adzetto/DASK_26__DESIGN_AND_ANALYSIS/afad_reports/DD3.pdf

# Tü rkiye Deprem Tehlike Haritaları Interaktif Web Uygulaması

## Kullanıcı Girdileri

Rapor Başlığı: DASK26DD-3

DD-3 Deprem Yer Hareketi Düzeyi | 50 yılda aşılma olasılığı %50 (tekrarlanma periyodu 72 yıl) olan deprem yer hareketi düzeyi
Yerel Zemin Sınıfı: ZD | Orta sıkı - sıkı kum, çakıl veya çok katı kil tabakaları

Enlem: 41.002136°

Boylam 29.106832°

## Çıktılar

S S

= 0.358 | S1 = 0.099 | PGA=0.152 | PGV=9.459

SS : Kısa periyot harita spektral ivme katsayısı [boyutsuz]

S1 : 1.0 saniye periyot için harita spektral ivme katsayısı [boyutsuz]

PGA : En büyük yer ivmesi [g]

PGV : En büyük yer hızı [cm/sn]

Sismik Tehlike Haritası Detay Raporu | https://tdth.afad.gov.tr/TDTH/detayliRapor.xhtml
1 of 6 | 2/3/2026, 4:59 PM

## Yerel Zemin Sınıfları

Yerel Zemin Sınıfı: | Zemin Cinsi | Üst 30 metrede ortalama
(VS)30 [m/s] | (N60)30 [darbe/30 cm] | (Cu )30 [kPa]
ZA | Sağlam, sert kayalar | > 1500 | - | -
ZB | Az ayrışmış, orta sağlam kayalar Çok sıkı kum, çakıl ve sert kil tabakaları veya ayrışmış, | 760 -1500 | - | - ZC
| çok çatlaklı zayıf kayalar | 360 -760 | > 50 | > 250
ZD | Orta sıkı - sıkı kum, çakıl veya çok katı kil tabakaları | 180 -360 | 15 - 50 | 70 -250
ZE | Gevşek kum, çakıl veya yumuşak - katı kil tabakaları veya PI > 20 ve w > % 40 koşullarını sağlayan toplamda 3 metreden daha kalın yumuşak kil tabakası ( Cu < 25 kPa ) içeren profiller | < 180 | < 15 | < 70
ZF | Sahaya özel araştırma ve değerlendirme gerektiren zeminler : 1) Deprem etkisi altında çökme ve potansiyel göçme riskine sahip zeminler (sıvılaşabilir zeminler, yüksek derecede hassas killer, göçebilir zayıf çimentolu zeminler vb.), 2) Toplam kalınlığı 3 metreden fazla turba ve/veya organik içeriği yüksek killer, 3) Toplam kalınlığı 8 metreden fazla olan yüksek plastisiteli (PI > 50) killer , 4) Çok kalın (> 35 m) yumuşak veya orta katı killer.
2 of 6 | 2/3/2026, 4:59 PM

## Yerel Zemin Etki Katsayıları

Yerel Zemin Sınıfı: | Kısa periyot bölgesi için Yerel Zemin Etki Katsayısı FS
SS ≤ 0.25 | SS = 0.50 | SS = 0.75 | SS = 1.00 | SS = 1.25 | SS ≥ 1.50
ZA | 0.8 | 0.8 | 0.8 | 0.8 | 0.8 | 0.8
ZB | 0.9 | 0.9 | 0.9 | 0.9 | 0.9 | 0.9
ZC | 1.3 | 1.3 | 1.2 | 1.2 | 1.2 | 1.2
ZD | 1.6 | 1.4 | 1.2 | 1.1 | 1.0 | 1.0
ZE | 2.4 | 1.7 | 1.3 | 1.1 | 0.9 | 0.8
ZF | Sahaya özel zemin davranış analizi yapılacaktır.

## Yerel Zemin Sınıfı: ZD ve SS

## =0.358 için FS=1.514

Yerel Zemin Sınıfı: | 1.0 saniye periyot için Yerel Zemin Etki Katsayısı F1 S1
≤ 0.10 | S1 = 0.20 | S1 = 0.30 | S1 = 0.40 | S1 = 0.50 | S1 ≥ 0.60
ZA | 0.8 | 0.8 | 0.8 | 0.8 | 0.8 | 0.8
ZB | 0.8 | 0.8 | 0.8 | 0.8 | 0.8 | 0.8
ZC | 1.5 | 1.5 | 1.5 | 1.5 | 1.5 | 1.4
ZD | 2.4 | 2.2 | 2.0 | 1.9 | 1.8 | 1.7
ZE | 4.2 | 3.3 | 2.8 | 2.4 | 2.2 | 2.0
ZF | Sahaya özel zemin davranış analizi yapılacaktır.

## Yerel Zemin Sınıfı: ZD ve S1

## =0.099 için F1

=2.400

3 of 6 | 2/3/2026, 4:59 PM

## Tasarım Spektral İvme Katsayıları

## SDS = SS FS

= 0.358 x 1.514 = 0.542

## SD1 = S1

F1

= 0.099 x 2.400 = 0.238

SDS : Kısa periyot tasarım spektral ivme katsayısı [boyutsuz]

SD1 : 1.0 saniye periyot için tasarım spektral ivme katsayısı [boyutsuz]

4 of 6 | 2/3/2026, 4:59 PM

## Yatay Elastik Tasarım Spektrumu

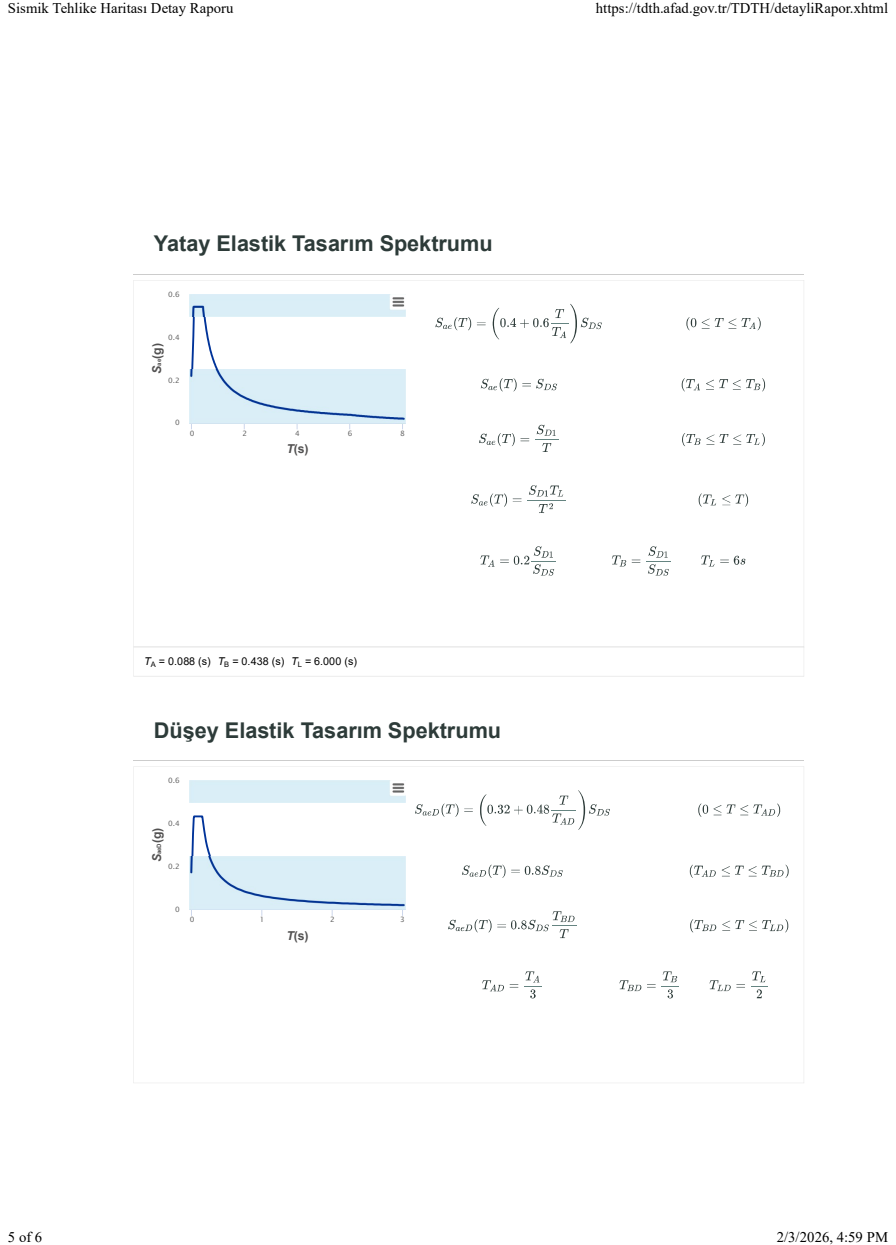
[picture p2: page 5]
Sae(g) 0 2 4 6 8; SaeD(g) 0 1 2 3

Düşey Elastik Tasarım Spektrumu

TAD = 0.029 (s) TBD = 0.146 (s) TLD = 3.000 (s)

6 of 6 | 2/3/2026, 4:59 PM
