adzetto/DASK_26__DESIGN_AND_ANALYSIS/tex/rapor.pdf

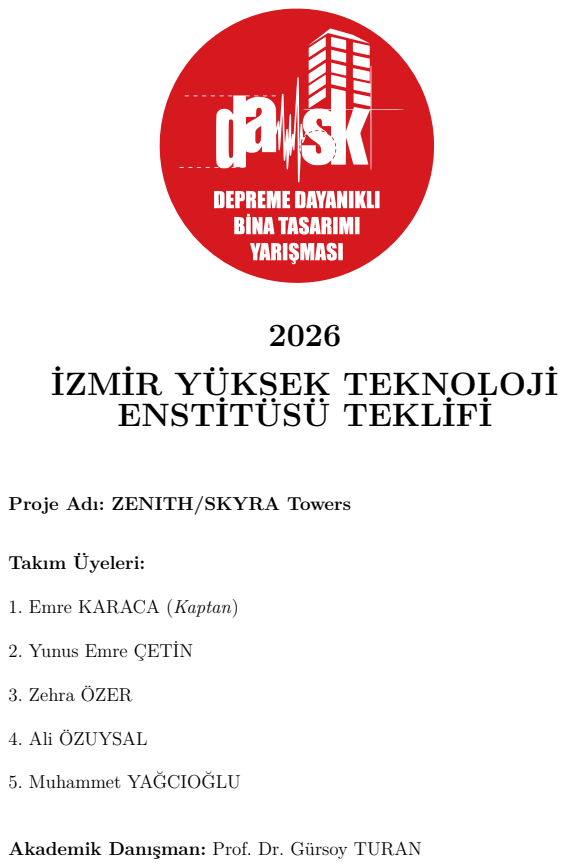
[picture p3: page 1]
Takım Üyeleri:; 3. Zehra ÖZER; 4. Ali ÖZUYSAL; 5. Muhammet YAĞCIOĞLU

İZMİR YÜKSEK TEKNOLOJİ
ENSTİTÜSÜ TEKLİFİ

Proje Adı: ZENITH/SKYRA Towers

1. Emre KARACA (Kaptan)

2. Yunus Emre ÇETİN

Akademik Danışman: Prof. Dr. Gürsoy TURAN

DASK 2026 | İzmir Yüksek Teknoloji Enstitüsü Proje Teklifi

## İçindekiler

1 BİNA TANITIMI | 1
2 MİMARİ TASARIM | 2
3 YAPISAL SİSTEM TANIMI ve TASARIMI | 3
4 ÇİZİMLER | 5
5 SORULAR | 6
DASK Depreme Dayanıklı Bina Tasarımı Yarışması Proje Teklifi | i/14

## 1 BİNA TANITIMI

Konum ve vizyon. İstanbul; Asya ile Avrupa’yı birbirine bağlayan, yüzyıllardır ticaretin, kültürün ve diplomasinin kesişim noktası olan dünyanın sayılı metropollerinden biridir. Türkiye’nin gayrisafi yurtiçi hasılasının yaklaşık üçte birini tek başına üreten bu şehir, ülkenin finans, lojistik ve hizmet sektörlerinin de merkezi konumundadır. Bu potansiyeli küresel ölçekte değerlendirmek amacıyla İstanbul’un Ümraniye ilçesinde inşa edilen İstanbul Finans Merkezi (İFM); Londra, New York, Hong Kong ve Singapur gibi dünya finans merkezleriyle rekabet edecek altyapıya sahip, akıllı ve sürdürülebilir bir kentsel finans ekosistemi yaratmayı hedeflemektedir (Şekil 1). İFM yerleşkesinde konumlanan GÜRSOY Towers projesi, bölgenin artan nitelikli ofis, konaklama ve ticaret alanı ihtiyacına yanıt vererek İstanbul’un küresel finans haritasındaki konumunu güçlendirmeyi amaçlamaktadır.
Mimari konsept ve boyutlar. GÜRSOY Towers, 25 katlı iki simetrik ikiz kuleden oluşan, İFM silüetine prestij katan bir yapı olarak tasarlanmıştır. Her kule 15×8 m plan boyutlarına sahip olup zemin kat yüksekliği 4,5 m, tipik kat yüksekliği 3,0 m, toplam bina yüksekliği 76,5 m, kuleler arası açıklık ise 4,0 m’dir. Kule başına tipik kat brüt alanı yaklaşık 150 m² olup iki kulenin toplam brüt inşaat alanı yaklaşık 7 666 m²
’dir. Kuleler; 6.,
12., 18. ve 25. katlarda yer alan dört adet köprü ile birbirine bağlanmıştır. Köprüler yalnızca taşıyıcı birer eleman değil, aynı zamanda birer sosyal ve ticari odak noktasıdır: sırasıyla gastronomi, iş dünyası, kültür-sanat ve sky lounge temaları etrafında şekillendirilmiştir. Dış cephe, yüksek performanslı cam paneller ve çelik çerçeve kompozisyonuyla tasarlanmış olup kulelerin kesişen çapraz elemanları cephede de okunarak yapıya dinamik ve güçlü bir karakter kazandırmaktadır.
Kat kullanım programı. Zemin kat; çift cepheli ana giriş lobisi, dijital karşılama ekranları, güvenlik kontrol noktası ve sanat sergi galerisi olarak düzenlenmiştir. 2.–3. katlar; butik mağazalar, flagship restoranlar, konferans merkezi ve basın odası gibi ticari ve kamusal işlevlere ayrılmıştır. 4. kat tam donanımlı fitness merkezi, kapalı yüzme havuzu ve spa alanı ile kullanıcılara sosyal yaşam imkânı sunmaktadır. 5–11. katlar; açık plan ofis düzeninde yüksek yoğunluklu çalışma alanları olarak planlanmış olup esnek bölme sistemleri sayesinde farklı kiracı ihtiyaçlarına uyarlanabilmektedir. 13–17. katlar ise hukuk büroları, finans şirketleri ve uluslararası danışmanlık firmalarına yönelik premium süit ofisler olarak tasarlanmıştır. A Kulesi’nde 19. kattan itibaren üst düzey yönetici ofisleri, CEO süitleri ve özel toplantı salonları; B Kulesi’nde ise aynı katlarda 5 yıldızlı butik otel odaları, wellness merkezi ve presidential süit yer almaktadır. Bu ikili kullanım yapısı sayesinde iş seyahati ile konaklama ihtiyacı aynı yerleşkede karşılanmaktadır. 24. katta her iki kulede penthouse katlar bulunurken, 25. katta İstanbul’un eşsiz siluetini sunan 360° panoramik sky lounge, çatı teras restoranı ve gözlem platformu konumlandırılmıştır. GÜRSOY Towers bu programıyla çalışma, konaklama, gastronomi, sosyal yaşam ve kültürel etkinlik işlevlerini bir arada sunarak İFM’nin en çok yönlü yapısı olmayı hedeflemektedir.
DASK Depreme Dayanıklı Bina Tasarımı Yarışması Proje Teklifi | 1/14


Şekil 1: İstanbul Finans Merkezi (İFM) yerleşkesi ve GÜRSOY Towers proje konumu.

## 2 MİMARİ TASARIM

Binanın mimari tasarımında dikkate alınan tasarım kriterlerinin çevresel ve ekonomik koşulları da kapsayacak şekilde ilgili görsellerle desteklenerek açıklandığı bölümdür (şekiller hariç maksimum 1 A4 sayfa).

DASK Depreme Dayanıklı Bina Tasarımı Yarışması Proje Teklifi | 2/14

## 3 YAPISAL SİSTEM TANIMI ve TASARIMI

Saha koşulları ve deprem tehlikesi. Proje sahası, İstanbul Finans Merkezi (41.00◦ K, 29.11◦ D) mevkiinde olup Kuzey Anadolu Fayı’na yakın konumu itibarıyla birinci derece deprem kuşağında yer almaktadır. AFAD [3] DD-2 tehlike düzeyinde tasarım spektral ivmeleri SDS = 1.008 g, SD1 = 0.514 g olarak belirlenmiştir [1]. Saha ZD zemin sınıfında olup kalın yumuşak zemin tabakası uzun periyotlu deprem dalgalarını kuvvetlendirerek üstyapıya aktarmaktadır; bu durum yapısal tasarımda hem yanal rijitliği hem de yeterli şekil değiştirme kapasitesini zorunlu kılmaktadır.
Taşıyıcı sistem tipi ve gerekçeleri. Salt moment çerçevesi sünek olmakla birlikte yanal ötelenmeyi yeterince sınırlayamamakta; çaprazlı sistem ise yüksek rijitlik sağlamakla beraber gevrek kırılmaya açık bulunmaktadır. Bu dengeyi kurmak üzere çerçeve–çapraz hibrit sistem tercih edilmiştir [5]: çapraz elemanlar yatay yükleri doğrudan temele ileterek yanal ötelenmeyi kontrol altına almakta; moment çerçevesi ise enerji yutma ve plastik yeniden dağılım imkânı sunmaktadır. İkiz kule konfigürasyonu benimsenerek ∼H/4, H/2, 3H/4 ve tepe kotlarına yerleştirilen dört köprü ile kuleler kuplajlanmış; global rijitlik artırılmış, diferansiyel ötelenme ve burulma talebi asgariye indirilmiştir [10, 15]. Köprüler aynı zamanda iki kulenin eş fazlı titreşimini sağlayarak antisimetrik modları bastırma işlevi de görmektedir.
İzlenen yaklaşımlar ve kabuller. Yapısal model OpenSees®
[4] ortamında oluşturulmuştur. Kolon–kiriş birleşimleri rijit, çapraz uçları mafsallı kabul edilmiştir. Güçlü kolon–zayıf kiriş ilkesi gözetilerek plastik mafsalların kiriş uçlarında oluşması hedeflenmiş, kat mekanizması ihtimali bertaraf edilmiştir [1]. Her iki doğrultuda tam simetri tesis edilerek kütle merkezi ile rijitlik merkezi çakıştırılmış (ex/Lx = 0, ey/Ly = 0); böylece deprem yüklerinin burulma bileşeni sıfırlanmıştır. A1a burulma düzensizliği kontrolünde zemin katta ηbi = 1,69 < 2,0, üst katlarda ηbi < 1,2 elde edilmiştir [2]. Deprem analizinde Mod Birleştirme Yöntemi (MBY) ile zaman tanım alanında hesap (ZTAH) uygulanmış; modal katkılar CQC kuralı (ξ =0.05) ile birleştirilmiştir [1].
Sistem geometrisi ve çapraz yerleşim stratejisi. Yapı 20×20 m taban alanı üzerinde iki simetrik kuleden oluşmaktadır (Şekil 2). Her kule 15×8 m plan boyutunda, 7×3 düşey kolon ağı üzerine inşa edilmiş olup zemin kat yüksekliği h0 = 4,5 m, sonraki 24 kat h = 3,0 m; toplam yükseklik H = 76,5 m’dir. Kuleler arası açıklık 4,0 m olup köprüler 6., 12., 18. ve
25. katlarda konumlandırılmıştır. X doğrultusunda köşe açıklıkları (1,35 m) kısa tutularak çerçeve rijitliği takviye edilmiş; Y doğrultusunda simetrik iki açıklık (3,85 m) ile rijitlik dağılımı dengelenmiştir. Çapraz elemanlar, deprem kesme kuvvetinin en yoğun olduğu alt katlara konsantre edilmiştir (Şekil 2). XZ düzleminde iç açıklıklarda zemin–13. kat arasında X-çapraz çifti uygulanarak kesme kuvveti basınç ve çekme bileşenlerine ayrıştırılmıştır. Dış açıklıklarda alt dört katta her katta tam çapraz, üst katlarda ise üçer katlık zikzak düzeninde çapraz yerleştirilmiştir; bu gradyan, üst katlardaki kesme kuvveti düşüşüne paralel olarak rijitlik dağılımını optimize etmektedir. Y Z düzleminde ise köprü katlarındaki düğüm noktalarını güçlendirmek amacıyla mega brace (mega çapraz) konfigürasyonu benimsenmiştir. Zemin bloğunda (0–6. kat) çaprazlar zemin kattan başlayarak iki kat yüksekliğinde orta kolonda birleşmekte (2. kat seviyesi) ve oradan köprü altı düğümüne (6. kat altı) açılmaktadır. Üst bloklarda mega çaprazlar bir köprü altı düğümünden bir sonraki köprü altı düğümüne uzanmakta, merkez düğüm noktaları orta kolonda oluşmaktadır. Köprü üstü düğüm noktaları ek çaprazlarla mega brace merkezine bağlanarak köprü seviyelerinde rijit düğüm noktaları tesis edilmiştir. En üst katta (24–25. kat) köprü üzerinden çatıya doğru kapatma çaprazları uygulanmıştır.
DASK Depreme Dayanıklı Bina Tasarımı Yarışması Proje Teklifi | 3/14

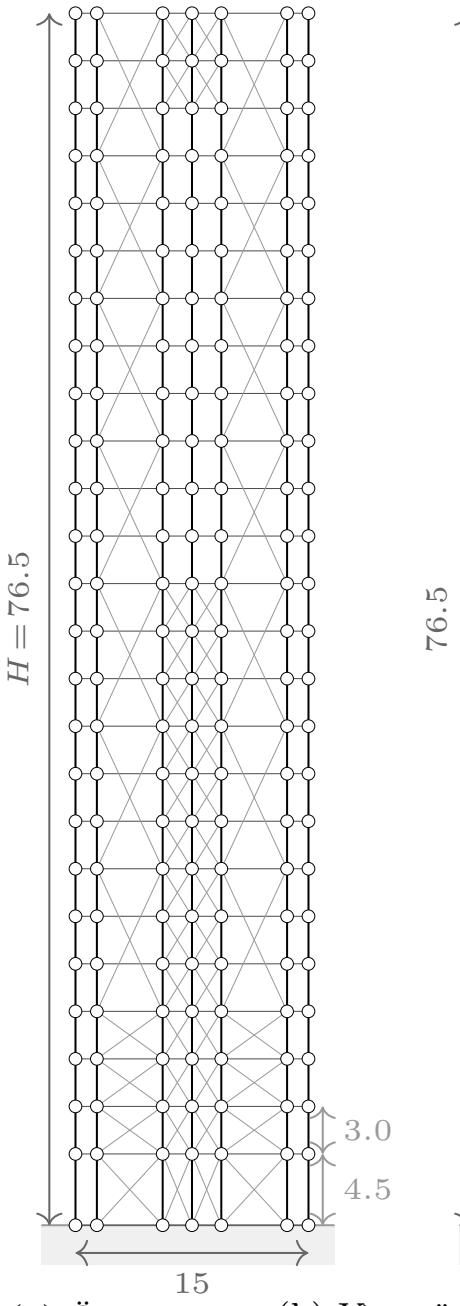
[picture p4: figure]

(a) Ön görünüm (XZ)

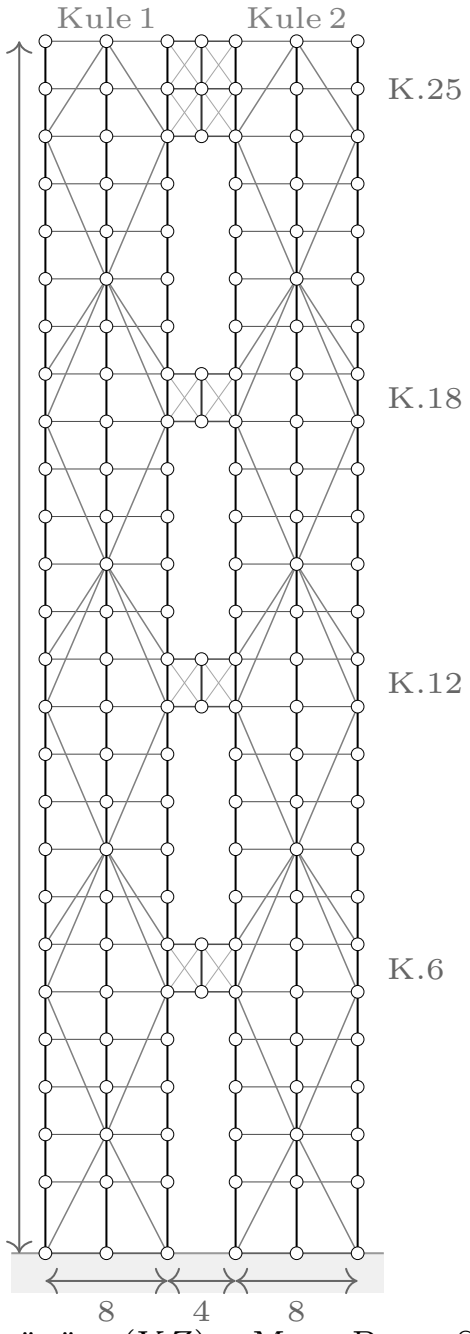
[picture p5: figure]
Kule 1; Kule 2

(b) Yan görünüm (Y Z) – Mega Brace Sistemi

Şekil 2: V10 modelinin yapısal sistemi: (a) ön görünüm (XZ)—iç açıklıklarda X-çapraz (0–12. kat), dış açıklıklarda 3 katlık zikzak; (b) yan görünüm (Y Z)—mega brace çapraz sistemi ve köprü kafes bağlantıları. Siyah: kolon, koyu gri: kiriş/köprü, açık gri: çapraz. Beyaz daireler: düğüm noktaları. Ölçüler metre cinsindendir.

DASK Depreme Dayanıklı Bina Tasarımı Yarışması Proje Teklifi | 4/14

## 4 ÇİZİMLER

Binanın her bir farklı katına ait plan ve iki ana doğrultudaki kesit çizimleri verilecektir.

- Çizimler ayrıca "dwg" formatında ek olarak sunulacaktır.
DASK Depreme Dayanıklı Bina Tasarımı Yarışması Proje Teklifi | 5/14

## 5 SORULAR

### 5.1 Soru I

Soru: Yapı taşıyıcı sistemini belirlerken nelere dikkat ettiğinizi depreme dayanıklı bina tasarım ilkeleri çerçevesinde (taşıyıcı elemanların geometrisi ve yerleşimi, yeterli dayanım, rijitlik ve sünekliğin sağlanması gibi) açıklayınız.
Cevap: Taşıyıcı sistem seçiminde beş temel ilkeye dikkat edilmiştir: (1) simetri ve düzenlilik, (2) yeterli rijitlik, (3) sürekli yük aktarımı, (4) süneklik, (5) hafiflik. TBDY 2018 ve uluslararası tasarım esasları çerçevesinde bu ilkeler aşağıda açıklanmıştır [1, 5].

### 5.1.1 İkiz Kule ve Köprü Sistemi & Simetri ve Düzenlilik

Yüksek katlı yapı konfigürasyonu olarak iki ayrı kule ve bunları birbirine bağlayan köprü elemanlarından oluşan bir sistem tasarlanmıştır. Her kule 26 kattan oluşmakta olup 7×3 kolon gridi üzerine inşa edilmiştir. Literatürdeki çalışmalar, köprü bağlantılarının yapı yüksekliğinin 1/4, 1/2 ve 3/4 seviyelerine yerleştirilmesinin sismik performansı optimize ettiğini göstermektedir [10]. Bu doğrultuda köprüler yaklaşık olarak 6., 12., 18. ve 25. katlara konumlandırılmıştır. Bu konfigürasyon, yatay yükler altında kulelerin birlikte çalışmasını sağlamakta ve tek bir yüksek kuleye kıyasla daha dengeli yük dağılımı sunmaktadır. Yapının planda ve düşeyde düzenli olması, burulma düzensizliğini önlemek açısından temel gerekliliktir. İkiz kule sistemi her iki ana eksende (X, Y ) simetrik olarak tasarlanmış; kütle merkezi ile rijitlik merkezi arasındaki eksantrisite en aza indirilmiştir. A1a burulma düzensizliği katsayısı zemin katta ηbi = 1.69 olup 2,0’nin altındadır; üst katlarda ηbi < 1.2 değerleri elde edilmiştir [2].

### 5.1.2 Yeterli Yanal Rijitlik & Sürekli Yük Aktarımı ve Süneklik

Deprem yüklerinin güvenle temele aktarılması için yapının yatay kuvvetlere karşı yeterli rijitliğe sahip olması gerekmektedir. Çerçeve-çapraz hibrit sistem tercih edilerek, moment taşıyan çerçevelerin sünekliği ile çapraz elemanların rijitliği bir arada kullanılmıştır. Çapraz elemanlar XZ ve Y Z düzlemlerinde stratejik noktalara yerleştirilmiş; köprü bağlantısı ise iki kule arasında yük paylaşımını sağlayarak global sistem rijitliğini artırmıştır. Deprem yüklerinin kesintisiz olarak temele iletilmesi için düşey taşıyıcı elemanlar tüm katlarda aynı konumda devam etmektedir. Kolon-kiriş düğüm noktaları rijit bağlantılı, çapraz elemanlar mafsallı modellenmiştir. Güçlü kolon–zayıf kiriş tasarım prensibi uygulanarak plastik mafsalların kiriş uçlarında oluşması hedeflenmiştir. CQC yöntemiyle hesaplanan göreli kat ötelemesi δ/h = 0.00117 < 0.008’dir [1].

### 5.1.3 Hafiflik ve Malzeme

Deprem kuvvetleri yapı kütlesi ile doğru orantılı olduğundan, taşıyıcı sistemin mümkün olduğunca hafif tutulması esastır. Balsa ahşap malzeme (E = 3.5 GPa) kullanılarak yapısal analizler OpenSees® yazılımı ile gerçekleştirilmiş [4], ağırlık minimizasyonu ve rijitlik maksimizasyonu hedefleriyle iteratif optimizasyon yapılmıştır. Github deposunda (https://github.com/adzetto/DASK_26__DESIGN_AND_ANALYSIS) tüm analiz ve optimizasyon kodları mevcuttur [11].
Sonuç olarak, sahaya özgü deprem tehlikesi parametreleri (SDS = 1.008 g, SD1 = 0.514 g, zemin sınıfı ZD) dikkate alınarak [3], TBDY 2018 gerekliliklerini karşılayan simetrik, yeterli yanal rijitliğe ve sünekliğe sahip, hafif bir çerçeve–çapraz hibrit ikiz kule–köprü taşıyıcı sistemi tasarlanmıştır.
DASK Depreme Dayanıklı Bina Tasarımı Yarışması Proje Teklifi | 6/14

### 5.2 Soru II

Soru: Binanızın doğal titreşim periyodu ile deprem yer hareketi tepki spektrumu arasındaki ilişkiyi açıklayınız.
Cevap: Yapının ilk üç doğal titreşim periyodu (T1 = 0.115 s, T2 = 0.079 s, T3 = 0.054 s) değerlendirildiğinde, T1 TBDY 2018 DD-2 tasarım spektrumunun sabit ivme (plato) bölgesine (TA = 0.102 s < T1 < TB = 0.510 s) düşmekte; T2 ve T3 ise artan bölgede (T < TA) yer almaktadır. Birinci mod tam plato ivmesini (Sae = 1.008 g) alırken, T2 için Sae = 0.872 g, T3 için Sae = 0.723 g elde edilmektedir. Periyotların ZD zemin hakim periyodundan (Tg ≈ 0.4–0.7 s) belirgin şekilde kısa olması rezonans riskini ortadan kaldırmaktadır.
İstanbul Finans Merkezi (41.002136◦

, 29.106832◦
) için AFAD [3] DD-2 verileri: SS = 0.877, S1 = 0.243, zemin sınıfı ZD. Yerel zemin etki katsayıları FS = 1.149, F1 = 2.114 ile tasarım parametreleri:
SDS = 0.877 × 1.149 = 1.008 g, | SD1 = 0.243 × 2.114 = 0.514 g. | (1)

Köşe periyotları TA = 0.2 · SD1/SDS = 0.102 s, TB = SD1/SDS = 0.510 s olarak hesaplanmıştır [1].

OpenSees®
[4] ile 1108 düğüm, 2794 elemanlı V10 modeli elasticBeamColumn elemanları ve toplu kütle (lumped mass) formülasyonu ile oluşturulmuştur. Özdeğer problemi Kϕn = ω

2
nMϕn ARPACK kütüphanesi ile Lanczos iterasyonu (-genBandArpack) kullanılarak çözülmüş; ilk 12 mod için periyotlar Tn = 2π/ωn ile elde edilmiştir. Modal periyotlar: T1 = 0.115 s (Y sallanım, %72.3), T2 = 0.079 s (X sallanım, %68.3), T3 = 0.054 s (burulma). Birinci mod TA < T1 < TB aralığında plato bölgesinde olup Sae = SDS = 1.008 g almaktadır; T2 ve T3 artan bölgede olup Sae(T2) = 0.872 g, Sae(T3) = 0.723 g değerlerini almaktadır. Dördüncü mod (T4 = 0.039 s) daha derin artan bölgede: Sae(T4) = (0.4 + 0.6 · 0.039/0.102) · 1.008 = 0.635 g. Modal katkılar CQC yöntemiyle birleştirilmiş olup korelasyon katsayısı ρij = 8ξ
| 2 (1 + βij )β 3/2 ij /[(1 − β
| 2 ij ) 2 + 4ξ
2βij (1 + βij )
| | 2 ]

(βij = ωi/ωj

, ξ = 0.05) ile hesaplanmıştır. Elastik taban kesme kuvveti Vt = 160 N olup TBDY 2018 gerekliliklerini sağlamaktadır. Yapı periyodunun ZD zemin hakim periyodundan (Tg ≈ 0.4–0.7 s) kısa olması rezonans riskini azaltmaktadır. Spektrum-periyot ilişkisi

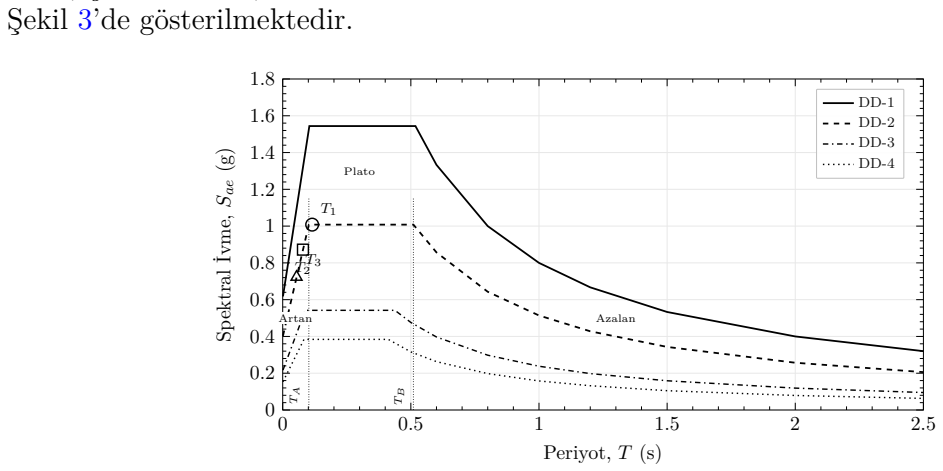
[picture p6: figure]
Şekil 3’de gösterilmektedir.; Artan; Azalan; Plato; Periyot, T (s); Spektral İvme,; Sae (g)

Şekil 3: AFAD DD-1/2/3/4 yatay elastik tasarım spektrumları ve OpenSees modal analiz sonuçları (İFM, ZD). Beyaz işaretçiler V10 modelinin ilk üç modunu göstermektedir (T1 = 0.115 s plato, T2 = 0.079 s artan, T3 = 0.054 s artan).

DASK Depreme Dayanıklı Bina Tasarımı Yarışması Proje Teklifi | 7/14

### 5.3 Soru III

Soru: Yapıdaki düşey taşıyıcıların yerleşiminin belirlenmesinde dikkat edilen hususlar nelerdir?
Cevap: Düşey taşıyıcı yerleşiminde üç temel hedef gözetilmiştir: (i) düşey yüklerin
(Z) sürekli ve kesintisiz temele aktarımı, (ii) yatay kuvvetlere (X, Y ) karşı yeterli yanal rijitliğin temini, (iii) burulma düzensizliğinin kontrolü [1].
Kolon Grid Konfigürasyonu: Her kule için 7 × 3 ortogonal kolon gridi uygulanmıştır. X ekseninde değişken açıklık düzeni benimsenmiş olup köşe açıklıkları (L = 2,7 cm) kısa tutularak moment çerçevesi rijitliği artırılmış, iç açıklıklarda (3,7 cm) perde duvarı benzeri rijitlik konsantrasyonu sağlanmıştır. Y ekseninde eşit iki açıklık (Ly = 7,7 cm) ile simetrik dağılım elde edilmiş; merkez kolonlar köprü bağlantı hattını güçlendirmektedir. Bu konfigürasyon rijitlik merkezi ile kütle merkezi arasındaki mesafeyi sıfıra indirerek burulma talebini azaltmaktadır [5].
Yanal Yük Taşıyıcı Sistem: Moment çerçevesi tek başına hedef yanal rijitliği karşılayamadığından, XZ ve Y Z düzlemlerinde çapraz elemanlarla desteklenmiş hibrit sistem tercih edilmiştir. Çapraz elemanlar köşe ve merkez açıklıklara yerleştirilmiş; tüm katlarda kesintisiz devam ettirilerek yük akışı sürekliliği tesis edilmiştir [1].
Köprü Bağlantı Seviyeleri: Köprüler yapı yüksekliğinin H/4, H/2, 3H/4 ve tepe kotlarına konumlandırılmıştır. Bu dağılım, ikiz kule sistemlerinde mod şekillerini dengeleyerek taban kesme kuvvetini minimize etmektedir [10]. Köprü genişliği merkez kolon hattı (x = 11.3–18.7 cm, genişlik 7,4 cm) ile sınırlandırılmış; böylece kulelerin bağımsız titreşim karakteristiği korunarak kontrollü yük paylaşımı sağlanmıştır. Uygulanan çift simetri sayesinde kütle-rijitlik eksantrisitesi ex/Lx = 0,000, ey/Ly = 0,000 olarak elde edilmiştir [1]. Zemin katta A1a burulma düzensizliği katsayısı ηbi = 1,69 < 2,0 olup bu değer alt katlardaki asimetrik çapraz rijitliğinden kaynaklanmaktadır; 5. kattan itibaren ηbi < 1,2 değerleri elde edilmiştir [2]. Kolon yerleşimi Şekil 4’de sunulmaktadır.

n−1

n

n+1

Kule 1 | Kule 2

Köprü

4.3 m

3 m

(a) YZ Kesiti

(köprü katı n = 6, 12, 18, 25)

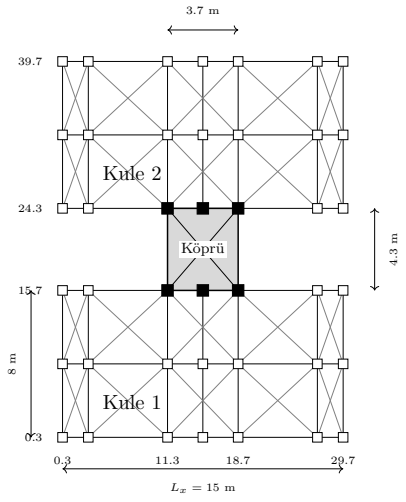
[picture p7: figure]
Köprü; Kule 1; Kule 2

(b) Kat Planı (n. kat)

Kolon

Köprü bağ.

Döşeme
Kiriş
Çapraz

Şekil 4: V10 modeli kolon yerleşimi ve köprü bağlantısı: (a) YZ kesiti (n−1, n, n+1 katları), (b) köprü katı planı. 7 × 3 kolon gridi, köprü açıklığı 8,6 cm. Temsilî çizim için DASK 2026 kodları [11] kullanılmıştır. Uzunluklar elemanların dışından dışına ölçü olarak verilmiştir.

DASK Depreme Dayanıklı Bina Tasarımı Yarışması Proje Teklifi | 8/14

### 5.4 Soru IV

Soru: Önerdiğiniz yapısal sistemin ülkemizde uygulaması yaygın mıdır? Yaygın değilse sebepleri ne olabilir? Bu sebepler arasında uygulama zorluğu ve maliyet olabilir mi? Cevap: Önerilen ikiz kule–gökyüzü köprüsü–moment çerçevesi/çaprazlı çerçeve hibrit sistemi Türkiye’de yaygın değildir. Ülkemiz dünyanın 7. büyük ham çelik üreticisi olmasına karşın yapısal çeliğin inşaat sektöründeki payı %5’in altındadır; gelişmiş ülkelerde bu oran %30–55 bandındadır [13, 14]. İkiz kule konsepti yalnızca İş Kuleleri, Tat Towers ve Skyland İstanbul gibi sınırlı sayıda projede karşımıza çıkmakta; hiçbirinde yüksek kotta kuleleri bağlayan yapısal bir sky bridge bulunmamaktadır. Petronas İkiz Kuleleri (170 m kotunda 58 m çelik köprü) bu konfigürasyonun dünya ölçeğindeki en bilinen temsilcisi olup Türkiye’de eşdeğeri mevcut değildir [10].

### 5.4.1 Uygulama Zorluğu

Hibrit sistemde moment çerçevesi düğüm noktaları tam nüfuziyetli küt kaynak ile rijit bağlantı gerektirmekte; her birleşimin ultrasonik muayene (UT) ile tahribatsız kontrol sürecinden geçmesi zorunludur. Çaprazlı çerçevelerde ise guse plakası tasarımı Whitmore efektif kesit, blok kesme dayanımı ve burkulma kontrolleri gibi çok parametreli bir detaylandırma sürecini içermektedir. Sky bridge elemanları, iki bağımsız kulenin farklı titreşim periyotlarından kaynaklanan diferansiyel yer değiştirmelere maruz kaldığından kayma anahtarı, sismik derz veya sürgülü mesnet gibi özel birleşim detayları ile donatılmalıdır. Türkiye’de çelik yapı sektörü betonarmeye kıyasla oldukça dar kapsamlıdır; sertifikalı kaynak teknisyeni, çelik detay mühendisi ve bu tür karmaşık birleşimleri projelendirebilecek deneyimli yapısal tasarım bürosu sayısı sınırlı kalmaktadır [13].

### 5.4.2 Maliyet

Çelik malzemenin kilogram başına birim fiyatı betonarmeye yakın olmakla birlikte sistemin bütünü değerlendirildiğinde belirgin ek maliyet kalemleri ortaya çıkmaktadır: tam nüfuziyetli kaynak işçiliği, UT ve manyetik parçacık muayenesi (MT) gibi tahribatsız muayene süreçleri, epoksi veya galvaniz bazlı çok katmanlı korozyon koruma sistemi ve sky bridge özel çelik imalatı bunların başlıcalarıdır. Öte yandan çeliğin düşük özgül ağırlığı (γs ≈ 78.5 kN/m³≪ γc ≈ 25 kN/m³
) yapının toplam kütlesini mt ciddi oranda azaltmakta, taban kesme kuvveti VtE = mt SaR(T1) doğrudan düşmekte ve temel boyutları küçülmektedir [1]. Ayrıca fabrikada kontrollü üretim ile sahada bulonlu montaj, kalıpiskele ihtiyacını ortadan kaldırarak inşaat süresini ve işçilik maliyetini belirgin biçimde azaltmaktadır.

### 5.4.3 Sektörel Sebepler

Türkiye’de inşaat sektörü köklü bir betonarme geleneği üzerine inşa edilmiştir. Ülke genelinde çimento fabrikası, hazır beton santrali ve beton prefabrik tesisi altyapısı son derece güçlüdür; mühendislik fakültelerinde yapısal tasarım eğitimi ağırlıklı olarak betonarme üzerine şekillenmektedir. Çelik yapıların tasarım, hesap ve yapım esaslarını düzenleyen ulusal yönetmelik ÇYTHYE 2018 ancak son yıllarda yürürlüğe girmiş olup [12] sektörde çelik yapı kültürünün oluşması için yeterli süre henüz geçmemiştir. Deprem sonrası hızlı yeniden yapılanma ihtiyacı ve çeliğin sismik performans avantajları göz önüne alındığında [14] bu eğilimin değişeceği ve önerdiğimiz gibi hibrit sistemlerin ülkemizde giderek daha fazla tatbik edileceği öngörülmektedir.

DASK Depreme Dayanıklı Bina Tasarımı Yarışması Proje Teklifi | 9/14

### 5.5 Soru V

Soru: Deprem etkileri altında tasarıma esas iç kuvvetleri belirlemek için hangi hesap yöntemini seçtiğinizi nedenleriyle birlikte açıklayınız.
Cevap: Tasarıma esas iç kuvvetlerin tayininde Mod Birleştirme Yöntemi (MBY, TBDY 2018 Md. 4.8.2) tercih edilmiştir [1].

### 5.5.1 EDYY’nin Yetersizliği

Eşdeğer Deprem Yükü Yöntemi (EDYY, Md. 4.7.3) yapı davranışının birinci mod ile temsil edilebileceğini varsayar. Kat deprem kuvvetleri bu tek modun şekil fonksiyonuna istinaden dağıtılır. Ne var ki ikiz kule–köprü sisteminde köprü elemanları iki kulenin müstakil titreşim modlarını çiftleştirmekte; translasyonel ve torsiyonel bileşenleri müteselsilen ihtiva eden karışık modlar hasıl olmaktadır. İlk üç doğal periyot (T1 = 0.115 s, T2 = 0.079 s, T3 = 0.054 s) birbirine yakındır; birinci modun etkin kütle oranı %72 olup kalan katkı üst modlara tevzi olmaktadır. Bu husus EDYY’nin esas varsayımını geçersiz kılmaktadır [1].

### 5.5.2 MBY’nin Tercih Gerekçesi

MBY’de tüm anlamlı titreşim modları ayrı ayrı göz önüne alınır. Her n. mod için azaltılmış spektral ivme SaR(Tn) = Sae(Tn)/Ra(Tn) tasarım spektrumundan okunur; modal kütle ile çarpılarak ilgili moda ait deprem kuvveti elde edilir (R = 4, D = 2.5, I = 1.0). Elde edilen modal kuvvetler elemanlarda N, V , M iç tesirlerine dönüştürülüp istatistiksel bir kaide ile tevhid edilir. İlk üç modun yakın frekansları hasebiyle modlar arası korelasyon ihmal edilemez; bu sebeple SRSS yerine CQC kuralı (ξ = 0.05) benimsenmiştir. Denk. 4.30 muktezasınca her iki doğrultuda etkin kütle oranı toplamı %95’i aşıncaya dek mod sayısı artırılmış; 12 mod ile şart sağlanmıştır [1].
Taban kesme kuvveti Md. 4.8.4 Denk. 4.31 uyarınca βtE ile kontrol edilmiş; A1a düzensizliği sebebiyle γE = 0.90 alınmıştır. Göreli kat ötelemesinde çelik yapılara mahsus κ = 0.5 (Md. 4.9.1.4) gözetilmiş; ikinci mertebe etkileri Ch = 1 ile hesaba katılmıştır (Md. 4.9.2) [1, 12].

### 5.5.3 Doğrulama ve Ölçekli Model

OpenSees®
[4] ile 1108 düğüm, 2794 elemanlı V10 modeli tesis edilmiştir. MBY neticeleri iki müstakil yöntemle teyit edilmiştir: ZTAH (Md. 4.8.3; Düzce BOL090, 1/

√
50 ölçek,
Newmark-β, ∆t = 0.005 s) ve statik itme (Md. 5.6.5; ters üçgen yük, δt = 6.12 cm) [11]. Her iki tahlilde taban kesme kuvveti ve kat ötelemesi MBY ile mutabık bulunmuştur. TBDY 2018 usulleri gerçek ölçekli binalar için tanzim edilmiş olmakla birlikte dayandığı nazari esaslar ölçekten bağımsızdır. Özdeğer problemi, CQC ve modal süperpozisyon sırf riyazi işlemlerdir; yapının balsa (E = 3.5 GPa) yahut çelik (E = 200 GPa) olması yalnızca K ve M’yi değiştirir. Benzeşim kuramı gereğince SF = SES

2
L

, Sm = SρS

3
L

şartı
sağlandıkça bu yöntemler ölçekli modelde de mer’iyyetini muhafaza etmektedir [1].
DASK Depreme Dayanıklı Bina Tasarımı Yarışması Proje Teklifi | 10/14

### 5.6 Soru VI

Soru: Yapı analizinde sönüm oranının ne şekilde dikkate alındığını açıklayınız.
Cevap: Gerçek yapılarda deprem enerjisi malzeme histerezisi, birleşim sürtünmesi ve yapısal olmayan elemanlar vasıtasıyla yutulur. Bu enerji kaybı analitik modelde doğrudan temsil edilemediğinden eşdeğer viskoz sönüm oranı ξ ile idealize edilir. Sönüm, yapı tepkisini doğrudan sınırlandıran parametredir; ihmal edilmesi halinde rezonans civarında teorik olarak sonsuz genlik hasıl olur. Analizlerde ξ iki seviyede dikkate alınmıştır [1]. Spektral düzeltme. MBY’de deprem talebi tasarım spektrumundan okunur; spektrum ise belirli bir referans sönüme göre tanzim edilmiştir. TBDY 2018 ξ = %5 esas alır. Farklı ξ değerlerinde spektral ordinatlar ηb =

q
10/(5 + ξ (%)) ile tashih edilir (Md. 2.3.4): ξ = %2 → ηb = 1.195 (spektrum yükselir, talep artar), ξ = %10 → 0.816 (talep düşer). Sebebi açıktır: düşük sönümlü yapı rezonans bandında daha fazla enerji biriktirir, dolayısıyla aynı yer hareketi altında daha büyük ivme tepkisi verir. Çelik çerçeve modelimiz için ξ = %5 benimsenmiştir; bu, kaynaksız bulonlu birleşim detayı ile uyumlu alt sınır değeridir [12]. Rayleigh sönümü. ZTAH’de hareket denklemi Mu¨ + Cu˙ + Ku = −M1u¨g(t) adım adım entegre edilir; burada C sönüm matrisinin açıkça tanımlanması gerekir. Genel bir C matrisi N² bağımsız terim içereceğinden deneysel tayini imkansızdır. Rayleigh formülasyonu C = a0M + a1K bu sorunu iki parametreye indirger; M ve K’ya orantılı olduğundan modal ayrışma özelliği korunur: ξn = a0/(2ωn) + a1ωn/2. İki kontrol frekansında hedef ξ sağlanacak biçimde a0 ve a1 hesaplanır [4]. V10 modelinde ω1 = 54.64 rad/s ve ω2 = 3.5ω1 = 191.2 rad/s seçilmiş; ξ = 0.05 ile a0 = 4.250, a1 = 4.07×10⁻⁴
s elde edilmiştir. ω1–ω2 arasında sönüm hedefin altında kalır (ξmin = 0.042); yüksek frekanslı modlarda a1K terimi baskınlaşarak aşırı sönüm verir ve fiziksel anlamsız yüksek mod salınımları bastırılır (Şekil 5b).
Parametrik doğrulama. Sönümün yapısal tepkiye etkisini nicel olarak göstermek amacıyla KYH-1 (PGA = 0.335 g) altında 9 farklı ξ (%0,5–%20) ile tam ZTAH (32,2 s, 6446 adım, sıfır yakınsama hatası) icra edilmiştir (Şekil 5a). ξ = %0,5’te umax = 1,127 cm iken ξ = %5’te 0,449 cm’e, ξ = %20’de 0,319 cm’e düşmüştür. Düşük sönümde (ξ < %3) eğri dikleşir zira birinci mod rezonans bandına yaklaşır; yüksek sönümde ise eğri yataylaşır çünkü enerji yutma kapasitesi doyuma ulaşır. Bu durum sönüm seçiminin tasarımda kritik bir durum olduğunu teyit etmektedir [1].
%0.5 | %1 | %2 | %5 | %10 | %20

0.2

0.4

0.6

0.8

1

1.2

ξ =%5

Sönüm oranı ξ

umax (cm)

(a)

10⁻¹.5 | 10⁻¹ | 10⁻⁰.5

0

5 · 10⁻²

0.1

0.15

0.2

Periyot T (s)

Efektif

ξ

ξ0 | =%2
ξ0 | =%5
ξ0 | =%10

(b)
Şekil 5: (a) Çatı ötelemesi–sönüm oranı (KYH-1, ZTAH), (b) Rayleigh sönüm eğrileri.
DASK Depreme Dayanıklı Bina Tasarımı Yarışması Proje Teklifi | 11/14

### 5.7 Soru VII

Soru: Önerdiğiniz yapısal sistemin göreli kat ötelemelerine ve kat ivmelerine etkisi ne olacaktır?
Cevap: Üç yer hareketi kaydı (KYH-1: 0.335 g, KYH-2: 1.243 g, KYH-3: 1.896 g) altında tam ZTAH (∆t=0.005 s, 6446 adım, ξ =0.05 Rayleigh) icra edilmiştir [1, 4]. Önerilen hibrit sistemin etkisi iki esas tepki büyüklüğü üzerinden değerlendirilmiştir (Şekil 6). Göreli kat ötelemesi. Maksimum interstory drift her üç kayıt altında 23. katta teşekkül etmektedir: KYH-1’de λmax =0.435%, KYH-2’de 1.320%, KYH-3’te 2.175%. Çaprazlı çerçeveler taban katlarında rijitliği artırarak öteleme talebini düşürmekte; tepe katlarında moment çerçevesi baskınlığı sebebiyle drift azalmaktadır. Öteleme talebi üst katlarda (14–23. kat) yoğunlaşmakta olup bu husus rijitlik gradyanı ile yüksek modların bu kotlarda birinci moda yakın genlikler hasıl etmesinden kaynaklanmaktadır. PGA oranı 5.66× iken drift oranı 5.00× olarak elde edilmiş; elastik modelin yaklaşık lineer orantılılığı teyit edilmiştir. Kule arası diferansiyel öteleme ∆ux < 0.001 cm olup sky bridge kuleleri eş-fazlı çalıştırmaktadır [10]. Tasarım depremi (KYH-1) altında λmax = 0.435% ≪ 0.8% (κ=0.5 çelik sınırı, Md. 4.9.1.3) olup yapı öteleme güvenliğini geniş marjla sağlamaktadır [1, 12].
Kat ivmeleri. Çatı katı ivme yükseltme faktörü: KYH-1’de Ω = 3.17, KYH-2’de 2.60, KYH-3’te 3.30 (Ω¯ ≈3.0). Kısa periyotlu yapı (T1 = 0.115 s, plato bölgesi) sismik enerjiyi büyük oranda ivme olarak yapıya intikal ettirmektedir: KYH-3’te uroof =2.37 cm (%1.6) iken u¨roof =6.26 g (PGA’nın 3.3×’ı). Yanal rijitliği yüksek yapıların karakteristiği budur: öteleme talebi düşük, ivme talebi yüksektir. Periyodun uzatılması Ω’yı düşürür fakat drift talebini artırır; bu mübadele yapısal sistem seçiminin esas dengeleme parametresidir. Çaprazlı çerçeveler Klateral’i artırarak T1’i düşürmekte (drift ↓, Ω ↑); moment çerçeveleri redundans ve yedek taşıyıcılık; sky bridge ise kuplajlama (∆ux≈0, ηbi =1.915) temin etmektedir [15].
0 | 1 | 2 | 3

0

5

10

15

20

25

λ (%)

Kat

KYH-1
KYH-2
KYH-3
(a) Göreli kat ötelemesi
0 | 1 | 2 | 3

0

5

10

15

20

25

ux (cm)

Kat

KYH-1
KYH-2
KYH-3
(b) Deplasman zarfı
0 | 0.5 | 1 | 1.5 | 2

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
Ω= 1

Ω= 3

KYH-1

KYH-2

KYH-3

Ω¯ ≈ 3.0

PGA (g)

¨uroof (g)

(c) Çatı ivmesi yükseltmesi
Şekil 6: Kule 1 ZTAH: (a) göreli kat ötelemesi profili (λmax: kat 23), (b) kat deplasman zarfı, (c) çatı ivmesi–PGA ilişkisi (Ω¯ ≈3).
DASK Depreme Dayanıklı Bina Tasarımı Yarışması Proje Teklifi | 12/14

### 5.8 Soru VIII

Soru: Önerdiğiniz yapısal sistemin tasarım depremine maruz kalması halinde oluşması muhtemel hasar durumunu yorumlayınız ve yapının deprem öncesi durumuna getirilmesinin teknik ve ekonomik açıdan fizibilitesini değerlendiriniz.
Cevap: Tasarım depremi DD-2 altında yapılan zaman tanım alanında hesap sonuçlarına göre, önerilen kompozit ikiz kule sisteminin tüm kolon, kiriş ve çapraz elemanlarında kalıcı şekil değiştirme oluşmadığı, birleşim bölgelerinde akma eşiğinin çok altında kalındığı ve yapının deprem sonrası derhal kullanılabilir durumda olduğu belirlenmiştir. Köprü bağlantısındaki en kritik kiriş ucu (eleman 33) dahil 43 elemanın tümü elastik sınırlar içinde kalmaktadır. Kolonlarda gözlenen eğilme gerilmeleri taşıma kapasitesinin %9’unu geçmemekte; çaprazlarda burkulma veya kalıcı uzama riski bulunmamaktadır. Yapıştırma birleşim kapasitesine göre talep/kapasite oranı TKOmax = 0.087 olup hasar eşiğinin (TKO = 0.25) çok altındadır. Eleman bazlı gerilme dağılımı Şekil 7a’da sunulmuştur. Balsa kırılma dayanımı fb = 3.5 kN/cm²
; modelde ×240 ölçekleme ile fb,m = 840 kN/cm²
. Birleşim verimi ηj = 0.35 olup belirleyici kapasite Mj = 10.6 kN·cm’dir [6]. KYH-3’te en kritik eleman 33’ün TKO = 0.68 (< 1.0, hâlâ elastik).
Göçme olasılığı Baker (2015) MLE yöntemi ile lognormal kırılganlık fonksiyonu kullanılarak hesaplanmıştır [6, 7]. 43 eleman × 3 yer hareketi verisinden eleman bazlı ki = TKOi/PGA MLE ile saptanmış, sistem kırılganlığı en zayıf halkadan (el. 33) türetilmiştir. Medyan kapasiteler: θDS-1 = 0.86 g, θgöçme = 3.45 g. Belirsizlik: βr = 0.15, βu = 0.55 (model+malzeme+birleşim), βT = 0.57. DD-2’de: P(DS-1) = 4.9%, P(göçme) = 2.2 × 10⁻⁵ (Şekil 7b). Yıllık göçme olasılığı 4.5×10⁻⁸ ≪ 10⁻⁴
(ASCE 7-22) [8]. Eleman bazlı medyan göçme kapasitesi (θgöçme,i) dağılımı Şekil 7c’de sunulmuştur.
1 | 5 | 10 | 15 | 20 | 25 | 30 | 35 | 40 43

0

50

100

150

200

250
El. 33

fb = 840 (ölçek dışı)

Eleman numarası

σb (kN/cm2

)

KYH-3 σb
KYH-2 σb
KYH-1 σb
(a) Eğilme gerilmesi dağılımı
0.1 | 0.2 | 0.5 | 1 | 2 | 5 | 10

0

0.2

0.4

0.6

0.8

1

| El.13

DS-1 (θ = 0.86)

DD-2

DD-1

PGA (g)

P(DS|PGA)

DS-2 (θ = 1.73) DS-3 (θ = 2.59)

Göçme (θ = 3.45) | 90% GA
(b) Sistem kırılganlık eğrileri (MLE)
1 | 5 | 10 | 15 | 20 | 25 | 30 | 35 | 40 | 43

0

20

40

60 | θ˜= 10.9
DD-2 | P5 | = 5.2
El. 4 | El. 13 | El. 33 | El. 36

Eleman numarası

θgöçme (g)

(c) Eleman bazlı θgöçme,i — gri bant: IQR (Q1–Q3)
Şekil 7: Hasar değerlendirmesi: (a) eğilme gerilmesi dağılımı (3 yer hareketi); (b) Baker (2015) MLE kırılganlık eğrileri (βT =0.57, gri alan: göçme %90 GA); (c) eleman bazlı θgöçme,i (gri bant IQR). En zayıf halka el. 33. İstatistik (N = 43, 5 el.>50 g kırpılmış): ˜θ=10.9 g, ¯θ=15.3 g, CoV = 0.78, P5 =5.2 g; θ < 10 g: 13 eleman (%30).

Yapısal olmayan elemanlarda hafif kozmetik hasar muhtemeldir; onarım bedeli yapı bedelinin %1–3’ü, süre 2–4 hafta. Taşıyıcı elemanlar elastik; kalıcı deformasyon sıfır [8]. Yapı Hemen Kullanım (HK) seviyesindedir [1].

DASK Depreme Dayanıklı Bina Tasarımı Yarışması Proje Teklifi | 13/14

## Kaynaklar

[1] T.C. Çevre ve Şehircilik Bakanlığı, Türkiye Bina Deprem Yönetmeliği (TBDY 2018), Resmi Gazete, 2018.
[2] T.C. Çevre, Şehircilik ve İklim Değişikliği Bakanlığı, TBDY 2018 Uygulama Tebliği Taslağı, 27.05.2024.
[3] AFAD, Türkiye Deprem Tehlike Haritaları İnteraktif Web Uygulaması, https://tdth.afad.gov.tr, 2024.
[4] McKenna, F., Scott, M.H., Fenves, G.L., OpenSees: Open System for Earthquake Engineering Simulation, Pacific Earthquake Engineering Research Center, UC Berkeley, https://opensees.berkeley.edu.
[5] FEMA P-751, 2009 NEHRP Recommended Seismic Provisions: Design Examples, Building Seismic Safety Council, National Institute of Building Sciences, Washington, D.C., 2012.
[6] FEMA P-58, Seismic Performance Assessment of Buildings, Federal Emergency Management Agency, Washington, D.C., 2012.
[7] Baker, J.W., “Efficient Analytical Fragility Function Fitting Using Dynamic Structural Analysis,” Earthquake Spectra, 31(1), 579–599, 2015.
[8] ASCE/SEI 41-17, Seismic Evaluation and Retrofit of Existing Buildings, American Society of Civil Engineers, Reston, Virginia, 2017.
[9] FEMA 356, Prestandard and Commentary for the Seismic Rehabilitation of Buildings, Federal Emergency Management Agency, Washington, D.C., 2000.
[10] Patoliya, N., Patel, I., Agrawal, V., Seismic Analysis of Tall Buildings Connected with Sky Bridge, IARJSET, vol. 10, 2023, doi: 10.17148/IARJSET.2023.10446.
[11] Adzetto, DASK 2026 Tasarım ve Analiz Kodları, https://github.com/adzetto/DASK_26__DESIGN_AND_ANALYSIS, (https://github.com/adzetto/DASK_26__DESIGN_AND_ANALYSIS) 2026.
[12] T.C. Çevre ve Şehircilik Bakanlığı, Çelik Yapıların Tasarım, Hesap ve Yapım Esaslarına Dair Yönetmelik (ÇYTHYE 2018), Resmi Gazete, 2018.
[13] Kurtay, C., Badem, M., Avrupa Ülkeleri ve Türkiye’deki Çelik Yapı Uygulama Olanak ve Kısıtlarının İncelenmesi, Gazi Üniversitesi Mühendislik Mimarlık Fakültesi Dergisi, cilt 19, sayı 4, ss. 351–363, 2004.
[14] Of, N., Öztürk, S., Depremlerden Sonraki Yeniden Yapılanma Süreci Üzerine Küresel Bir Araştırma: Çelik Prefabrik Malzeme Kullanımının Gerekliliği, Afet ve Risk Dergisi, cilt 5, sayı 1, ss. 346–360, 2022, doi: 10.35341/afet.1092649.
[15] Tambunan, M.L.S., Sjah, J., Rarasati, A.D., Sulistian, R., Trigunarsyah, B., Optimizing Seismic Design of Multi-Tower Buildings Using Sky Bridge Isolation and BIM: A Case Study, Int. J. Eng. Technol. Innov., vol. 14, no. 4, pp. 355–377, 2024, doi: 10.46604/ijeti.2024.13409.
[16] TS EN 1991-1-4, Eurocode 1: Yapılar Üzerindeki Etkiler – Bölüm 1-4: Genel Etkiler – Rüzgar Etkileri, Türk Standartları Enstitüsü, 2015.
DASK Depreme Dayanıklı Bina Tasarımı Yarışması Proje Teklifi | 14/14
