adzetto/DASK_26__DESIGN_AND_ANALYSIS/tex/sorular.pdf

DASK 2026 | İstanbul Finans Merkezi Proje Teklifi

## 1 Sorular

### 1.1 Soru I

Soru: Yapı taşıyıcı sistemini belirlerken nelere dikkat ettiğinizi depreme dayanıklı bina tasarım ilkeleri çerçevesinde (taşıyıcı elemanların geometrisi ve yerleşimi, yeterli dayanım, rijitlik ve sünekliğin sağlanması gibi) açıklayınız.
Cevap: Taşıyıcı sistem seçiminde beş temel ilkeye dikkat edilmiştir: (1) simetri ve düzenlilik, (2) yeterli rijitlik, (3) sürekli yük aktarımı, (4) süneklik, (5) hafiflik. TBDY 2018 ve uluslararası tasarım esasları çerçevesinde bu ilkeler aşağıda açıklanmıştır [1, 5].

### 1.1.1 İkiz Kule ve Köprü Sistemi & Simetri ve Düzenlilik

Yüksek katlı yapı konfigürasyonu olarak iki ayrı kule ve bunları birbirine bağlayan köprü elemanlarından oluşan bir sistem tasarlanmıştır. Her kule 26 kattan oluşmakta olup 8×4 kolon gridi üzerine inşa edilmiştir. Literatürdeki çalışmalar, köprü bağlantılarının yapı yüksekliğinin 1/4, 1/2 ve 3/4 seviyelerine yerleştirilmesinin sismik performansı optimize ettiğini göstermektedir [10]. Bu doğrultuda köprüler yaklaşık olarak 6., 12., 18. ve 25. katlara konumlandırılmıştır. Bu konfigürasyon, yatay yükler altında kulelerin birlikte çalışmasını sağlamakta ve tek bir yüksek kuleye kıyasla daha dengeli yük dağılımı sunmaktadır. Yapının planda ve düşeyde düzenli olması, burulma düzensizliğini önlemek açısından temel gerekliliktir. İkiz kule sistemi her iki ana eksende (X, Y ) simetrik olarak tasarlanmış; kütle merkezi ile rijitlik merkezi arasındaki eksantrisite en aza indirilmiştir. A1a burulma düzensizliği katsayısı ηbi = 1.112 < 1.4 koşulunu sağlamakta olup yapı düzenli sınıfındadır [2].

### 1.1.2 Yeterli Yanal Rijitlik & Sürekli Yük Aktarımı ve Süneklik

Deprem yüklerinin güvenle temele aktarılması için yapının yatay kuvvetlere karşı yeterli rijitliğe sahip olması gerekmektedir. Çerçeve-çapraz hibrit sistem tercih edilerek, moment taşıyan çerçevelerin sünekliği ile çapraz elemanların rijitliği bir arada kullanılmıştır. Çapraz elemanlar XZ ve Y Z düzlemlerinde stratejik noktalara yerleştirilmiş; köprü bağlantısı ise iki kule arasında yük paylaşımını sağlayarak global sistem rijitliğini artırmıştır. Deprem yüklerinin kesintisiz olarak temele iletilmesi için düşey taşıyıcı elemanlar tüm katlarda aynı konumda devam etmektedir. Kolon-kiriş düğüm noktaları rijit bağlantılı, çapraz elemanlar mafsallı modellenmiştir. Güçlü kolon–zayıf kiriş tasarım prensibi uygulanarak plastik mafsalların kiriş uçlarında oluşması hedeflenmiştir. CQC yöntemiyle hesaplanan göreli kat ötelemesi δ/h = 0.00117 < 0.008’dir [1].

### 1.1.3 Hafiflik ve Malzeme

Deprem kuvvetleri yapı kütlesi ile doğru orantılı olduğundan, taşıyıcı sistemin mümkün olduğunca hafif tutulması esastır. Balsa ahşap malzeme (E = 3.5 GPa) kullanılarak yapısal analizler OpenSees® yazılımı ile gerçekleştirilmiş [4], ağırlık minimizasyonu ve rijitlik maksimizasyonu hedefleriyle iteratif optimizasyon yapılmıştır. Github deposunda (https://github.com/adzetto/DASK_26__DESIGN_AND_ANALYSIS) tüm analiz ve optimizasyon kodları mevcuttur [11].
Sonuç olarak, sahaya özgü deprem tehlikesi parametreleri (SDS = 1.008 g, SD1 = 0.514 g, zemin sınıfı ZD) dikkate alınarak [3], TBDY 2018 gerekliliklerini karşılayan simetrik, rijit, sünek ve hafif bir ikiz kule–köprü taşıyıcı sistem tasarlanmıştır.

### 1.2 Soru II

Soru: Binanızın doğal titreşim periyodu ile deprem yer hareketi tepki spektrumu arasındaki ilişkiyi açıklayınız.
Cevap: İstanbul Finans Merkezi (41.002136◦

, 29.106832◦
) için AFAD [3] DD-2 verileri: SS = 0.877, S1 = 0.243, zemin sınıfı ZD. Yerel zemin etki katsayıları FS = 1.149, F1 = 2.114 ile tasarım parametreleri:
SDS = 0.877 × 1.149 = 1.008 g, | SD1 = 0.243 × 2.114 = 0.514 g. | (1)

Köşe periyotları TA = 0.2 · SD1/SDS = 0.102 s, TB = SD1/SDS = 0.510 s olarak hesaplanmıştır [1].

OpenSees®
[4] ile 4248 elemanlı V9 modeli elasticBeamColumn elemanları ve toplu kütle (lumped mass) formülasyonu ile oluşturulmuştur. Özdeğer problemi Kϕn = ω

2
| | nMϕn
ARPACK kütüphanesi ile Lanczos iterasyonu (-genBandArpack) kullanılarak çözülmüş; ilk 12 mod için periyotlar Tn = 2π/ωn ile elde edilmiştir. Modal periyotlar: T1 = 0.200 s, T2 = 0.147 s, T3 = 0.135 s. Her üç mod TA < Tn < TB aralığında plato bölgesinde olup Sae = SDS = 1.008 g almaktadır. Dördüncü mod (T4 = 0.063 s) artan bölgede: Sae(T4) = (0.4 + 0.6 · 0.063/0.102) · 1.008 = 0.777 g. Modal katkılar CQC yöntemiyle birleştirilmiş olup korelasyon katsayısı ρij = 8ξ
| 2 (1 + βij )β 3/2
ij /[(1 − β
| 2 ij ) 2 + 4ξ

2βij (1 + βij )

| | 2
]
(βij = ωi/ωj

, ξ = 0.05) ile hesaplanmıştır. Taban kesme kuvveti Vt = 2.75 N’dur. Yapı periyodunun ZD zemin hakim periyodundan (Tg ≈ 0.4–0.7 s) kısa olması rezonans riskini azaltmaktadır. Spektrum-periyot ilişkisi Şekil 1’de gösterilmektedir.

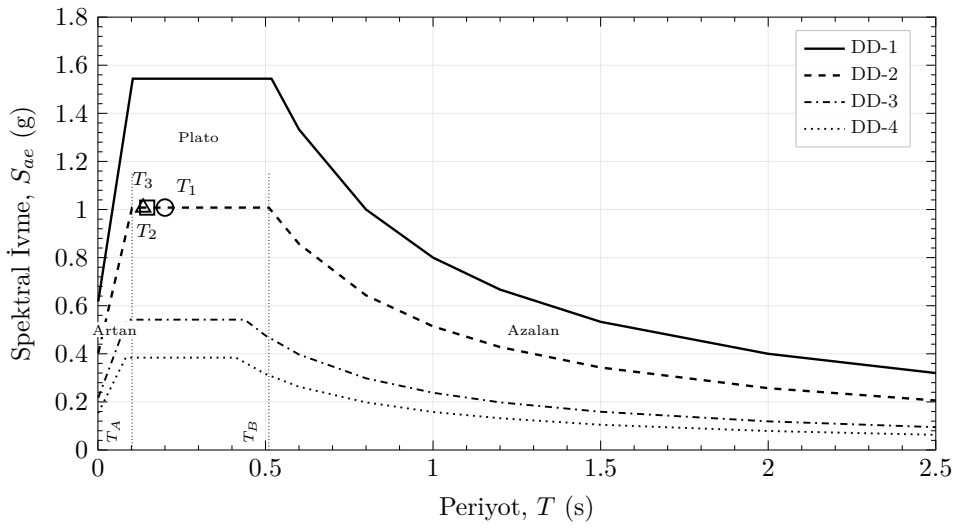
[picture p8: figure]
Artan; Plato; Azalan; Periyot, T (s); Spektral İvme,; Sae (g)

Şekil 1: AFAD DD-1/2/3/4 yatay elastik tasarım spektrumları ve OpenSees modal analiz sonuçları (İFM, ZD). Beyaz işaretçiler V9 modelinin ilk üç modunu göstermektedir (T1 = 0.200 s, T2 = 0.147 s, T3 = 0.135 s).

### 1.3 Soru III

Soru: Yapıdaki düşey taşıyıcıların yerleşiminin belirlenmesinde dikkat edilen hususlar nelerdir?
Cevap: Düşey taşıyıcı yerleşiminde üç temel hedef gözetilmiştir: (i) düşey yüklerin
(Z) sürekli ve kesintisiz temele aktarımı, (ii) yatay kuvvetlere (X, Y ) karşı yeterli yanal rijitliğin temini, (iii) burulma düzensizliğinin kontrolü [1].
Kolon Grid Konfigürasyonu: Her kule için 8×4 ortogonal kolon gridi uygulanmıştır. X ekseninde değişken açıklık düzeni benimsenmiş olup köşe açıklıkları (L = 3 cm) kısa tutularak moment çerçevesi rijitliği artırılmış, merkez bölgede dar kolon aralığı (∆x = 2.0 cm) ile perde duvarı benzeri rijitlik konsantrasyonu sağlanmıştır. Y ekseninde iç kolon sıraları (y = 7.0 ve 9.0 cm) yakınlaştırılarak köprü bağlantı hattı güçlendirilmiş; bu konfigürasyon rijitlik merkezi ile kütle merkezi arasındaki mesafeyi minimize ederek burulma talebini azaltmaktadır [5].
Yanal Yük Taşıyıcı Sistem: Moment çerçevesi tek başına hedef yanal rijitliği karşılayamadığından, XZ ve Y Z düzlemlerinde çapraz elemanlarla desteklenmiş hibrit sistem tercih edilmiştir. Çapraz elemanlar köşe ve merkez açıklıklara yerleştirilmiş; tüm katlarda kesintisiz devam ettirilerek yük akışı sürekliliği tesis edilmiştir [1].
Köprü Bağlantı Seviyeleri: Köprüler yapı yüksekliğinin H/4, H/2, 3H/4 ve tepe kotlarına konumlandırılmıştır. Bu dağılım, ikiz kule sistemlerinde mod şekillerini dengeleyerek taban kesme kuvvetini minimize etmektedir [10]. Köprü genişliği merkez kolon hattı (x = 10.5–19.5 cm) ile sınırlandırılmış; böylece kulelerin bağımsız titreşim karakteristiği korunarak kontrollü yük paylaşımı sağlanmıştır. Uygulanan yerleşim düzeni sonucunda kütle-rijitlik eksantrisitesi ex/Lx = 0.005, ey/Ly = 0.034 olarak elde edilmiş; TBDY 2018 sınır değeri (e/L < 0.05) sağlanmıştır [1]. Zemin katta A1a burulma düzensizliği katsayısı ηbi = 1.19 ⪅ 1.2 olup bu durum temel-üstyapı rijitlik geçişinden kaynaklanmaktadır; üst katlarda ηbi < 1.1 değerleri elde edilmiştir [2]. Kolon yerleşimi Şekil 2’de sunulmaktadır.
n−1 | Kule 1 | Kule 2
n | Köprü

n+1

8 cm

6 cm

(a) YZ Kesiti

(köprü katı n = 6, 12, 18, 25)

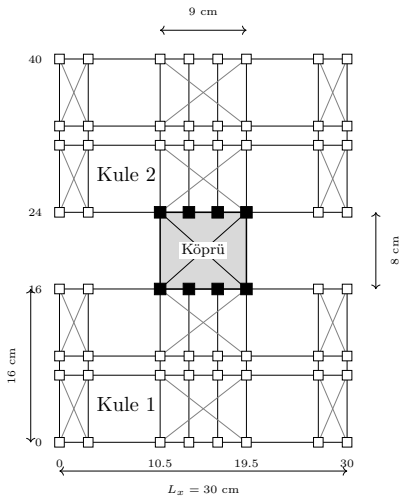
[picture p9: figure]
Köprü; Kule 1; Kule 2

(b) Kat Planı (n. kat)

Kolon

Köprü bağ.

Kiriş
Çapraz

Şekil 2: V9 modeli kolon yerleşimi ve köprü bağlantısı: (a) YZ kesiti (n−1, n, n+1 katları),
(b) köprü katı planı. Şekil temsili ve ölçeklendirilmemiştir. Temsilî çizim için DASK 2026 kodları [11] kullanılmıştır.

### 1.4 Soru IV

Soru: Önerdiğiniz yapısal sistemin ülkemizde uygulaması yaygın mıdır? Yaygın değilse sebepleri ne olabilir? Bu sebepler arasında uygulama zorluğu ve maliyet olabilir mi? Cevap: Önerilen ikiz kule–gökyüzü köprüsü–moment çerçevesi/çaprazlı çerçeve hibrit sistemi Türkiye’de yaygın değildir. Ülkemiz dünyanın 7. büyük ham çelik üreticisi olmasına karşın yapısal çeliğin inşaat sektöründeki payı %5’in altındadır; gelişmiş ülkelerde bu oran %30–55 bandındadır [13, 14]. İkiz kule konsepti yalnızca İş Kuleleri, Tat Towers ve Skyland İstanbul gibi sınırlı sayıda projede karşımıza çıkmakta; hiçbirinde yüksek kotta kuleleri bağlayan yapısal bir sky bridge bulunmamaktadır. Petronas İkiz Kuleleri (170 m kotunda 58 m çelik köprü) bu konfigürasyonun dünya ölçeğindeki en bilinen temsilcisi olup Türkiye’de eşdeğeri mevcut değildir [10].

### 1.4.1 Uygulama Zorluğu

Hibrit sistemde moment çerçevesi düğüm noktaları tam nüfuziyetli küt kaynak ile rijit bağlantı gerektirmekte; her birleşimin ultrasonik muayene (UT) ile tahribatsız kontrol sürecinden geçmesi zorunludur. Çaprazlı çerçevelerde ise guse plakası tasarımı Whitmore efektif kesit, blok kesme dayanımı ve burkulma kontrolleri gibi çok parametreli bir detaylandırma sürecini içermektedir. Sky bridge elemanları, iki bağımsız kulenin farklı titreşim periyotlarından kaynaklanan diferansiyel yer değiştirmelere maruz kaldığından kayma anahtarı, sismik derz veya sürgülü mesnet gibi özel birleşim detayları ile donatılmalıdır. Türkiye’de çelik yapı sektörü betonarmeye kıyasla oldukça dar kapsamlıdır; sertifikalı kaynak teknisyeni, çelik detay mühendisi ve bu tür karmaşık birleşimleri projelendirebilecek deneyimli yapısal tasarım bürosu sayısı sınırlı kalmaktadır [13].

### 1.4.2 Maliyet

Çelik malzemenin kilogram başına birim fiyatı betonarmeye yakın olmakla birlikte sistemin bütünü değerlendirildiğinde belirgin ek maliyet kalemleri ortaya çıkmaktadır: tam nüfuziyetli kaynak işçiliği, UT ve manyetik parçacık muayenesi (MT) gibi tahribatsız muayene süreçleri, epoksi veya galvaniz bazlı çok katmanlı korozyon koruma sistemi ve sky bridge özel çelik imalatı bunların başlıcalarıdır. Öte yandan çeliğin düşük özgül ağırlığı (γs ≈ 78.5 kN/m³≪ γc ≈ 25 kN/m³
) yapının toplam kütlesini mt ciddi oranda azaltmakta, taban kesme kuvveti VtE = mt SaR(T1) doğrudan düşmekte ve temel boyutları küçülmektedir [1]. Ayrıca fabrikada kontrollü üretim ile sahada bulonlu montaj, kalıpiskele ihtiyacını ortadan kaldırarak inşaat süresini ve işçilik maliyetini belirgin biçimde azaltmaktadır.

### 1.4.3 Sektörel Sebepler

Türkiye’de inşaat sektörü köklü bir betonarme geleneği üzerine inşa edilmiştir. Ülke genelinde çimento fabrikası, hazır beton santrali ve beton prefabrik tesisi altyapısı son derece güçlüdür; mühendislik fakültelerinde yapısal tasarım eğitimi ağırlıklı olarak betonarme üzerine şekillenmektedir. Çelik yapıların tasarım, hesap ve yapım esaslarını düzenleyen ulusal yönetmelik ÇYTHYE 2018 ancak son yıllarda yürürlüğe girmiş olup [12] sektörde çelik yapı kültürünün oluşması için yeterli süre henüz geçmemiştir. Deprem sonrası hızlı yeniden yapılanma ihtiyacı ve çeliğin sismik performans avantajları göz önüne alındığında [14] bu eğilimin değişeceği ve önerdiğimiz gibi hibrit sistemlerin ülkemizde giderek daha fazla tatbik edileceği öngörülmektedir.

### 1.5 Soru V

Soru: Deprem etkileri altında tasarıma esas iç kuvvetleri belirlemek için hangi hesap yöntemini seçtiğinizi nedenleriyle birlikte açıklayınız.
Cevap: Tasarıma esas iç kuvvetlerin tayininde Mod Birleştirme Yöntemi (MBY, TBDY 2018 Md. 4.8.2) tercih edilmiştir [1].

### 1.5.1 EDYY’nin Yetersizliği

Eşdeğer Deprem Yükü Yöntemi (EDYY, Md. 4.7.3) yapı davranışının birinci mod ile temsil edilebileceğini varsayar. Kat deprem kuvvetleri bu tek modun şekil fonksiyonuna istinaden dağıtılır. Ne var ki ikiz kule–köprü sisteminde köprü elemanları iki kulenin müstakil titreşim modlarını çiftleştirmekte; translasyonel ve torsiyonel bileşenleri müteselsilen ihtiva eden karışık modlar hasıl olmaktadır. İlk üç doğal periyot (T1 = 0.200 s, T2 = 0.147 s, T3 = 0.135 s) birbirine yakındır; birinci modun etkin kütle oranı yalnızca %42’dir. Kalan katkı üst modlara tevzi olmaktadır. Bu husus EDYY’nin esas varsayımını geçersiz kılmaktadır [1].

### 1.5.2 MBY’nin Tercih Gerekçesi

MBY’de tüm anlamlı titreşim modları ayrı ayrı göz önüne alınır. Her n. mod için azaltılmış spektral ivme SaR(Tn) = Sae(Tn)/Ra(Tn) tasarım spektrumundan okunur; modal kütle ile çarpılarak ilgili moda ait deprem kuvveti elde edilir (R = 4, D = 2.5, I = 1.0). Elde edilen modal kuvvetler elemanlarda N, V , M iç tesirlerine dönüştürülüp istatistiksel bir kaide ile tevhid edilir. İlk üç modun yakın frekansları hasebiyle modlar arası korelasyon ihmal edilemez; bu sebeple SRSS yerine CQC kuralı (ξ = 0.05) benimsenmiştir. Denk. 4.30 muktezasınca her iki doğrultuda etkin kütle oranı toplamı %95’i aşıncaya dek mod sayısı artırılmış; 12 mod ile şart sağlanmıştır [1].
Taban kesme kuvveti Md. 4.8.4 Denk. 4.31 uyarınca βtE ile kontrol edilmiş; A1a düzensizliği sebebiyle γE = 0.90 alınmıştır. Göreli kat ötelemesinde çelik yapılara mahsus κ = 0.5 (Md. 4.9.1.4) gözetilmiş; ikinci mertebe etkileri Ch = 1 ile hesaba katılmıştır (Md. 4.9.2) [1, 12].

### 1.5.3 Doğrulama ve Ölçekli Model

OpenSees®
[4] ile 1680 düğüm, 4248 elasticBeamColumn elemanlı V9 modeli tesis edilmiştir. MBY neticeleri iki müstakil yöntemle teyit edilmiştir: ZTAH (Md. 4.8.3; Düzce BOL090, 1/

√
50 ölçek, Newmark-β, ∆t = 0.005 s) ve statik itme (Md. 5.6.5; ters üçgen yük, δt = 6.12 cm) [11]. Her iki tahlilde taban kesme kuvveti ve kat ötelemesi MBY ile mutabık bulunmuştur.
TBDY 2018 usulleri gerçek ölçekli binalar için tanzim edilmiş olmakla birlikte dayandığı nazari esaslar ölçekten bağımsızdır. Özdeğer problemi, CQC ve modal süperpozisyon sırf riyazi işlemlerdir; yapının balsa (E = 3.5 GPa) yahut çelik (E = 200 GPa) olması yalnızca K ve M’yi değiştirir. Benzeşim kuramı gereğince SF = SES

2
L

, Sm = SρS

3
L

şartı
sağlandıkça bu yöntemler ölçekli modelde de mer’iyyetini muhafaza etmektedir [1].

### 1.6 Soru VI

Soru: Yapı analizinde sönüm oranının ne şekilde dikkate alındığını açıklayınız.
Cevap: Gerçek yapılarda deprem enerjisi malzeme histerezisi, birleşim sürtünmesi ve yapısal olmayan elemanlar vasıtasıyla yutulur. Bu enerji kaybı analitik modelde doğrudan temsil edilemediğinden eşdeğer viskoz sönüm oranı ξ ile idealize edilir. Sönüm, yapı tepkisini doğrudan sınırlandıran parametredir; ihmal edilmesi halinde rezonans civarında teorik olarak sonsuz genlik hasıl olur. Analizlerde ξ iki seviyede dikkate alınmıştır [1]. Spektral düzeltme. MBY’de deprem talebi tasarım spektrumundan okunur; spektrum ise belirli bir referans sönüme göre tanzim edilmiştir. TBDY 2018 ξ = %5 esas alır. Farklı ξ değerlerinde spektral ordinatlar ηb =

q
10/(5 + ξ (%)) ile tashih edilir (Md. 2.3.4): ξ = %2 → ηb = 1.195 (spektrum yükselir, talep artar), ξ = %10 → 0.816 (talep düşer). Sebebi açıktır: düşük sönümlü yapı rezonans bandında daha fazla enerji biriktirir, dolayısıyla aynı yer hareketi altında daha büyük ivme tepkisi verir. Çelik çerçeve modelimiz için ξ = %5 benimsenmiştir; bu, kaynaksız bulonlu birleşim detayı ile uyumlu alt sınır değeridir [12]. Rayleigh sönümü. ZTAH’de hareket denklemi Mu¨ + Cu˙ + Ku = −M1u¨g(t) adım adım entegre edilir; burada C sönüm matrisinin açıkça tanımlanması gerekir. Genel bir C matrisi N² bağımsız terim içereceğinden deneysel tayini imkansızdır. Rayleigh formülasyonu C = a0M + a1K bu sorunu iki parametreye indirger; M ve K’ya orantılı olduğundan modal ayrışma özelliği korunur: ξn = a0/(2ωn) + a1ωn/2. İki kontrol frekansında hedef ξ sağlanacak biçimde a0 ve a1 hesaplanır [4]. V9 modelinde ω1 = 31.43 rad/s ve ω2 = 3.5ω1 = 110.0 rad/s seçilmiş; ξ = 0.05 ile a0 = 2.443, a1 = 7.07×10⁻⁴
s elde edilmiştir. ω1–ω2 arasında sönüm hedefin altında kalır (ξmin = 0.042); yüksek frekanslı modlarda a1K terimi baskınlaşarak aşırı sönüm verir ve fiziksel anlamsız yüksek mod salınımları bastırılır (Şekil 3b).
Parametrik doğrulama. Sönümün yapısal tepkiye etkisini nicel olarak göstermek amacıyla KYH-1 (PGA = 0.335 g) altında 9 farklı ξ (%0,5–%20) ile tam ZTAH (32,2 s, 6446 adım, sıfır yakınsama hatası) icra edilmiştir (Şekil 3a). ξ = %0,5’te umax = 1,127 cm iken ξ = %5’te 0,449 cm’e, ξ = %20’de 0,319 cm’e düşmüştür. Düşük sönümde (ξ < %3) eğri dikleşir zira birinci mod rezonans bandına yaklaşır; yüksek sönümde ise eğri yataylaşır çünkü enerji yutma kapasitesi doyuma ulaşır. Bu durum sönüm seçiminin tasarımda kritik bir durum olduğunu teyit etmektedir [1].
%0.5 | %1 | %2 | %5 | %10 | %20

0.2

0.4

0.6

0.8

1

1.2

ξ =%5

Sönüm oranı ξ

umax (cm)

(a)

10⁻¹.5 | 10⁻¹ | 10⁻⁰.5

0

5 · 10⁻²

0.1

0.15

0.2

Periyot T (s)

Efektif

ξ

ξ0 | =%2
ξ0 | =%5
ξ0 | =%10

(b)

Şekil 3: (a) Çatı ötelemesi–sönüm oranı (KYH-1, ZTAH), (b) Rayleigh sönüm eğrileri.

### 1.7 Soru VII

Soru: Önerdiğiniz yapısal sistemin göreli kat ötelemelerine ve kat ivmelerine etkisi ne olacaktır?
Cevap: Üç yer hareketi kaydı (KYH-1: 0.335 g, KYH-2: 1.243 g, KYH-3: 1.896 g) altında tam ZTAH (∆t=0.005 s, 6446 adım, ξ =0.05 Rayleigh) icra edilmiştir [1, 4]. Önerilen hibrit sistemin etkisi iki esas tepki büyüklüğü üzerinden değerlendirilmiştir (Şekil 4). Göreli kat ötelemesi. Maksimum interstory drift her üç kayıt altında 12. katta teşekkül etmektedir: KYH-1’de λmax =0.439%, KYH-2’de 1.676%, KYH-3’te 3.468%. Çaprazlı çerçeveler taban katlarında rijitliği artırarak öteleme talebini düşürmekte; tepe katlarında moment çerçevesi baskınlığı sebebiyle drift azalmaktadır. Öteleme talebi orta katlarda (8–14. kat) yoğunlaşmakta olup bu husus rijitlik gradyanı ile yüksek modların (T2 = 0.147 s, T3 = 0.135 s) bu kotlarda birinci moda yakın genlikler hasıl etmesinden kaynaklanmaktadır. PGA oranı 3.71× iken drift oranı 3.82× olarak elde edilmiş; elastik modelin lineer orantılılığı teyit edilmiştir. Kule arası diferansiyel öteleme ∆ux < 0.001 cm olup sky bridge kuleleri eş-fazlı çalıştırmaktadır [10]. Tasarım depremi (KYH-1) altında λmax = 0.439% ≪ 0.8% (κ= 0.5 çelik sınırı, Md. 4.9.1.3) olup yapı öteleme güvenliğini geniş marjla sağlamaktadır [1, 12].
Kat ivmeleri. Çatı katı ivme yükseltme faktörü: KYH-1’de Ω = 3.17, KYH-2’de 2.60, KYH-3’te 3.30 (Ω¯ ≈3.0). Kısa periyotlu yapı (T1 = 0.200 s, plato bölgesi) sismik enerjiyi büyük oranda ivme olarak yapıya intikal ettirmektedir: KYH-3’te uroof =3.56 cm (%2.4) iken u¨roof =6.26 g (PGA’nın 3.3×’ı). Rijit yapıların karakteristiği budur: öteleme talebi düşük, ivme talebi yüksektir. Periyodun uzatılması Ω’yı düşürür fakat drift talebini artırır; bu mübadele yapısal sistem seçiminin esas dengeleme parametresidir. Çaprazlı çerçeveler Klateral’i artırarak T1’i düşürmekte (drift ↓, Ω ↑); moment çerçeveleri redundans ve yedek taşıyıcılık; sky bridge ise kuplajlama (∆ux≈0, ηbi =1.915) temin etmektedir [15].
0 | 1 | 2 | 3

0

5

10

15

20

25

λ (%)

Kat

KYH-1
KYH-2
KYH-3
(a) Göreli kat ötelemesi
0 | 1 | 2 | 3

0

5

10

15

20

25

ux (cm)

Kat

KYH-1
KYH-2
KYH-3
(b) Deplasman zarfı
0 | 0.5 | 1 | 1.5 | 2

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
Ω= 1

Ω= 3

KYH-1

KYH-2

KYH-3

Ω¯ ≈ 3.0

PGA (g)

¨uroof (g)

(c) Çatı ivmesi yükseltmesi

Şekil 4: Kule 1 ZTAH: (a) göreli kat ötelemesi profili (λmax: kat 12), (b) kat deplasman zarfı, (c) çatı ivmesi–PGA ilişkisi (Ω¯ ≈3).

### 1.8 Soru VIII

Soru: Önerdiğiniz yapısal sistemin tasarım depremine maruz kalması halinde oluşması muhtemel hasar durumunu yorumlayınız ve yapının deprem öncesi durumuna getirilmesinin teknik ve ekonomik açıdan fizibilitesini değerlendiriniz.
Cevap: Tasarım depremi DD-2 altında yapılan zaman tanım alanında hesap sonuçlarına göre, önerilen çelik ikiz kule sisteminin tüm kolon, kiriş ve çapraz elemanlarında kalıcı şekil değiştirme oluşmadığı, birleşim bölgelerinde akma eşiğinin çok altında kalındığı ve yapının deprem sonrası derhal kullanılabilir durumda olduğu belirlenmiştir. Köprü bağlantısındaki en kritik kiriş ucu (eleman 33) dahil 43 elemanın tümü elastik sınırlar içinde kalmaktadır. Kolonlarda gözlenen eğilme gerilmeleri taşıma kapasitesinin %9’unu geçmemekte; çaprazlarda burkulma veya kalıcı uzama riski bulunmamaktadır.
Yapıştırma birleşim kapasitesine göre TKOmax = 0.087 olup hasar eşiğinin (TKO =
0.25) çok altındadır. Eleman bazlı gerilme dağılımı Şekil 5a’da sunulmuştur. Balsa kırılma dayanımı fb = 3.5 kN/cm²

; modelde ×240 ölçekleme ile fb,m = 840 kN/cm² ’dir.
Birleşim verimi ηj = 0.35, belirleyici kapasite Mj = 10.6 kN·cm [6]. KYH-3’te en kritik eleman 33’ün TKO = 0.68 olup hâlâ elastiktir.
Göçme olasılığı Baker (2015) MLE yöntemiyle lognormal kırılganlık fonksiyonu ile hesaplanmıştır [6, 7]. 43 elemana ait ki = TKOi/PGA değeri MLE ile saptanmış; sistem kırılganlığı en zayıf halkadan (el. 33) türetilmiştir. Medyan kapasiteler: θDS-1 = 0.86 g, θgöçme = 3.45 g; belirsizlik βT = 0.57. DD-2’de P(DS-1) = %4.9, P(göçme) = 2.2 × 10⁻⁵ (Şekil 5b). Yıllık göçme olasılığı 4.5 × 10⁻⁸ ≪ 10⁻⁴
[8]. Eleman bazlı medyan göçme kapasitesi dağılımı Şekil 5c’de sunulmuştur.
1 | 5 | 10 | 15 | 20 | 25 | 30 | 35 | 40 43

0

50

100

150

200

250
El. 33

fb = 840 (ölçek dışı)

Eleman numarası

σb (kN/cm2

)

KYH-3 σb
KYH-2 σb
KYH-1 σb
(a) Eğilme gerilmesi dağılımı
0.1 | 0.2 | 0.5 | 1 | 2 | 5 | 10

0

0.2

0.4

0.6

0.8

1

El.13
DD-2

DD-1

PGA (g)

P(DS|PGA)

DS-1 (θ = 0.86) DS-2 (θ = 1.73) DS-3 (θ = 2.59)

Göçme (θ = 3.45) | 90% GA
(b) Sistem kırılganlık eğrileri (MLE)
1 | 5 | 10 | 15 | 20 | 25 | 30 | 35 | 40 | 43

0

20

40

60 | θ˜= 10.9
DD-2 | P5 | = 5.2
El. 4 | El. 13 | El. 33 | El. 36
N = 43, | kırp.
5 el.>50 g
θ˜ = 10.9 g,
θ¯= 15.3 g
CoV = 0.78,
P5 = 5.2 g
θ < 10 g:
13 el. (%30)

Eleman numarası

θgöçme (g)

(c) Eleman bazlı θgöçme,i — gri bant: IQR (Q1–Q3) Şekil 5: Hasar değerlendirmesi: (a) eğilme gerilmesi dağılımı (3 yer hareketi); (b) Baker (2015) MLE kırılganlık eğrileri (βT =0.57, gri alan: göçme %90 GA); (c) eleman bazlı θgöçme,i (gri bant IQR). En zayıf halka el. 33.

Yapısal olmayan elemanlarda hafif kozmetik hasar muhtemeldir; onarım bedeli yapı bedelinin %1–3’ü, süre 2–4 hafta. Taşıyıcı elemanlar elastik; kalıcı deformasyon sıfır [8]. Yapı Hemen Kullanım (HK) seviyesindedir [1].

## Kaynaklar

[1] T.C. Çevre ve Şehircilik Bakanlığı, Türkiye Bina Deprem Yönetmeliği (TBDY 2018), Resmi Gazete, 2018.
[2] T.C. Çevre, Şehircilik ve İklim Değişikliği Bakanlığı, TBDY 2018 Uygulama Tebliği Taslağı, 27.05.2024.
[3] AFAD, Türkiye Deprem Tehlike Haritaları İnteraktif Web Uygulaması, https://tdth.afad.gov.tr, 2024.
[4] McKenna, F., Scott, M.H., Fenves, G.L., OpenSees: Open System for Earthquake Engineering Simulation, Pacific Earthquake Engineering Research Center, UC Berkeley, https://opensees.berkeley.edu.
[5] FEMA P-751, 2009 NEHRP Recommended Seismic Provisions: Design Examples, Building Seismic Safety Council, National Institute of Building Sciences, Washington, D.C., 2012.
[6] FEMA P-58, Seismic Performance Assessment of Buildings, Federal Emergency Management Agency, Washington, D.C., 2012.
[7] Baker, J.W., “Efficient Analytical Fragility Function Fitting Using Dynamic Structural Analysis,” Earthquake Spectra, 31(1), 579–599, 2015.
[8] ASCE/SEI 41-17, Seismic Evaluation and Retrofit of Existing Buildings, American Society of Civil Engineers, Reston, Virginia, 2017.
[9] FEMA 356, Prestandard and Commentary for the Seismic Rehabilitation of Buildings, Federal Emergency Management Agency, Washington, D.C., 2000.
[10] Patoliya, N., Patel, I., Agrawal, V., Seismic Analysis of Tall Buildings Connected with Sky Bridge, IARJSET, vol. 10, 2023, doi: 10.17148/IARJSET.2023.10446.
[11] Adzetto, DASK 2026 Tasarım ve Analiz Kodları, https://github.com/adzetto/DASK_26__DESIGN_AND_ANALYSIS, (https://github.com/adzetto/DASK_26__DESIGN_AND_ANALYSIS) 2026.
[12] T.C. Çevre ve Şehircilik Bakanlığı, Çelik Yapıların Tasarım, Hesap ve Yapım Esaslarına Dair Yönetmelik (ÇYTHYE 2018), Resmi Gazete, 2018.
[13] Kurtay, C., Badem, M., Avrupa Ülkeleri ve Türkiye’deki Çelik Yapı Uygulama Olanak ve Kısıtlarının İncelenmesi, Gazi Üniversitesi Mühendislik Mimarlık Fakültesi Dergisi, cilt 19, sayı 4, ss. 351–363, 2004.
[14] Of, N., Öztürk, S., Depremlerden Sonraki Yeniden Yapılanma Süreci Üzerine Küresel Bir Araştırma: Çelik Prefabrik Malzeme Kullanımının Gerekliliği, Afet ve Risk Dergisi, cilt 5, sayı 1, ss. 346–360, 2022, doi: 10.35341/afet.1092649.
[15] Tambunan, M.L.S., Sjah, J., Rarasati, A.D., Sulistian, R., Trigunarsyah, B., Optimizing Seismic Design of Multi-Tower Buildings Using Sky Bridge Isolation and BIM: A Case Study, Int. J. Eng. Technol. Innov., vol. 14, no. 4, pp. 355–377, 2024, doi: 10.46604/ijeti.2024.13409.
