adzetto/DASK_26__DESIGN_AND_ANALYSIS/results/DASK_Design_Report_V8.md

# DASK 2026 Twin Towers - Design Report (V8)

**Date:** Feb 2, 2026  
**Model Version:** V8 (Weight Optimized)  
**Status:** ✅ Ready for Construction

## 1. Model Specifications
*   **Type:** Twin Towers with Bridges (No Podium)
*   **Dimensions:** 30 cm (W) x 16 cm (D) x 153 cm (H)
*   **Total Weight:** **1.382 kg** (Limit: 1.400 kg) ✅
    *   *Frame:* 1.323 kg
    *   *Panels:* 0.059 kg
    *   *Margin:* 18 g

## 2. Structural Configuration
*   **Core Gap (1.2cm):** **EMPTY** (Reserved for steel weights).
*   **Shear Walls:**
    *   **Floors 0-6:** 3mm Balsa Panels in the 3.4cm bays adjacent to the core.
    *   **Floors 7-25:** Checkerboard X-Bracing in 3.4cm bays.
*   **Bridges:**
    *   4 Bridges (Floors 5-6, 11-12, 17-18, 23-25).
    *   **Stiffened:** Horizontal X-bracing on Top and Bottom faces.
*   **Y-Bracing:** Minimal (Floors 0, 8, 16, 24).

## 3. Modal Analysis (Stiffness)
The structure is extremely stiff, ensuring it stays in the "Ascending" region of the design spectrum.

*   **Fundamental Period (T₁):** **0.041 s** (24.5 Hz)
*   **Target:** T < 0.061 s
*   **Region:** ✅ **Ascending (Stiff)**
*   **Mode Shapes:**
    *   *Mode 1 (Y-Dir):* Anti-Symmetric Torsion (Towers twisting against each other).
    *   *Mode 2 (X-Dir):* Anti-Symmetric Pinching.
    *   *Note:* Global sway is suppressed by high stiffness and bridge coupling.

## 4. Dynamic Earthquake Analysis (Time History)
Performed using **BOL090.AT2** Ground Motion (Bolu, Duzce 1999).

*   **Max Roof Drift:** **0.034 %**
    *   *Limit:* < 1.0% (Damage), < 0.5% (Elastic)
    *   *Status:* ✅ **SAFE (Elastic Range)**
*   **Max Base Shear:** **0.013 kN**
*   **Stress State:** Balsa elements remain well within elastic limits due to low drift.

## 5. Construction Files
*   **AutoCAD (Laser Cut):** `exports/twin_towers_v8_weights.dxf`
*   **3D Visualization:** `results/visualizations/twin_towers_3d_interactive.html`
*   **Blender Render Script:** `scripts/blender_render_script.py`

## 6. Recommendations
1.  **Glue Joints:** Ensure bridge connections are rigid. The anti-symmetric modes stress these connections.
2.  **Base Fixity:** The high stiffness relies on a solid base connection. Use ample glue at Floor 0.
3.  **Weight Placement:** Ensure the steel weights in the 1.2cm gap do not touch the columns to avoid rattling/impact during vibration.

---
*Generated by Gemini CLI Agent*
