adzetto/DASK_26__DESIGN_AND_ANALYSIS/results/visualizations/period_vs_sae_spectrum.png

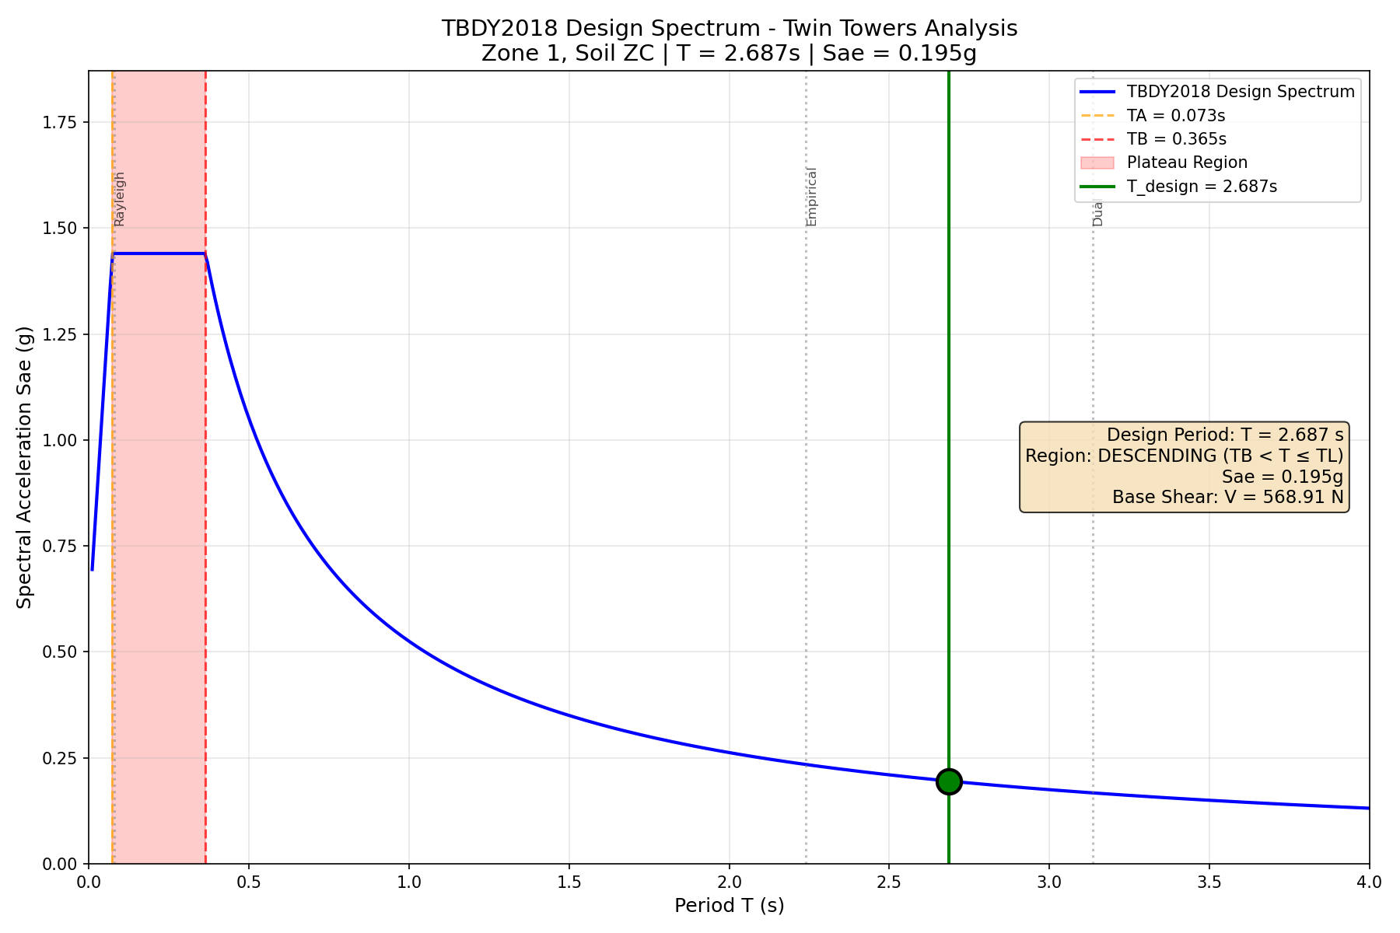
results/visualizations/period_vs_sae_spectrum.png
