adzetto/DASK_26__DESIGN_AND_ANALYSIS/results/visualizations/tbdy2018_spectrum.png

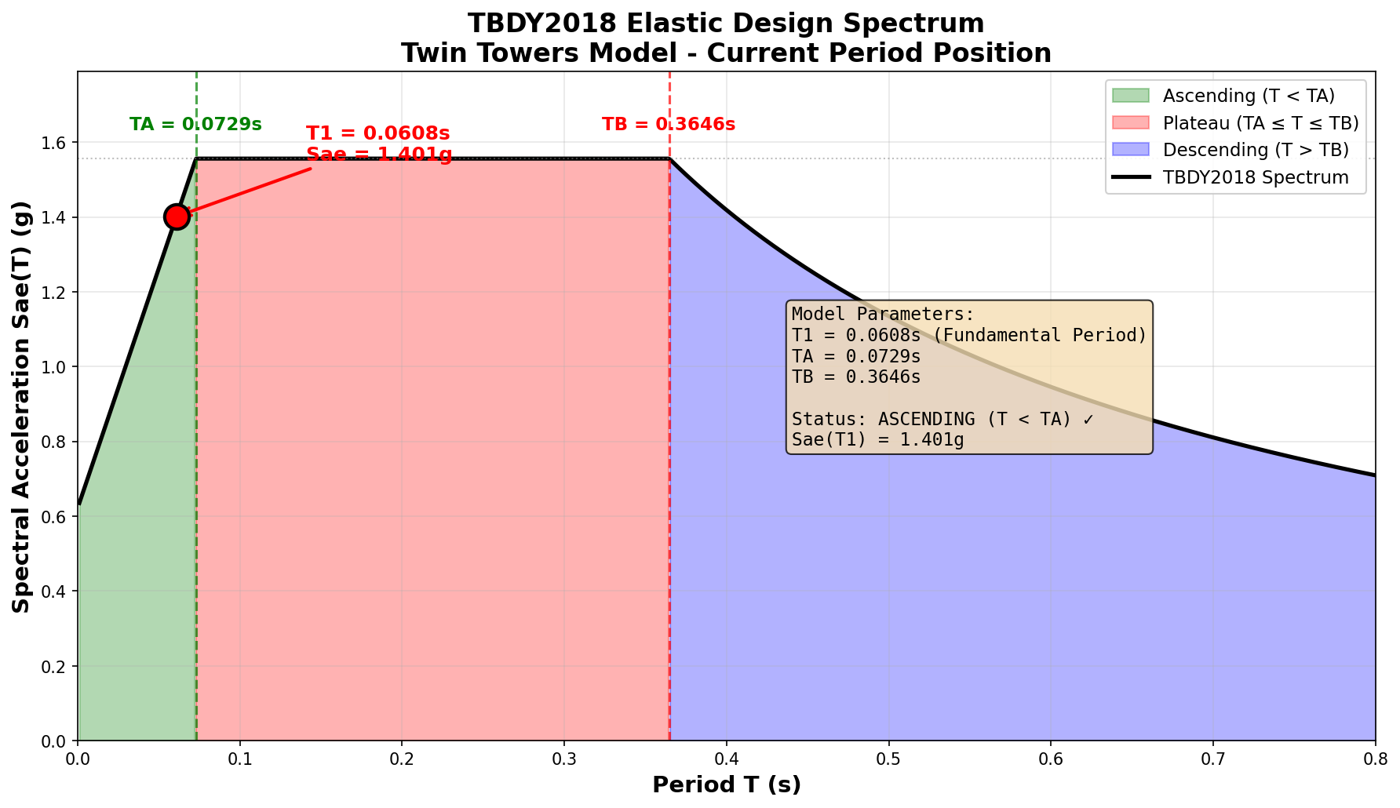
results/visualizations/tbdy2018_spectrum.png
