adzetto/DASK_26__DESIGN_AND_ANALYSIS/results/visualizations/tbdy_spectrum_check.png

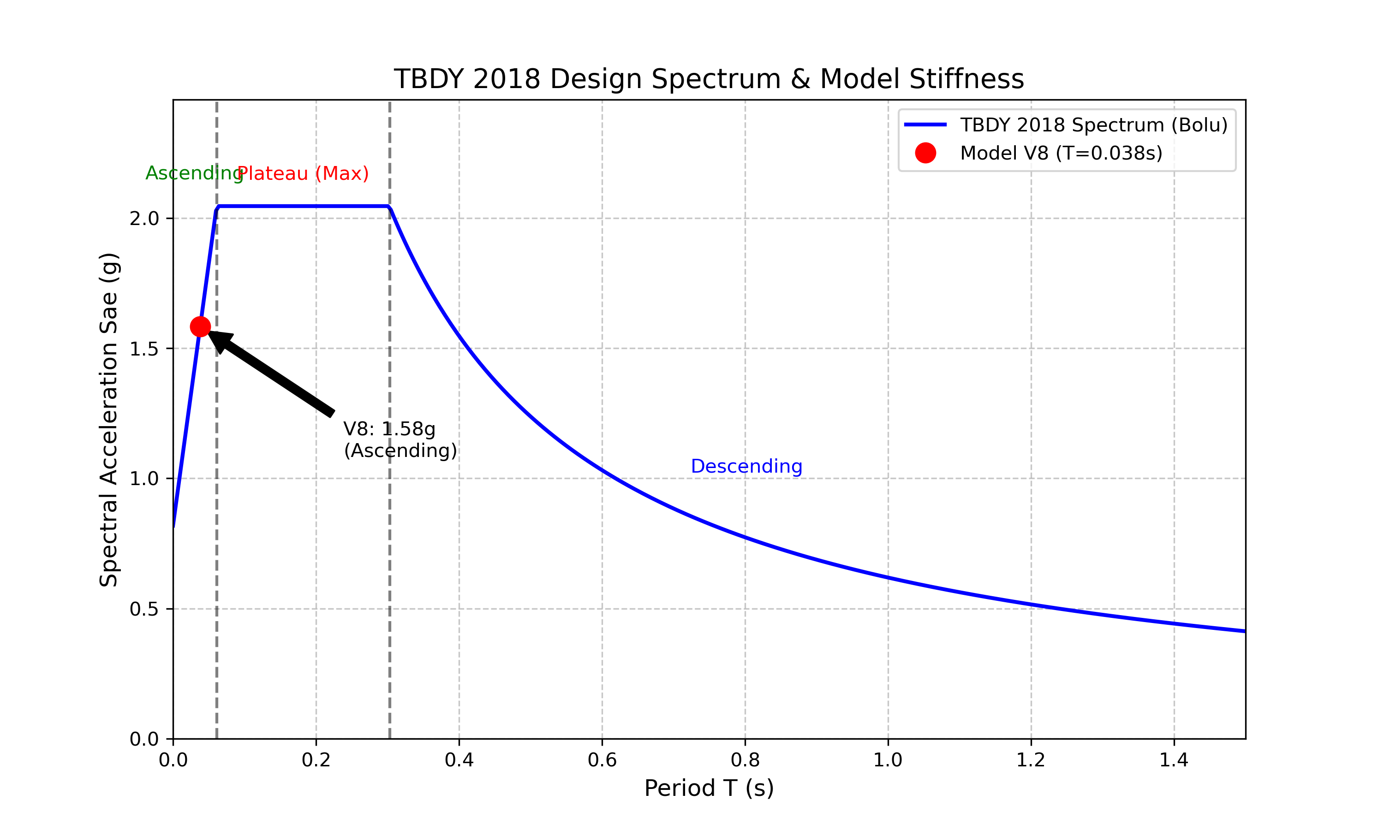
results/visualizations/tbdy_spectrum_check.png
