adzetto/DASK_26__DESIGN_AND_ANALYSIS/exports/twin_towers_v9_plan.dxf

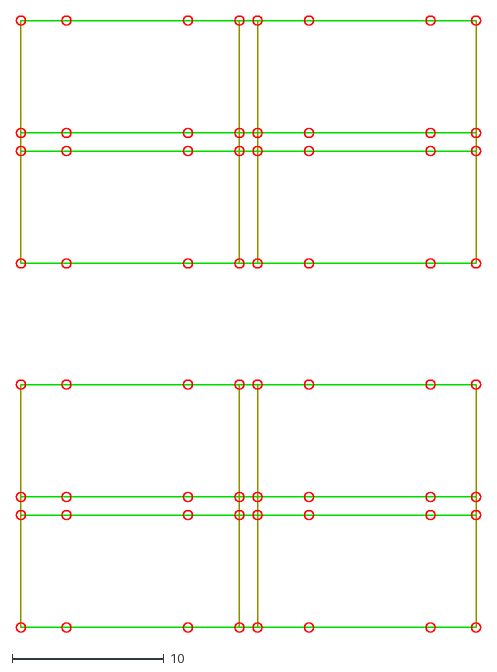
[picture p27: CAD file, 2026-02-07, an earlier design]
exports/twin_towers_v9_plan.dxf
30.6 x 40.6
