adzetto/DASK_26__DESIGN_AND_ANALYSIS/opensees_doc/OpenSeesCommandLanguageManual.txt

Open System for Earthquake Engineering Simulation (OpenSees)

OpenSees Command
Language Manual
Silvia Mazzoni, Frank McKenna, Michael H. Scott, Gregory L. Fenves,
et al.

Printed on 1 July, 2007

iii

Contents
Introduction

11

Notation ........................................................................................................................................11
Copyright ......................................................................................................................................13
Introduction to the Tcl command language ..................................................................................14
Tcl Commands Format.................................................................................................................15
Example Tcl Commands ..............................................................................................................16
Additional Tcl Resources .............................................................................................................17
OpenSees Interpreter...................................................................................................................18

OpenSees

19

OpenSees Features .....................................................................................................................21
WHY OPENSEES? ......................................................................................................................21
+ The library of materials, elements and analysis commands makes OpenSees a powerful tool
for numerical simulation of nonlinear structural and geotechnical systems ......................21
+ The OpenSees library of components is ever-growing and at the leading edge of
numerical-simulation models .............................................................................................21
+ The OpenSees interface is based on a command-driven scripting language which enables
the user to create more-versatile input files.......................................................................21
+ OpenSees is not a black box, making it a useful educational tool for numerical modeling21
+ You can create your own material, element or analysis tools and incorporate them into
OpenSees ..........................................................................................................................21
+ NEES is supporting integration of OpenSees as the simulation component of laboratory
testing.................................................................................................................................21
MODELS: .....................................................................................................................................22
+ linear & nonlinear structural and geotechnical models ...................................................22
SIMULATIONS: ............................................................................................................................23
+ static push-over analyses ...............................................................................................23
+ static reversed-cyclic analyses .......................................................................................23
+ dynamic time-series analyses.........................................................................................23
+ uniform-support excitation...............................................................................................23
+ multi-support excitation ...................................................................................................23
MODELING FEATURES: .............................................................................................................23
MODEL-BUILDING FEATURES: .................................................................................................24
ANALYSIS FEATURES:...............................................................................................................26
ModelBuilder Object .....................................................................................................................29
Domain Object..............................................................................................................................30
Recorder Object ...........................................................................................................................31
Analysis Object.............................................................................................................................31

Model-Building Objects

33

model Command

34

Basic Model Builder......................................................................................................................34
build Command ............................................................................................................................35

node Command

36

mass Command

37

Contents

constraints objects

iv

38

Single-Point Constraints...............................................................................................................38
fix Command ................................................................................................................................38
fixX Command..............................................................................................................................39
fixY Command..............................................................................................................................39
fixZ Command ..............................................................................................................................40
Multi-Point Constraints .................................................................................................................41
equalDOF Command ...................................................................................................................41
rigidDiaphragm Command ...........................................................................................................41
rigidLink Command ......................................................................................................................42

uniaxialMaterial Command

43

-- Contributed Uniaxial Materials

44

BARSLIP Material ........................................................................................................................44
Concrete04 Material -- Popovics Concrete Material ....................................................................57

Concrete04 -- Material Behavior

61

FatigueMaterialExample.tcl

63

Limit State Material

73

Shear Limit Curve.........................................................................................................................74
Axial Limit Curve ..........................................................................................................................75
Shear Limit Curve.........................................................................................................................76
Example Files for Limit State Material..........................................................................................78
PINCHING4 Material ....................................................................................................................84
PINCHING4 Uniaxial Material Model Discussion.........................................................................90
PyTzQz Uniaxial Materials .........................................................................................................104
PySimple1 Material ....................................................................................................................104
TzSimple1 Material.....................................................................................................................105
QzSimple1 Material ....................................................................................................................106
PyLiq1 Material...........................................................................................................................107
TzLiq1 Material...........................................................................................................................108
PySimple1Gen Command..........................................................................................................110
TzSimple1Gen Command..........................................................................................................111

ReinforcingSteel -- Material Behavior

125

Elastic Material ...........................................................................................................................125
Elastic-Perfectly Plastic Material ................................................................................................126
Elastic-Perfectly Plastic Gap Material ........................................................................................128
Elastic-No Tension Material .......................................................................................................129
Parallel Material..........................................................................................................................130
Series Material ...........................................................................................................................131
Hardening Material .....................................................................................................................133
Concrete01 Material -- Zero Tensile Strength............................................................................134

Concrete01 -- Material Behavior

137

Concrete02 Material -- Linear Tension Softening ......................................................................137

Concrete02 -- Material Behavior

143

Concrete03 Material -- Nonlinear Tension Softening................................................................143

Concrete03 -- Material Behavior

147

Contents

v

Steel01 Material .........................................................................................................................147

Steel01 -- Material Behavior

152

Steel02 Material -- Giuffré-Menegotto-Pinto Model with Isotropic Strain Hardening .................153

Steel02 -- Material Behavior

158

Hysteretic Material......................................................................................................................158

Hysteretic -- Material Behavior

161

Viscous Material .........................................................................................................................161

nDMaterial Command

162

Elastic Isotropic Material ............................................................................................................162
J2 Plasticity Material...................................................................................................................163
Plane Stress Material .................................................................................................................163
Plate Fiber Material ....................................................................................................................164
UC Davis Soil Models.................................................................................................................164
Template Elasto-Plastic Material................................................................................................164
UCSD Soil Models......................................................................................................................169

section Command

191

Elastic Section............................................................................................................................192
Uniaxial Section..........................................................................................................................193
Fiber Section ..............................................................................................................................194
Fiber Command..........................................................................................................................196
Quadrilateral Patch Command...................................................................................................197
Circular Patch Command ...........................................................................................................199
Straight Layer Command ...........................................................................................................201
Circular Layer Command ...........................................................................................................202
Section Aggregator.....................................................................................................................203
Elastic Membrane Plate Section ................................................................................................205
Plate Fiber Section .....................................................................................................................205
Bidirectional Section...................................................................................................................206
Isolator2spring Section: Model to include buckling behavior of an elastomeric bearing ..........207

element Command

215

Contents

vi

Truss Element ............................................................................................................................215
Corotational Truss Element........................................................................................................216
Elastic Beam Column Element...................................................................................................217
NonLinear Beam-Column Elements...........................................................................................218
Nonlinear Beam Column Element..............................................................................................218
Beam With Hinges Element .......................................................................................................219
Displacement-Based Beam-Column Element............................................................................223
Zero-Length Elements................................................................................................................223
Zero-Length Element..................................................................................................................224
Zero-Length ND Element ...........................................................................................................225
Zero-Length Section Element ....................................................................................................226
Quadrilateral Elements...............................................................................................................227
Quad Element ............................................................................................................................227
Shell Element .............................................................................................................................228
Bbar Plane Strain Quadrilateral Element ...................................................................................228
Enhanced Strain Quadrilateral Element.....................................................................................229
Brick Elements ...........................................................................................................................230
Standard Brick Element..............................................................................................................230
Bbar Brick Element.....................................................................................................................231
BeamColumnJoint Element........................................................................................................232
Beam-Column Joint Element Discussion ...................................................................................236

Beam-Column Joint Element Discussion

236

UC Davis Soil Elements .............................................................................................................256
FourNodeQuadUP Element .......................................................................................................256
u-p-U element.............................................................................................................................258
Eight Node Brick Element ..........................................................................................................259
Twenty Node Brick Element.......................................................................................................261

UC San Diego Soil Elements

263

block Command

273

block2D Command.....................................................................................................................274
block3D Command.....................................................................................................................276

region Command

278

Geometric Transformation Command

280

Linear Transformation ................................................................................................................280
P-Delta Transformation ..............................................................................................................286
Corotational Transformation.......................................................................................................287

Time Series

288

Constant Time Series.................................................................................................................289
Linear Time Series .....................................................................................................................289
Rectangular Time Series............................................................................................................290
Sine Time Series ........................................................................................................................291
Path Time Series........................................................................................................................292

pattern Command

294

Contents

vii

plain Pattern ...............................................................................................................................294
load Command ...........................................................................................................................295
sp Command ..............................................................................................................................296
eleLoad Command .....................................................................................................................297
UniformExcitation Pattern ..........................................................................................................298
MultipleSupport Pattern..............................................................................................................299
groundMotion Command............................................................................................................299
Plain GroundMotion....................................................................................................................300
Interpolated GroundMotion ........................................................................................................301
imposedMotion Command .........................................................................................................301

Recorder Objects

303

Node Recorder ...........................................................................................................................303
EnvelopeNode Recorder ............................................................................................................305
Drift Recorder .............................................................................................................................306
Element Recorder ......................................................................................................................307
EnvelopeElement Recorder .......................................................................................................309
Display Recorder........................................................................................................................310
Plot Recorder .............................................................................................................................311
playback Command....................................................................................................................311

Analysis Objects

313

constraints Command

316

Plain Constraints ........................................................................................................................318
Penalty Method ..........................................................................................................................318
Lagrange Multipliers ...................................................................................................................319
Transformation Method ..............................................................................................................320

numberer Command

321

Plain Numberer ..........................................................................................................................321
RCM Numberer ..........................................................................................................................322

system Command

323

BandGeneral SOE......................................................................................................................324
BandSPD SOE ...........................................................................................................................324
ProfileSPD SOE .........................................................................................................................324
SparseGeneral SOE...................................................................................................................324
UmfPack SOE ............................................................................................................................325
SparseSPD SOE ........................................................................................................................325

test Command

326

Norm Unbalance Test ................................................................................................................326
Norm Displacement Increment Test...........................................................................................327
Energy Increment Test...............................................................................................................328

algorithm Command

329

Linear Algorithm .........................................................................................................................329
Newton Algorithm .......................................................................................................................329
Newton with Line Search Algorithm ...........................................................................................330
Modified Newton Algorithm ........................................................................................................331
Krylov-Newton Algorithm............................................................................................................331
BFGS Algorithm .........................................................................................................................331
Broyden Algorithm......................................................................................................................332

integrator Command

333

Contents

viii

Load Control...............................................................................................................................334
Displacement Control .................................................................................................................335
Minimum Unbalanced Displacement Norm................................................................................336
Arc-Length Control .....................................................................................................................336
Newmark Method .......................................................................................................................337
Hilbert-Hughes-Taylor Method ...................................................................................................338

analysis Command

339

Static Analysis ............................................................................................................................339
Transient Analysis ......................................................................................................................340
VariableTransient Analysis.........................................................................................................341

rayleigh command

342

eigen Command

343

analyze Command

344

dataBase Commands

345

FileDatastore Command ............................................................................................................345
save Command ..........................................................................................................................346
restore Command.......................................................................................................................346

Miscellaneous Commands

347

print Command...........................................................................................................................347
reset Command..........................................................................................................................348
wipe Command ..........................................................................................................................348
wipeAnalysis Command .............................................................................................................348
loadConst Command..................................................................................................................349
getTime Command.....................................................................................................................349
nodeDisp Command...................................................................................................................349
video Command .........................................................................................................................350
play Command ...........................................................................................................................351
nodeBounds ...............................................................................................................................351
display Command.......................................................................................................................352

How To....

353

Run OpenSees...........................................................................................................................354
...Define Units & Constants ........................................................................................................356
...Generate Matlab Commands ..................................................................................................357
...Define Tcl Procedure...............................................................................................................357
...Read External files ..................................................................................................................359
Building The Model.....................................................................................................................360
...Define Variables and Parameters .................................................................................360
...Build Model and Define Nodes .....................................................................................363
...Build Model and Define Nodes using Variables............................................................364
...Define Materials ............................................................................................................364
...Define Elements............................................................................................................365
Defining Output ..........................................................................................................................366
...Define Analysis-Output Generation ..............................................................................366
...Define Data-Plot During Analysis..................................................................................368
Gravity Loads .............................................................................................................................369
...Define Gravity Loads ....................................................................................................369
...Run Gravity Analysis.....................................................................................................370
Static Analysis ............................................................................................................................370
...Define Static Pushover Analysis ...................................................................................370

Contents

ix

...Run Static Pushover Analysis.......................................................................................371
Dynamic Analysis .......................................................................................................................372
...Define Dynamic Ground-Motion Analysis .....................................................................372
...Run Dynamic Ground-Motion Analysis ...................................................................................373
...Combine Input-File Components ............................................................................................373
...Run Parameter Study..............................................................................................................374
...Run Moment-Curvature Analysis on Section ..........................................................................376
...Determine Natural Period & Frequency ..................................................................................377

Getting Started with OpenSees

379

Introduction.................................................................................................................................381
Download OpenSees .................................................................................................................382
Run OpenSees...........................................................................................................................384
Problem Definition ......................................................................................................................386
Model Builder .............................................................................................................................387
Nodes .........................................................................................................................................388
Elements ....................................................................................................................................390
Recorders ...................................................................................................................................391
Summary of Model-Building Input File .......................................................................................391
Loads and Analysis ....................................................................................................................394
1. Load definition ........................................................................................................................394
2. Analysis definition and features .............................................................................................395
3. Analysis execution..................................................................................................................396
Gravity Loads .............................................................................................................................396
Summary of Gravity Loads.........................................................................................................399
Lateral Loads -- Static Pushover................................................................................................400
Lateral Loads -- Cyclic Lateral Load ..........................................................................................401
Lateral Loads -- Dynamic ground motion ...................................................................................402

Getting Going with OpenSees (under development)

406

Problem Definition ......................................................................................................................407
Model Building............................................................................................................................408
Variables and Units ....................................................................................................................408
Model Builder .............................................................................................................................410
Nodal Coordinates & Masses, Boundary Conditions .................................................................410
Materials .....................................................................................................................................411
Element Cross Section...............................................................................................................412
Elements and Element Connectivity ..........................................................................................413
Gravity and other Constant Loads .............................................................................................414
Summary of Defining Structural Model ......................................................................................414
Error-Checking Tip for Model Building .......................................................................................419
Recorders for Output..................................................................................................................425

Analysis Components

426

Script Utilities Library

427

Contents

x

matTest.tcl..................................................................................................................................427
RCcircSection.tcl ........................................................................................................................429
RCcircSectionFEDEAS.tcl .........................................................................................................430
RCFrameDisplay.tcl ...................................................................................................................432
MomentCurvature.tcl ..................................................................................................................433
ReadSMDFile.tcl ........................................................................................................................434
RotSpring2D...............................................................................................................................436
StFramePZLdisplay.tcl ...............................................................................................................437
Wsection.tcl ................................................................................................................................437
RigidFrame3Ddisplay.tcl ............................................................................................................438
Units&Constants.tcl ....................................................................................................................439
MatlabOutput.tcl .........................................................................................................................440
genPlaneFrame.tcl .....................................................................................................................440

References

443

Index

447

11

CHAPTER 1

Introduction
This document is intended to outline the basic commands currently available with the OpenSees
interpreter. This interpreter is an extension of the Tcl/Tk language for use with OpenSees.
OpenSees is an object-oriented framework for finite element analysis. OpenSees' intended users
are in the research community. A key feature of OpenSees is the interchangeability of
components and the ability to integrate existing libraries and new components into the framework
(not just new element classes) without the need to change the existing code. Core components,
that is the abstract base classes, define the minimal interface (minimal to make adding new
component classes easier but large enough to ensure all that is required can be accommodated).

In This Chapter
Notation.................................................................... 11
Copyright.................................................................. 13
Introduction to the Tcl command language ............... 14
OpenSees Interpreter............................................... 18

Notation
The notation presented in this chapter is used throughout this document.
Input values are a string, unless the first character is a $, in which case an integer, floating point
number or variable is to be provided. In the Tcl language, variable references start with the $
character. Tcl expressions can also be used as input to the commands where the input value is
specified by the first character being a $.
Optional values are identified in enclosing <> braces.
When specifying a variable quantity of values, the command line contains (x $values). The
number of values required, x, and the types of values, $values, are specified in the description of
the command.
An arbitrary number of input values is indicated with the dot-dot-dot notation, i.e. $value1 $value2
...

Chapter 1

Introduction

12

The OpenSees interpreter constructs objects in the order they are specified by the user. New
objects are often based on previously-defined objects. When specified as an object parameter, a
previously-defined object must have already been added to the Domain. This requirement is
specified in the description of the command arguments.
Also, and very important:
Do not use greek fonts ANYWHERE in your documentation, not only do they not come out in Html,
they are not allowed in tcl, which is where this is important. I recommend spelling out the letters:
alpha, beta, gamma, eps (short for epsilon), etc.
I recommend to not use them in your figures either, as you would be unable to refer to them. If you
must use them you have to do it very carefully, as it may be okey for internal variables.

Example command:

node $nodeTag (ndm $coords) <-mass (ndf $MassValues)>
This line executes the node command (page 36) assigns coordinates and masses to a specified
node. The $nodeTag argument is an integer tag identifying the node.The coordinate arguments
are specified with the parentheses () because the number of arguments is dependent on the
definition of the model (ndm (page 34)): two arguments in 2D and three in 3D.
The mass specification at the node definition is optional. Therefore, it is enclosed in <> braces.
The number of mass arguments is also dependent on the model definition, depending on the
number of degrees of freedom assigned to a node (ndf (page 34)).

Chapter 1

Introduction

13

Copyright
Copyright © 1999,2000 The Regents of the University of California. All Rights Reserved.
Permission to use, copy, modify, and distribute this software and its documentation for
educational, research and non-profit purposes, without fee, and without a written agreement is
hereby granted, provided that the above copyright notice, this paragraph and the following three
paragraphs appear in all copies.
Permission to incorporate this software into commercial products may be obtained by contacting
the University of California. [Bill Hoskins Office of Technology Licensing, 2150 Shattuck Avenue
#150 Berkeley, CA 94720-1620, (510) 643-7201]
This software program and documentation are copyrighted by The Regents of the University of
California. The software program and documentation are supplied "as is", without any
accompanying services from The Regents. The Regents does not warrant that the operation of
the program will be uninterrupted or error-free. The end-user understands that the program was
developed for research purposes and is advised not to rely exclusively on the program for any
reason.
IN NO EVENT SHALL THE UNIVERSITY OF CALIFORNIA BE LIABLE TO ANY PARTY FOR
DIRECT, INDIRECT, SPECIAL, INCIDENTAL, OR CONSEQUENTIAL DAMAGES, INCLUDING
LOST PROFITS, ARISING OUT OF THE USE OF THIS SOFTWARE AND ITS
DOCUMENTATION, EVEN IF THE UNIVERSITY OF CALIFORNIA HAS BEEN ADVISED OF
THE POSSIBILITY OF SUCH DAMAGE. THE UNIVERSITY OF CALIFORNIA SPECIFICALLY
DISCLAIMS ANY WARRANTIES, INCLUDING, BUT NOT LIMITED TO, THE IMPLIED
WARRANTIES OF MERCHANTABILITY AND FITNESS FOR A PARTICULAR PURPOSE. THE
SOFTWARE PROVIDED HEREUNDER IS ON AN "AS IS" BASIS, AND THE UNIVERSITY OF
CALIFORNIA HAS NO OBLIGATIONS TO PROVIDE MAINTENANCE, SUPPORT, UPDATES,
ENHANCEMENTS, OR MODIFICATIONS.

Chapter 1

Introduction

14

Introduction to the Tcl command language
The Tcl scripting language was chosen to support the OpenSees commands, which are used to
define the problem geometry, loading, formulation and solution. These commands are one-line
commands which have specific tasks, as described in this manual. The Tcl language provides
useful programming tools, such as variables manipulation, mathematical-expression evaluation
and control structures.
Tcl is a string-based scripting language which allows the following:

Variables and variable substitution
Mathematical-expression evaluation

Basic control structures (if , while, for, foreach)

Procedures

File manipulation

More information on Tcl commands can be found at its web site: Tcl/Tk Primer
(http://dev.scriptics.com/scripting/primer.html) (http://dev.scriptics.com/scripting/primer.html)

Handy Tcl commands:

incr - Increment the value of a variable:
set a 1
incr a

a book reference:
Brent Welch <welch@acm.org>, Ken Jones, and Jeff Hobbs: Practical Programming in Tcl and
Tk, (http://www.beedub.com/book/) 4th Edition ISBN: 0-13-038560-3, June, 2003
(http://www.beedub.com/book/)

Chapter 1

Introduction

15

Tcl Commands Format
Tcl scripts are made up of commands separated by new lines or semicolon (;).
The basic syntax for a Tcl command is:

command $arg1 $arg2 ...
command

name of the Tcl command or user-defined procedure

$arg1 $arg2 ...

arguments for the command

Tcl allows any argument to be nested command:

command [nested-command1] [nested-command2]
where the [] are used to delimit the nested commands. The Tcl interpreter will first evaluate the
nested commands and will then evaluate the outer command with the results to the nested
commands.
The most basic command in Tcl is the set command:

set variable $value
for example:
set a 5

The Tcl interpreter regards a command starting with the pond sign (#) to be a comment statement,
so it does not execute anything following the #. For example:
# this command assigns the value 5 to the variable a
set a 5

The pound sign and the semicolon can be used together to put comments on the same line as the
command. For example:
set a 5; # this command assigns the value 5 to the variable a

Chapter 1

Introduction

Example Tcl Commands
arithmetic

procedure

for & foreach functions

>set a 1

>proc sum {a b} {

for {set i 1} {$i < 10} {incr i 1} {

1

return [expr $a + $b]

puts “i equals $i”

>set b a

}

}

a

>sum 2 3

>set b $a

5

1

>set c [sum 2 3]

set sum 0

>expr 2 + 3

5

foreach value {1 2 3 4} {

5

>

set sum [expr $sum +
$value]

>expr 2 + $a

}

3

puts $sum

>set b [expr 2 + $a]

10

3

>

>
file manipulation

procedure & if statement

>set fileId [open tmp w]

>proc guess {value} {

anumber

global sum

>puts $fileId “hello”

if {$value < $sum} {
puts “too low”

>close $fileID
>type tmp

} else {
if {$value > $sum} {

hello
>

puts “too high”
} else { puts “you got it!”}
}

>source Example1.tcl

}
> guess 9
too low
>

16

Chapter 1

Introduction

Additional Tcl Resources
Here are additional resources for Tcl:

http://www.freeprogrammingresources.com/tcl.html
(http://www.freeprogrammingresources.com/tcl.html)
(a large list of helpful resources)

http://www.tcl.tk/man/ (http://www.tcl.tk/man/)
(Tcl/Tk manual pages)

http://www.mit.edu/afs/sipb/user/golem/doc/tcltk-iap2000/TclTk1.html
(http://www.mit.edu/afs/sipb/user/golem/doc/tcltk-iap2000/TclTk1.html)
(a tutorial describing many commands by describing their implementation in a short
program)

http://www.beedub.com/book/ (http://www.beedub.com/book/)
(some sample chapters from Practical Programming in Tcl and Tk, by Welch and
Jones)

http://philip.greenspun.com/tcl/ (http://philip.greenspun.com/tcl/)
(not the most readable tutorial IMHO, but it does have Tickle-me-Elmo ;) It can be
accessed from the link below as well.)
http://www.tcl.tk/scripting/ (http://www.tcl.tk/scripting/)

17

Chapter 1

Introduction

18

http://hegel.ittc.ukans.edu/topics/tcltk/tutorial-noplugin/index.html
(http://hegel.ittc.ukans.edu/topics/tcltk/tutorial-noplugin/index.html)
(a short tutorial on the essential Tcl commands, also includes a manual of Tcl/Tk
commands at the website below)
http://hegel.ittc.ukans.edu/topics/linux/man-pages/index/index-mann.html
(http://hegel.ittc.ukans.edu/topics/linux/man-pages/index/index-mann.html)

http://pages.cpsc.ucalgary.ca/~saul/personal/archives/Tcl-Tk_stuff/tcl_examples/
(http://pages.cpsc.ucalgary.ca/~saul/personal/archives/Tcl-Tk_stuff/tcl_examples/)
(Tk widgets with screenshots)

OpenSees Interpreter
The main abstractions of OpenSees will be explained using the OpenSees interpreter. The
interpreter is an extension of the Tcl (page 15) scripting language. The OpenSees interpreter adds
commands to Tcl for finite element analysis. Each of these commands is associated (bound) with
a C++ procedure that is provided. It is this procedure that is called upon by the interpreter to parse
the command. In this document we outline only those commands which have been added to Tcl by
OpenSees.
For OpenSees we have added commands to Tcl for finite element analysis:

Modeling – create nodes, elements, loads and constraints

Analysis – specify the analysis procedure.

Output specification – specify what it is you want to monitor during the analysis.

 HELP
OpenSees Documentation Web Page (http://opensees.berkeley.edu/OpenSees/primer.html)
http://opensees.berkeley.edu/cgi-bin/OpenSeesCommands.pl
(http://opensees.berkeley.edu/cgi-bin/OpenSeesCommands.pl)

19

CHAPTER 2

OpenSees
 What is OpenSees?

•ᾉAn object-oriented software framework for simulation applications in earthquake engineering using
finite element methods. OpenSees is not a code.

•ᾉA communication mechanism within PEER for exchanging and building upon research
accomplishments.

•ᾉAs open-source software, it has the potential for a community code for earthquake engineering.

Chapter 2

In This Chapter
OpenSees Features ................................................. 21
ModelBuilder Object ................................................. 29
Domain Object ......................................................... 30
Recorder Object ....................................................... 31
Analysis Object ........................................................ 31

OpenSees

20

Chapter 2

21

OpenSees Features
+ The library of materials, elements and analysis c
powerful tool for numerical simulation of nonlinea
systems
+ The OpenSees library of components is ever-gro
numerical-simulation models
+ The OpenSees interface is based on a command
enables the user to create more-versatile input files.
+ OpenSees is not a black box, making it a useful
modeling
+ You can create your own material, element or an
into OpenSees
+ NEES is supporting integration of OpenSees as
laboratory testing

WHY OPENSEES?

Chapter 2

MODELS:
+ linear & nonlinear structural and
geotechnical models

22

Chapter 2

SIMULATIONS:
+ static push-over analyses
+ static reversed-cyclic analyses
+ dynamic time-series analyses
+ uniform-support excitation
+ multi-support excitation

MODELING FEATURES:
 MODEL-BUILDING CAPABILITIES:

model command (page 34)

node command (page 36)

mass command (page 37)
constraints objects

uniaxialMaterial command (page 43)

nDMaterial command (page 162)

section command (page 191)
element command (page 215)

block command (page 273)

region command
Geometric Transformation command (page 280)

23

Chapter 2

Time Series command (page 288)

pattern command (page 294)

 ANALYSIS CAPABILITIES

constraints command (page 316)

numberer command (page 321)

system command (page 323)
test command (page 326)

algorithm command (page 329)

integrator command (page 333)

analysis command (page 339)
rayleigh command (page 342)

eigen command (page 343)

dataBase command

 RECORDER/OUTPUT CAPABILITIES

Node Recorder (page 303)

EnvelopeNode Recorder
Drift Recorder

Element Recorder (page 307)

EnvelopeElement Recorder

Display Recorder (page 310)
Plot Recorder

playback Command

MODEL-BUILDING FEATURES:
 UNIAXIAL MATERIALS (page 43):

24

Chapter 2

25

Elastic Material (page 125)

Elastic-Perfectly Plastic Material

Elastic-Perfectly Plastic Gap Material
Elastic-No Tension Material

Parallel Material

Series Material

Hardening Material
Concrete01 Material -- Zero Tensile Strength (page 134)

Concrete02 Material -- Linear Tension Softening (page 137)

Concrete03 Material -- Nonlinear Tension Softening (page 143)

Steel01 Material (page 147)
Steel02 Material -- Giuffré-Menegotto-Pinto Model with Isotropic Strain Hardening (page 153)

Hysteretic Material (page 158)

Viscous Material

BARSLIP Material
Bond_SP01 - - Strain Penetration Model for Fully Anchored Steel Reinforcing Bars

Concrete04 Material -- Popovics Concrete Material (page 57)

Fatigue Material

Limit State Material
PINCHING4 Material (page 84)

PyTzQz Uniaxial Materials

Reinforcing Steel Material

 MULTIDIMENSIONAL/nD MATERIALS:

Elastic Isotropic Material (page 162)

J2 Plasticity Material
Plane Stress Material

Plate Fiber Material (page 164)

Template Elasto-Plastic Material

FluidSolidPorousMaterial Material
PressureIndependMultiYield Material

PressureDependMultiYield Material

 ELEMENTS:

Truss Element

Corotational Truss Element

Chapter 2

Elastic Beam Column Element (page 217)

Nonlinear Beam Column Element (page 218)

Beam With Hinges Element (page 219)
Displacement-Based Beam-Column Element (page 223)

Zero-Length Element

Zero-Length ND Element

Zero-Length Section Element (page 226)
Quad Element

Shell Element

Bbar Plane Strain Quadrilateral Element (page 228)

Enhanced Strain Quadrilateral Element
Standard Brick Element

Bbar Brick Element

Eight Node Brick Element (page 259)

Twenty Node Brick Element
u-p-U element

FourNodeQuadUP Element (page 256)

BeamColumnJoint Element

26

 SECTIONS:

Elastic Section (page 192)

Uniaxial Section (page 193)
Fiber Section (page 194)

Section Aggregator

Elastic Membrane Plate Section

Plate Fiber Section (page 205)
Bidirectional Section

Isolator2spring Section: Model to include buckling behavior of an elastomeric bearing

ANALYSIS FEATURES:
 Linear Equation Solvers (page 323) -- provide the solution of the linear system
of equations Ku = P. Each solver is tailored to a specific matrix topology.

Chapter 2

27

Profile SPD (page 324) -- Direct profile solver for symmetric positive definite matrices

Band General -- Direct solver for banded unsymmetric matrices

Band SPD -- Direct solver for banded symmetric positive definite matrices
Sparse General -- Direct solver for unsymmetric sparse matrices

Sparse Symmetric -- Direct solver for symmetric sparse matrices

UmfPack General -- Direct UmfPack solver for unsymmetric matrices

Full General -- Direct solver for unsymmetric dense matrices
Conjugate Gradient -- Iterative solver using the preconditioned conjugate gradient method

 Eigenvalue Solvers -- provide the solution of the generalized eigenvalue
problem Kv = MvL

Symmetric Arpack -- Arpack solver for symmetric matrices
Band Arpack -- Arpack solver for banded matrices

 DOF Numberers (page 321) -- number the degrees of freedom in the domain

Plain (page 321) -- Uses the numbering provided by the user

RCM (page 322) -- Renumbers the DOF to minimize the matrix band-width using the Reverse
Cuthill-McKee algorithm

 Static Integrators (page 333) -- determine the next time step for an analysis

Load Control (page 334) -- Specifies the incremental load factor to be applied to the loads in
the domain

Displacement Control (page 335) -- Specifies the incremental displacement at a specified DOF
in the domain

Minimum Unbalanced Displacement Norm (page 336) -- Specifies the incremental load factor
such that the residual displacement norm in minimized

Arc Length (page 336) -- Specifies the incremental arc-length of the load-displacement path

 Transient Integrators (page 333) -- determine the next time step for an analysis
including inertial effects

Newmark (page 337) -- The two parameter time-stepping method developed by Newmark

Hilbert-Hughes-Taylor (page 338) -- The three parameter Hilbert-Hughes-Taylor time-stepping
method

Central Difference -- Approximates velocity and acceleration by centered finite differences of
displacement

Chapter 2

28

 Solution Algorithms (page 329) -- Iterate from the last time step to the current

Linear Algorithm -- Uses the solution at the first iteration and continues

Newton Algorithm (page 329) -- Uses the tangent at the current iteration to iterate to
convergence

Modified Newton Algorithm -- Uses the tangent at the first iteration to iterate to convergence
Newton with Line Search Algorithm

Krylov-Newton Algorithm

BFGS Algorithm
Broyden Algorithm

 Convergence Tests (page 326) -- Accept the current state of the domain as
being on the converged solution path

Norm Unbalance -- Specifies a tolerance on the norm of the unbalanced load at the current
iteration

Norm Displacement Increment -- Specifies a tolerance on the norm of the displacement
increments at the current iteration

Energy Increment -- Specifies a tolerance on the inner product of the unbalanced load and
displacement increments at the current iteration
Relative Unbalance

Relative Displacement Increment

Relative Energy Increment

 Constraint Handlers (page 316) -- Handle the constraints defined on the domain

Plain Constraints (page 318) -- Removes constrained degrees of freedom from the system of
equations

Lagrange Multipliers (page 319) -- Uses the method of Lagrange multipliers to enforce
constraints

Penalty Method (page 318) -- Uses penalty numbers to enforce constraints

Transformation Method (page 320) -- Performs a condensation of constrained degrees of
freedom

 analysis Command (page 339) -- defines what type of analysis is to be
performed

Chapter 2

29

Static Analysis (page 339) -- solves the KU=R problem, without the mass or damping matrices.

Transient Analysis (page 340) -- solves the time-dependent analysis. The time step in this type
of analysis is constant. The time step in the output is also constant.

Variable Transient Analysis (page 341) -- performs the same analysis type as the Transient
Analysis object. The time step, however, is variable. This method is used when there are
convergence problems with the Transient Analysis object at a peak or when the time step is
too small. The time step in the output is also variable.

ModelBuilder Object
The model builder constructs As in any finite element analysis, the analyst's first step is to
subdivide the body being studied into elements and nodes, to define loads acting on the elements
and nodes, and to define constraints acting on the nodes.
The ModelBuilder is the object in the program responsible for building the following objects in the
model and adding them to the domain:

Node (page 36)

Mass (page 37)
Material (page 162, page 43)

Section (page 191)

Element (page 215)

LoadPattern (page 294)

TimeSeries (page 288)

Transformation (page 280)

Block (page 273)

Constraint (page 316)

Chapter 2

30

Domain Object
The Domain object is responsible for storing the objects created by the ModelBuilder (page 29)
object and for providing the Analysis (page 313) and Recorder (page 31) objects access to these
objects.

Figure 1: Domain Object

Chapter 2

31

Recorder Object
The recorder object monitors user-defined parameters in the model during the analysis. This, for
example, could be the displacement history at a node in a transient analysis, or the entire state of
the model at each step of the solution procedure. Several Recorder (page 303) objects are
created by the analyst to monitor the analysis.

 What does a recorder do?

Monitors the state of a domain component (node, element, etc.) during an analysis

Writes this state to a file or to a database at selected intervals during the analysis

There are also recorders for plotting and monitoring residuals

Once in a file, the information can be easily post-processed.

Analysis Object
The Analysis objects are responsible for performing the analysis. The analysis moves the model
along from state at time t to state at time t + dt. This may vary from a simple static (page 339) linear
analysis to a transient (page 340, page 341) non-linear analysis. In OpenSees each Analysis
object is composed of several component objects, which define the type of analysis how the
analysis is performed.

Chapter 2

Figure 2: Analysis Object

32

33

CHAPTER 3

Model-Building Objects
These objects are used to create the physical model.

In This Chapter
model Command ...................................................... 34
node Command........................................................ 36
mass Command ....................................................... 37
constraints objects.................................................... 38
uniaxialMaterial Command ....................................... 43
nDMaterial Command .............................................. 162
section Command .................................................... 191
element Command ................................................... 215
block Command ....................................................... 273
region Command...................................................... 278
Geometric Transformation Command....................... 280
Time Series .............................................................. 288
pattern Command..................................................... 294

34

CHAPTER 4

model Command
This command is used to construct a ModelBuilder object.
Currently there is only one type of ModelBuilder accepted.

For an example of this command, refer to the Model Building Example (page 363)

In This Chapter
Basic Model Builder.................................................. 34
build Command ........................................................ 35

Basic Model Builder
This command is used to construct the BasicBuilder object.

model BasicBuilder -ndm $ndm <-ndf $ndf>
$ndm

dimension of problem (1,2 or 3)

$ndf

number of degrees of freedom at node (optional)
(default value depends on value of ndm:
ndm=1 -> ndf=1
ndm=2 -> ndf=3
ndm=3 -> ndf=6)

These additional commands allow for the construction of Nodes (page 36), Masses (page 37),
Materials (page 162, page 43), Sections (page 191), Elements (page 215), LoadPatterns (page
294), TimeSeries (page 288), Transformations (page 280), Blocks (page 273) and Constraints
(page 316). These additional commands are described in the subsequent chapters.
EXAMPLE:

Chapter 4

model Command

model basic -ndm 3 -ndf 6; # 3 spacial dimensions, 6 DOF's per node
For an example of this command, refer to the Model Building Example (page 363)

build Command
This command is used to invoke build() (????) on the ModelBuilder (page 29) object.

build
This command has no effect a BasicBuilder (page 34) object, but will on other types of
ModelBuilder (page 29) objects.

35

36

CHAPTER 5

node Command
This command is used to construct a Node object. It assigns coordinates and masses to the Node
object.

node $nodeTag (ndm $coords) <-mass (ndf $MassValues)>
$nodeTag

integer tag identifying node

$coords

nodal coordinates (ndm (page 34) arguments)

$MassValues

nodal mass corresponding to each DOF (ndf (page 34)
arguments) (optional)

The optional -mass string allows analyst the option of associating nodal mass with the node
EXAMPLE:
node 1

0.0

0.0

0.0; # x,y,z coordinates (0,0,0) of node 1

node 2

0.0

120.

0.0; # x,y,z coordinates (0,120,0) of node 2

For an example of this command, refer to the Model Building Example (page 363)

37

CHAPTER 6

mass Command
This command is used to set the mass at a node.

mass $nodeTag (ndf $MassValues)
$nodeTag

integer tag identifying the node associated with the mass

$MassValues

mass values corresponding to each nodal degrees of freedom
(ndf (page 34) values)

EXAMPLE:
mass 2 2.5 0.0 2.5 0.0 0.0 0.0;

# define mass in x and z coordinates

For an example of this command, refer to the Model Building Example (page 363)

38

CHAPTER 7

constraints objects
From Cook: " A constraint either prescribes the value of a DOF (as in imposing a support
condition) or prescribes a relationship among DOF. In common terminology, a single-point
constraint sets a single DOF to a known value (often zero) and a multi-point constraint imposes a
relationship between two or more DOF.... For example, support conditions on a three-bar truss
invoke single-point constraints, while rigid links and rigid elements each invoke a multi-point
constraint."

In This Chapter
Single-Point Constraints ........................................... 38
Multi-Point Constraints ............................................. 41

Single-Point Constraints
The following commands construct homogeneous single-point boundary constraints.

fix Command
This command is used to construct homogeneous single-point boundary constraints.

fix $nodeTag (ndf $ConstrValues)
$nodeTag

integer tag identifying the node to be constrained

$ConstrValues

constraint type (0 or 1). ndf (page 29) values are specified,
corresponding to the ndf degrees-of-freedom.
The two constraint types are:
0

unconstrained

1

constrained

EXAMPLE:
fix 1 1 1 1 1 1 1;

# node 1: fully fixed

Chapter 7

fix 2 0 1 0 0 1 0 -mass 2.5 0.0 2.5 0.0 0.0 0.0;
torsion, translational masses in x-z plane only

constraints objects

39

# node 2: restrain axial elongation and

For an example of this command, refer to the Model Building Example (page 363)

fixX Command
This command is used to construct multiple homogeneous single-point boundary constraints for
all nodes whose x-coordinate lies within a specified distance from a specified coordinate.

fixX $xCoordinate (ndf $ConstrValues) <-tol $tol>
For example, this command is used when specifying boundary conditions for a series of nodes
lying in a plane parallel to the y-z plane in global coordinates.
$xCoordinate

x-coordinate of nodes to be constrained

$ConstrValues

constraint type (0 or 1). ndf (page 29) values are specified,
corresponding to the ndf degrees-of-freedom.
The two constraint types are:

$tol

0

unconstrained

1

constrained

user-defined tolerance (optional, default = 1e-10)

EXAMPLE:
fixX 0.0 1 1 1 1 1 1 -tol 0.1; # fully restrain all nodes in y-z plane at origin (x=0.0)

fixY Command
This command is used to construct multiple homogeneous single-point boundary constraints for
all nodes whose y-coordinate lies within a specified distance from a specified coordinate.

fixY $yCoordinate (ndf $ConstrValues) <-tol $tol>
For example, this command is used when specifying boundary conditions for a series of nodes
lying in a plane parallel to the x-z plane in global coordinates.

Chapter 7

constraints objects

$yCoordinate

y-coordinate of nodes to be constrained

$ConstrValues

constraint type (0 or 1). ndf values are specified, corresponding to
the ndf (page 34) degrees-of-freedom.

40

The two constraint types are:

$tol

0

unconstrained

1

constrained

user-defined tolerance (optional, default = 1e-10)

EXAMPLE:
fixY 0.0 1 1 1 1 1 1 -tol 0.1; # fully restrain all nodes in x-z plane at origin (y=0.0)

fixZ Command
This command is used to construct multiple homogeneous single-point boundary constraints for
all nodes whose z-coordinate lies within a specified distance from a specified coordinate.

fixZ $zCoordinate (ndf $ConstrValues) <-tol $tol>
For example, this command is used when specifying boundary conditions for a series of nodes
lying in a plane parallel to the x-y plane in global coordinates.
$zCoordinate

z-coordinate of nodes to be constrained

$ConstrValues

constraint type (0 or 1). ndf values are specified, corresponding to
the ndf (page 34) degrees-of-freedom.
The two constraint types are:

$tol

0

unconstrained

1

constrained

user-defined tolerance (optional, default = 1e-10)

EXAMPLE:
fixZ 0.0 1 1 1 1 1 1 -tol 0.1; # fully restrain all nodes in x-y plane at origin (z=0.0)

Chapter 7

constraints objects

41

Multi-Point Constraints
The following commands construct multi-point boundary constraints.

equalDOF Command
This command is used to construct a multi-point constraint between nodes.

equalDOF $rNodeTag $cNodeTag $dof1 $dof2 ...
$rNodeTag

integer tag identifying the retained, or master node (rNode)

$cNodeTag

integer tag identifying the constrained, or slave node (cNode)

$dof1 $dof2 ...

nodal degrees-of-freedom that are constrained at the cNode to
be the same as those at the rNode
Valid range is from 1 through ndf (page 34), the number of nodal
degrees-of-freedom.

EXAMPLE:
equalDOF 2 3 1 3 5;

# impose the traslational displacements in x and z directions, and
rotation about the y-axis of node 3 to be the same as those of
node 2.

rigidDiaphragm Command
This command is used to construct a number of Multi-Point Constraint (MP_Constraint) objects.
These objects will constraint certain degrees-of-freedom at the listed slave nodes to move as if in
a rigid plane with the master node.

rigidDiaphragm $perpDirn $masterNodeTag $slaveNodeTag1 $slaveNodeTag2
...

Chapter 7

$perpDirn

constraints objects

42

direction perpendicular to the rigid plane (i.e. direction 3
corresponds to the 1-2 plane)
The rigid plane can be the 1-2, 1-3 or 2-3 plane

$masterNodeTag

integer tag identifying the master node

$slaveNodeTag1
$slaveNodeTag2 ...

nodes that are to be constrained to the master node

NOTE: The constraint object is constructed assuming small rotations.
NOTE: The rigidDiaphragm command works only for problems in three dimensions with
six-degrees-of-freedom at the nodes (ndf (page 34) = 6).
EXAMPLE:
rigidDiaphragm 2 2 4 5 6;

constrain nodes 4,5,6 to move as if in the same x-z plane as node 2.

rigidLink Command
This command is used to construct a single MP_Constraint object.

rigidLink $type $masterNodeTag $slaveNodeTag
$type

string-based argument for rigid-link type:
rod

only the translational degree-of-freedom will be
constrained to be exactly the same as those at
the master node

beam

both the translational and rotational degrees of
freedom are constrained.

$masterNodeTag

integer tag identifying the master node

$slaveNodeTag

integer tag identifying the slave node to be constrained to master
node

NOTE: The constraint object constructed for the beam option assumes small rotations
EXAMPLE:
rigidLink beam 2 3; # connect node 3 to node 2 via a rigid link-beam.

43

CHAPTER 8

uniaxialMaterial Command
This command is used to construct a UniaxialMaterial object which represents uniaxial
stress-strain (or force-deformation) relationships.
The valid queries to any uniaxial material when creating an ElementRecorder (page 307) are
'strain,' 'stress,' and 'tangent.'

In This Chapter
-- Contributed Uniaxial Materials .............................. 44
Elastic Material ......................................................... 125
Elastic-Perfectly Plastic Material............................... 126
Elastic-Perfectly Plastic Gap Material ....................... 128
Elastic-No Tension Material...................................... 129
Parallel Material........................................................ 130
Series Material ......................................................... 131
Hardening Material ................................................... 133
Concrete01 Material -- Zero Tensile Strength........... 134
Concrete02 Material -- Linear Tension Softening...... 137
Concrete03 Material -- Nonlinear Tension Softening143
Steel01 Material ....................................................... 147
Steel02 Material -- Giuffré-Menegotto-Pinto Model with Isotropic
Strain Hardening ...................................................... 153
Hysteretic Material.................................................... 158
Viscous Material ....................................................... 161

44

CHAPTER 9

-- Contributed Uniaxial Materials
These additional materials are contributions to OpenSees and should be available in the latest
executable.
If you have questions about these objects, please do contact the individual authors directly.

In This Chapter
BARSLIP Material .................................................... 44
Bond_SP01 - - Strain Penetration Model for Fully Anchored Steel
Reinforcing Bars....................................................... 46
Concrete04 Material -- Popovics Concrete Material.. 57
Fatigue Material........................................................ 61
Limit State Material................................................... 73
PINCHING4 Material ................................................ 84
PyTzQz Uniaxial Materials ....................................... 104
Reinforcing Steel Material ........................................ 112

BARSLIP Material
Contact Author:

This command is used to construct a uniaxial material that simulates the bar force versus slip
response of a reinforcing bar anchored in a beam-column joint. The model exhibits degradation
under cyclic loading. Cyclic degradation of strength and stiffness occurs in three ways: unloading
stiffness degradation, reloading stiffness degradation, strength degradation.

uniaxialMaterial BarSlip $matTag $fc $fy $Es $fu $Eh $db $ld $nb $depth
$height <$ancLratio> $bsFlag $type <$damage $unit>

$matTag

unique material object integer tag

$fc

positive floating point value defining the compressive strength of
the concrete in which the reinforcing bar is anchored

Chapter 9

-- Contributed Uniaxial Materials

$fy

positive floating point value defining the yield strength of the
reinforcing steel

$Es

floating point value defining the modulus of elasticity of the
reinforcing steel

$fu

positive floating point value defining the ultimate strength of the
reinforcing steel

$Eh

floating point value defining the hardening modulus of the
reinforcing steel

$ld

floating point value defining the development length of the
reinforcing steel

$db

point value defining the diameter of reinforcing steel

$nb

an integer defining the number of anchored bars

$depth

floating point value defining the dimension of the member (beam
or column) perpendicular to the dimension of the plane of the
paper

$height

floating point value defining the height of the flexural member,
perpendicular to direction in which the reinforcing steel is placed,
but in the plane of the paper

$ancLratio

floating point value defining the ratio of anchorage length used for
the reinforcing bar to the dimension of the joint in the direction of
the reinforcing bar (optional, default: 1.0)

$bsFlag

string indicating relative bond strength for the anchored
reinforcing bar (options: "Strong" or "Weak")

$type

string indicating where the reinforcing bar is placed. (options:
"beamtop", “beambot” or "column")

$damage

string indicating whether there is full damage in the material or no
damage (optional, options: “Damage”, “NoDamage” ; default:
Damage)

$unit

string indicating the type of unit system used (optional, options:
“psi”, “MPa”, “Pa”, “psf”, “ksi”, “ksf”) (default: “psi” / “MPa”)*

NOTE:
Model Characteristics:

45

Chapter 9

-- Contributed Uniaxial Materials

46

The uniaxial material model uses the Pinching4 material (page 84) model (Ref. Pinching4 material
model). The response envelope for the bar-slip springs does not represent strength deterioration,
but once the slip demand exceeds 3mm (0.12 in), strength deterioration due to cyclic loading
initiates. As a result the bond-slip springs always exhibit positive stiffness, but strength
deterioration upon reloading to a previously observed slip demand. Reloading and Unloading
Stiffness deterioration are also simulated.

The damage index for unloading and reloading stiffness degradation is evaluated the same say as
the Pinching4 material (ref. Pinching4 material doc.) but the index for strength degradation
specified as

(

(~ )

δf i is

)

δf i = gF1 ⋅ d max + gF 3 ≤ gFLim

With degradation model parameters gF*. It should be noted in here that the deterioration
parameters for unloading, reloading stiffness and strength degradation cannot be modified by the
user and are defined to represent observed behavior.

*NOTE: The model includes predefined bond strengths, so there is the necessity to include in
Units in this material model. For default one can specify units in psi (i.e. pounds/inch2) or in MPa
(i.e. N/mm2). The code detects units in psi if the compressive strength of concrete is greater than
1000 otherwise it takes it as MPa system. The optional variable $unit will help the user to specify
other different types of unit systems according to one’s choice, but currently it is limited to the unit
systems as specified above. The user should also take care to specify the units of length in the
corresponding matching units. (note: Pa = N/m2; ksf = kilo-pound/ft2)

Bond_SP01 - - Strain Penetration Model for Fully Anchored Steel
Reinforcing Bars
URL:

http://www.uwm.edu/~jzhao/Bond_SP01_pages/Bond_index.html
http://www.uwm.edu/~jzhao/Bond_SP01_pages/Bond_index.html

Contact Authors:

Jian Zhao, University of Wisconsin, Milwakee [jzhao@uwm.edu]
Sri Sritharan, Iowa State University [sri@iastate.edu]

Chapter 9

-- Contributed Uniaxial Materials

47

This command is used to construct a uniaxial material object for capturing strain penetration
effects at the column-to-footing, column-to-bridge bent caps, and wall-to-footing intersections. In
these cases, the bond slip associated with strain penetration typically occurs along a portion of the
anchorage length. This model can also be applied to the beam end regions, where the strain
penetration may include slippage of the bar along the entire anchorage length, but the model
parameters should be chosen appropriately.

uniaxialMaterial Bond_SP01 $matTag $Fy $Sy $Fu $Su $b $R

This model is for fully anchored steel reinforcement bars that experience bond slip along a portion
of the anchorage length due to strain penetration effects, which are usually the case for column
and wall longitudinal bars anchored into footings or bridge joints

$matTag

Unique material object integer tag

$Fy

Yield strength of the reinforcement steel

$Sy

Rebar slip at member interface under yield stress and may be
obtained from
1

 d (in ) $ Fy ( psi )
 alpha
$ Sy (in ) = 0.1 b
(
2 * alpha + 1)
+ 0.013(in )
 4000 f ' ( psi )

c


or
1

db(mm) $Fy(MPa
 alpha
)

(2*alpha+1) +0.34(mm)
$Sy(mm) =2.54
 8437 f '(MPa
)
c


db: rebar diameter
$Fy: yield strength of the reinforcement steel
fc': concrete compressive strength of the adjoining connection
member
alpha: parameter used in the local bond-slip relation and can be
taken as 0.4 in accordance with CEB-FIP Model Code 90
$Fu

Ultimate strength of the reinforcement steel

$Su

Rebar slip at the loaded end at the bar fracture strength

$Su = (30~ 40)*$Sy

Chapter 9

-- Contributed Uniaxial Materials

$b

Initial hardening ratio in the monotonic slip vs. bar stress
response (0.3~0.5)

$R

Pinching factor for the cyclic slip vs. bar response (0.5~1.0)

stress

NOTE:

$Fu
$bK
$Fy

K

$Sy

$Su slip

48

Chapter 9

-- Contributed Uniaxial Materials

49

stress

Figure 1: Monotonic bar stress vs. slip response as modelled in Bond_SP01

K

K

slip
K

Figure 2: Cyclic bar stress vs. slip response as modelled in Bond_SP01

80

$R = 1.0
$R = 0.6

Bar stress (ksi)

40

0

-40

-80
-0.6

-0.4

-0.2

0
Loaded-end slip (in)

0.2

0.4

0.6

Chapter 9

-- Contributed Uniaxial Materials

50

Figure 3: Pinching effect represented by $R in Bond_SP01

Model background:
Capturing the structural response and associated damage require accurate modeling of localized
inelastic deformations occurring at the member end regions as identified by shaded areas in
Figure 4. These member end deformations consist of two components: 1) the flexural deformation
that causes inelastic strains in the longitudinal bars and concrete, and 2) the member end rotation,
as indicated by arrows in Figure 4, due to reinforcement slip. The slip considered here is the result
of strain penetration along a portion of the fully anchored bars into the adjoining concrete
members (e.g., footings and joints) during the elastic and inelastic response of a structure.
Ignoring the strain penetration component may appear to produce satisfactory force-displacement
response of the structural system by compromising strain penetration effects with greater
contribution of the flexural action at a given lateral load. However, this approach will appreciably
overestimate the strains and section curvatures in the critical inelastic regions of the member, and
thereby overestimate the structural damage.

Building frame

Bridge bent

Structural wall

Figure 4: Expected inelastic regions at the column and wall ends

Chapter 9

-- Contributed Uniaxial Materials

51

The zero-length section element available in OpenSees may be used to accurately model the
strain penetration effects (or the fixed end rotations shown in Figure 4). Zero-length section
elements have been generally used for section analyses to calculate the moment corresponding
to a given curvature. To model the fixed-end rotation, the zero-length section element should be
placed at the intersection between the flexural member and an adjoining member representing a
footing or joint as shown in Figure 5. A duplicate node is also required between a fiber-based
beam-column element and the adjoining concrete element as shown in Figure 5. The translational
degree-of-freedom of this new node (i.e., node j in Figure 5) should be constrained to the other
node (i.e., node i in Figure 5) to prevent sliding of the beam-column element under lateral loads
because the shear resistance is not included in the zero-length section element.
N
M

Node k
Sec. n
beamcolumn
element

.
.
.
Sec. 2

zero-length
section
element

Sec. 1
Node j
Node i

0

Figure 5: Adding a zero-length section element to a beam-column element

The zero-length section element in OpenSees is assumed to have a unit length such that the
element deformations (i.e., elongation and rotation) are equal to the section deformations (i.e.,
axial strain and curvature). The material model for the steel fibers in the zero-length section
element represents the bar slip instead of strain for a given bar stress. The uniaxial material model
Bond_SP01 is developed for steel fibers in the zero-length section elements.
Note on Material Model for Concrete Fibers

Chapter 9

-- Contributed Uniaxial Materials

52

Similar to the model proposed for the steel fibers, a material model describing the monotonic
response and hysteretic rules is also required for the concrete fibers. The combination of using the
zero-length section element and enforcing the plane section assumption at the end of a flexural
member impose high deformations to the extreme concrete fibers in the zero-length element.
These deformations would likely correspond to concrete compressive strains significantly greater
than the strain capacity stipulated by typical confined concrete models. Such high compressive
strains at the end of flexural members are possible because of additional confinement effects
expected from the adjoining members and because of complex localized deformation at the
member end. Without further proof, it is suggested that the concrete fibers in the zero-length
section element follow a concrete model in OpenSees (e.g., Concrete02). To accommodate the
large deformations expected to the extreme concrete fibers in the zero-length element, this
concrete model may be assumed to follow a perfectly plastic behavior once the concrete strength
reduces to 80% of the confined compressive strength. A parametric study has indicated that the
simulation results would not be very sensitive to the compressive strain chosen to trigger the
perfectly plastic behavior for the concrete fibers in the zero-length section element.
Reference:
Zhao, J., and S. Sritharan. Modeling of strain penetration effects in fiber-based analysis of
reinforced concrete structures. ACI Structural Journal. (Accepted for publication in 2006).

example ss_ic1.tcl
# bridge T-joint
# ----------------# Units: kips, in.
# Pushover analysis multiple dispBeamColumn with strain penetration
# modeling the circular RC column in a bridge T-joint tested by
# Sri Sritharan
# "Seismic response of column/cap beam tee connections
# with cap beam prestressing" Ph.D. thesis, UCSD
# Create ModelBuilder (with two dimensions and 2 DOF/node)
model basic -ndm 2 -ndf 3
# Create nodes
# tag X
node
1 0.0
node
2 0.0
node
3 0.0
node
4 0.0
node
5 0.0
node
6 0.0
node
7 0.0
node
8 12.0
node
9 19.0
node
10 40.0
node
11 61.5
node
12 84.0
node
13 12.0
# Fix supports at base of column

Y
-48.0
-30.0
-12.0
0.0
12.0
30.0
48.0
0.0
0.0
0.0
0.0
0.0
0.0

Chapter 9

-- Contributed Uniaxial Materials

53

# Tag DX DY
RZ
fix 1 1 1
0
fix 7 1 0
0
#equalDOF $rNodeTag $cNodeTag $dof1 $dof2
equalDOF 8 13 2
# Define materials for nonlinear columns
##column Core CONCRETE
uniaxialMaterial Concrete01
uniaxialMaterial Concrete01
##column Cover CONCRETE
uniaxialMaterial Concrete01
##column stub CONCRETE
uniaxialMaterial Elastic
##beam CONCRETE
ecu
uniaxialMaterial Concrete01
## STEEL rebar
##STEEL02
$cR1
$cR2
uniaxialMaterial Steel02
0.04 1.0 0.04
uniaxialMaterial Steel02
0.00 1.0 0.00
uniaxialMaterial Elastic
#uniaxialMaterial StrPen01
$Cd $db $fc
uniaxialMaterial StrPen01
0.0 1.0 4.35

tag
1
200
tag
2
tag
3

f'c
-6.38
-6.38
f'c
-4.56
E
2280

ec0
-0.004
-0.004
ec0
-0.002

tag

$a1

f'cu
-5.11
-5.11
f'cu
0.0

f'c

4

-5.76

$a2
5

$a3
65.0

tag
$a4
29000

6

62.8

29000

7

29000

$Tag

$sy

$fy

$su

400

0.02

65

0.7

ecu
-0.014
-0.014
ecu
-0.006

ec0

f'cu

-0.002

0.0

-0.006

$Fy

$E

$b

$R0

0.02

18.5

0.925

0.15

0.02

18.5

0.925

0.15

$fu

$Kz

$R

97.5

0.50

0.7

1.0
1.0

$la
25.0

# Define cross-section for nonlinear column
set colDia 24;
# bending in this direction (local and global y)
set cover 1.38;
set bcent 1.81;
# [expr $cover+0.197+0.5]
set As 0.60;
# Area of no. 7 bar
set R [expr $colDia/2.0]
set Rc [expr $colDia/2.0-$cover]
set Rb [expr $colDia/2.0-$bcent]
section Fiber 1 {
# core concrete fibers
patch circ
# concrete cover fibers
patch circ
# reinforcing fibers
layer circ
}
section Fiber 2 {
# core concrete fibers
patch circ
# concrete cover fibers
patch circ
# reinforcing fibers
layer circ
}
section Fiber 5 {

1

70

22

0.0

0.0

0.0

$Rc

0.0

360.0

2

70

2

0.0

0.0

$Rc

$R

0.0

360.0

5

14

$As

0.0

0.0

$Rb

-90.0

244.3

3

70

22

0.0

0.0

0.0

$Rc

0.0

360.0

3

70

2

0.0

0.0

$Rc

$R

0.0

360.0

5

14

$As

0.0

0.0

$Rb

-90.0

244.3

Chapter 9

# core concrete fibers
patch circ
# concrete cover fibers
patch circ
# reinforcing fibers
layer circ

-- Contributed Uniaxial Materials

200

70

22

0.0

0.0

0.0

$Rc

0.0

360.0

2

70

2

0.0

0.0

$Rc

$R

0.0

360.0

400

14

$As

0.0

0.0

$Rb

-90.0

244.3

$aw

-$bw

$aw

secID
1
1
1
1
1
1
1
1
1
1
1

transfTag

}
# Define cross-section for nonlinear cap beam
set bmw 27;
# bending in this direction (local and global y)
set bmh 24;
# bending in this direction (local and global y)
set cover 1.38;
set bcent 1.81;
# [expr $cover+0.197+0.5]
set aw [expr $bmw/2.0]
set ac [expr $bmw/2.0-$cover]
set ab [expr $bmw/2.0-$bcent]
set bw [expr $bmh/2.0]
set bc [expr $bmh/2.0-$cover]
set bb [expr $bmh/2.0-$bcent]
section Fiber 3 {
# concrete fibers
patch quad 4 48 1
# reinforcing fibers
layer straight 6 7 $As
layer straight 6 7 $As
}

54

-$bw

-$aw

$bw

-$aw

-$bb
$bb

$ab
$ab

-$bb
$bb

-$ab
-$ab

$bw

# Define column elements
## Geometry of coloumn elements
geomTransf Linear 1
# Number of integration points along length of element
set np 5
# Create the columns using displacement controlled beam-column elements
#
tag
ndI
ndJ
nsecs
element dispBeamColumn
1
1
2
$np
3
element dispBeamColumn
2
2
3
$np
3
element dispBeamColumn
3
3
4
$np
3
element dispBeamColumn
4
4
5
$np
3
element dispBeamColumn
5
5
6
$np
3
element dispBeamColumn
6
6
7
$np
3
element dispBeamColumn
7
4
8
$np
2
element dispBeamColumn
8
13
9
$np
1
element dispBeamColumn
9
9
10
$np
1
element dispBeamColumn
10
10
11
$np
1
element dispBeamColumn
11
11
12
$np
1
# zeroLengthSection
tag
ndI
ndJ
secID
element zeroLengthSection
12
8
13
5
# Set up and perform analysis
## Create recorders
recorder Node -file topdispac.out -time -node 12 -dof 2 disp
recorder Node -file rot4ac.out -time -node 4 -dof 3 disp
recorder Node -file rot8ac.out -time -node 8 -dof 3 disp
recorder Drift drift84ac.out 4 8 2 1
recorder Drift curvatureac.out 8 9 3 1
recorder Drift curvatureac1.out 13 9 3 1

Chapter 9

-- Contributed Uniaxial Materials

recorder Element -file secstrspac.out -time -ele 8 section 5 fiber -$Rb 0 5 stressStrain
recorder Element -file secstrsnac.out -time -ele 8 section 5 fiber $Rb 0 5 stressStrain
recorder Element -file secstrcac.out -time -ele 8 section 5 fiber $Rc 0 1 stressStrain
recorder plot topdispac.out Node12_Ydisp 10 10 300 300 -columns 2 1
set P -90.0
pattern Plain 1 "Constant" {
load 12 $P 0.0 0.0
}
# Define analysis parameters
integrator LoadControl 0
system SparseGeneral -piv
test NormDispIncr 1.0e-4 2000
numberer Plain
constraints Plain
algorithm KrylovNewton
analysis Static
# Do one analysis for constant axial load
analyze 1
# Define reference force
pattern Plain 2 "Linear" {
load 12 0.0 1.0 0.0
}
set dU1 -0.02
set dU2 0.02
# Perform the analysis
integrator DisplacementControl 12 2 $dU1
analyze 33
integrator DisplacementControl 12 2 $dU2
analyze 65
integrator DisplacementControl 12 2 $dU1
analyze 32
integrator DisplacementControl 12 2 $dU1
analyze 67
integrator DisplacementControl 12 2 $dU2
analyze 134
integrator DisplacementControl 12 2 $dU1
analyze 67
integrator DisplacementControl 12 2 $dU1
analyze 101
integrator DisplacementControl 12 2 $dU2
analyze 202
integrator DisplacementControl 12 2 $dU1
analyze 101
integrator DisplacementControl 12 2 $dU1
analyze 135
integrator DisplacementControl 12 2 $dU2
analyze 270
integrator DisplacementControl 12 2 $dU1
analyze 135
integrator DisplacementControl 12 2 $dU1

55

Chapter 9

-- Contributed Uniaxial Materials

56

analyze 202
integrator DisplacementControl 12 2 $dU2
analyze 404
integrator DisplacementControl 12 2 $dU1
analyze 202

materialmodels.tcl
# load pattern test
# ----------------# Jian Zhao, Iowa State University
# June 20, 2004
# ----------------#----------Create Model (2-D 3dof problem-plane truss)
model basic -ndm 2 -ndf 3
# Create nodes
# tag X Y
node
1 0.0
node
2 1.0
node
3 1.0

0.0
0.0
1.0

# Fix supports at node 1
# Tag DX DY
fix 1 1 1
fix 2 0 1
fix 3 0 0

RZ
1
1
1

# Define faked material
# unconfined
uniaxialMaterial Concrete01
# confined CONCRETE
uniaxialMaterial Concrete01
# unconfined
ratio ft et0
uniaxialMaterial Concrete03
0.1 2.5 0.0025
#
STEEL02
$a1 $a2 $a3
uniaxialMaterial Steel02
0.04 1.0 0.04
#uniaxialMaterial StrPen01
$Cd $db $fc
uniaxialMaterial StrPen01
0.0 1.0 4.35
set mat 5
# Define truss element
#
tag
element truss
element truss
element truss
#----------DONE Create Model

CONCRETE
1
tag
f'c
2
CONCRETE
ft0
3

tag
-4.5
ec0
-6.0
tag
beta
-6.0

f'c
-0.002
-0.004
f'c
etu
-0.004

tag

$Fy

4

68.1

tag

$sy

5

0.022

jnode
1
1
2

A
2
3
3

ec0
0.0
f'cu
-5.0
ec0

-0.006
ecu
-0.014

f'cu

ecu

f'cu

ecu

-5.0

-0.014

0.5

0.45

0.0015

$E

$b

$R0

$cR1

$cR2

29000

0.010

22

0.925

0.15

$fy

$su

$fu

$Kz

$R

60

0.77

90

0.5

0.65

-node

2

-dof

1

$a4
1.0
$la
25.0

inode
1
2
3

#----------Create Analysis
# Create displacement command recorders
recorder Node
-file
disp

Mattag
1
$mat
1
$mat
1
$mat

commanddisp.out -time

Chapter 9

-- Contributed Uniaxial Materials

# Create reaction force recorders (for checking material models)
recorder Element -file
reaction.out
-time
-ele

1

57

axialForce

pattern Plain 1 "Series -dt 0.01 -filePath cycload.txt" {
sp 2 1 1
}
integrator LoadControl .01
system SparseGeneral -piv
test NormUnbalance 1.0e-6 100
numberer Plain
constraints Transformation
algorithm Newton
analysis Static
set numIncr 310
analyze $numIncr
wipe

Concrete04 Material -- Popovics Concrete
Material
Contact Authors:

Laura Lowes: http://www.ce.washington.edu/~lowes/
Michael Berry: mpberry@u.washington.edu

This command is used to construct a uniaxial Popovics concrete material object with degraded
linear unloading/reloading stiffness according to the work of Karsan-Jirsa and tensile strength with
exponential decay.

uniaxialMaterial Concrete04 $matTag $fc $ec $ecu $Ec <$ft $et> <$beta>
$matTag

unique material object integer tag

$fc

floating point values defining concrete compressive strength at
28 days (compression is negative)*

$ec

floating point values defining concrete strain at maximum
strength*

$ecu

floating point values defining concrete strain at crushing strength*

$Ec

floating point values defining initial stiffness**

$fct

floating point value defining the maximum tensile strength of
concrete

$et

floating point value defining ultimate tensile strain of concrete

Chapter 9

$beta

-- Contributed Uniaxial Materials

58

floating point value defining the exponential curve parameter to
define the residual stress (as a factor of $ft) at $etu

*NOTE: Compressive concrete parameters should be input as negative values.
**NOTE: The envelope of the compressive stress-strain response is defined using the model
57000 fc
proposed by Popovics (1973). If the user defines Ec =
(in psi) then the envelope curve
is identical to proposed by Mander et al. (1988).
Model Characteristic:
For loading in compression, the envelope to the stress-strain curve follows the model
proposed by Popovics (1973) until the concrete crushing strength is achieved and also for strains
beyond that corresponding to the crushing strength.

ε 
f ci = f c′  ci 
 εc 

Esec =

f ci

ε ci

n=

n
ε 
n − 1 +  ci 
 εc 

n

Ec
Ec − Esec

where subscript i refer to the stress/strain at any load step. For unloading and reloading in
compression, the Karsan-Jirsa model (1969) is used to determine the slope of the curve. For
tensile loading, an exponential curve is used to define the envelope to the stress-strain curve:
f
Ec
 β f  ε − ft
σ i = ft  t  t Ec

εi − t

 ft 

where β multiplier refers to the stress at ultimate tensile strain, generally the value considered is
0.1.
For unloading and reloading in tensile, the secant stiffness is used to define the path.

Chapter 9

-- Contributed Uniaxial Materials

59

The following figures show example stress-strain histories generated using the model.
-4

Tensile response

stress

0.4

1.5

cyclic tension

x 10

1
0.2
0.5
0

0

0.5

1

1.5

strain

0

0

500

Compressive response

stress

1500

2000

x 10

cyclic compression

3

0.01

2
0.005
1
0

0

2

4
strain

6

8

0

0

200

400

600

800

1000

-3

x 10

-3

Tensile-Compressive response
3

10

2
stress

1000

-4

x 10

cyclic tension-compression

5

1
0

0
-1
-2

0

2

4
strain

6

8
-3

x 10

-5

0

200

400

600

800

1000

1200

Chapter 9

-- Contributed Uniaxial Materials

60

cyclic tension compression response envelope
3

2.5

stress (ksi)

2

1.5

1

0.5

0

-0.5
-1

0

1

2

3
strain

4

5

6

7
-3

x 10

Reference:
Mander, J. B., Priestley, M. J. N., and Park, R. (1988). "Theoretical stress-strain model for
confined concrete." Journal of Structural Engineering ASCE, 114(8), 1804-1825.
Popovics, S. (1973). " A numerical approach to the complete stress strain curve for concrete."
Cement and concrete research, 3(5), 583-599.
Karsan, I. D., and Jirsa, J. O. (1969). "Behavior of concrete under compressive loading." Journal
of Structural Division ASCE, 95(ST12).

61

CHAPTER 10

Concrete04 -- Material Behavior
Each material was subjected to a series of ten uniaxial tension and compression strain histories.
The following is the response of this material to such strain excursions. The data shown are the
normalized stresses versus strain. In the normalization, the steel stress was divided by the yield
stress Fy and the concrete stress was divided by the absolute value of compressive strength fc -to maintain positive tension and negative compression. The first figure shows all 10 load patterns
together, which are subsequently shown individually.

Fatigue Material
Author:

Patxi Uriz

Contact Information:

Exponent - Failure Analysis Associates
149 Commonwealth Drive Menlo Park, CA 94025
patxi@exponent.com

The fatigue material uses a modified rainflow cycle counting algorithm to accumulate damage in a
material using Miner’s Rule. Element stress/strain relationships become zero when fatigue life is
exhausted.

uniaxialMaterial Fatigue $matTag $tag <-E0 $E0> <-m $m>
<-min $min> <-max $max>
This material model accounts for the effects of low cycle fatigue. A modified rainflow cycle counter
has been implemented to track strain amplitudes. This cycle counter is used in concert with a
linear strain accumulation model (i.e. Miner’s Rule), based on Coffin-Manson log-log relationships
describing low cycle fatigue failure. This material “wraps” around another material and does not
influence the stress-strain (or force-deformation) relationship of the parent material.
Once the Fatigue material model reaches a damage level of 1.0, the force (or stress) of the parent
material becomes zero (1.0x10-8 times the call to the material). If failure is triggered in
compression, the material stress is dropped at the next zero-force crossing (i.e. compression force
never “drops” to zero).
The Fatigue material assumes that each point is the last point of the history, and tracks damage
with this assumption. If failure is not triggered, this pseudo-peak is discarded.
The material also has the ability to trigger failure based on a maximum or minimum strain (i.e. not
related to fatigue). The default for these values is set to very large numbers.

Chapter 10

Concrete04 -- Material Behavior

62

The default values are calibrated parameters from low cycle fatigue tests of European steel
sections Ballio and Castiglioni (1995), for more information about how material was calibrated, the
user is directed to Uriz (2005).
$matTag

unique material object integer tag

$tag

Unique material object integer tag for the material that is being
“wrapped”

$E0

Value of strain at which one cycle will cause failure (default
0.191)

$m

Slope of Coffin-Manson curve in log-log space (default -0.458)

$min

Global minimum value for strain or deformation (default -1e16)

$max

Global maximum value for strain or deformation (default 1e16)

Example Command:
Example command: uniaxialMaterial Fatigue 2 1 -E0 0.191 -m -0.458
where 2 is the Fatigue material tag, and 1 is the material that is being wrapped, the -E0 and -m
values I have listed here are the default values.

Valid recorder objects for the material are ‘stress’,’tangent’, ‘strain’, ‘stressStrain’, and ‘damage’.
The stress, strain, and tangent recorder options must be available in the material that you are
wrapping.

Chapter 10

FatigueMaterialExample.tcl

FatigueMaterialExample.tcl

63

Chapter 10

FatigueMaterialExample.tcl

# Run an example script to test the fatigue material model
## Define model and loads
model

BasicBuilder -ndm 2

-ndf 2

node 1 0.0 0.0
node 2 0.0 0.0
fix 1 1 1
fix 2 0 1
uniaxialMaterial Steel01 1 60.0 29800.0 0.003
uniaxialMaterial Fatigue 2 1
element zeroLength 1 1 2 -mat 2 -dir 1
pattern Plain 1 "Linear" {
#

nd

load 2

FX
1.0 0.0 0.0

}
## Recorders
recorder Element -file "Damage.out" -time -ele 1 material 1 damage
recorder Element -file "StressStrain.out" \
-time -ele 1 material 1 stressANDstrain
## Set analysis parameters
test EnergyIncr 1.0e-8 200

0

algorithm Newton
system UmfPack
numberer RCM
constraints Plain
analysis Static
## Source the displacement history, and initialize analysis parameters
#source RandomStrainHstory1.tcl
source RandomStrainHstory2.tcl
set LoopLength [array size disp]
set h 1
set controlNode 2
set currentDisp [nodeDisp $controlNode 1 ]
puts [format " \n STARTING DISPLACEMENT = %5.3f \n" $currentDisp]

64

Chapter 10

Figure 1. DamageExample1.jpg

FatigueMaterialExample.tcl

65

Chapter 10

Figure 2. DamageExample2.jpg

FatigueMaterialExample.tcl

66

Chapter 10

RandomStrainHistory1.tcl

FatigueMaterialExample.tcl

67

Chapter 10

set disp(1) -0.0110
set disp(2) -0.0106
set disp(3) -0.0129
set disp(4) -0.0089
set disp(5) -0.0113
set disp(6) -0.0069
set disp(7) -0.0079
set disp(8) 0.0020
set disp(9) -0.0118
set disp(10) -0.0057
set disp(11) -0.0180
set disp(12) -0.0097
set disp(13) -0.0195
set disp(14) -0.0152
set disp(15) -0.0321
set disp(16) -0.0281
set disp(17) -0.0323
set disp(18) -0.0145
set disp(19) -0.0179
set disp(20) -0.0098
set disp(21) -0.0297
set disp(22) -0.0219
set disp(23) -0.0304
set disp(24) -0.0172
set disp(25) -0.0199
set disp(26) -0.0175
set disp(27) -0.0261
set disp(28) -0.0201
set disp(29) -0.0243
set disp(30) -0.0089
set disp(31) -0.0092
set disp(32) 0.0047
set disp(33) -0.0104
set disp(34) 0.0087
set disp(35) 0.0048
set disp(36) 0.0059
set disp(37) 0.0022

FatigueMaterialExample.tcl

68

Chapter 10

FatigueMaterialExample.tcl

69

Chapter 10

RandomStrainHistory2.tcl

FatigueMaterialExample.tcl

70

Chapter 10

set disp(1) -0.0058
set disp(2) 0.0028
set disp(3) -0.0043
set disp(4) -0.0040
set disp(5) -0.0088
set disp(6) -0.0048
set disp(7) -0.0057
set disp(8) 0.0120
set disp(9) 0.0077
set disp(10) 0.0138
set disp(11) 0.0056
set disp(12) 0.0125
set disp(13) 0.0019
set disp(14) 0.0036
set disp(15) -0.0053
set disp(16) 0.0028
set disp(17) -0.0011
set disp(18) 0.0084
set disp(19) 0.0024
set disp(20) 0.0154
set disp(21) 0.0078
set disp(22) 0.0123
set disp(23) -0.0006
set disp(24) 0.0022
set disp(25) -0.0022
set disp(26) 0.0027
set disp(27) 0.0012
set disp(28) 0.0033
set disp(29) -0.0059
set disp(30) 0.0058
set disp(31) -0.0081
set disp(32) 0.0005
set disp(33) -0.0092
set disp(34) -0.0024
set disp(35) -0.0066
set disp(36) -0.0042
set disp(37) -0.0094

FatigueMaterialExample.tcl

71

Chapter 10

FatigueMaterialExample.tcl

72

References
Uriz, Patxi (2005) “Towards Earthquake Resistant Design of Concentrically Braced Steel
Structures,” Doctoral Dissertation, Structural Engineering, Mechanics, and Materials, Department
of Civil and Environmental Engineering, University of California, Berkeley, December 2005
Ballio, G., and Castiglioni, C. A. (1995). "A Unified Approach for the Design of Steel Structures
under Low and/or High Cycle Fatigue." Journal of Constructional Steel Research, 34, 75-101.

73

CHAPTER 11

Limit State Material
Contact Author:

Ken Elwood:
http://www.civil.ubc.ca/faculty/KElwood/KElwood.html

This command is used to construct a uniaxial hysteretic material object with pinching of force and
deformation, damage due to ductility and energy, and degraded unloading stiffness based on
ductility. Failure of the material is defined by the associated limit curve.

uniaxialMaterial LimitState $matTag $s1p $e1p $s2p $e2p $s3p $e3p $s1n $e1n
$s2n $e2n $s3n $e3n $pinchX $pinchY
$damage1 $damage2 $beta $curveTag $curveType.
$matTag

unique material object integer tag

$s1p

$e1p

stress and strain (or force & deformation) at first point of the
envelope in the positive direction

$s2p

$e2p

stress and strain (or force & deformation) at second point of
the envelope in the positive direction

$s3p

$e3p

stress and strain (or force & deformation) at third point of
the envelope in the positive direction (optional)

$s1n

$e1n

stress and strain (or force & deformation) at first point of the
envelope in the negative direction*

$s2n

$e2n

stress and strain (or force & deformation) at second point of
the envelope in the negative direction*

$s3n

$e3n

stress and strain (or force & deformation) at third point of
the envelope in the negative direction (optional)*

$pinchX

pinching factor for strain (or deformation) during reloading

$pinchY

pinching factor for stress (or force) during reloading

$damage1

damage due to ductility: D1(µ-1)

$damage2

damage due to energy: D2(Ei/Eult)

$beta

power used to determine the degraded unloading stiffness
based on ductility, µ-β (optional, default=0.0)

$curveTag

an integer tag for the LimitCurve defining the limit surface

$curveType

an integer defining the type of LimitCurve (0 = no curve,
1 = axial curve, all other curves can be any other integer)

Chapter 11

Limit State Material

74

*NOTE: negative backbone points should be entered as negative numeric values

In This Chapter
Shear Limit Curve..................................................... 74
Axial Limit Curve ...................................................... 75
Shear Limit Curve..................................................... 76
Example Files for Limit State Material ...................... 78

Shear Limit Curve
This command is used to construct a shear limit curve object that is used to define the point of
shear failure for a LimitStateMaterial object. Point of shear failure based on empirical drift capacity
model from Chapter 2.

limitCurve Shear $curveTag $eleTag $rho $fc $b $h $d $Fsw $Kdeg $Fres
$defType $forType <$ndI $ndJ $dof $perpDirn $delta>.
$curveTag

unique limit curve object integer tag

$eleTag

integer element tag for the associated beam-column
element

$rho

transverse reinforcement ratio (Ast/bh)

$fc

concrete compressive strength (psi)

$b

column width (in.)

$h

full column depth (in.)

$d

effective column depth (in.)

$Fsw

floating point value describing the amount of transverse
reinforcement (Fsw = Astfytdc/s)

$Kdeg

If positive: unloading stiffness of beam-column element
(Kunload from Figure 4-8)
if negative: slope of third branch of post-failure backbone
(see Figure 4-6)

$Fres

floating point value for the residual force capacity of the
post-failure backbone (see Figure 4-6)

Chapter 11

Limit State Material

$defType

integer flag for type of deformation defining the abscissa of
the limit curve
1 = maximum beam-column chord rotations
2 = drift based on displacment of nodes ndI and ndJ

$forType

integer flag for type of force defining the ordinate of the limit
curve*
0 = force in associated limit state material
1 = shear in beam-column element

$ndI

integer node tag for the first associated node
(normally node I of $eleTag beam-column element)

$ndJ

integer node tag for the second associated node
(normally node J of $eleTag beam-column element)

$dof

nodal degree of freedom to monitor for drift**

$perpDirn

perpendicular global direction from which length is
determined to compute drift**

$delta

drift (floating point value) used to shift shear limit curve

75

NOTE: * Option 1 assumes no member loads.
** 1 = X, 2 = Y, 3 = Z

Axial Limit Curve
This command is used to construct an axial limit curve object that is used to define the point of
axial failure for a LimitStateMaterial object. Point of axial failure based on model from Chapter 3.
After axial failure response of LimitStateMaterial is forced to follow axial limit curve.

limitCurve Axial $curveTag $eleTag $Fsw $Kdeg $Fres $defType $forType <$ndI
$ndJ $dof $perpDirn $delta>.
$curveTag

unique limit curve object integer tag

$eleTag

integer element tag for the associated beam-column
element

$Fsw

floating point value describing the amount of transverse
reinforcement (Fsw = Astfytdc/s)

$Kdeg

floating point value for the slope of the third branch in the
post-failure backbone, assumed to be negative (see Figure
4-6)

$Fres

floating point value for the residual force capacity of the
post-failure backbone (see Figure 4-6)

Chapter 11

Limit State Material

$defType

integer flag for type of deformation defining the abscissa of
the limit curve
1 = maximum beam-column chord rotations
2 = drift based on displacment of nodes ndI and ndJ

$forType

integer flag for type of force defining the ordinate of the limit
curve*
0 = force in associated limit state material
1 = shear in beam-column element
2 = axial load in beam-column element

$ndI

integer node tag for the first associated node
(normally node I of $eleTag beam-column element)

$ndJ

integer node tag for the second associated node
(normally node J of $eleTag beam-column element)

$dof

nodal degree of freedom to monitor for drift**

$perpDirn

perpendicular global direction from which length is
determined to compute drift**

$delta

drift (floating point value) used to shift axial limit curve

76

NOTE: * Options 1 and 2 assume no member loads.
** 1 = X, 2 = Y, 3 = Z

Shear Limit Curve
This command is used to construct a shear limit curve object that is used to define the point of
shear failure for a LimitStateMaterial object. Point of shear failure based on empirical drift capacity
model from Chapter 2.

limitCurve Shear $curveTag $eleTag $rho $fc $b $h $d $Fsw $Kdeg $Fres
$defType $forType <$ndI $ndJ $dof $perpDirn $delta>.
$curveTag

unique limit curve object integer tag

$eleTag

integer element tag for the associated beam-column
element

$rho

transverse reinforcement ratio (Ast/bh)

$fc

concrete compressive strength (psi)

$b

column width (in.)

$h

full column depth (in.)

$d

effective column depth (in.)

Chapter 11

Limit State Material

$Fsw

floating point value describing the amount of transverse
reinforcement (Fsw = Astfytdc/s)

$Kdeg

If positive: unloading stiffness of beam-column element
(Kunload from Figure 4-8)
if negative: slope of third branch of post-failure backbone
(see Figure 4-6)

$Fres

floating point value for the residual force capacity of the
post-failure backbone (see Figure 4-6)

$defType

integer flag for type of deformation defining the abscissa of
the limit curve
1 = maximum beam-column chord rotations
2 = drift based on displacment of nodes ndI and ndJ

$forType

integer flag for type of force defining the ordinate of the limit
curve*
0 = force in associated limit state material
1 = shear in beam-column element

$ndI

integer node tag for the first associated node
(normally node I of $eleTag beam-column element)

$ndJ

integer node tag for the second associated node
(normally node J of $eleTag beam-column element)

$dof

nodal degree of freedom to monitor for drift**

$perpDirn

perpendicular global direction from which length is
determined to compute drift**

$delta

drift (floating point value) used to shift shear limit curve

NOTE: * Option 1 assumes no member loads.
** 1 = X, 2 = Y, 3 = Z

77

Chapter 11

Limit State Material

Example Files for Limit State Material
CenterCol_basicModel.tcl

78

Chapter 11

Limit State Material

# Example analysis file for LimitStateMaterial
#
# Units: kip, in
# KJE, Feb 2003
source tags.tcl
# Number of analysis steps and step size
#set nSteps 35000
set nSteps 6000
set dlamda 0.1
# Loading option
set loading push
#set loading cyclic
# Analysis control option
set control load
#set control displ
###########################
# Build model
###########################
model BasicBuilder -ndm 2 -ndf 3
################################
# Define nodal mesh and B.C.s
################################
set L 58.0
# tag X Y
node 1 0.0 0.0
node 2 0.0 0.0
node 3 0.0 $L
node 4 0.0 $L
node 5 0.0 $L
# tag DX DY RZ
fix 1 1 1 1
fix 4 0 0 1
fix 5 1 1 1
##############################
# Create column section
##############################
source CenterColSecFiber.tcl
#################################
# Define the beam-column element
#################################
geomTransf PDelta 1
set nint 5
element nonlinearBeamColumn $bcTag 2 3 $nint $flexSec 1 -iter 5 1e-15
####################################
# Define the zero-length end springs
####################################
#rigid material
uniaxialMaterial Elastic $rigidMatTag 9.9e9
#bottom of column slip spring

79

Chapter 11

Limit State Material

80

CenterColShearSpring.tcl
# Defines Shear Spring
# Units: kip, in
# KJE, Feb 2003
# slopes of shear spring backbone
set rigidSlope 1700; #Values when using zero-length spring (G*Av/L)
set negSlope -8;
# residual shear capacity
set Vr 3.0;
# strengths for initial response
set Vi1 25.0;
set Vi2 30.0;
set Vi3 45.0;
# stiffness of unloading slope for flexural component
set kf 24.7 ;# measured off hysteresis plot from analysis
# define limit surface using shear drift model
#
tag
eleTag
# rho f'c b h d Fsw
# Kdeg Fres defType forType nodeI nodeJ dof perpDirn
limitCurve Shear $shearCurveTag $bcTag\
0.0018 3517.0 9.0 9.0 7.75 11.87\
$kf $Vr 2
0
1 4 1 2 0.0
# define HystereticMaterial
uniaxialMaterial LimitState $shearTag\
$Vi1 [expr $Vi1/$rigidSlope] $Vi2 [expr $Vi2/$rigidSlope] $Vi3 [expr $Vi3/$rigidSlope]\
[expr -$Vi1] [expr -$Vi1/$rigidSlope] [expr -$Vi2] [expr -$Vi2/$rigidSlope] [expr -$Vi3] [expr -$Vi3/$rigidSlope]\
$pinchX $pinchY $damage1 $damage2 $beta $shearCurveTag 2 0

CenterColSecFiber.tcl
# Defines Center Column Section
# Units: kip, in
# KJE, Feb 2003
set h 9.0
set b $h
set beta1 100.0
set beta2 100.0
set spall nospalling
set alphaS 0.015
# Set parameters for fiber section
set nfCore 28
set nfCover 4
set c 1.0
set z [expr $h/2.0-$c]
set y [expr $b/2.0-$c]
set nz [expr -$z]

Chapter 11

Limit State Material

81

set ny [expr -$y]
set zc [expr $z+$c]
set yc [expr $y+$c]
set nzc [expr -$zc]
set nyc [expr -$yc]
set fc -3.517
set fc [expr -3.517*$beta2/100.0]
set fcu [expr $fc*$beta1/100.0]
set fy 69.5
set Es 29000.0
set esy [expr $fy/$Es]
set esu 0.15
set fu [expr $fy+$alphaS*$Es*($esu-$esy)]
# Define parameters for elastic section
set Ec 3400
set A [expr $h*$b]
set Ig [expr $h*$h*$h*$b/12]
set Mcr
set Kcr

228.0
1.2e-4

set My
set Ky

554.0 ;# for trilinear model (Mmax from UCFyber)
6.3e-4 ;# based on UCFyber results

set Ry
[expr $Ky*$L/6.0] ; # yield rotation
set EI
[expr $My/$Ky]
set alpha 0.05
set Ku
set Mu
set Ru

0.05
[expr $My+$alpha*$EI*($Ku-$Ky)]
0.5 ;# this assumes alpha is very small so diff between M-curv alpha and M-rot alpha is negligible

set pinchX 0.5
set pinchY 0.4
set damage1 0.0
set damage2 0.0
set beta

0.4; #only to be used with version 1.3

set Ic

[expr $EI/$Ec]

set slipStiff 91000 ;# see CenterColumnMomCurv.xls
set Rslipy [expr $My/$slipStiff]
set alphaSlip [expr $alpha/(1.0+(1.0-$alpha)*($slipStiff*$L/6/$EI))]
set Rslipu [expr $Rslipy+($Mu-$My)/($alphaSlip*$slipStiff)]
# Create axial failure spring
source CenterColAxialSpring.tcl
# Create shear failure spring
source CenterColShearSpring.tcl
section Aggregator $shearAxialOnlySec $shearTag Vy $axialFailTag P
# Create fiber section

Chapter 11

# Define uniaxialMaterials
#
tag
f'c epsc f'cu epscu
uniaxialMaterial Concrete01 $coreTag $fc -0.002 $fcu -0.0052
if {$spall == "spalling"} {
uniaxialMaterial Concrete01 $coverTag $fc

-0.002 0.0

} elseif {$spall == "nospalling"} {
uniaxialMaterial Concrete01 $coverTag $fc

-0.002 $fcu -0.0052

-0.0060

} else {
puts stderr "Invalid spalling option: $spall"
}
#
tag
fy E
hardening ratio
#uniaxialMaterial Steel02 $steelTag 69.5 29000 $alphaS
uniaxialMaterial Hysteretic $steelTag $fy $esy $fu $esu\
-$fy -$esy -$fu -$esu 1.0 1.0 0 0
# Define the fiber section
section Fiber $flexSec {
# Define the concrete patch with fibers for unidirectional bending
patch quadr $coreTag 1 $nfCore $ny $z $ny $nz $y $nz $y $z
# Define the four cover patches
patch quadr $coverTag 1 $nfCover $nyc $zc $nyc $nzc $ny $nz $ny $z
patch quadr $coverTag 1 $nfCover $y $z $y $nz $yc $nzc $yc $zc
patch quadr $coverTag 1 $nfCore $ny $nz $nyc $nzc $yc $nzc $y $nz
patch quadr $coverTag 1 $nfCore $nyc $zc $ny $z $y $z $yc $zc
# Define the reinforcement explicitly using fiber command
# yloc zloc area matTag
fiber -3.250 3.250 0.2 $steelTag 0
fiber -3.250 -3.250 0.2 $steelTag 0
fiber 3.250 -3.250 0.2 $steelTag 0
fiber 3.250 3.250 0.2 $steelTag 0
fiber -3.187 0.0 0.31 $steelTag 0
fiber 3.187 0.0 0.31 $steelTag 0
fiber 0.0 -3.187 0.31 $steelTag 0
fiber 0.0 3.187 0.31 $steelTag 0 }
# moment-rotation end springs for slip (assume elastic)
uniaxialMaterial Elastic $centerSlipTag $slipStiff
set Acenter $A
set Eccenter $Ec
set Iccenter $Ic

CenterColAxialSpring.tcl
# Defines Axial Spring
# Units: kip, in
# KJE, Feb 2003
set Fsw [expr 11.87/1.0]
# Axial elastic stiffness (only one axial spring used)

Limit State Material

82

Chapter 11

Limit State Material

83

set axialElasticSlope [expr 99.0*$Ec*$A/$L]; #99 times more rigid than column
set axialNegSlope -90.0; #slope = axial load/axial displ}
# residual capacity
set Pr 5.0;
# axial loads used for setting initial elastic slope
set P1 65.0;
set P2 75.0;
set P3 85.0;
# define limit surface
#
tag
eleTag Fsw Kdeg
Fres defType forType nodeI nodeJ dof perpDir delta eleRemove
limitCurve Axial $axialCurveTag $bcTag $Fsw $axialNegSlope $Pr 2
2
1 4 1 2
0.0 0
# define LimitStateMaterial
uniaxialMaterial LimitState $axialFailTag\
$P1 [expr $P1/$axialElasticSlope] $P2 [expr $P2/$axialElasticSlope] $P3 [expr $P3/$axialElasticSlope]\
[expr -$P1] [expr -$P1/$axialElasticSlope] [expr -$P2] [expr -$P2/$axialElasticSlope] [expr -$P3] [expr
-$P3/$axialElasticSlope]\
0.5 0.5 0.0 0.0 0.0 $axialCurveTag 1

Tags.tcl
# UniaxialMaterial tags
set coreTag 1
set coverTag 2
set steelTag 3

;# core concrete
;# cover concrete
;# steel

set shearTag 4
;# shear limit state material
set momTag 5
;# mom-curv hysteretic model
set axialTag 6
;# elastic axial force-strain model
set momDegTag 7
;# degrading moment-curv hysteretic model
set axialFailTag 8
;# axial limit state material
set centerSlipTag 9 ;# elastic slip spring
set rigidMatTag 10
set softMatTag 11
# Section tags
set flexSec 1
set shearSec 2
set flexTopSec 3
set flexBotSec 4
set axialSec 5
set shearAxialSec 6
set axialOnlySec 7
set flexShearSec 8
set shearAxialOnlySec 9
# Limit Curve tags
set shearCurveTag 1
set axialCurveTag 2
# Element tags
set bcTag
99

Chapter 11

Limit State Material

84

cyclic.txt
1.2557524028480316e-003
1.2557524028480316e-003
3.0608252487525078e-003
1.5641001656305775e-003
1.1015791633965932e-003
-1.8313432524451514e+000

PINCHING4 Material
Contact Author:

This command is used to construct a uniaxial material that represents a ‘pinched’
load-deformation response and exhibits degradation under cyclic loading. Cyclic degradation of
strength and stiffness occurs in three ways: unloading stiffness degradation, reloading stiffness
degradation, strength degradation.

uniaxialMaterial Pinching4 $matTag $ePf1 $ePd1 $ePf2 $ePd2 $ePf3 $ePd3
$ePf4 $ePd4 <$eNf1 $eNd1 $eNf2 $eNd2 $eNf3 $eNd3 $eNf4 $eNd4>
$rDispP $rForceP $uForceP <$rDispN $rForceN $uForceN > $gK1
$gK2 $gK3 $gK4 $gKLim $gD1 $gD2 $gD3 $gD4 $gDLim $gF1 $gF2
$gF3 $gF4 $gFLim $gE $dmgType

$matTag

unique material object integer tag

$ePf1 $ePf2 $ePf3
$ePf4

floating point values defining force points on the positive
response envelope

$ePd1 $ePd2
$ePd3 $ePd4

floating point values defining deformation points on the positive
response envelope

$eNf1 $eNf2 $eNf3
$eNf4

floating point values defining force points on the negative
response envelope (optional, default: negative of positive
envelope values)

$eNd1 $eNd2
$eNd3 $eNd4

floating point values defining deformations points on the negative
response envelope (optional, default: negative of positive
envelope values)

Chapter 11

Limit State Material

$rDispP

floating point value defining the ratio of the deformation at which
reloading occurs to the maximum historic deformation demand

$rForceP

floating point value defining the ratio of the force at which
reloading begins to force corresponding to the maximum historic
deformation demand

$uForceP

floating point value defining the ratio of strength developed upon
unloading from negative load to the maximum strength
developed under monotonic loading

$rDispN

floating point value defining the ratio of the deformation at which
reloading occurs to the minimum historic deformation demand
(optional, default: $rDispP)

$rForceN

floating point value defining the ratio of the force at which
reloading begins to the force corresponding to the minimum
historic deformation demand (optional, default: $rForceP)

$uForceN

floating point value defining the ratio of the strength developed
upon unloading from a positive load to the minimum strength
developed under monotonic loading (optional, default: $rForceP)

$gK1 $gK2 $gK3
$gK4 $gKLim

floating point values controlling cyclic degradation model for
unloading stiffness degradation

$gD1 $gD2 $gD3
$gD4 $gDLim

floating point values controlling cyclic degradation model for
reloading stiffness degradation

$gF1 $gF2 $gF3
$gF4 $gFLim

floating point values controlling cyclic degradation model for
strength degradation

$gE

floating point value used to define maximum energy dissipation
under cyclic loading. Total energy dissipation capacity is defined
as this factor multiplied by the energy dissipated under
monotonic loading.

$dmgType

string to indicate type of damage (option: “cycle”, “energy”)

85

Chapter 11

Limit State Material

86

NOTE:

Figure 1: Definition of Pinching4 Uniaxial Material Model

Damage Models:
Stiffness and strength are assumed to deteriorate due to the imposed “load” history. The same
basic equations are used to describe deterioration in strength, unloading stiffness and reloading
stiffness:

k i = k 0 ⋅ (1 − δk i )

Chapter 11

Limit State Material

87

where ki is the unloading stiffness at time ti, ko is the initial unloading stiffness (for the case of no
damage), and

δk i (defined below) is the value of the stiffness damage index at time t .
i

d max i = d max 0 ⋅ (1 + δd i )
where d max i is the deformation demand that defines the end of the reload cycle for increasing
d

deformation demand, max 0 is the maximum historic deformation demand (which would be the
deformation demand defining the end of the reload cycle if degradation of reloading stiffness is
ignored), and

δd i (defined below) is the value of reloading stiffness damage index at time t .

(fmax )i = (fmax )0 ⋅ (1 − δf i )

i

Chapter 11

where

Limit State Material

88

(fmax )i is the current envelope maximum strength at time t , (fmax )0 is the initial envelope
i

δf
maximum strength for the case of no damage, and i (defined below) is the value of strength
value index at time ti.

δk δd

δf

i and
i , may be defined to be a function of displacement history
The damage indices, i ,
only ($dmgType = “cycle”) or displacement history and energy accumulation ($dmgType =
“energy”). For either case, all of the damage indices are computed using the same basic equation.

If the damage indices are assumed to be a function of displacement history and energy
accumulation, the unloading stiffness damage index,


(~ )

δk i =  gK1 ⋅ d max


gK 3



Ei

+ gK 2 ⋅ 

E
 monotonic 

where
d min i 
 d max i
~
d max = max 
,

def min 
 def max
Ei =

∫ dE
load history





E monotonic = gE ⋅ 
dE
 monotonic load history 



∫

gK 4 

 ≤ gKLim



δk i is computed as follows:

Chapter 11

Limit State Material

89

with Emonotic equal to the energy required to achieve under monotonic loading the deformation that
defines failure, defmax and defmin the positive and negative deformations that define failure. The

δd

δf

i and
i , are computed using the same equations with degradation
other damage indices,
model parameters gK* replaced by gF* and gD*, as is appropriate.

The above expressions were meant for “Energy” type damage. The user specification of “Energy”
type damage implements damage due to displacement as well as energy. Other type of damage
can be activated: “Cycle” which implements damage due to displacement as well as damage
accrued due to load cycle counting. The expressions for the “Cycle” damage are given below.

If the damage indices are assumed to be a function only of the displacement history, the unloading
stiffness damage index,

(~ )

δk i =  gK1 ⋅ d max


gK 3

δk i is computed as follows:

+ gK 2 ⋅ (Cycle )

gK 4

 ≤ gKLim


where
d min i 
 d max i
~
d max = max 
,

def min 
 def max

with Cycle equal to the number of cycles accrued in the loading history, defmax and defmin the positive

δd

δf

i and
i , are
and negative deformations that define failure. The other damage indices,
computed using the same equations with degradation model parameters gK* replaced by gF* and
gD*, as is appropriate.

 EXAMPLE:
main input file:

RCyclicPinch.tcl (page 96)

supporting files:

procUniaxialPinching.tcl (page 101)

procRCycDAns.tcl (page 102)

Chapter 11

Limit State Material

90

PINCHING4 Uniaxial Material Model
Discussion
PINCHING4 Uniaxial Material Model Discussion

The example files (RCyclicPinch.tcl (page 96), procUniaxialPinching.tcl (page 101),
procRCycDAns.tc (page 102)l) create a one-dimensional structural model consisting of a single
truss element of length 1.0 and area 1.0 (Figure 1). The Pinching4 uniaxial material model is used
to simulate the stress-strain response of the truss material. The truss is subjected to a
pseudo-static cyclic loading. Several files are provided that include different input parameters for
the Pinching4 material model and result in different load-displacement histories for the truss
structure. Refer to the documentation about the Pinching4 uniaxial material model for additional
information.

Input for the Pinching4 Uniaxial Material Model
Refer to the documentation of the Pinching4 uniaxial material model for an explanation of the
following notation.

Response Envelopes:
In these examples the pinching material model is demonstrated with two different
load-deformation response envelopes. Envelope 1 (Figure 2) defines a hardening-type response
while Envelope 2 (Figure 2) defines a softening-type response.

Envelope 1 (Figure 2):

 ePd1 ePf 1   0.0001 2   − eNd1 − eNf 1 
ePd 2 ePf 2 0.0055 6  − eNd 2 − eNf 2

=
=

 ePd 3 ePf 3 0.0188 7   − eNd 3 − eNf 3

 
 

ePd 4 ePf 4 0.0189 7.2 − eNd 4 − eNf 4

Chapter 11

Limit State Material

91

Envelope 2 (Figure 2):

 ePd1 ePf 1   0.0001 2   − eNd1 − eNf 1 
ePd 2 ePf 2 0.0055 6  − eNd 2 − eNf 2

=
=

 ePd 3 ePf 3 0.0188 7   − eNd 3 − eNf 3

 
 

ePd 4 ePf 4 0.0189 0.2 − eNd 4 − eNf 4

Load-Unload Response Parameters:
The form of the load-unload response, and the extent of pinching in the response history, is
defined by the following six parameters. In each of the examples, the following values are used.

[rDispP

rForceP uForceP] = [rDispN

rForceN

uForceN ] = [0.5 0.25 0.05]

Chapter 11

Limit State Material

92

Strength and Stiffness Degradation Parameters:
The Pinching4 uniaxial material model simulates degradation of stiffness and strength under cyclic
loading. The example files demonstrate, individually and in combination, each of the two stiffness
degradation options and the one strength degradation option. The following parameters are used
to define strength and stiffness degradation, as needed, in the example files.

 gK1 gK 2 gK 3 gK 4 gKLim   1.0 0.2 0.3 0.2 0.9
 gD1 gD 2 gD3 gD 4 gDLim  0.5 0.5 2.0 2.0 0.5

=

 gF1 gF 2 gF 3 gF 4 gFLim   1.0 0.0 1.0 1.0 0.9

 

 gE
 10.0


Tcl Scripts:
The following tcl script files are used to run the examples:
RCyclicPinch.tcl (page 96)
procUniaxialPinching.tcl (page 101)
procRCycDAns.tcl (page 102)
Lines should be commented out as necessary within RCyclicPinch.tcl to exercise different
degradation models of the Pinching4 uniaxial material model and different load histories.

If the structure is subjected to a monotonic load history, the load-displacement history is shown in
Figure 2 results with the actual response history depending on the envelope chosen for the
material model. If the structure is subjected to a cyclic load history (Figure 3), one of the
load-displacement histories shown in Figure 4 results, with the exact response depending on the
strength and stiffness degradation model employed. In this case the damage type activated was
“Energy”. The case in which the damage type activated was “Cycle” is shown in Figure 5.

Figures:

Chapter 11

Figure 3: Structural Model
Figure 1: Structural Model

Limit State Material

93

Chapter 11

Figure 4: Response Envelopes
Figure 2: Response Envelopes

Figure 5: Cyclic Displacement History
Figure 3: Cyclic Displacement History

Limit State Material

94

Chapter 11

Limit State Material

95

Chapter 11

Limit State Material

96

Figure 6: Load-Deformation Response Histories ("Energy type damage")
Figure 4: Load-Deformation Response Histories (“Energy type damage”)

Figure 7: Plot showing Both Stiffness and Strength Degradation for Damage Type "Energy" and
"Cycle"
Figure 5. Plot showing Both Stiffness and Strength Degradation for Damage Type
"Energy" and "Cycle"

RCyclicPinch.tcl
#############################################################################################
#####################

# Test example for PINCHING MATERIAL #

# Written: N.Mitra #

# Description: uniaxial material with user defined envelope (softening type used here) and damage parameters #

Chapter 11

Limit State Material

97

# Date: May 04 2002 #

## Model subjected to reverse Cyclic Loading #

## File Name: RCyclicPinch.tcl #

# refer to Pinching-Type Material Model.doc for full explanation of the parameters #

#############################################################################################
#####################

wipe
#create the ModelBuilder object

model BasicBuilder -ndm 2 -ndf 2

# add nodes - command: node nodeId xCrd yCrd

node 1 0.0 0.0

node 2 1.0 0.0

## please keep the follwoing procedures on the same path

source procUniaxialPinching.tcl

source procRCycDAns.tcl

##### Positive/Negative envelope Stress/Load

### stress1 stress2 stress3 stress4

set pEnvelopeStress [list 2.0 6.0 7.0 0.2]

Chapter 11

Limit State Material

set nEnvelopeStress [list -2.0 -6.0 -7.0 -0.2]

##### Positive/Negative envelope Strain/Deformation

### strain1 strain2 strain3 strain4

set pEnvelopeStrain [list 0.0001 0.0055 0.0188 0.0189]

set nEnvelopeStrain [list -0.0001 -0.0055 -0.0188 -0.0189]

##### Ratio of maximum deformation at which reloading begins

### Pos_env. Neg_env.

set rDisp [list 0.5 0.5]

##### Ratio of envelope force (corresponding to maximum deformation) at which reloading begins

### Pos_env. Neg_env.

set rForce [list 0.25 0.25]

##### Ratio of monotonic strength developed upon unloading

### Pos_env. Neg_env.

set uForce [list 0.05 0.05]

##### Coefficients for Unloading Stiffness degradation

### gammaK1 gammaK2 gammaK3 gammaK4 gammaKLimit

set gammaK [list 1.0 0.2 0.3 0.2 0.9]

98

Chapter 11

Limit State Material

#set gammaK [list 0.0 0.0 0.0 0.0 0.0]

##### Coefficients for Reloading Stiffness degradation

### gammaD1 gammaD2 gammaD3 gammaD4 gammaDLimit

set gammaD [list 0.5 0.5 2.0 2.0 0.5]

#set gammaD [list 0.0 0.0 0.0 0.0 0.0]

##### Coefficients for Strength degradation

### gammaF1 gammaF2 gammaF3 gammaF4 gammaFLimit

set gammaF [list 1.0 0.0 1.0 1.0 0.9]

#set gammaF [list 0.0 0.0 0.0 0.0 0.0]

set gammaE 10

# material ID

set matID 1

# damage type (option: "energy", "cycle")

set dam "energy"

# add the material to domain through the use of a procedure

procUniaxialPinching $matID $pEnvelopeStress $nEnvelopeStress $pEnvelopeStrain $nEnvelopeStrain $rDisp

99

Chapter 11

$rForce $uForce $gammaK $gammaD $gammaF $gammaE $dam

# add truss elements - command: element truss trussID node1 node2 A matID

element truss 1 1 2 1.0 1

# set the boundary conditions - command: fix nodeID xResrnt? yRestrnt?

fix 1 1 1

fix 2 0 1

pattern Plain 1 Linear {

load 2 1 0

}

recorder Node -file RCyclicPinchR.out -node 2 -dof 1 disp

# build the components for the analysis object

system ProfileSPD

constraints Plain

test NormDispIncr 1.0e-8 20

algorithm Newton

numberer RCM

Limit State Material

100

Chapter 11

Limit State Material

101

## analysis type used in the procedure is Static

set peakpts [list 0.0001 0.001 0.002 0.003 0.005 0.006 0.007 0.009 0.01 0.011 0.012 0.013 ]

set increments 10

set nodeTag 2

set dofTag 1

## start procedure for feeding in

## Reverse Cyclic loading to the model by Disp. control

procRCycDAns $increments $nodeTag $dofTag $peakpts

# print the results at nodes

print node

procUniaxialPinching.tcl
#############################################################################################
########

##

# procUniaxialPinching.tcl #

# procedure for activating the pinching material given its parameters in the form of list #

# created NM (nmitra@u.washington.edu) dated : Feb 2002 #

#############################################################################################
########

proc procUniaxialPinching { materialTag pEnvelopeStress nEnvelopeStress pEnvelopeStrain nEnvelopeStrain rDisp

Chapter 11

Limit State Material

102

rForce uForce gammaK gammaD gammaF gammaE damage} {

# add material - command: uniaxialMaterial ...... paramaters as shown

#uniaxialMaterial Pinching4 tag

#### stress1P strain1P stress2P strain2P stress3P strain3P stress4P strain4P

#### stress1N strain1N stress2N strain2N stress3N strain3N stress4N strain4N

#### rDispP rForceP uForceP rDispN rForceN uForceN

#### gammaK1 gammaK2 gammaK3 gammaK4 gammaKLimit

#### gammaD1 gammaD2 gammaD3 gammaD4 gammaDLimit

#### gammaF1 gammaF2 gammaF3 gammaF4 gammaFLimit gammaE $damage

uniaxialMaterial Pinching4 $materialTag [lindex $pEnvelopeStress 0] [lindex $pEnvelopeStrain 0] [lindex
$pEnvelopeStress 1] [lindex $pEnvelopeStrain 1] [lindex $pEnvelopeStress 2] [lindex $pEnvelopeStrain 2] [lindex
$pEnvelopeStress 3] [lindex $pEnvelopeStrain 3] [lindex $nEnvelopeStress 0] [lindex $nEnvelopeStrain 0] [lindex
$nEnvelopeStress 1] [lindex $nEnvelopeStrain 1] [lindex $nEnvelopeStress 2] [lindex $nEnvelopeStrain 2] [lindex
$nEnvelopeStress 3] [lindex $nEnvelopeStrain 3] [lindex $rDisp 0] [lindex $rForce 0] [lindex $uForce 0] [lindex $rDisp 1]
[lindex $rForce 1] [lindex $uForce 1] [lindex $gammaK 0] [lindex $gammaK 1] [lindex $gammaK 2] [lindex $gammaK 3]
[lindex $gammaK 4] [lindex $gammaD 0] [lindex $gammaD 1] [lindex $gammaD 2] [lindex $gammaD 3] [lindex
$gammaD 4] [lindex $gammaF 0] [lindex $gammaF 1] [lindex $gammaF 2] [lindex $gammaF 3] [lindex $gammaF 4]
$gammaE $damage

}

procRCycDAns.tcl
#############################################################################################
########
#
#

#
procRCycDAns.tcl

#

Chapter 11

# procedure for reverse cyclic displacement control analysis given the peak pts.
# analysis type used : STATIC
# Written : N.Mitra

Limit State Material

103

#

#
#

#############################################################################################
########
proc procRCycDAns { incre nodeTag dofTag peakpts} {

set x [lindex $peakpts 0]
set fir [expr $x/$incre]

integrator DisplacementControl $nodeTag $dofTag 0.0 1 $fir $fir

# create the analysis object
analysis Static
# perform the analysis
analyze $incre
integrator DisplacementControl $nodeTag $dofTag 0.0 1 [expr -$fir] [expr -$fir]
analyze [expr 2*$incre]
integrator DisplacementControl $nodeTag $dofTag 0.0 1 $fir $fir
analyze $incre

for {set j 1} {$j < [llength $peakpts]} {incr j 1} {
set tx [lindex $peakpts $j]
set tinc [expr $tx/$fir]
set rt [expr int($tinc)]

integrator DisplacementControl $nodeTag $dofTag 0.0 1 $fir $fir
analyze $rt
integrator DisplacementControl $nodeTag $dofTag 0.0 1 [expr -$fir] [expr -$fir]
analyze [expr 2*$rt]
integrator DisplacementControl $nodeTag $dofTag 0.0 1 $fir $fir
analyze $rt
}
################################ end procRCycDAns.tcl #######################################
}

Chapter 11

Limit State Material

104

PyTzQz Uniaxial Materials
This section describes commands that are used to construct uniaxial materials for p-y, t-z and q-z
elements for modeling soil-structure interaction developed at UC Davis.
There is available documentation on UCD COmpGeomech work within OpenSees framework at:

http://sokocalo.engr.ucdavis.edu/~jeremic/OpenSees/UCD_CG_OpenSees_Commands_2up.pd
f
(http://sokocalo.engr.ucdavis.edu/~jeremic/OpenSees/UCD_CG_OpenSees_Commands_2up.p
df)

Also, there is a more in depth writeup (lecture notes) at:

http://sokocalo.engr.ucdavis.edu/~jeremic/CG/CompGeomechanicsLectureNotes.pdf
(http://sokocalo.engr.ucdavis.edu/~jeremic/CG/CompGeomechanicsLectureNotes.pdf)

PySimple1 Material
This command is used to construct a PySimple1 uniaxial material object.

uniaxialMaterial PySimple1 $matTag $soilType $pult $Y50 $Cd <$c>.
$matTag

Unique material object integer tag.

$soilType

soilType = 1 Backbone of p-y curve approximates Matlock (1970)
soft clay relation.
soilType = 2 Backbone of p-y curve approximates API (1993)
sand relation.

$pult

Ultimate capacity of the p-y material. Note that “p” or “pult” are
distributed loads [force per length of pile] in common design
equations, but are both loads for this uniaxialMaterial [i.e.,
distributed load times the tributary length of the pile].

Chapter 11

Limit State Material

$Y50

Displacement at which 50% of pult is mobilized in monotonic
loading.

$Cd

Variable that sets the drag resistance within a fully-mobilized gap
as Cd*pult.

$c

The viscous damping term (dashpot) on the far-field (elastic)
component of the displacement rate (velocity). Default = 0.0.
Nonzero c values are used to represent radiation damping
effects.

105

NOTE: Full documentation of the PyLiq1 command is found in PySimple1_documentation.pdf
(http://opensees.berkeley.edu/OpenSees/manuals/usermanual/documents/PySimple1_documen
tation.PDF)

TzSimple1 Material
This command is used to construct a TzSimple1 uniaxial material object.

uniaxialMaterial TzSimple1 $matTag $tzType $tult $z50 <$c>.
$matTag

Unique material object integer tag.

$tzType

tzType = 1 Backbone of t-z curve approximates Reese and
O’Neill (1987) relation.
tzType = 2 Backbone of t-z curve approximates Mosher (1984)
relation.

$tult

Ultimate capacity of the t-z material. Note that “t” or “tult” are
distributed loads [force per length of pile] in common design
equations, but are both loads for this uniaxialMaterial [i.e.,
distributed load times the tributary length of the pile].

$z50

Displacement at which 50% of tult is mobilized in monotonic
loading.

$c

The viscous damping term (dashpot) on the far-field (elastic)
component of the displacement rate (velocity). Default = 0.0.
Nonzero c values are used to represent radiation damping
effects.

NOTE: Full documentation of the TzLiq1 command is included in: TzSimple1_documentation.PDF
(http://opensees.berkeley.edu/OpenSees/manuals/usermanual/documents/TzSimple1_documen
tation.PDF)

Chapter 11

Limit State Material

106

QzSimple1 Material
This command is used to construct a QzSimple1 uniaxial material object.

uniaxialMaterial PySimple1 $matTag $qzType $qult $Y50 <$suction $c>.
$matTag

Unique material object integer tag.

$soilType

qzType = 1 Backbone of q-z curve approximates Reese and
O’Neill’s (1987) relation for drilled shafts in clay.
qzType = 2 Backbone of q-z curve approximates Vijayvergiya’s
(1977) relation for piles in sand.

$qult

Ultimate capacity of the q-z material. Note that “q” or “qult” are
stresses [force per unit area of pile tip] in common design
equations, but are both loads for this uniaxialMaterial [i.e., stress
times tip area].

$z50

Displacement at which 50% of pult is mobilized in monotonic
loading. Note that Vijayvergiya’s relation (qzType=2) refers to a
“critical” displacement (zcrit) at which qult is fully mobilized, and
that the corresponding z50 would be 0. 125zcrit.

$suction

Uplift resistance is equal to suction*qult. Default = 0.0. The value
of suction must be 0.0 to 0.1.*

$c

The viscous damping term (dashpot) on the far-field (elastic)
component of the displacement rate (velocity). Default = 0.0.
Nonzero c values are used to represent radiation damping
effects.*

NOTE: Full documentation of the QzSimple1 command is found in:
QzSimple1_Documentation.pdf
(http://opensees.berkeley.edu/OpenSees/manuals/usermanual/documents/QzSimple1_documen
tation.PDF)
*NOTE: Optional variables suction and c must either both be omitted or both be included.

Chapter 11

Limit State Material

PyLiq1 Material
This command is used to construct a PyLiq1 uniaxial material object.

uniaxialMaterial PyLiq1 $matTag $soilType $pult $Y50 $Cd $c $pRes
$solidElem1 $solidElem2.
$matTag

Unique material object integer tag.

$soilType

soilType = 1 Backbone of p-y curve approximates Matlock (1970)
soft clay relation.
soilType = 2 Backbone of p-y curve approximates API (1993)
sand relation.

$pult

Ultimate capacity of the p-y material. Note that “p” or “pult” are
distributed loads [force per length of pile] in common design
equations, but are both loads for this uniaxialMaterial [i.e.,
distributed load times the tributary length of the pile].

$Y50

Displacement at which 50% of pult is mobilized in monotonic
loading.

$Cd

Variable that sets the drag resistance within a fully-mobilized gap
as Cd*pult.

$c

The viscous damping term (dashpot) on the far-field (elastic)
component of the displacement rate (velocity). Default = 0.0.
Nonzero c values are used to represent radiation damping
effects.

$pRes

Minimum (or residual) p-y resistance that the material retains as
the adjacent solid soil elements liquefy (i.e. at ru = 1.0).

$solidElem1

Element object integer tag for a solid element from which PyLiq1
will obtain mean effective stresses and pore pressures.

$solidElem2

Element object integer tag for a solid element from which PyLiq1
will obtain mean effective stresses and pore pressures.

107

Chapter 11

Limit State Material

108

NOTE: Full documentation of the PyLiq1 command is found in: PyLiq1_Documentation.pdf
(http://opensees.berkeley.edu/OpenSees/manuals/usermanual/documents/PyLiq1_documentati
on.pdf)
NOTE: The implementation of PyLiq1 requires that the specified soil elements consist of
FluidSolidPorousMaterials in FourNodeQuad elements. To model the effects of liquefaction with
PyLiq1, it is necessary to use the material stage updating command:

updateMaterialStage –material $matNum –stage $sNum
where the argument matNum is the material number (for PyLiq1) and the argument sNum is the
desired stage (valid values are 0 & 1). With sNum=0, the PyLiq1 behavior will be independent of
any pore pressure in the specified solidElem’s. When updateMaterialStage first sets sNum=1,
PyLiq1 will obtain the average mean effective stress in the two solidElem’s and treat it as the initial
consolidation stress prior to undrained loading. Thereafter, the behavior of PyLiq1 will depend on
the mean effective stresses (and hence excess pore pressures) in the solidElem’s. The default
value of sNum is 0 (i.e., sNum=0 if updateMaterialStage is not called). Note that the
updateMaterialStage command is used with some soil material models, and that sNum=0
generally corresponds to the application of gravity loads (e.g., elastic behavior with no excess
pore pressure development) and sNum=1 generally corresponds to undrained loading (e.g.,
plastic behavior with excess pore pressure development). The analysis for gravity loading cannot
use the "algorithm Linear" command because the relevant soil materials do not currently work
properly with this command. Instead, the "algorithm Newton" or some other option must be used.

TzLiq1 Material
This command is used to construct a PyLiq1 uniaxial material object.

uniaxialMaterial TzLiq1 $matTag $soilType $tult $z50 $c $solidElem1
$solidElem2.
$matTag

Unique material object integer tag.

$tzType

tzType = 1 Backbone of t-z curve approximates Reese and
O’Neill (1987) relation.
tzType = 2 Backbone of t-z curve approximates Mosher (1984)
relation.

Chapter 11

Limit State Material

$tult

Ultimate capacity of the t-z material. Note that “t” or “tult” are
distributed loads [force per length of pile] in common design
equations, but are both loads for this uniaxialMaterial [i.e.,
distributed load times the tributary length of the pile].

$z50

Displacement at which 50% of tult is mobilized in monotonic
loading.

$c

The viscous damping term (dashpot) on the far-field (elastic)
component of the displacement rate (velocity). Default = 0.0.
Nonzero c values are used to represent radiation damping
effects.

$solidElem1

Element object integer tag for a solid element from which TzLiq1
will obtain mean effective stresses and pore pressures.

$solidElem2

Element object integer tag for a solid element from which TzLiq1
will obtain mean effective stresses and pore pressures.

109

NOTE: Full documentation of the TzLiq1 command is included in: TzLiq1_Documentation.pdf
(http://opensees.berkeley.edu/OpenSees/manuals/usermanual/documents/TzLiq1_documentatio
n.pdf)
NOTE: The implementation of TzLiq1 requires that the specified soil elements consist of
FluidSolidPorousMaterials in FourNodeQuad elements. To model the effects of liquefaction with
TzLiq1, it is necessary to use the material stage updating command:

updateMaterialStage –material $matNum –stage $sNum
where the argument matNum is the material number (for TzLiq1) and the argument sNum is the
desired stage (valid values are 0 & 1). With sNum=0, the TzLiq1 behavior will be independent of
any pore pressure in the specified solidElem’s. When updateMaterialStage first sets sNum=1,
TzLiq1 will obtain the average mean effective stress in the two solidElem’s and treat it as the initial
consolidation stress prior to undrained loading. Thereafter, the behavior of TzLiq1 will depend on
the mean effective stress (and hence excess pore pressures) in the solidElem’s. The default value
of sNum is 0 (i.e., sNum=0 if updateMaterialStage is not called). Note that the
updateMaterialStage command is used with some soil material models, and that sNum=0
generally corresponds to the application of gravity loads (e.g., elastic behavior with no excess
pore pressure development) and sNum=1 generally corresponds to undrained loading (e.g.,
plastic behavior with excess pore pressures development). The analysis for gravity loading cannot
use the "algorithm Linear" command because the relevant soil materials do not currently work
properly with this command. Instead, the "algorithm Newton" or some other option must be used.

Chapter 11

Limit State Material

110

PySimple1Gen Command
This command is used to construct output files containing material properties for PySimple1
uniaxial materials. The PySimple1Gen command constructs PySimple1 materials (Boulanger,
2003) for pre-defined zeroLength elements.

PySimple1Gen $file1 $file2 $file3 $file4 $file5 <$file6>
$file1

The name of an input file containing soil and pile properties
required to define the PySimple1 materials.

$file2

The name of an input file containing information about nodes that
define the mesh in the domain.

$file3

The name of an input file containing information about the
zeroLength elements to be assigned PySimple1 materials
(hereafter called p-y elements).

$file4

The name of an input file containing information about the beam
column elements that are attached to p-y elements.

$file5

The name of the output file to which the PySimple1 materials are
written.

$file6

The name of the output file to which the applied patterns are
written (optional).

The command has been structured such that $File2, $File3, $File4, $File5 and $File6 can be
sourced directly by OpenSees from within a master tcl file. Hence $File2, $File3 and $File4 serve
two purposes:
1 They provide information to PySimple1Gen to create the PySimple1 materials.
2 They can be sourced directly in a master tcl file to define the nodes, zeroLength elements for
p-y materials, and pile elements, respectively.
Furthermore, $File5 and $File 6 serve the following purpose:
1

They can be sourced by OpenSees from within a master tcl file to define the PySimple1
materials and the applied patterns, respectively.

The intended use of the files is demonstrated in an example problem in the Appendix:
PySimple1GenDocumentation.pdf
(http://opensees.berkeley.edu/OpenSees/manuals/usermanual/documents/PySimple1GenDocu
mentation.pdf)

Chapter 11

Limit State Material

111

TzSimple1Gen Command
The TzSimple1Gen command constructs TzSimple1 materials (Boulanger, 2003) for pre-defined
zeroLength elements.

TzSimple1Gen $file1 $file2 $file3 $file4 $file5 <$file6>
$file1

The name of an input file containing soil and pile properties
required to define the TzSimple1 materials.

$file2

The name of an input file containing information about the nodes
that define the mesh in the domain.

$file3

The name of an input file containing information about the
zeroLength elements that are to be assigned TzSimple1
materials (hereafter called tz elements).

$file4

The name of an input file containing information about the beam
column elements that are attached to tz elements.

$file5

The name of the output file to which the TzSimple1 materials are
written.

$file6

The name of the output file to which the applied patterns are
written (optional).

The command has been structured such that $File2, $File3, $File4, $File5 and $File6 can be
sourced directly from within a master tcl file. Hence $File2, $File3 and $File4 serve two purposes:
1

They provide information to TzSimple1Gen to create the TzSimple1 materials.

2 They can be sourced directly in a master tcl file to define the nodes, zeroLength elements for tz
materials, and pile elements, respectively.
Furthermore, $File5 and $File6 serve the following purpose:
1

They can be sourced directly in a master tcl file to define the TzSimple1 materials and the
applied patterns.

The dual use of the files is demonstrated in an example problem in the Appendix:
TzSimple1GenDocumentation.pdf
(http://opensees.berkeley.edu/OpenSees/manuals/usermanual/documents/TzSimple1GenDocu
mentation.pdf)

Chapter 11

Limit State Material

112

Reinforcing Steel Material
Contact Authors:

Jon Mohle M.S., P.E.
Sashi Kunnath:
http://cee.engr.ucdavis.edu/faculty/kunnath/kunnath.htm

This command is used to construct a ReinforcingSteel uniaxial material object. This object is
intended to be used in a reinforced concrete fiber section as the steel reinforcing material.

uniaxialMaterial ReinforcingSteel $matTag $fy $fu $Es $Esh $esh $eult
< -GABuck $lsr $beta $r $gama > < -DMBuck $lsr < $alpha >>
< -CMFatigue $Cf $alpha $Cd > < -IsoHard <$a1 <$limit> > >

$matTag

unique material object integer tag

$fy

Yield stress in tension (see Figure 1)

$fu

Ultimate stress in tension

$Es

Initial elastic tangent

$Esh

Tangent at initial strain hardening

$esh

Strain corresponding to initial strain hardening

$eult

Strain at peak stress

-GABuck

Buckling Model Based on Gomes and Appleton (1997)

Chapter 11

Limit State Material

113

$lsr

Slenderness Ratio (see Figure 2)

$beta

Amplification factor for the buckled stress strain curve. (see
Figure 3)

$r

Buckling reduction factor
r can be a real number between [0.0 and 1.0]
r=1.0 full reduction (no buckling)
r=0.0 no reduction
0.0<r<1.0 linear interpolation between buckled and unbuckled
curves

$gamma
-DMBuck

Buckling constant (see Figures 3 and 4)

Buckling model based on Dhakal and Maekawa (2002)
$lsr

Slenderness Ratio (see Figure 2)

$alpha

Adjustment Constant usually between 0.75 and 1.0
Default: alpha=1.0, this parameter is optional.

-CMFatigue

Coffin-Manson Fatigue and Strength Reduction
$Cf

Coffin-Manson constant C (see Figure 5)

$alpha

Coffin-Manson constant α (see Figure 5)

$Cd

Cyclic strength reduction constant
(see Figure 6 and Equation 3)

-IsoHard

Isotropic Hardening / Diminishing Yield Plateau
$a1

Hardening constant (default = 4.3)

$limit

Limit for the reduction of the yield plateau. % of original plateau
length to remain (0.01 < limit < 1.0 )
Limit =1.0, then no reduction takes place (default =0.01)

-MPCurveParams

Menegotto and Pinto Curve Parameters
$R1

(default = 0.333)

$R2

(default = 18)

$R3

(default = 4)

R = R2 (1.0 − R3ε t ) ( ε y' )

R1

see Fig 6b

Chapter 11

Limit State Material

114

NOTE: This simulation is based on the Chang and Mander(1994) uniaxial steel model. The
simulation has incorporated additional reversal memory locations to better control stress
overshooting (default is 10 branches but this can be easily modified by changing the variable
“LastRule_RS” within the header file “ReinforcingSteel.h”). The cycle counting method
implemented in the routine achieves the same result as rainflow counting. Fatigue parameters are
based on the Coffin-Manson equation for plastic strain amplitude as indicated in Figure 6a. The
buckling simulations incorporated consist of a variation on Gomes and Appleton(1997) and
Dhakal and Maekawa(2002). The buckling and fatigue portions of this simulation are still being
further enhanced and refined. Additional buckling and fatigue options should be available in the
near future.

Figure 1: Material Constants
BACKBONE CURVE: The backbone curve shown in Figure 1 is used as a bounding surface for
the reinforcing bar simulation. This backbone curve is shifted as described by Chang and Mander
(1994) to account for Isotropic hardening. This backbone can be obtained by utilizing simple
tension test data. Within the material class, the backbone curve is transformed from engineering
stress space to natural stress space (accounting for change in area as the bar is stressed.) This
allows the single backbone to represent both tensile and compressive stress-strain relations. The
tension and compression backbone curves are not the same in engineering stress space for this
model! This transformation assumes small strain relations described by Dodd and
Restrepo-Posada (1995)
The softening region (strain greater than eult), shown in Figure 1, is a localization effect due to
necking and is a function of the gage length used during measurement. This geometric effect is
ignored in this simulation. In this simulation, it is assumed that there is no softening in natural
stress space. Because the simulation always converts back to engineering stress space, you will
observe some softening in the tension response due to the reduction in area, however this will be
much smaller than that shown in the original backbone curve proposed by Chang and Mander.

Chapter 11

Limit State Material

115

DIMINISHING YIELD PLATEAU: It has been observed that when a reinforcing bar is subjected to
plastic strain reversals within the yield plateau, strain hardening will initiate at a lower strain that
that of the same bar loaded monotonically. Additionally, isotropic hardening can result from
repeated strain reversals and is commonly related to accumulated plastic strain. These two
aspects of the stress-strain behavior of steel bars are somewhat related and that by shortening the
yield plateau as a function of accumulated plastic strain, the model will have some capability to
simulate both the diminishing yield plateau and isotropic hardening. The Chang and Mander
model, on which this formulation is based, models only anisotropic hardening by shifting the
backbone curves and by targeting previous reversal points on the backbone curves. By adding a
component of isotropic hardening, the model has additional capabilities and is able to more
accurately simulate test data.

Accumulated plastic strain is tracked within the material model for each branch, plateau
adjustments are made only in the outer branches for simplicity. The plastic strain due to the
backbone curve is ignored so that a monotonically loaded sample can be calibrated to a
monotonic test sample more easily.

Figure 2: Slenderness Defined

Chapter 11

Limit State Material

116

Figure 3: Buckling Parameters

GOMES AND APPLETON BUCKLED CURVE: Figure 3 describes the use of the buckling
parameters modified from Gomes and Appleton(1997). β is an amplification factor that allows the
user to scale the buckling curve. This is useful to adjust the location of the bifurcation point. The
r factor is used to adjust the curve between the buckled curve and the unbuckled curve. The
variable r can only be a real number between 0.0 and 1.0.

Chapter 11

Limit State Material

117

The γ factor is the positive stress location about which the buckling factor is initiated. This factor
was introduced to avoid kinks in the reloading branch. The implementation of the γ factor is shown
in Figure 3. The basic idea is that the stress strain curves are reduced toward the positive stress
γfsu. γ should be between 0.0 and 1.0. A γ of 0.0 will factor to the zero stress axis. This will usually
produce a kink in the reloading curve at the zero stress location. Good results have been obtained
using the following values for the buckling constants.

β
r

γ

1.0
0.4
0.5

β
r
or

γ

2.0
0.0
0.5

Figure 4 displays the buckling behavior due to the variation of the different constants. The
response shown on the upper left is the unbuckled case. In each of the other cases, buckling
behavior is defined by the constants shown.

Chapter 11

Limit State Material

118

Figure 4: Effect of Sample Parameters in the Gomes and Appleton Buckling Model

DHAKAL AND MAEKAWA BUCKLED CURVE: The buckling model described in this section is
based on Dhakal and Maekawa(2002). This model takes two terms, lsr and α. lsr is the
slenderness ratio as described in Figure 2 and α is an amplification factor. Dhakal and Maekawa
suggest a value of α =1.0 for linear strain hardening and α =0.75 for elastic perfectly plastic
material behavior. The material model in this implementation is neither linear strain hardening nor
elastic perfectly plastic. However, since the material model does include strain hardening α=1.0
has been assumed as the default value. Figure 5 shows the unbuckled vs buckled stress strain
response curves.

Chapter 11

Limit State Material

119

Figure 5: Effect of Suggested Parameters in the Dhakal and Maekawa Buckling Model

CYCLIC DEGRADATION: Cf and α are factors used to relate the number of half cycles to fracture
to the half cycle plastic strain amplitude (Figure 6a). Plastic strain half cycle amplitude is defined

ε

by Equation 1. The total half cycle strain amplitude, t , is shown in Figure 6b as the change in
strain from reversal A to reversal B. Cf and α are used to define a cumulative damage factor, D, as
described in Equation 2.

Chapter 11

Figure 6a: Coffin-Manson Constants

ε p = εt −

Limit State Material

120

Figure 6b: Half Cycle Terms Defined

σt
Es

(1)
1

 ∆ε p  α
D = ∑
 C 
 f 

(2)

The cumulative damage factor is zero at no damage and 1.0 at fracture. Once a bar has been
determined to have fractured, the strength is rapidly degraded to zero.

Chapter 11

Limit State Material

121

Figure 7: Strength Reduction

A degrade constant, K1, is used to describe loss in strength due to damage or other phenomenon
resulting in softening due to plastic reversals. The degradation is currently assumed to have a
simple linear relationship with D. This is used to correlate strength degradation to the cumulative
damage factor. This linear relationship is shown in Equation 3.

φSR = K1D

(3)

Alternately this simple linear equation can be rewritten in a way that makes the strength
degradation independent of the number of half cycles to failure. Keeping the failure and
degradation terms independent is convenient for calibration. Equation 3 is rewritten below utilizing
the strength degradation constant Cd.

1

 ∆ε p α
φSR = ∑ 

 Cd 

(4)

The constants K1 and Cd can be related as shown in Equation 5.

Cd =

Cf
K1α

(5)

Suggested starting values have been obtained from data reported by Brown and Kunnath (2000)
for bars with a slenderness of 6. Keep in mind that this experimental data is limited and additional
calibration may be necessary to capture realistic behavior in a reinforcing bar embedded in
concrete and influenced by other factors such as confinement.

Chapter 11

α:

0.506

Cf:

0.26

Cd:

0.389

Limit State Material

122

Sample Simulations of Degradation behavior
α is best obtained from calibration of test results. α is used to relate damage from one strain range
to an equivalent damage at another strain range. This is usually constant for a material type.

Cf is the ductility constant used to adjust the number of cycles to failure. A higher value for Cf will
result in a lower damage for each cycle. A higher value Cf translates to a larger number of cycles
to failure.

Cd is the strength reduction constant. A larger value for Cd will result in a lower reduction of
strength for each cycle. The four charts shown in Figure 8 demonstrate the effect that some of the
variables have on the cyclic response.

Chapter 11

Limit State Material

123

Figure 8: Fatigue and Degradation Parameter Examples

In Figure 8, the upper left response contains no strength degradation by setting the Cd variable to
0.0. The upper right response shows strength degradation due to the suggested values of Cf, α,
and Cd. The response shown on the lower left demonstrates the change in the response when the
suggested values of Cf and α are used with Cd=0.6. Making the value of Cd larger results in less
strength reduction due to damage. The response on the lower right once again returns to the
suggested values but Cf is changed to 0.15. This results in a more rapid accumulation of damage
causing the bar to fail sooner. Note however that the strength degradation is unaffected by the
more rapid accumulation of damage. The strength reduction and failure are not interdependent
making the model easier to calibrate.

References
1

Chang, G. and Mander, J. (1994). “Seismic Energy Based Fatigue Damage Analysis of Bridge
Columns: Part I – Evaluation of Seismic Capacity.” NCEER Technical Report 94-0006.

Chapter 11

Limit State Material

124

2 Dodd, L. and Restrepo-Posada, J. (1995). “Model for Predicting Cyclic Behavior of Reinforcing
Steel” J. Struct. Eng., 121(3), 433-445.
3 Gomes, A., and Appleton, J. (1997). “Nonlinear Cyclic Stress-Strain Relationship of
Reinforcing Bars Including Buckling.” Eng. Struct., 19(10), 822–826.
4 Brown, J. and Kunnath, S.K. (2000). “Low Cycle Fatigue Behavior of Longitudinal
Reinforcement in Reinforced Concrete Bridge Columns.” NCEER Technical Report 00-0007.
5 Dhakal, R. and Maekawa, K. (2002). “Modeling for Postyield Buckled of Reinforcement” J.
Struct. Eng., 128(9), 1139-1147.

125

CHAPTER 12

ReinforcingSteel -- Material
Behavior
Each material was subjected to a series of ten uniaxial tension and compression strain histories.
The following is the response of this material to such strain excursions. The data shown are the
normalized stresses versus strain. In the normalization, the steel stress was divided by the yield
stress Fy and the concrete stress was divided by the absolute value of compressive strength fc -to maintain positive tension and negative compression. The first figure shows all 10 load patterns
together, which are subsequently shown individually.

Elastic Material
This command is used to construct an elastic uniaxial material object.

uniaxialMaterial Elastic $matTag $E <$eta>
$matTag

unique material object integer tag

$E

tangent

$eta

damping tangent (optional, default=0.0)

Chapter 12

ReinforcingSteel -- Material Behavior

Figure 8: Elastic Material

Elastic-Perfectly Plastic Material
This command is used to construct an elastic perfectly-plastic uniaxial material object.

uniaxialMaterial ElasticPP $matTag $E $epsyP <$epsyN $eps0>
$matTag

unique material object integer tag

$E

tangent

126

Chapter 12

ReinforcingSteel -- Material Behavior

$epsyP

strain or deformation at which material reaches plastic state in
tension

$epsyN

strain at which material reaches plastic state in compression
(optional, default: tension value)

$eps0

initial strain (optional, default: zero)

127

Chapter 12

ReinforcingSteel -- Material Behavior

128

Figure 9: Elastic-Perfectly Plastic Material

Elastic-Perfectly Plastic Gap Material
This command is used to construct an elastic perfectly-plastic gap uniaxial material object.

uniaxialMaterial ElasticPPGap $matTag $E $Fy $gap <$eta> <damage>
$matTag

unique material object integer tag

$E

tangent stiffness

$Fy

stress or force at which material reaches plastic state

$gap

initial gap (strain or deformation)

$eta

hardening ratio (=Eh/E), which can be negative

damage

a switch to accumulate damage in the material. If damage is
omitted, default value, the gap material "re-centers" on load
reversal.

NOTE: To create a compression-only gap element, NEGATIVE values need to be specified for
$Fy and $gap.

Figure 10: Elastic-Perfectly Plastic Gap Material

Chapter 12

ReinforcingSteel -- Material Behavior

Elastic-No Tension Material
This command is used to construct a uniaxial elastic-no tension material object.

uniaxialMaterial ENT $matTag $E
$matTag

unique material object integer tag

$E

elastic model in compression

In tension, there is zero stress.

129

Chapter 12

ReinforcingSteel -- Material Behavior

130

Figure 11: Elastic-No Tension Material

Parallel Material
This command is used to construct a parallel material object made up of an arbitrary number of
previously-constructed UniaxialMaterial (page 43) objects.

uniaxialMaterial Parallel $matTag $tag1 $tag2 ...
$matTag

unique material object integer tag

$tag1 $tag2 ...

identification of materials making up the material model

The parallel material is represented graphically:

Figure 12: Parallel Material

Chapter 12

ReinforcingSteel -- Material Behavior

131

In a parallel model, strains are equal and stresses and stiffnesses are
additive:

Series Material
This command is used to construct a series material object made up of an arbitrary number of
previously-constructed UniaxialMaterial (page 43) objects.

uniaxialMaterial Series $matTag $tag1 $tag2 ...
$matTag

unique material object integer tag

$tag1 $tag2 ...

identification of materials making up the material model

Chapter 12

ReinforcingSteel -- Material Behavior

The series material is represented graphically:

Figure 13: Series Material

In a series model, stresses are equal and strains and flexibilities are additive:

132

Chapter 12

ReinforcingSteel -- Material Behavior

133

Figure 14: Series Material Relationship

Hardening Material
This command is used to construct a uniaxial material object with combined linear kinematic and
isotropic hardening. The model includes optional visco-plasticity using a Perzyna formulation
(REF???)

uniaxialMaterial Hardening $matTag $E $sigmaY $H_iso $H_kin <$eta>
$matTag

unique material object integer tag

$E

tangent stiffness

$sigmaY

yield stress or force

$H_iso

isotropic hardening Modulus

$H_kin

kinematic hardening Modulus

$eta

visco-plastic coefficient (optional, default=0.0)

Figure 15: Hardening Material

Chapter 12

ReinforcingSteel -- Material Behavior

134

Concrete01 Material -- Zero Tensile Strength
This command is used to construct a uniaxial Kent-Scott-Park concrete material object with
degraded linear unloading/reloading stiffness according to the work of Karsan-Jirsa and no tensile
strength. (REF: Fedeas).

uniaxialMaterial Concrete01 $matTag $fpc $epsc0 $fpcu $epsU
$matTag

unique material object integer tag

$fpc

concrete compressive strength at 28 days (compression is
negative)*

$epsc0

concrete strain at maximum strength*

$fpcu

concrete crushing strength *

$epsU

concrete strain at crushing strength*

*NOTE: Compressive concrete parameters should be input as negative values.
The initial slope for this model is (2*$fpc/$epsc0)

Chapter 12

ReinforcingSteel -- Material Behavior

Figure 16: Concrete01 Material -- Material Parameters
Concrete01 Material -- Material Parameters

135

Chapter 12

ReinforcingSteel -- Material Behavior

Figure 17: Typical Hysteretic Stress-Strain Relation of Concrete_1 Model
Typical Hysteretic Stress-Strain Relation of Concrete_1 Model

136

137

CHAPTER 13

Concrete01 -- Material Behavior
Each material was subjected to a series of ten uniaxial tension and compression strain histories.
The following is the response of this material to such strain excursions. The data shown are the
normalized stresses versus strain. In the normalization, the steel stress was divided by the yield
stress Fy and the concrete stress was divided by the absolute value of compressive strength fc -to maintain positive tension and negative compression. The first figure shows all 10 load patterns
together, which are subsequently shown individually.

Concrete02 Material -- Linear Tension
Softening
This command is used to construct a uniaxial concrete material object with tensile strength and
linear tension softening. This is a Fedeas Material and the source code may not be available, yet.

uniaxialMaterial Concrete02 $matTag $fpc $epsc0 $fpcu $epsU $lambda $ft
$Ets
$matTag

unique material object integer tag

$fpc

compressive strength*

$epsc0

strain at compressive strength*

$fpcu

crushing strength*

$epsU

strain at crushing strength*

$lambda

ratio between unloading slope at $epscu and initial slope

$ft

tensile strength

$Ets

tension softening stiffness (absolute value) (slope of the linear
tension softening branch)

Chapter 13

Concrete01 -- Material Behavior

*NOTE: Compressive concrete parameters should be input as negative values.

138

Chapter 13

The initial slope for this model is (2*$fpc/$epsc0)

Figure 18: Concrete02 Material -- Material parameters
Concrete02 Material -- Material parameters

Concrete01 -- Material Behavior

139

Chapter 13

Concrete01 -- Material Behavior

Figure 19: Typical Hysteretic Stress-Strain Relation of Concrete_2 Model
Typical Hysteretic Stress-Strain Relation of Concrete_2 Model

Figure 20: Hysteretic Stress-Strain Relation of Concrete_2 Model in Tension-Compression
Hysteretic Stress-Strain Relation of Concrete_2 Model in Tension-Compression

140

Chapter 13

Concrete01 -- Material Behavior

141

Chapter 13

Concrete01 -- Material Behavior

Figure 21: Hysteretic Stress-Strain Relation of Concrete_2 Model in Tension-Compression
(Detail)
Hysteretic Stress-Strain Relation of Concrete_2 Model in Tension-Compression (Detail)

Figure 22: Comparison of Hysteretic Behavior of Concrete_1 and Concrete_2 model
Comparison of Hysteretic Behavior of Concrete_1 and Concrete_2 model

142

143

CHAPTER 14

Concrete02 -- Material Behavior
Each material was subjected to a series of ten uniaxial tension and compression strain histories.
The following is the response of this material to such strain excursions. The data shown are the
normalized stresses versus strain. In the normalization, the steel stress was divided by the yield
stress Fy and the concrete stress was divided by the absolute value of compressive strength fc -to maintain positive tension and negative compression. The first figure shows all 10 load patterns
together, which are subsequently shown individually.

Concrete03 Material -- Nonlinear Tension
Softening
This command is used to construct a uniaxial concrete material object with tensile strength and
nonlinear tension softening. This is a Fedeas Material and the source code may not be available,
yet.

uniaxialMaterial Concrete03 $matTag $fpc $epsc0 $fpcu $epsU $lambda $ft
$epst0 $ft0 $beta $epstu
$matTag

unique material object integer tag

$fpc

compressive strength*

$epsc0

strain at compressive strength*

$fpcu

crushing strength*

$epsU

strain at crushing strength*

$lambda

ratio between unloading slope at $epscu and initial slope
(=2*$fpc/$epsc0)

$ft

tensile strength

$epst0

tensile strain at the transition from nonlinear to linear softening

Chapter 14

Concrete02 -- Material Behavior

$ft0

tensile stress at the transition from nonlinear to linear softening

$beta

exponent of the tension softening curve

$epstu

ultimate tensile strain

144

Chapter 14

Concrete02 -- Material Behavior

*NOTE: Compressive concrete parameters should be input as negative values.

Figure 23: Concrete03 Material -- Material Parameters
Concrete03 Material -- Material Parameters

145

Chapter 14

Concrete02 -- Material Behavior

146

Figure 24: Hysteretic stress-strain relation of Concrete_3 model in Tension-Compression
Hysteretic stress-strain relation of Concrete_3 model in Tension-Compression

Figure 25: Hysteretic stress-strain relation of Concrete_3 model in Tension-Compression (Detail)
Hysteretic stress-strain relation of Concrete_3 model in Tension-Compression (Detail)

147

CHAPTER 15

Concrete03 -- Material Behavior
Each material was subjected to a series of ten uniaxial tension and compression strain histories.
The following is the response of this material to such strain excursions. The data shown are the
normalized stresses versus strain. In the normalization, the steel stress was divided by the yield
stress Fy and the concrete stress was divided by the absolute value of compressive strength fc -to maintain positive tension and negative compression. The first figure shows all 10 load patterns
together, which are subsequently shown individually.

Steel01 Material
This command is used to construct a uniaxial bilinear steel material object with kinematic
hardening and optional isotropic hardening described by a non-linear evolution equation (REF:
Fedeas).

uniaxialMaterial Steel01 $matTag $Fy $E0 $b <$a1 $a2 $a3 $a4>
$matTag

unique material object integer tag

$Fy

yield strength

$E0

initial elastic tangent

$b

strain-hardening ratio (ratio between post-yield tangent and initial
elastic tangent)

$a1, $a2, $a3, $a4

isotropic hardening parameters: (optional, default: no isotropic
hardening)
$a1

isotropic hardening parameter, increase of compression
yield envelope as proportion of yield strength after a
plastic strain of $a2*($Fy/E0).

$a2

isotropic hardening parameter (see explanation under
$a1)

Chapter 15

Concrete03 -- Material Behavior

$a3

isotropic hardening parameter, increase of tension yield
envelope as proportion of yield strength after a plastic
strain of $a4*($Fy/E0)

$a4

isotropic hardening parameter (see explanation under
$a3)

148

Chapter 15

Concrete03 -- Material Behavior

Figure 26: Steel01 Material -- Material Parameters of Monotonic Envelope
Steel01 Material -- Material Parameters of Monotonic Envelope

149

Chapter 15

Concrete03 -- Material Behavior

Figure 27: Steel01 Material -- Hysteretic Behavior of Model w/o Isotropic Hardening
Steel01 Material -- Hysteretic Behavior of Model w/o Isotropic Hardening

Figure 28: Hysteretic Behavior of Model with Isotropic Hardening in Compression
Steel01 Material -- Hysteretic Behavior of Model with Isotropic Hardening in Compression

150

Chapter 15

Concrete03 -- Material Behavior

151

Figure 29: Steel01 Material -- Hysteretic Behavior of Steel_1 Model with Isotropic Hardening in
Tension

Steel01 Material -- Hysteretic Behavior of Steel_1 Model with Isotropic Hardening in Tension

152

CHAPTER 16

Steel01 -- Material Behavior
Each material was subjected to a series of ten uniaxial tension and compression strain histories.
The following is the response of this material to such strain excursions. The data shown are the
normalized stresses versus strain. In the normalization, the steel stress was divided by the yield
stress Fy and the concrete stress was divided by the absolute value of compressive strength fc -to maintain positive tension and negative compression. The first figure shows all 10 load patterns
together, which are subsequently shown individually.

Chapter 16

Steel01 -- Material Behavior

153

Steel02 Material -- Giuffré-Menegotto-Pinto
Model with Isotropic Strain Hardening
This command is used to construct a uniaxial Giuffre-Menegotto-Pinto steel material object with
isotropic strain hardening.

uniaxialMaterial Steel02 $matTag $Fy $E $b $R0 $cR1 $cR2 $a1 $a2 $a3 $a4
$matTag

unique material object integer tag

$Fy

yield strength

$E

initial elastic tangent

$b

strain-hardening ratio (ratio between post-yield tangent and initial
elastic tangent)

$R0, $cR1, $cR2

control the transition from elastic to plastic branches.
Recommended values:
$R0=between 10 and 20, $cR1=0.925, $cR2=0.15

$a1, $a2, $a3, $a4

isotropic hardening parameters: (optional, default: no isotropic
hardening)
$a1

isotropic hardening parameter, increase of compression
yield envelope as proportion of yield strength after a
plastic strain of $a2*($Fy/$E).

$a2

isotropic hardening parameter (see explanation under
$a1)

$a3

isotropic hardening parameter, increase of tension yield
envelope as proportion of yield strength after a plastic
strain of $a4*($Fy/$E)

$a4

isotropic hardening parameter (see explanation under
$a3)

Chapter 16

Steel01 -- Material Behavior

154

Chapter 16

Steel01 -- Material Behavior

Figure 30: Steel02 Material -- Material Parameters of Monotonic Envelope
Steel02 Material -- Material Parameters of Monotonic Envelope

Figure 31: Steel02 Material -- Hysteretic Behavior of Model w/o Isotropic Hardening
Steel02 Material -- Hysteretic Behavior of Model w/o Isotropic Hardening

155

Chapter 16

Steel01 -- Material Behavior

Figure 32: Steel02 Material -- Hysteretic Behavior of Model with Isotropic Hardening in
Compression
Steel02 Material -- Hysteretic Behavior of Model with Isotropic Hardening in Compression

156

Chapter 16

Steel01 -- Material Behavior

157

Figure 33: Steel02 Material -- Hysteretic Behavior of Model with Isotropic Hardening in Tension
Steel02 Material -- Hysteretic Behavior of Model with Isotropic Hardening in Tension

158

CHAPTER 17

Steel02 -- Material Behavior
Each material was subjected to a series of ten uniaxial tension and compression strain histories.
The following is the response of this material to such strain excursions. The data shown are the
normalized stresses versus strain. In the normalization, the steel stress was divided by the yield
stress Fy and the concrete stress was divided by the absolute value of compressive strength fc -to maintain positive tension and negative compression. The first figure shows all 10 load patterns
together, which are subsequently shown individually.

Hysteretic Material
This command is used to construct a uniaxial bilinear hysteretic material object with pinching of
force and deformation, damage due to ductility and energy, and degraded unloading stiffness
based on ductility.

uniaxialMaterial Hysteretic $matTag $s1p $e1p $s2p $e2p <$s3p $e3p> $s1n
$e1n $s2n $e2n <$s3n $e3n> $pinchX $pinchY $damage1 $damage2
<$beta>
$matTag

unique material object integer tag

$s1p

$e1p

stress and strain (or force & deformation) at first point of the
envelope in the positive direction

$s2p

$e2p

stress and strain (or force & deformation) at second point of the
envelope in the positive direction

$s3p

$e3p

stress and strain (or force & deformation) at third point of the
envelope in the positive direction (optional)

Chapter 17

Steel02 -- Material Behavior

$s1n

$e1n

stress and strain (or force & deformation) at first point of the
envelope in the negative direction*

$s2n

$e2n

stress and strain (or force & deformation) at second point of the
envelope in the negative direction*

$s3n

$e3n

stress and strain (or force & deformation) at third point of the
envelope in the negative direction (optional)*

$pinchX

pinching factor for strain (or deformation) during reloading

$pinchY

pinching factor for stress (or force) during reloading

$damage1

damage due to ductility: D1(mu-1)

$damage2

damage due to energy: D2(Eii/Eult)

$beta

power used to determine the degraded unloading stiffness based
on ductility, mu-beta (optional, default=0.0)

*NOTE: negative backbone points should be entered as negative numeric values

159

Chapter 17

Figure 34: Hysteretic Material

Steel02 -- Material Behavior

160

161

CHAPTER 18

Hysteretic -- Material Behavior
Each material was subjected to a series of ten uniaxial tension and compression strain histories.
The following is the response of this material to such strain excursions. The data shown are the
normalized stresses versus strain. In the normalization, the steel stress was divided by the yield
stress Fy and the concrete stress was divided by the absolute value of compressive strength fc -to maintain positive tension and negative compression. The first figure shows all 10 load patterns
together, which are subsequently shown individually.

Viscous Material
This command is used to construct a uniaxial material object with a non-linear elastic
stress-strain-rate relation given by:
stress =C(strain-rate)alpha.

uniaxialMaterial Viscous $matTag $C $alpha
$matTag

unique material object integer tag

$C

tangent

$alpha

damping tangent

162

CHAPTER 19

nDMaterial Command
This command is used to construct an NDMaterial object which represents stress-strain
relationships at the integration points of continuum and force-deformation elements.
The valid queries to any ND material when creating an ElementRecorder (page 307) are 'strain,'
'stress,' and 'tangent.'

In This Chapter
Elastic Isotropic Material........................................... 162
J2 Plasticity Material................................................. 163
Plane Stress Material ............................................... 163
Plate Fiber Material .................................................. 164
UC Davis Soil Models............................................... 164
UCSD Soil Models.................................................... 169

Elastic Isotropic Material
This command is used to construct an ElasticIsotropic material object.

nDMaterial ElasticIsotropic $matTag $E $v
$matTag

unique material object integer tag

$E

elastic Modulus

$v

Poisson's ratio

The material formulations for the ElasticIsotropic object are "ThreeDimensional," "PlaneStrain,"
"Plane Stress," "AxiSymmetric," and "PlateFiber." These are the valid strings that can be passed
to the continuum elements (page 231, page 228, page 229, page 227, page 228, page 230) for the
type parameter.

Chapter 19

nDMaterial Command

J2 Plasticity Material
This command is used to construct a J2Plasticity material object.

nDmaterial J2Plasticity $matTag $K $G $sig0 $sigInf $delta $H
$matTag

unique material object integer tag

$K

bulk Modulus

$G

shear Modulus

$sig0

initial yield stress

$sigInf

final saturation yield stress

$delta

exponential hardening parameter

$H

linear hardening parameter

Plane Stress Material
This command is used to construct a plane-stress material wrapper which converts any
three-dimensional material into a plane stress material via static condensation.

nDMaterial PlaneStress $matTag $threeDtag
$matTag

unique material object integer tag

$threeDTag

material tag for a previously-defined three-dimensional material

163

Chapter 19

nDMaterial Command

164

Plate Fiber Material
This command is used to construct a plate-fiber material wrapper which converts any
three-dimensional material into a plate fiber material (by static condensation) appropriate for shell
analysis.

nDMaterial PlateFiber $matTag $threeDTag
$matTag

unique material object integer tag

$threeDTag

material tag for a previously-defined three-dimensional material

UC Davis Soil Models
For further information or examples about the following models, please visit:
http://sokocalo.engr.ucdavis.edu/~jeremic/ (http://sokocalo.engr.ucdavis.edu/~jeremic/)

Template Elasto-Plastic Material
This command is used to construct the template elasto-plastic material object.

nDMaterial Template3Dep $matTag $ElmatTag -YS $ys -PS $ps -EPS $eps
<-ELS1 $el> <-ELT1 $et>
$matTag

unique material object tag

$ElmatTag

previously defined elastic nDMaterial (such as ElasticIsotropic3D (page 162),
PressureDependentElastic3D) tag

$ys

yield surface variable, previously defined in Yield Surface (page 165) object

$ps

potential surface variable, previously defined in Potential Surface (page 166)
object

$eps

elasto-plastic state variable, previously defined in EPState (page 168) object

$el

scalar (isotropic) evolution law variable, previously defined in Evolution Law
(page 167) object

Chapter 19

$et

nDMaterial Command

165

tensorial (kinematic) evolution law variable, previously defined in Evolution
Law (page 167) object

Yield Surface
This command sets the yield surface variable ys to be the specified type. Currently these include:
Drucker-Prager yield surface, Rounded Mohr-Coulomb (Willam-Warnke) yield surface, von Mises
yield surface, Cam-Clay yield surface and Leon yield surface.

set ys "-YieldSurfaceType <parameter list>"
Valid strings for YieldSurfaceType are DP, VM and CC.

 For Drucker-Prager yield surface
set ys "-DP"

 For von Mises yield surface
set ys "-VM"

 For rounded Mohr-Coulomb (Willam-Warnke) yield surface
set ys "-RMC01"

 For Cam-Clay yield surface
set ys "-CC $M"
$M

Slope of the critical state line in p-q space

 For Leon yield surface
set ys "-Leon $fc $ft $e $c"
$fc

compressive strength

Chapter 19

nDMaterial Command

$ft

tensile strength

$e

excentricity of yield surface (usually 0.6-0.7)

$c

cohesion

166

Potential Surface
This command is used to set the potential surface variable $ps to the specific surface (or directly to
the flow directions). Currently included are: Drucker-Prager potential surface, Rounded
Mohr-Coulomb (Willam-Warnke) potential surface, von Mises potential surface, Cam-Clay
potential surface and Leon potential surface.

set ps "-PotentialSurfaceType <parameter list>"
Valid strings for PotentialSurfaceType are DP, VM and CC.

 For the Drucker-Prager potential surface
set ps "-DP"

 For the von Mises potential surface
set ps "-VM"

 For rounded Mohr-Coulomb (Willam-Warnke) potential surface
set ps "-RMC01"

 For the Cam-Clay potential surface
set ps "-CC $M"
$M

Slope of the critical state line in p-q space

Chapter 19

nDMaterial Command

167

 For Leon potential surface
set ps "-Leon $fc $ft $e $c"
$fc

compressive strength

$ft

tensile strength

$e

excentricity of yield surface (usually 0.6-0.7)

$c

cohesion

Evolution Law
This command is used to set the evolution law variable el to the specified type. There are two
types of evolutions laws implemented: scalar (isotropic) evolution and tensorial (kinemartic)
evolution. For scalar evolution law, there are linear scalar evolution law and nonlinear scalar
evolution law. For tensorial evolution law, there are linear tensorial evolution law and nonlinear
tensorial evolution law.

set el "-EvolutionLawType <parameter list>"
Valid strings for EvolutionLawType are Leq, NLp, LEij, and NLEij

 For linear scalar evolution law
set el "-Leq $a"

 For Cam-Clay type nonlinear scalar evolution law
set el "-NLp $e_o $lambda $k

 For linear tensorial evolution law
set et "-LEij $a1"

 For Armstrong-Frederick type nonlinear tensorial evolution law
set et "-NLEij $h_a $C_r"

Chapter 19

nDMaterial Command

168

$a

linear hardening coefficient

$e_o

initial void ratio

$lambda

nonlinear evolution law constant (Cam-Clay type)

$k

nonlinear evolution law constant (Cam-Clay type)

$a1

linear tensorial evolution law constant

$h_a

nonlinear tensorial evolution law constant (Armstrong-Frederick type)

$C_r

nonlinear tensorial evolution law constant (Armstrong-Frederick type)

EPState
This command is used to set the Elasto-Plastic State, which includes two states.

 To set the initial stress tensor to variable sts, if –stressp $sts is used in eps:
set sts "$sigma_xx $sigma_xy $sigma_xz $sigma_yx $sigma_yy $sigma_yz
$sigma_zx $sigma_zy $sigma_zz"
 To assign to the Elasto-Plastic state variable eps the specified state parameters
set eps "<-NOD $nt> -NOS $ns $scalar1 $scalar2 ... <-stressp $sts>"
$sigma_xx $sigma_xy $sigma_xz
$sigma_yx $sigma_yy $sigma_yz
$sigma_zx $sigma_zy $sigma_zz

Initial stress tensor components (Default = 0.0),

$nt

number of tensorial internal variables

$ns

number of scalar internal variables

$scalar1 $scalar2 ...

corresponding initial values of scalar internal variables

$sts

initial stresses

Chapter 19

nDMaterial Command

169

UCSD Soil Models
This chapter describes the user interfaces for: 1) a number of NDMaterial models developed for
simulating nonlinear, drained/undrained soil response under general 3D cyclic loading conditions
Please visit http://cyclic.ucsd.edu/opensees (http://cyclic.ucsd.edu/opensees) for examples.
This documentation is last updated at 8/5/2005 by Zhaohui Yang (zhyang@ucsd.edu
(mailto:zhyang@ucsd.edu)) and Ahmed Elgamal (elgamal@ucsd.edu
(mailto:elgamal@ucsd.edu)).

FluidSolidPorousMaterial
FluidSolidPorousMaterial couples the responses of two phases: fluid and solid. The fluid phase
response is only volumetric and linear elastic. The solid phase can be any NDMaterial. This
material is developed to simulate the response of saturated porous media under fully undrained
condition. Please visit http://cyclic.ucsd.edu/opensees (http://cyclic.ucsd.edu/opensees) for
examples.

OUTPUT INTERFACE:
The following information may be extracted for this material at given integration point, using the
OpenSees Element Recorder facility (McKenna and Fenves 2001): "stress", "strain", "tangent",
or "pressure". The "pressure" option records excess pore pressure and excess pore pressure
ratio at a given material integration point.

nDMaterial FluidSolidPorousMaterial $tag $nd $soilMatTag
$combinedBulkModul
$tag

A positive integer uniquely identifying the material among all nDMaterials

$nd

Number of dimensions, 2 for plane-strain, and 3 for general 3D analysis.

$soilMatTag

The material number for the solid phase material (previously defined).

Chapter 19

$combinBulkModul

nDMaterial Command

170

Combined undrained bulk modulus Bc relating changes in pore pressure
and volumetric strain, may be approximated by:

Bc ≈ B f / n
where Bf is the bulk modulus of fluid phase (2.2x106 kPa for water
typically), and n the initial porosity.
1
NOTE:
1

Buoyant unit weight (total unit weight - fluid unit weight) should be used in definition of the finite
elements composed of a FluidSolidPorousMaterial.

2 During the application of gravity (elastic) load, the fluid phase does not contribute to the
material response.

Chapter 19

nDMaterial Command

171

PressureDependMultiYield Material
PressureDependMultiYield material is an elastic-plastic material for simulating the essential
response characteristics of pressure sensitive soil materials under general loading conditions.
Such characteristics include dilatancy (shear-induced volume contraction or dilation) and non-flow
liquefaction (cyclic mobility), typically exhibited in sands or silts during monotonic or cyclic loading.
Please visit http://cyclic.ucsd.edu/opensees (http://cyclic.ucsd.edu/opensees) for examples.

When this material is employed in regular solid elements (e.g., FourNodeQuad, Brick), it simulates
drained soil response. To simulate soil response under fully undrained condition, this material may
be either embedded in a FluidSolidPorousMaterial (see below), or used with one of the
solid-fluid fully coupled elements (see below) with very low permeability. To simulate partially
drained soil response, this material should be used with a solid-fluid fully coupled element with
proper permeability values.

During the application of gravity load (and static loads if any), material behavior is linear elastic. In
the subsequent dynamic (fast) loading phase(s), the stress-strain response is elastic-plastic (see
MATERIAL STAGE UPDATE below). Plasticity is formulated based on the multi-surface (nested
surfaces) concept, with a non-associative flow rule to reproduce dilatancy effect. The yield
surfaces are of the Drucker-Prager type.

OUTPUT INTERFACE:
The following information may be extracted for this material at a given integration point, using the
OpenSees Element Recorder facility (McKenna and Fenves 2001): "stress", "strain",
"backbone", or "tangent".
For 2D problems, the stress output follows this order: σxx, σyy, σzz, σxy, ηr, where ηr is the ratio
between the shear (deviatoric) stress and peak shear strength at the current confinement
(0<= ηr<=1.0). The strain output follows this order: εxx, εyy, γxy.
For 3D problems, the stress output follows this order: σxx, σyy, σzz, σxy, σyz, σzx, ηr, and the strain output
follows this order: εxx, εyy, εzz, γxy, γyz, γzx.
The "backbone" option records (secant) shear modulus reduction curves at one or more given
confinements. The specific recorder command is as follows:

recorder Element –ele $eleNum -file $fName -dT $deltaT material $GaussNum backbone
$p1 <$p2 …>

Chapter 19

nDMaterial Command

172

where p1, p2, … are the confinements at which modulus reduction curves are recorded. In the
output file, corresponding to each given confinement there are two columns: shear strain γ and
secant modulus Gs. The number of rows equals the number of yield surfaces.

nDMaterial PressureDependMultiYield $tag $nd $rho $refShearModul
$refBulkModul $frictionAng $peakShearStra $refPress
$pressDependCoe $PTAng $contrac $dilat1 $dilat2 $liquefac1
$liquefac2 $liquefac3 <$noYieldSurf=20 <$r1 $Gs1 …> $e=0.6
$cs1=0.9 $cs2=0.02 $cs3=0.7 $pa=101>
Octahedral
shear stress τ
$τ f
Shear stress-strain at p'r

Octahedral
shear strain γ

$Gr
$γmax

$tag

A positive integer uniquely identifying the material among all nDMaterials.

$nd

Number of dimensions, 2 for plane-strain, and 3 for 3D analysis.

$rho

Saturated soil mass density.

$refShearModul
(Gr)

Reference low-strain shear modulus, specified at a reference mean
effective confining pressure refPress of p’r (see below).

$refBulkModul (Br)

Reference bulk modulus, specified at a reference mean effective
confining pressure refPress of p’r (see below).

$frictionAng (f)

Friction angle at peak shear strength, in degrees.

Chapter 19

$peakShearStra
(gmax)

nDMaterial Command

173

An octahedral shear strain at which the maximum shear strength is
reached, specified at a reference mean effective confining pressure
refPress of p’r (see below).
Octahedral shear strain is defined as:

γ =

[

]

1/ 2
2
ε xx − ε yy )2 + (ε yy − ε zz )2 + (ε xx − ε zz )2 + 6ε xy2 + 6ε yz2 + 6ε xz2
(
3

$refPress (p’r)

Reference mean effective confining pressure at which Gr, Br, and γmax are
defined.

$pressDependCoe
(d)

A positive constant defining variations of G and B as a function of
instantaneous effective confinement p’:

G = Gr (

p′ d
)
p ′r

B = Br (

p′ d
)
p ′r

$PTAng (φPT)

Phase transformation angle, in degrees.

$contrac

A non-negative constant defining the rate of shear-induced volume
decrease (contraction) or pore pressure buildup. A larger value
corresponds to faster contraction rate.

$dilat1, $dilat2

Non-negative constants defining the rate of shear-induced volume
increase (dilation). Larger values correspond to stronger dilation rate.

$liquefac1,
$liquefac2,
$liquefac3

Parameters controlling the mechanism of liquefaction-induced perfectly
plastic shear strain accumulation, i.e., cyclic mobility. Set liquefac1 = 0 to
deactivate this mechanism altogether. liquefac1 defines the effective
confining pressure (e.g., 10 kPa) below which the mechanism is in effect.
Smaller values should be assigned to denser sands. liquefac2 defines the
maximum amount of perfectly plastic shear strain developed at zero
effective confinement during each loading phase. Smaller values should
be assigned to denser sands. liquefac3 defines the maximum amount of
biased perfectly plastic shear strain γb accumulated at each loading phase
under biased shear loading conditions, as γb=liquefac2 x liquefac3.
Typically, liquefac3 takes a value between 0.0 and 3.0. Smaller values
should be assigned to denser sands. See the references listed at the end
of this chapter for more information.

$noYieldSurf

Number of yield surfaces, optional (must be less than 40, default is 20).
The surfaces are generated based on the hyperbolic relation defined in
Note 2 below.

Chapter 19

$r , $Gs

nDMaterial Command

174

Instead of automatic surfaces generation (Note 2), you can define yield
surfaces directly based on desired shear modulus reduction curve.
To do so, add a minus sign in front of noYieldSurf, then provide
noYieldSurf pairs of shear strain (γ ) and modulus ratio (Gs) values. For
example, to define 10 surfaces:
… -10 γ1 Gs1 … γ10 Gs10 …
See Note 3 below for some important notes.

$e

Initial void ratio, optional (default is 0.6).

$cs1, $cs2, $cs3,
$pa

Parameters defining a straight critical-state line ec in e-p’ space.
If cs3=0,

ec = cs1 − cs 2 log( p ′ / p a )
else (Li and Wang, JGGE, 124(12)),

ec = cs1 − cs2( p ′ / p a ) cs3
where pa is atmospheric pressure for normalization (typically 101 kPa in
SI units). All four constants are optional (default values: cs1=0.9,
cs2=0.02, cs3=0.7, pa =101).

NOTE:
The friction angle φ defines the variation of peak (octahedral) shear strength τf as a function of
current effective confinement p’:

τf =
1

2 2 sin φ
p′
3 − sin φ

Octahedral shear stress is defined as:

τ =

1/ 2
1
σ xx − σ yy )2 + (σ yy − σ zz )2 + (σ xx − σ zz )2 + 6σ xy2 + 6σ yz2 + 6σ xz2
(
3

[

]

Chapter 19

1

nDMaterial Command

175

(Automatic surface generation) At a constant confinement p’, the shear stress τ (octahedral) shear strain γ (octahedral) nonlinearity is defined by a hyperbolic curve (backbone curve):

Gγ

τ=
1+

γ  p′r 
 
γ r  p′ 

d

where γr satisfies the following equation at p’r:

τf =

G r γ max
2 2 sin φ
p r′ =
3 − sin φ
1 + γ max / γ r

(User defined surfaces) The user specified friction angle f is ignored. Instead, f is defined as
follows:

sin φ =

3 3 σ m / p r′
6 + 3 σ m / p r′

where sm is the product of the last modulus and strain pair in the modulus reduction curve.
Therefore, it is important to adjust the backbone curve so as to render an appropriate f. If the
resulting f is smaller than the phase transformation angle fPT, fPT is set equal to f.
Also remember that improper modulus reduction curves can result in strain softening response
(negative tangent shear modulus), which is not allowed in the current model formulation. Finally,
note that the backbone curve varies with confinement, although the variations are small within
commonly interested confinement ranges. Backbone curves at different confinements can be
obtained using the OpenSees element recorder facility (see OUTPUT INTERFACE above).

1

The last five optional parameters are needed when critical-state response (flow liquefaction) is
anticipated. Upon reaching the critical-state line, material dilatancy is set to zero.

1

SUGGESTED PARAMETER VALUES

Chapter 19

nDMaterial Command

176

For user convenience, a table is provided below as a quick reference for selecting parameter
values. However, use of this table should be of great caution, and other information should be
incorporated wherever possible.

Loose Sand
(15%-35%)

Medium Sand
(35%-65%)

Medium-dense
Sand (65%-85%)

Dense Sand
(85%-100%)

Chapter 19

rho (ton/m3)

1.7

nDMaterial Command

1.9

2.0

2.1

refShearModul (kPa, 5.5x104
at p’r=80 kPa)

7.5x104

1.0x105

1.3x105

refBulkModu (kPa,
at p’r=80 kPa)

1.5x105

2.0x105

3.0x105

3.9x105

frictionAng

29

33

37

40

peakShearStra (at
p’r=80 kPa)

0.1

0.1

0.1

0.1

refPress (p’r, kPa)

80

80

80

80

pressDependCoe

0.5

0.5

0.5

0.5

PTAng

29

27

27

27

contrac

0.21

0.07

0.05

0.03

dilat1

0.

0.4

0.6

0.8

dilat2

0

2

3

5

liquefac1 (kPa)

10

10

5

0

liquefac2

0.02

0.01

0.003

0

liquefac3

1

1

1

0

e

0.85

0.7

0.55

0.45

177

Chapter 19

nDMaterial Command

178

PressureDependMultiYield02 Material
PressureDependMultiYield02 material is modified from PressureDependMultiYield material,
with: 1) additional parameters ($contrac3 and $dilat3) to account for Kσ effect, 2) a parameter to
account for the influence of previous dilation history on subsequent contraction phase ($contrac2),
and 3) modified logic related to permanent shear strain accumulation ($liquefac1 and $liquefac2).
Please visit http://cyclic.ucsd.edu/opensees (http://cyclic.ucsd.edu/opensees) for examples.

nDMaterial PressureDependMultiYield02 $tag $nd $rho $refShearModul
$refBulkModul $frictionAng $peakShearStra $refPress
$pressDependCoe $PTAng $contrac1 $contrac3 $dilat1 $dilat3
<$noYieldSurf=20 <$r1 $Gs1 …> $contrac2=5. $dilat2=3.
$liquefac1=1. $liquefac2=0. $e=0.6 $cs1=0.9 $cs2=0.02 $cs3=0.7
$pa=101>
$contrac3

A non-negative constant reflecting Kσ effect.

$dilat3

A non-negative constant reflecting Kσ effect.

$contrac2

A non-negative constant reflecting dilation history on contraction tendency.

$liquefac1

Damage parameter to define accumulated permanent shear strain as a
function of dilation history. (Redefined and different from
PressureDependMultiYield material).

Chapter 19

nDMaterial Command

179

$liquefac2

Damage parameter to define biased accumulation of permanent shear strain
as a function of load reversal history. (Redefined and different from
PressureDependMultiYield material).

Others

See PressureDependMultiYield material above.

Chapter 19

nDMaterial Command

180

Chapter 19

nDMaterial Command

181

NOTE:
The following values are suggested for the model parameters.

Dr=30%

Dr=40%

Dr=50%

Dr=60%

Dr=75%

Chapter 19

nDMaterial Command

182

rho (ton/m3)

1.7

1.8

1.9

2.0

2.1

refShearModul
(kPa, at p’r=80
kPa)

6x104

9x104

10x104

11x104

13x104

16x104

22x104

23.3x104

24x104

26x104

(K0=0.5)

(K0=0.47)

(K0=0.45)

(K0=0.43)

(K0=0.4)

frictionAng

31

32

33.5

35

36.5

PTAng

31

26

25.5

26

26

peakShearStra (at
p’r=101 kPa)

0.1

refPress (p’r, kPa)

101

pressDependCoe

0.5

Contrac1

0.087

0.067

0.045

0.028

0.013

Contrac3

0.18

0.23

0.15

0.05

0.0

dilat1

0.

0.06

0.06

0.1

0.3

dilat3

0.0

0.27

0.15

0.05

0.0

e

0.85

0.77

0.7

0.65

0.55

refBulkModu (kPa,
at p’r=80 kPa)

Chapter 19

nDMaterial Command

183

PressureIndependMultiYield Material
PressureIndependMultiYield material is an elastic-plastic material in which plasticity exhibits
only in the deviatoric stress-strain response. The volumetric stress-strain response is linear-elastic
and is independent of the deviatoric response. This material is implemented to simulate monotonic
or cyclic response of materials whose shear behavior is insensitive to the confinement change.
Such materials include, for example, organic soils or clay under fast (undrained) loading
conditions. Please visit http://cyclic.ucsd.edu/opensees (http://cyclic.ucsd.edu/opensees) for
examples.

During the application of gravity load (and static loads if any), material behavior is linear elastic. In
the subsequent dynamic (fast) loading phase(s), the stress-strain response is elastic-plastic (see
MATERIAL STAGE UPDATE below). Plasticity is formulated based on the multi-surface (nested
surfaces) concept, with an associative flow rule. The yield surfaces are of the Von Mises type.

OUTPUT INTERFACE:
The following information may be extracted for this material at a given integration point, using the
OpenSees Element Recorder facility (McKenna and Fenves 2001): "stress", "strain",
"backbone", or "tangent".
For 2D problems, the stress output follows this order: σxx, σyy, σzz, σxy, ηr, where ηr is the ratio
between the shear (deviatoric) stress and peak shear strength at the current confinement
(0<= ηr<=1.0). The strain output follows this order: εxx, εyy, γxy.
For 3D problems, the stress output follows this order: σxx, σyy, σzz, σxy, σyz, σzx, ηr, and the strain output
follows this order: εxx, εyy, εzz, γxy, γyz, γzx.
The "backbone" option records (secant) shear modulus reduction curves at one or more given
confinements. The specific recorder command is as follows:

recorder Element –ele $eleNum -file $fName -dT $deltaT material $GaussNum backbone
$p1 <$p2 …>

where p1, p2, … are the confinements at which modulus reduction curves are recorded. In the
output file, corresponding to each given confinement there are two columns: shear strain γ and
secant modulus Gs. The number of rows equals the number of yield surfaces.

Chapter 19

nDMaterial Command

184

nDmaterial PressureIndependMultiYield $tag $nd $rho $refShearModul
$refBulkModul $cohesi $peakShearStra <$frictionAng=0.
$refPress=100. $pressDependCoe=0. $noYieldSurf=20 <$r1 $Gs1 …>
>
Octahedral
shear stress τ
$τ f
Shear stress-strain at p'r

Octahedral
shear strain γ

$Gr
$γmax

$tag

A positive integer uniquely identifying the material among all nDMaterials.

$nd

Number of dimensions, 2 for plane-strain, and 3 for 3D analysis

$rho

Saturated soil mass density.

$refShearModul
(Gr)

Reference low-strain shear modulus, specified at a reference mean
effective confining pressure refPress of p’r (see below).

$refBulkModul (Br)

Reference bulk modulus, specified at a reference mean effective
confining pressure refPress of p’r (see below).

$cohesi (c)

Apparent cohesion at zero effective confinement.

$peakShearStra
(gmax)

An octahedral shear strain at which the maximum shear strength is
reached, specified at a reference mean effective confining pressure
refPress of p’r (see below).

$frictionAng (f)

Friction angle at peak shear strength in degrees, optional (default is 0.0).

$refPress (p’r)

Reference mean effective confining pressure at which Gr, Br, and γmax are
defined, optional (default is 100.).

Chapter 19

$pressDependCoe
(d)

nDMaterial Command

185

An optional non-negative constant defining variations of G and B as a
function of initial effective confinement p’i (default is 0.0):

G = Gr (

p i′ d
)
p r′

B = Br (

p i′ d
)
p r′

If φ=0, d is reset to 0.0.
$noYieldSurf

Number of yield surfaces, optional (must be less than 40, default is 20).
The surfaces are generated based on the hyperbolic relation defined in
Note 2 below.

$r , $Gs

Instead of automatic surfaces generation (Note 2), you can define yield
surfaces directly based on desired shear modulus reduction curve.
To do so, add a minus sign in front of noYieldSurf, then provide
noYieldSurf pairs of shear strain (γ ) and modulus ratio (Gs) values. For
example, to define 10 surfaces:
… -10 γ1 Gs1 … γ10 Gs10 …
See Note 3 below for some important notes.

NOTE:
1

The friction angle φ and cohesion c define the variation of peak (octahedral) shear strength τf
as a function of initial effective confinement p’i :

τf =
1

2 2 sin φ
2 2
p i′ +
c
3 − sin φ
3

Automatic surface generation: at a constant confinement p’, the shear stress τ (octahedral) shear strain γ (octahedral) nonlinearity is defined by a hyperbolic curve (backbone curve):

Gγ

τ=
1+

γ  p′r 
 
γ r  p′ 

d

where γr satisfies the following equation at p’r :

τf =

G r γ max
2 2 sin φ
2 2
p r′ +
c=
3 − sin φ
3
1 + γ max / γ r

Chapter 19

nDMaterial Command

186

(User defined surfaces) If the user specifies f=0, cohesion c will be ignored. Instead, c is defined
by c=sqrt(3)*sm/2, where sm is the product of the last modulus and strain pair in the modulus
reduction curve. Therefore, it is important to adjust the backbone curve so as to render an
appropriate c.
If the user specifies f>0, this f will be ignored. Instead, f is defined as follows:

sin φ =

3 ( 3 σ m − 2c) / p ′r
6 + ( 3 σ m − 2c) / p ′r

If the resulting f<0, we set f=0 and c=sqrt(3)*sm/2.
Also remember that improper modulus reduction curves can result in strain softening response
(negative tangent shear modulus), which is not allowed in the current model formulation. Finally,
note that the backbone curve varies with confinement, although the variation is small within
commonly interested confinement ranges. Backbone curves at different confinements can be
obtained using the OpenSees element recorder facility (see OUTPUT INTERFACE above).
1

SUGGESTED PARAMETER VALUES

For user convenience, a table is provided below as a quick reference for selecting parameter
values. However, use of this table should be of great caution, and other information should be
incorporated wherever possible.

Soft Clay

Medium Clay

Stiff Clay

Chapter 19

rho (ton/m3)

1.3

1.5

1.8

refShearModul (kPa) 1.3x104

6.0x104

1.5x105

refBulkModu (kPa)

6.5x104

3.0x105

7.5x105

cohesi (kPa)

18

37

75

peakShearStra

0.1

0.1

0.1

frictionAng

0

0

0

pressDependCoe

0

0

0

nDMaterial Command

187

Chapter 19

nDMaterial Command

188

Chapter 19

nDMaterial Command

189

updateMaterialStage
This command is used to update a PressureDependMultiYield, PressureDependMultiYield02,
PressureIndependMultiYield, or FluidSolidPorous material. To conduct a seismic analysis, two
stages should be followed. First, during the application of gravity load (and static loads if any), set
material stage to 0, and material behavior is linear elastic (with Gr and Br as elastic moduli). A
FluidSolidPorous material does not contribute to the material response if its stage is set to 0.
After the application of gravity load, set material stage to 1 or 2. In case of stage 2, all the elastic
material properties are then internally determined at the current effective confinement, and remain
constant thereafter. In the subsequent dynamic (fast) loading phase(s), the deviatoric stress-strain
response is elastic-plastic (stage 1) or linear-elastic (stage 2), and the volumetric response
remains linear-elastic. Please visit http://cyclic.ucsd.edu/opensees
(http://cyclic.ucsd.edu/opensees) for examples.

updateMaterialStage -material $tag -stage $sNum
$tag

Material number.

$sNum

desired stage:
0 - linear elastic,
1 – plastic,
2 - Linear elastic, with elasticity constants (shear modulus and bulk
modulus) as a function of initial effective confinement.

Chapter 19

nDMaterial Command

190

updateParameter
This command is used to update:
1. Parameters of PressureDependMultiYield or PressureIndependMultiYield material.
Currently, two material parameters, reference low-strain shear modulus Gr and reference bulk
modulus Br, can be modified during an analysis.
2. Permeability parameters of solid-fluid fully coupled elements including FourNodeQuadUP,
Nine_Four_Node_QuadUP, BrickUP, and Twenty_Eight_Node_BrickUP.
Please visit http://cyclic.ucsd.edu/opensees (http://cyclic.ucsd.edu/opensees) for examples.

updateParameter -material $tag -refG $newVal

updateParameter -material $tag -refB $newVal

updateParameter -element $tag -hPerm $newVal

updateParameter -element $tag -vPerm $newVal
$tag

Material/element number.

$newVal

New parameter value.

191

CHAPTER 20

section Command
This command is used to construct a SectionForceDeformation object, hereto referred to as
Section, which represents force-deformation (or resultant stress-strain) relationships at
beam-column and plate sample points.

 What is a section?

•

A section defines the stress resultant force-deformation response at a cross section of a
beam-column or plate element
Types of sections:
Elastic – defined by material and geometric constants

•
Resultant – general nonlinear description of force-deformation response, e.g.
moment-curvature
•
Fiber – section is discretized into smaller regions for which the material stress-strain
response is integrated to give resultant behavior, e.g. reinforced concrete

The valid queries to any section when creating an ElementRecorder (page 307) are 'force' and
'deformation.'

Chapter 20

section Command

192

Figure 35: Section Representation

In This Chapter
Elastic Section.......................................................... 192
Uniaxial Section........................................................ 193
Fiber Section ............................................................ 194
Section Aggregator................................................... 203
Elastic Membrane Plate Section............................... 205
Plate Fiber Section ................................................... 205
Bidirectional Section................................................. 206
Isolator2spring Section: Model to include buckling behavior of an
elastomeric bearing .................................................. 207

Elastic Section
This command is used to construct an ElasticSection object.

section Elastic $secTag $E $A $Iz <$Iy $G $J>
$secTag

unique section object tag

$E

Young's Modulus

$A

cross-sectional area of section

$Iz

second moment of area about the local z-axis

$Iy

second moment of area about the local y-axis (optional, used for
3D analysis)

$G

Shear Modulus (optional, used for 3D analysis)

$J

torsional moment of inertia of section (optional, used for 3D
analysis)

This command is useful for patch tests of the nonlinear beam-column elements (page 218). It also
allows nonlinear beam-column elements to be used for elastic analysis.

EXAMPLE:
section Elastic 1 29000 100 100000 80000 20000 100000;
IDtag 1

# create elastic section with

Chapter 20

section Command

193

Uniaxial Section
This command is used to construct a UniaxialSection object which uses a previously-defined
UniaxialMaterial (page 43) object to represent a single section force-deformation response
quantity. (Formerly known as Generic1d section, which is still accepted by OpenSees)

section Uniaxial $secTag $matTag $string
$secTag

unique section object tag

$matTag

previously-defined UniaxialMaterial (page 43) object

$string

the force-deformation quantity to be modeled by this section
object. One of the following strings is used:
P

Axial force-deformation

Mz

Moment-curvature about section local z-axis

Vy

Shear force-deformation along section local y-axis

My

Moment-curvature about section local y-axis

Vz

Shear force-deformation along section local z-axis

T

Torsion Force-Deformation

EXAMPLE:
section Uniaxial 1 1 Mz;
# create sectionID-tag 1 from UniaxialMaterialID-tag 1 for the
moment-curvature about section local z-axis.

Chapter 20

section Command

194

Fiber Section
The FiberSection object is composed of Fiber objects.
A fiber section has a general geometric configuration formed by subregions of simpler, regular
shapes (e.g. quadrilateral, circular and triangular regions) called patches. In addition, layers of
reinforcement bars can be specified. The subcommands patch (page 197) and layer (page 202,
page 201) are used to define the discretization of the section into fibers. Individual fibers, however,
can also be defined using the fiber (page 196) command (During generation, the Fiber objects are
associated with uniaxialMaterial (page 43) objects, which enforce Bernoulli beam assumptions.
The geometric parameters are defined with respect to a planar local coordinate system (y,z). See
figures.

section Fiber $secTag {
fiber <fiber arguments>
patch <patch arguments>
layer <layer arguments>
}

An example fiber section is shown in the Figure.

Chapter 20

Figure 36: Fiber Section

section Command

195

Chapter 20

section Command

196

Fiber Command
This command is used to construct a UniaxialFiber object and add it to the section.

fiber $yLoc $zLoc $A $matTag

$yLoc

y coordinate of the fiber in the section (local coordinate system)

$zLoc

z coordinate of the fiber in the section (local coordinate system)

$A

area of fiber

$matTag

material tag of the pre-defined UniaxialMaterial (page 43) object used
to represent the stress-strain for the area of the fiber

NOTE: in 2D (page 34) bending is about the local z-axis

EXAMPLE:
fiber 0.0 0.0 1.0 1;
materialIDtag 1

# create a single fiber of area 1.0 at the origin (0,0) of the section, using

Figure 37: Fiber Command

Chapter 20

section Command

197

Quadrilateral Patch Command
This command is used to construct a Patch object with a quadrilateral shape. The geometry of the
patch is defined by four vertices: I J K L, as illustrated in the Figure. The coordinates of each of the
four vertices is specified in sequence -- counter-clockwise.

patch quad $matTag $numSubdivIJ $numSubdivJK $yI $zI $yJ $zJ $yK $zK $yL
$zL
$matTag

material integer tag of the previously-defined UniaxialMaterial
(page 43) object used to represent the stress-strain for the area
of the fiber

$numSubdivIJ

number of subdivisions (fibers) in the IJ direction.

$numSubdivJK

number of subdivisions (fibers) in the JK direction.

$yI

$zI

y & z-coordinates of vertex I (local coordinate system)

$yJ

$zJ

y & z-coordinates of vertex J (local coordinate system)

$yK

$zK

y & z-coordinates of vertex K (local coordinate system)

$yL

$zL

y & z-coordinates of vertex L (local coordinate system)

Chapter 20

section Command

NOTE: in 2D (page 34) bending is about the local z-axis

EXAMPLE:
patch quad $coreMatTag 8 8 -$b -$h $b -$h $b $h -$b $h; # define core patch with 8
subdivisions within a rectange of width 2b and depth 2h

198

Chapter 20

section Command

Figure 38: Quadrilateral Patch

Circular Patch Command
This command is used to construct a Patch object with a circular shape.

patch circ $matTag $numSubdivCirc $numSubdivRad $yCenter $zCenter
$intRad $extRad <$startAng $endAng>
$matTag

material integer tag of the previously-defined UniaxialMaterial
(page 43) object used to represent the stress-strain for the
area of the fiber

$numSubdivCirc

number of subdivisions (fibers) in the circumferential direction.

$numSubdivRad

number of subdivisions (fibers) in the radial direction.

$yCenter

y & z-coordinates of the center of the circle

$zCenter

$intRad

internal radius

$extRad

external radius

$startAng

starting angle (optional. default=0.0)

$endAng

ending angle (optional. default=360.0)

NOTE: in 2D (page 34) bending is about the local z-axis

199

Chapter 20

section Command

200

EXAMPLE:
patch circ $coreMatTag 8 8 0.0 0.0 0.0 $h; # define core patch with 8 subdivisions within a
whole circle of diameter 2h

Chapter 20

section Command

201

Figure 39: Circular Patch

Straight Layer Command
This command is used to construct a straight layer of reinforcing bars.

layer straight $matTag $numBars $areaBar $yStart $zStart $yEnd $zEnd
$matTag

material integer tag of the previously-defined UniaxialMaterial
(page 43) object used to represent the stress-strain for the area
of the fiber

$numBars

number of reinforcing bars along layer

$areaBar

area of individual reinforcing bar

$yStart

$zStart

y and z-coordinates of starting point of reinforcing layer (local
coordinate system)

$yEnd

$zEnd

y and z-coordinates of ending point of reinforcing layer (local
coordinate system)

NOTE: in 2D (page 34) bending is about the local z-axis

EXAMPLE:
layer straight $steelMatTag 10 0.11 -b -h b -h; # define steel layer of 10 bars with area 0.11 at
bottom of section of width 2b by 2h

Figure 40: Straight Layer

Chapter 20

section Command

202

Circular Layer Command
This command is used to construct a circular layer of reinforcing bars.

layer circ $matTag $numBar $areaBar $yCenter $zCenter $radius <$startAng
$endAng>
$matTag

material integer tag of the previously-defined
UniaxialMaterial (page 43) object used to represent the
stress-strain for the area of the fiber

$numBar

number of reinforcing bars along layer

$areaBar

area of individual reinforcing bar

$yCenter

$zCenter

$radius
$startAng

y and z-coordinates of center of reinforcing layer (local
coordinate system)
radius of reinforcing layer

$endAng

starting and ending angle of reinforcing layer, respectively.
(Optional, Default: a full circle is assumed 0-360)

NOTE: in 2D (page 34) bending is about the local z-axis

EXAMPLE:
layer circ $steelMatTag 10 0.11 0.0 0.0 $h 0 360; # define circular steel layer of 10 bars with
area 0.11 uniformly distributed along circumference of circle of diameter 2h

Chapter 20

section Command

203

Figure 41: Circular Reinforcing Layer

Section Aggregator
This command is used to construct a SectionAggregator object which groups previously-defined
UniaxialMaterial (page 43) objects into a single section force-deformation model.

section Aggregator $secTag $matTag1 $string1 $matTag2 $string2 .......
<-section $sectionTag>
$secTag

unique section object integer tag

$matTag1,
$matTag2 ...

previously-defined UniaxialMaterial (page 43) objects

$string1, $string2
....

the force-deformation quantities corresponding to each section
object. One of the following strings is used:

<-section
$sectionTag>

P

Axial force-deformation

Mz

Moment-curvature about section local z-axis

Vy

Shear force-deformation along section local y-axis

My

Moment-curvature about section local y-axis

Vz

Shear force-deformation along section local z-axis

T

Torsion Force-Deformation
specifies a previously-defined Section (page 191) object
(identified by the argument $sectionTag) to which these
UniaxialMaterial (page 43) objects may be added to recursively
define a new Section (page 191) object

NOTE: The UniaxialMaterial (page 43) objects aggregated in this Section (page 191) object are
uncoupled from each other as well as from the Section (page 191) object represented by
$sectionTag, if present.

There are two main tasks that can be performed using the Section Aggregator:

Chapter 20

section Command

204

 1. Group previously defined uniaxial materials to describe stress resultant
section behavior

Figure 42: Section Aggregator 1
EXAMPLE:
section Aggregator 1 2 Vy 5 Mz; #create new section with IDtag 1, taking the existing material
tag 2 to represent the shear and the existing material tag 5 to represent the moment.

 2. Add to an existing section

Chapter 20

section Command

205

Figure 43: Section Aggregator 2

EXAMPLE:
section Aggregator 2 2 Vy -section 4; # create new section with IDtag 2, taking the existing
material tag 2 to represent the shear and adding it to the existing section tag 4, which may be a
fiber section where the interaction betweeen axial force and flexure is already considered.

Elastic Membrane Plate Section
This command is used to construct an ElasticMembranePlateSection object, which is an isotropic
section appropriate for plate and shell analysis.

section ElasticMembranePlateSection $secTag $E $nu $h $rho
$secTag

unique section object tag

$E

Elastic Modulus

$nu

Poisson's Ratio

$h

thickness of the plate section

$rho

mass density of the material (per unit volume)

Plate Fiber Section
The plate fiber section takes any plate fiber material (page 164) and, by thickness integration,
creates a plate section appropriate for shell analysis.

section PlateFiber $secTag $fiberTag $h
$secTag

unique section object tag for section being constructed

$fiberTag

material tag for a previously-defined plate fiber material (page
164)

Chapter 20

$h

section Command

206

thickness of the plate section

Bidirectional Section
This command is used to construct a Bidirectional section object which is the two-dimensional
generalization of a one-dimensional elasto-plastic model with linear hardening.

section Bidirectional $matTag $E $sigY $H_iso $H_kin
$matTag

unique section object integer tag

$E

Elastic Modulus

$sigY

yield stress

$H_iso

isotropic hardening Modulus

$H_kin

kinematic hardening Modulus

then why do we have kinematic and isotripic hardening parameters??????***********

Chapter 20

section Command

207

Isolator2spring Section: Model to include
buckling behavior of an elastomeric bearing
Author: Keri L. Ryan
Assistant Professor, Utah State University

Contact: http://www.engineering.usu.edu/cee/faculty/kryan/

This command is used to construct an Isolator2spring section object, which represents the
buckling behavior of an elastomeric bearing for two-dimensional analysis in the lateral and vertical
plane. An Isolator2spring section represents the resultant force-deformation behavior of the
bearing, and should be used with a zeroLengthSection element. The bearing should be
constrained against rotation.

section Iso2spring $matTag $tol $k1 $Fyo $k2o $kvo $hb $PE <$Po>

$matTag

unique section object integer tag

$tol

tolerance for convergence of the element state. Suggested
value: E-12 to E-10. OpenSees will warn if convergence is not
achieved, however this usually does not prevent global
convergence.

$k1

initial stiffness for lateral force-deformation

$Fyo

nominal yield strength for lateral force-deformation

$k2o

nominal postyield stiffness for lateral force-deformation

$kvo

nominal stiffness in the vertical direction

$hb

total height of elastomeric bearing

$PE

Euler Buckling load for the bearing

$Po

axial load at which nominal yield strength is achieved (optional,
default = 0.0, i.e. no strength degradation)

Chapter 20

section Command

208

Model Characteristic:
This material model is based on a two-spring mechanical model of an elastomeric bearing,
originally developed by Koh and Kelly [1987] (Figure 1). The model yields the approximate results
as predicted by stability analysis of a multi-layer bearing. The axial flexibility of the bearing is
modeled by an additional vertical spring in series (not shown in Figure 1). The original model
included only linear material behavior. The rotational stiffness is given by

where

is the Euler buckling load as a function of bending stiffness EIs and bearing height

hb. The nominal shear stiffness
and the vertical stiffness
, where G is
the shear modulus, Ec is the compression modulus, A is the cross-sectional area, and tr is the total
height of rubber. Ec and G can be related by the bearing shape factor S [Kelly 1997].

Chapter 20

section Command

209

Figure 1: Two-spring model of an isolation bearing in the undeformed and deformed configuration.

In this implementation, the linear shear spring has been replaced by a bilinear spring to
represent the nonlinear behavior observed in elastomeric and lead-rubber bearings [Ryan et. al
2005] (Figure 2). The nonlinear behavior is implemented by rate-independent plasticity with
kinematic hardening [Simo and Hughes 1998]. The behavior of the nonlinear spring is controlled
by the initial stiffness k1, yield strength Fyo, and postyield stiffness k2o.

Figure 2: Bilinear shear spring and parameters.
Also included is an optional variation of strength with axial load, to represent the inability of
lead-plug bearings to achieve their full strength when lightly loaded, as has been experimentally
observed. An empirical equation for the yield strength as a function of compressive load has been
developed from experimental data:

Chapter 20

section Command

210

where P is the compressive load on the bearing and Po is the axial load at which approximately
63% of the nominal strength is achieved (Figure 3). The bearing is assumed to have an acting
yield strength of zero in tension. If not specified, Po = 0, which means that the strength equals the
nominal yield strength and no strength degradation occurs.

Figure 3: Empirical model for yield strength degradation.
The equilibrium equations and kinematic constraints for the two-spring model form a system of five
nonlinear equations (below) which are solved by an internal iterative Newton algorithm (this is
iteration within the material object). The stiffness matrix is formed by taking differentials of the
equilibrium and kinematic equations. The return mapping algorithm is implemented at each
iteration to determine the state of the shear spring.

Chapter 20

section Command

211

Not defined previously, v is the deformation due to the vertical spring and ubv is the total vertical
deformation, including the geometric effect of tilting.
Analysis of the linear two-spring model leads to the following approximate coupled lateral
force-deformation and vertical force-deformation equations:

where

is the critical buckling load for

the bearing, and

That is, lateral stiffness decreases as the axial load on the bearing approaches the critical load,
and vertical flexibility increases in the laterally deformed configuration.

Example:
The following example demonstrates a simple cyclic lateral load test, and was used to produce the
lateral force deformation behavior shown in Figure 4 by variation of the parameters P/Pcr and
P/Po in the script file (page 212).

Chapter 20

section Command

212

Figure 4: Cyclic lateral force deformation behavior of a bearing as a function of axial load: (a)
postyield stiffness degrades as axial load P approaches the critical load Pcr, (b) yield strength
degrades as axial load decreases relative to Po.
References:
Ryan, Keri L., James M. Kelly and Anil K. Chopra (2005). “Nonlinear model for lead-rubber
bearings including axial-load effects” Journal of Engineering Mechanics, ASCE, 131(12).
Kelly, James M. (1997). Earthquake-Resistant Design with Rubber. Springer-Verlag.
Koh, C.-G. and Kelly, J. M. (1987). “Effects of axial load on elastomeric isolation bearings”, Rep.
No. UCB/EERC-86/12. Earthquake Engineering Research Center, University of California,
Berkeley.
Kelly, James M. (2003). “Tension buckling in multilayer elastomeric bearings”, Journal of
Engineering Mechanics, ASCE, 129(12):1363-1368.
Simo, J. C and T. J. R. Hughes (1998). Computational Inelasticity. New York, NY, Springer.

CyclicLoading_Iso2spring.tcl
# Test Example for ISOLATOR2SPRING material
# Written: K. Ryan
# Date: November 22, 2005
#
# Description: A Single DOF isolator supporting a rigid mass. Generates lateral force deformation through

Chapter 20

section Command

# application of a pseudo-static cyclic (sinusoidal) lateral force. Force deformation behavior varies
# as a function of the axial load P and normalized values of P/Pcr and P/Po
#
# Units: cm, dimensionless
set g 982.0
set PI [expr 2.0 * asin(1.0)]
# Define the model builder
model BasicBuilder -ndm 2 -ndf 3
# Assumed parameters which define system
# Period associated with second stiffness k2o
set Tb 2.5
# Normalized axial load parameter P/Pcr. Vary to produce data for Figure 4a
set PPcr 0.001
# Normalized axial load paramter P/Po. Vary to produce data for Figure 4b
set PPo 0.25
# Unit mass
set M 1.0
# Bearing shape factor
set S 20.0
# Yield displacement
set uy 1.0
# Strength coefficient (determines yield strength)
set mu 0.1
set tol 1.0e-10
# Parameters computed from the assumed ones
set wb [expr (2.0*$PI/$Tb)]
set k2o [expr $wb*$wb*$M]
set Fyo [expr $mu*$M*$g + $k2o*$uy]
set k1 [expr $Fyo/$uy]
set kvo [expr 6.0*$S*$S*$k2o]
set Pcr [expr $M*$g/$PPcr]
set Pe [expr 50.0*$Pcr]
set Ps [expr 1.0/50.0*$Pcr]
set hb [expr $Ps/$k2o]
set Po [expr $M*$g/$PPo]
# Define nodes
node 1 0.0 0.0
node 2 0.0 0.0
# Define single point constraints (Constrain the isolator against rotation)
fix 1 1 1 1
fix 2 0 0 1
# Create Iso2spring section
section Iso2spring 1 $tol $k1 $Fyo $k2o $kvo $hb $Pe $Po
#
id ndI ndJ mattag
element zeroLengthSection 1 1 2 1
# Apply gravity load on isolated mass
set P [expr $M*$g]
pattern Plain 1 "Linear" {
load 2 0.0 -[expr $P] 0.0
}
system BandSPD

213

Chapter 20

constraints Plain
numberer Plain
test EnergyIncr 1.0e-15 100
algorithm Newton
integrator LoadControl 0.1 1 0.1 0.1
analysis Static
initialize
analyze 10
loadConst -time 0.0
# Estimated postyield stiffness degradation
set k2oest [expr $k2o*(1.0-$PPcr*$PPcr)]
# Estimated yield strength degradation
set Fyoest [expr $Fyo*(1.0-exp(-$PPo))]
# Define amplitude of cyclic force to induce approx. 20 cm deformation
set Fu [expr $Fyoest + $k2oest*20.0]
# Apply sinusoidal lateral load
set SinePath "Trig 0.0 1.5 1.0"
pattern Plain 2 $SinePath {
load 2 $Fu 0.0 0.0
}
wipeAnalysis
recorder Node -file Node2.out -node 2 -dof 1 disp
recorder Element 1 -file Elem1.out force
system BandGeneral
constraints Plain
numberer Plain
test EnergyIncr 1.0e-15 100
algorithm Newton
integrator LoadControl 0.01 1 0.001 0.1
analysis Static
analyze 1500
print ele 1
print node 2

section Command

214

215

CHAPTER 21

element Command
This command is used to construct an Element object.

In This Chapter
Truss Element .......................................................... 215
Corotational Truss Element ...................................... 216
Elastic Beam Column Element ................................. 217
NonLinear Beam-Column Elements ......................... 218
Zero-Length Elements.............................................. 223
Quadrilateral Elements ............................................. 227
Brick Elements ......................................................... 230
BeamColumnJoint Element ...................................... 232
UC Davis Soil Elements ........................................... 256
UC San Diego Soil Elements.................................... 263

Truss Element
This command is used to construct a truss element object. There are two ways to construct a truss
element object:
One way is to specify an area and a UniaxialMaterial (page 43) identifier:

element truss $eleTag $iNode $jNode $A $matTag
the other is to specify a Section (page 191) identifier:

element truss $eleTag $iNode $jNode $secTag

$eleTag

unique element object tag

$iNode $jNode

end nodes

$A

cross-sectional area of element

$matTag

tag associated with previously-defined UniaxialMaterial (page
43)

Chapter 21

$secTag

element Command

216

tag associated with previously-defined Section (page 191)

When constructed with a UniaxialMaterial (page 43) object, the truss element considers strain-rate
effects, and is thus suitable for use as a damping element.
The valid queries to a truss element when creating an ElementRecorder (page 307) object are
'axialForce,' 'stiff,' deformations,' 'material matArg1 matArg2...,' 'section sectArg1 sectArg2...'
There will be more queries after the interface for the methods involved have been developed
further.

Corotational Truss Element
This command is used to construct a Corotational Truss (CorotTruss) element object. A
corotational formulation adopts a set of corotational axes which rotate with the element, thus
taking into account an exact geometric transformation between local and global frames of
reference.
There are two ways to construct a Corotational Truss element object:
One way is to specify an area and a UniaxialMaterial (page 43) identifier:

element corotTruss $eleTag $iNode $jNode $A $matTag
the other is to specify a Section (page 191) identifier:

element corotTruss $eleTag $iNode $jNode $secTag

$eleTag

unique element object tag

$iNode $jNode

end nodes

$A

cross-sectional area of element

$matTag

tag associated with previously-defined UniaxialMaterial (page
43) object

$secTag

tag associated with previously-defined Section (page 191) object

NOTE: When constructed with a UniaxialMaterial (page 43) object, the truss element considers
strain-rate effects, and is thus suitable for use as a damping element.
The valid queries to a corotational truss element when creating an ElementRecorder (page 307)
object are 'axialForce,' 'stiff,' 'material $matNum matArg1 matArg2...,' 'section $secNum sectArg1
sectArg2...'

Chapter 21

element Command

217

Elastic Beam Column Element
This command is used to construct an elasticBeamColumn element object. The arguments for the
construction of an elastic beam-column element depend on the dimension of the problem, ndm
(page 29):
For a two-dimensional problem:

element elasticBeamColumn $eleTag $iNode $jNode $A $E $Iz $transfTag
For a three-dimensional problem:

element elasticBeamColumn $eleTag $iNode $jNode $A $E $G $J $Iy $Iz
$transfTag

$eleTag
$iNode

unique element object tag
$jNode

end nodes

$A

cross-sectional area of element

$E

Young's Modulus

$G

Shear Modulus

$J

torsional moment of inertia of cross section

$Iz

second moment of area about the local z-axis

$Iy

second moment of area about the local y-axis

$transfTag

identifier for previously-defined coordinate-transformation (page
280) (CrdTransf) object

The valid queries to an elastic beam-column element when creating an ElementRecorder (page
307) object are 'stiffness' and 'force.'

Chapter 21

element Command

218

NonLinear Beam-Column Elements
There are basically two types of Nonlinear Beam-Column Elements

 Force based elements

Distributed plasticity (nonlinearBeamColumn (page 218))
Concentrated plasticity with elastic interior (beamWithHinges (page 219))

 Displacement based element

Distributed plasticity with linear curvature distribution (dispBeamColumn (page 223))

Nonlinear Beam Column Element
This command is used to construct a nonlinearBeamColumn element object, which is based on
the non-iterative (or iterative) force formulation, and considers the spread of plasticity along the
element.

element nonlinearBeamColumn $eleTag $iNode $jNode $numIntgrPts $secTag
$transfTag <-mass $massDens> <-iter $maxIters $tol>

$eleTag
$iNode

unique element object tag
$jNode

end nodes

$numIntgrPts

number of integration points along the element.

$secTag

identifier for previously-defined section (page 191) object

$transfTag

identifier for previously-defined coordinate-transformation (page
280) (CrdTransf) object

$massDens

element mass density (per unit length), from which a
lumped-mass matrix is formed (optional, default=0.0)

$maxIters

maximum number of iterations to undertake to satisfy element
compatibility (optional, default=1)

$tol

tolerance for satisfaction of element compatibility (optional,
default=10-16)

The integration along the element is based on Gauss-Lobatto quadrature rule (two integration
points at the element ends).

Chapter 21

element Command

219

The element is prismatic, i.e. the beam is represented by the section (page 191) model identified
by $secTag at each integration point.
The -iter switch enables the iterative form of the flexibility formulation. Note that the iterative form
can improve the rate of global convergence at the expense of more local element computation.
The valid queries to a nonlinear beam-column element when creating an ElementRecorder (page
307) object are 'force,' 'stiffness,' and 'section $secNum secArg1 secArg2...' Where $secNum
refers to the integration point whose data is to be output.
Useful references for this element are found in the References (page 443, http://www.) chapter.

Beam With Hinges Element
Contact Author:

Michael H. Scott
Oregon State University
http://web.engr.oregonstate.edu/~mhscott/

Reference:

Scott, M.H. and G.L. Fenves. "Plastic Hinge Integration Methods for Fo
of Structural Engineering, ASCE, 132(2):244-252, February 2006.

Chapter 21

element Command

220

This command is used to construct a beamWithHinges element object, which is based on the
non-iterative (or iterative) flexibility formulation, and considers plasticity to be concentrated over
specified hinge lengths at the element ends.
Note, the beamWithHinges element localize plastic hinging at the element ends only.
This type of element divides the element in three parts: two hinges at the ends, and a
linear-eleastic region in the middle. The hinges are defined by assigning to each a
previously-defined section. The length of the each hinge is also specified by the user:

While the integration of distributed-plasticity force-base elements distributes the gauss points
along the entire element length, the beamWithHinges element localizes the integration points in
the hinge regions. Two integration points per hinge are used to be able represent the curvature
distribution accurately -- Gauss-Radau Integration:

Chapter 21

element Command

221

Two integration points per hinge, however, require too much computational overhead. A Modified
Gauss-Radau Integration, developed by Scott et al., would apply the Gauss-Radau hinge
integration over 4Lp instead of Lp. Elastic properties are then applied to the interior integration
points, where a closed-form solution is used:

There are many advantages to this formulation over the other types of beamWithHinges:

Nonlinear behavior is confined to the integration points at the element ends.

The user only needs to specify the length of each hinge.

Captures largest bending moment at the ends.
Represents linear curvature distributions exactly.

Characteristic length is equal to Lp when deformations localize.

The arguments for the construction of the element depend on the dimension of the problem, ndm
(page 29).
For a two-dimensional problem:

element beamWithHinges $eleTag $iNode $jNode $secTagI $Lpi $secTagJ $Lpj
$E $A $Iz $transfTag <-mass $massDens> <-iter $maxIters $tol>
For a three-dimensional problem:

element beamWithHinges $eleTag $iNode $jNode $secTagI $Lpi $secTagJ $Lpj
$E $A $Iz $Iy $G $J $transfTag <-mass $massDens> <-iter $maxIters
$tol>

$eleTag
$iNode

unique element object tag
$jNode

end nodes

Chapter 21

element Command

$secTagI

identifier for previously-defined section (page 191) object
corresponding to node i

$Lpi

hinge length at node i

$secTagJ

identifier for previously-defined section (page 191) object
corresponding to node j

$Lpj

hinge length at node j

$E

Young's Modulus

$A

area of element cross-section

$Iz

section moment of inertia about the section local z-axis

$Iy

section moment of inertia about the section local y-axis

$G

Shear Modulus

$J

torsional moment of inertia of cross section

$transfTag

identifier for previously-defined coordinate-transformation (page
280) (CrdTransf) object

$massDens

element mass density (per unit length), from which a
lumped-mass matrix is formed (optional, default=0.0)

$maxIters

maximum number of iterations to undertake to satisfy element
compatibility (optional, default=1)

$tol

tolerance for satisfaction of element compatibility (optional,
default=10-16)

222

The -iter switch enables the iterative form of the flexibility formulation. Note that the iterative form
can improve the rate of global convergence at the expense of more local element computation.
NOTE: The elastic properties are integrated only over the beam interior, which is considered to be
linear-elastic.
The valid queries to a beamWithHinges element when creating an ElementRecorder (page 307)
object are 'force,' 'stiffness,' 'rotation' (hinge rotation), or 'section $secNum secArg1 secArg2...'
Where $secNum refers to the integration point whose data is to be output.
NOTE: The beamWithHinges element used here has four elastic sections and two fiber section at
the end. Therefore for output in specifying $secNum:
$secNum=1: hinge at node i
$secNum=6: hinge at node j

Chapter 21

element Command

223

Displacement-Based Beam-Column Element
This command is used to construct a dispBeamColumn element object, which is a
distributed-plasticity, displacement-based beam-column element.

element dispBeamColumn $eleTag $iNode $jNode $numIntgrPts $secTag
$transfTag <-mass $massDens>
$eleTag
$iNode

unique element object tag
$jNode

end nodes

$numIntgrPts

number of integration points along the element.

$secTag

identifier for previously-defined section (page 191) object

$transfTag

identifier for previously-defined coordinate-transformation (page
280) (CrdTransf) object

$massDens

element mass density (per unit length), from which a
lumped-mass matrix is formed (optional, default=0.0)

The integration along the element is based on the Gauss-Legendre quadrature rule (REF???).
The element is prismatic, i.e. the beam is represented by the section model identified by $secTag
at each integration point.
The valid queries to a displacement-based beam-column element when creating an
ElementRecorder (page 307) object are 'force,' 'stiffness,' and 'section $secNum secArg1
secArg2...' Where $secNum refers to the integration point whose data is to be output.

Zero-Length Elements
Zero-length elements connect two points at the same coordinate.

Chapter 21

element Command

224

Zero-Length Element
This command is used to construct a zeroLength element object, which is defined by two nodes at
the same location. The nodes are connected by multiple UniaxialMaterial (page 43) objects to
represent the force-deformation relationship for the element.

element zeroLength $eleTag $iNode $jNode -mat $matTag1 $matTag2 ... -dir
$dir1 $dir2 ... <-orient $x1 $x2 $x3 $yp1 $yp2 $yp3>
$eleTag
$iNode

unique element object tag
$jNode

end nodes

$matTag1
$matTag2 ...

tags associated with previously-defined UniaxialMaterials (page
43)

$dir1 $dir2 ...

material directions:
1,2,3

translation along local x,y,z axes, respectively

4,5,6

rotation about local x,y,z axes, respectively

the orientation vectors can be specified for the element (optional):
$x1 $x2 $x3

vector components in global coordinates defining local x-axis
(vector x)

$yp1 $yp2 $yp3

vector components in global coordinates defining vector yp which
lies in the local x-y plane for the element:
the local z-axis is defined by the cross product
between the vectors x and yp

If the optional orientation vectors are not specified, the local element axes coincide with the global
axes.
The valid queries to a zero-length element when creating an ElementRecorder (page 307) object
are 'force,' 'deformation,' 'stiff,' and 'material $matNum matArg1 matArg2 ...' Where $matNum is
the tag associated with the material whose data is to be output.

Chapter 21

element Command

225

Zero-Length ND Element
This command is used to construct a zeroLengthND element object, which is defined by two
nodes at the same location. The nodes are connected by a single NDMaterial (page 162) object to
represent the force-deformation relationship for the element.

element zeroLengthND $eleTag $iNode $jNode $matTag <$uniTag> <-orient $x1
$x2 $x3 $yp1 $yp2 $yp3>
$eleTag
$iNode

unique element object tag
$jNode

end nodes

$matTag

tag associated with previously-defined NDMaterial (page 162)
object

$uniTag

tag associated with previously-defined UniaxialMaterial (page
43) object which may be used to represent uncoupled behavior
orthogonal to the plane of the NDmaterial response.
If the NDMaterial (page 162) object is of order two, the response
lies in the element local x-y plane and the UniaxialMaterial object
may be used to represent the uncoupled behavior orthogonal to
this plane, i.e. along the local z-axis.
If the NDMaterial (page 162) object is of order three, the
response is along each of the element local exes.

the orientation vectors can be specified for the element (optional):
$x1 $x2 $x3

vector components in global coordinates defining local x-axis
(vector x)

$yp1 $yp2 $yp3

vector components in global coordinates defining vector yp which
lies in the local x-y plane for the element:
the local z-axis is defined by the cross product
between the vectors x and yp

If the optional orientation vectors are not specified, the local element axes coincide with the global
axes.
NOTE: The zeroLengthND element only represents translational response between its nodes
The valid queries to a zero-length element when creating an ElementRecorder (page 307) object
are 'force,' 'deformation,' 'stiffness,' and 'material matArg1 matArg2 ...'

Chapter 21

element Command

226

Zero-Length Section Element
This command is used to construct a zeroLengthSection element object, which is defined by two
nodes at the same location. The nodes are connected by a single SectionForceDeformation (page
191) object to represent the force-deformation relationship for the element.

element zeroLengthSection $eleTag $iNode $jNode $secTag <-orient $x1 $x2
$x3 $yp1 $yp2 $yp3>
$eleTag
$iNode

unique element object tag
$jNode

$secTag

end nodes
tag associated with previously-defined Section (page 191) object

the orientation vectors can be specified for the element (optional):
$x1 $x2 $x3

vector components in global coordinates defining local x-axis
(vector x)

$yp1 $yp2 $yp3

vector components in global coordinates defining vector yp which
lies in the local x-y plane for the element:
the local z-axis is defined by the cross product
between the vectors x and yp

If the optional orientation vectors are not specified, the local element axes coincide with the global
axes.
The section (page 191) force-deformation response represented by section string P acts along the
element local x-axis, and the response for code Vy along the local y-axis. The other modes of
section response follow from this orientation.
The valid queries to a zero-length element when creating an ElementRecorder (page 307) object
are 'force,' 'deformation,' 'stiffness,' and 'section secArg1 secArg2 ....'
NOTE: the ZeroLength section element only has 1 section therefore you do not need to identify
the section in the recorder command .. Example:
recorder Element -file Element1.out -time -ele 1 section fiber 0.10 0.10 stressStrain

Chapter 21

element Command

227

Quadrilateral Elements
Quad Element
This command is used to construct a FourNodeQuad element object which uses a bilinear
isoparametric formulation.

element quad $eleTag $iNode $jNode $kNode $lNode $thick $type $matTag
<$pressure $rho $b1 $b2>
$eleTag

unique element object tag

$iNode $jNode
$kNode $lNode

four nodes defining element boundaries, input in
counter-clockwise order around the element.

$thick

element thickness (constant)

$type

string representing material behavior.
Valid options depend on the NDMaterial (page 162) object and its
available material formulations. The type parameter can be either
"PlaneStrain" or "PlaneStress."

$matTag

tag associated with previously-defined NDMaterial (page 162)
object

$pressure

surface pressure (???? sign convention????****)

$rho

element mass density (per unit volume) from which a lumped
element mass matrix is computed (optional, default=0.0)

$b1 $b2

constant body forces defined in the isoparametric domain
(optional, default=0.0)

Consistent nodal loads are computed from the pressure and body forces.
The valid queries to a Quad element when creating an ElementRecorder (page 307) object are
'force,' 'stiffness,' and 'material $matNum matArg1 matArg2 ...' Where $matNum refers to the
material object at the integration point corresponding to the node numbers in the isoparametric
domain.

Chapter 21

element Command

228

Shell Element
This command is used to construct a ShellMITC4 element object, which uses a bilinear
isoparametric formulation in combination with a modified shear interpolation to improve thin-plate
bending performance.

element ShellMITC4 $eleTag $iNode $jNode $kNode $lNode $secTag

$eleTag

unique element object tag

$iNode $jNode
$kNode $lNode

four nodes defining element boundaries, input in
counter-clockwise order around the element.

$secTag

tag associated with previously-defined
SectionForceDeformation (page 191) object.
Typically, corresponds to some PlateFiberSection (page 205),
elastic or otherwise

Should the element be required to compute a mass matrix, a consistent translational element
mass matrix is computed. Rotational-inertia terms are ignored.
The valid queries to a shell element when creating an ElementRecorder (page 307) object are
'force,' 'stiffness,' and 'material matArg1 matArg2 ...'

Bbar Plane Strain Quadrilateral Element
This command is used to construct a four-node quadrilateral element object, which uses a bilinear
isoparametric formulation along with a mixed volume/pressure B-bar assumption. This element is
for plane strain problems only.

element bbarQuad $eleTag $iNode $jNode $kNode $lNode $matTag

$eleTag

unique element object tag

$iNode $jNode
$kNode $lNode

four nodes defining element boundaries, input in
counter-clockwise order around the element

$matTag

tag associated with previously-defined NDMaterial (page 162)
object

Chapter 21

element Command

229

Should the element be required to compute a mass matrix, a consistent translational element
mass matrix is computed. Rotational-inertia terms are ignored.

Enhanced Strain Quadrilateral Element
This command is used to construct a four-node quadrilateral element, which uses a bilinear
isoparametric formulation with enhanced strain modes.

element enhancedQuad $eleTag $iNode $jNode $kNode $lNode type $matTag

$eleTag

unique element object tag

$iNode $jNode
$kNode $lNode

four nodes defining element boundaries, input in
counter-clockwise order around the element.

type

string representing material behavior.
Valid options depend on the NDMaterial (page 162) object and its
available material formulations. The type parameter can be either
"PlaneStrain" or "PlaneStress."

$matTag

tag associated with previously-defined NDMaterial (page 162)
object

Should the element be required to compute a mass matrix, a consistent translational element
mass matrix is computed. Rotational-inertia terms are ignored.
The valid queries to a zero-length element when creating an ElementRecorder (page 307) object
are 'force,' 'stiffness,' and 'material matArg1 matArg2 ...'

Chapter 21

element Command

230

Brick Elements
Standard Brick Element
This element is used to construct an eight-node brick element object, which uses a trilinear
isoparametric formulation.

element stdBrick $eleTag $node1 $node2 $node3 $node4 $node5 $node6
$node7 $node8 $matTag
$eleTag

unique element object tag

$node1 $node2
$node3 $node4
$node5 $node6
$node7 $node8

eight nodes defining element boundaries, input order is shown in
the figure

$matTag

tag associated with previously-defined NDMaterial (page 162)
object

Should the element be required to compute a mass matrix, a consistent translational element
mass matrix is computed. Rotational-inertia terms are ignored.

Chapter 21

element Command

231

Figure 44: Node-Numbering for Standard Brick Element
Note: Node numbering for this element is different from that for the eight-node brick (page 259)
(Brick8N) element.

Bbar Brick Element
This command is used to construct an eight-node mixed volume/pressure brick element object,
which uses a trilinear isoparametric formulation.

element bbarBrick $eleTag $node1 $node2 $node3 $node4 $node5 $node6
$node7 $node8 $matTag
$eleTag

unique element object tag

$node1 $node2
$node3 $node4
$node5 $node6
$node7 $node8

eight nodes defining element boundaries, input order is shown in
the figure

$matTag

tag associated with previously-defined NDMaterial (page 162)
object

Should the element be required to compute a mass matrix, a consistent translational element
mass matrix is computed. Rotational-inertia terms are ignored

Figure 45: Node Numbering for Eight-Node Three-Dimensional Element

Chapter 21

element Command

232

BeamColumnJoint Element
This command is used to construct a two-dimensional beam-column-joint element object. The
element may be used with both two-dimensional and three-dimensional structures; however, load
is transferred only in the plane of the element.

element beamColumnJoint $eleTag $Nd1 $Nd2 $Nd3 $Nd4 $Mat1 $Mat2 $Mat3
$Mat4 $Mat5 $Mat6 $Mat7 $Mat8 $Mat9 $Mat10 $Mat11 $Mat12 $Mat13
<$eleHeightFac $eleWidthFac>

$eleTag

an integer identifying the element tag in the domain

$Nd1,$Nd2,$Nd3,$
Nd4

tag associated with previously defined nodes

$Mat1

uniaxial material tag for left bar-slip spring at node 1

$Mat2

uniaxial material tag for right bar-slip spring at node 1

$Mat3

uniaxial material tag for interface-shear spring at node 1

$Mat4

uniaxial material tag for lower bar-slip spring at node 2

$Mat5

uniaxial material tag for upper bar-slip spring at node 2

$Mat6

uniaxial material tag for interface-shear spring at node 2

$Mat7

uniaxial material tag for left bar-slip spring at node 3

$Mat8

uniaxial material tag for right bar-slip spring at node 3

$Mat9

uniaxial material tag for interface-shear spring at node 3

$Mat10

uniaxial material tag for lower bar-slip spring at node 4

$Mat11

uniaxial material tag for upper bar-slip spring at node 4

$Mat12

uniaxial material tag for interface-shear spring at node 4

$Mat13

uniaxial material tag for shear-panel

$eleHeightFac

floating point value (as a ratio to the total height of the element) to
be considered for determination of the distance in between the
tension-compression couples (optional, default: 1.0)

$eleWidthFac

floating point value (as a ratio to the total width of the element) to
be considered for determination of the distance in between the
tension-compression couples (optional, default: 1.0)

Chapter 21

element Command

233

NOTE:

Node 3

external node

Node 4

shear panel

bar-slip
spring (typ.)

Node 2

internal node
Node 1

interface-shear
spring (typ.)

Chapter 21

element Command

234

Figure 46: BeamColumnJoint Element
The valid queries to a BeamColumnJoint element when creating an ElementRecorder (page 307)
are as follows:
‘internalDisplacement’

- returns the displacements of the internal joint nodes.

‘externalDisplacement’

- returns the displacement of the external joint nodes.

‘deformation’ - generates a four-column matrix in which the first column is the contribution to the
total joint shear deformation of all of the bar-slip components of the joint, the second is the
deformation contribution of the interface shear springs, the third is the deformation contribution of
the shear-panel and the fourth is the total shear deformation of the joint.
‘node1BarSlipL’
Left at node 1.

- returns the load-deformation response history of the Bar-Slip spring on the

‘node1BarSlipR’
Right at node 1.

- returns the load-deformation response history of the Bar-Slip spring on the

‘node1InterfaceShear’- returns the load-deformation response history of the Interface-Shear
spring at node 1.
‘node2BarSlipB’
Bottom at node 2.

- returns the load-deformation response history of the Bar-Slip spring on the

‘node2BarSlipT’
Top at node 2.

- returns the load-deformation response history of the Bar-Slip spring on the

‘node2InterfaceShear’- returns the load-deformation response history of the Interface Shear
spring at node 1.
’node3BarSlipL’
Left at node 3.

- returns the load-deformation response history of the Bar-Slip spring on the

‘node3BarSlipR’
Right at node 3.

- returns the load-deformation response history of the Bar-Slip spring on the

‘node3InterfaceShear’- returns the load-deformation response history of the Interface-Shear
spring at node 3.
‘node4BarSlipB’
Bottom at node 4.

- returns the load-deformation response history of the Bar-Slip spring on the

‘node4BarSlipT’
Top at node 4.

- returns the load-deformation response history of the Bar-Slip spring on the

‘node4InterfaceShear’- returns the load-deformation response history of the Interface Shear
spring at node 4.

Chapter 21

‘shearPanel’

element Command

235

- returns the load-deformation response history of the Shear-Panel spring.

 EXAMPLE:
main input file:

PR1.tcl (page 240)

supporting files:

procMKPC.tcl (page 250)

procUniaxialPinching.tcl (page 101)

procRC.tcl (page 252)

References:
Lowes, Laura N.; Mitra, Nilanjan; Altoontash, Arash A beam-column joint model for simulating the
earthquake response of reinforced concrete frames PEER-2003/10
(http://nisee.berkeley.edu/elibrary/getdoc?id=1288878) Pacific Earthquake Engineering
Research Center, University of California, Berkeley 2003 59 pages (400/P33/2003-10)

Chapter 21

Beam-Column Joint Element Discussion

236

Beam-Column Joint Element Discussion

Beam-Column Joint Element
Discussion
The example files (PR1.tcl (page 240), procMKPC.tcl (page 250), procUniaxialPinching.tcl (page
101), procRC.tcl (page 252)) create a model of a RC beam column sub-assemblage (Figure 1).
The cruciform is subjected to constant gravity load at nodes 4 and 7 and pseudo-static cyclic
lateral load under displacement control at node 10. The beam-column-joint region (element
number 7) is represented using a beamColumnJoint element (Figure 2), and the beams and
columns (element numbers 1 through 6) are modeled using the nonlinearBeamColumn element.
The beam-column joint consists of 13 components that may have different material constitutive
models; in this example 9 of the 13 components utilize the nonlinear material model – Pinching4.
Figure 3 shows the displacement history for node 10.

Chapter 21

Figure 47: Cruciform model
Figure 1: Cruciform model

Figure 48: Beam Column Joint Element
Figure 2: Beam Column Joint Element

Beam-Column Joint Element Discussion

237

Chapter 21

Beam-Column Joint Element Discussion

238

Figure 49: Displacement history for Node 10
Figure 3: Displacement history for Node 10

Tcl Scripts:
The following tcl script files are used to run the examples:
PR1.tcl (page 240)
procMKPC.tcl (page 250)
procUniaxialPinching.tcl (page 101)
procRC.tcl (page 252)
The p-delta response of cruciform, along with the response of each of the nonlinear joint
components is shown below. The shear panel response shows the moment-curvature
relationships whereas the bar slips at the beam top and bottom are represented by the force-slip
plots (Figure 4).

Chapter 21

Beam-Column Joint Element Discussion

239

Chapter 21

Beam-Column Joint Element Discussion

Figure 50: Nonlinear Joint component response
Figure 4: Nonlinear Joint component response

Figure 51: P-delta response of the cruciform

Figure 5. P-delta response of the cruciform

PR1.tcl
############################################################################
# Test example for BEAM COLUMN ELEMENT JOINT ------- PARK RUITONG TEST SPECIMEN Unit 1
# Written: N.Mitra
# Description: 4 noded 12 dof element having 12 springs and a shear panel
# Date: Feb 16 2003
## Model consisting of a crucifix with beams and columns and a joint
## File Name: PR1.tcl
# refer to Beam-Column-Joint Element.doc for full explanation of the parameters
################################################################################

240

Chapter 21

Beam-Column Joint Element Discussion

241

#create the ModelBuilder object
model BasicBuilder -ndm 2 -ndf 3

## unit name ---- PR1
set fName "PR1";

source procMKPC.tcl
source procUniaxialPinching.tcl
source procRC.tcl

# all dimensions are in here as MPa (conversion factors are required in certain places)
set Strfactor 145; set Lenfactor [expr 1/25.4];

## Y taken as the inplane dim. against which the bending takes place
set colY 406; set colZ 305;
set bmY 457; set bmZ 229;

# covers
set colCov 43; set bmCov1 42; set bmCov2 33; set bmCov $bmCov1;

# y,z,x dimension of the joint respectively
set JointWidth [expr $colY]; set JointHeight [expr $bmY]; set JointDepth $colZ ;
set BeamLengthIn 645; set BeamLengthOut 1271; set ColumnLengthClear 1008;

set JointVolume [expr $JointWidth*$JointHeight*$JointDepth];

############################################################
################# material properties of column section
############################################################
set CUnconfFc -45.9; set CUnconfEc -0.002;
set CTSspace 60; set CTSlength 1853.53; set CTSFy 282; set CTSarea 28.3;
set CFy 498.0; set CEs 196600.0; set CsHratio 0.004216; set CAs 201.06;

procMKPC $CUnconfFc $CUnconfEc $colY $colZ $colCov $CTSspace $CTSlength $CTSFy $CTSarea $Strfactor
$Lenfactor

set CUnconfFcu [lindex $concreteProp 2]; set CUnconfEcu [lindex $concreteProp 3];
set CConfFc [lindex $concreteProp 4]; set CConfEc [lindex $concreteProp 5];

Chapter 21

Beam-Column Joint Element Discussion

242

set CConfFcu [lindex $concreteProp 6]; set CConfEcu [lindex $concreteProp 7];

#########################################################
########################### material properties of beam section
#####################################################
set BUnconfFc -45.9; set BUnconfEc -0.002;
set BTSspace 80; set BTSlength 1036; set BTSFy 282; set BTSarea 28.3;
set BFy 294.0; set BEs 210400.0; set BAs 201.06; set BsHratio 0.002322;

procMKPC $BUnconfFc $BUnconfEc $bmY $bmZ $bmCov $BTSspace $BTSlength $BTSFy $BTSarea $Strfactor
$Lenfactor

set BUnconfFcu [lindex $concreteProp 2]; set BUnconfEcu [lindex $concreteProp 3];
set BConfFc [lindex $concreteProp 4]; set BConfEc [lindex $concreteProp 5];
set BConfFcu [lindex $concreteProp 6]; set BConfEcu [lindex $concreteProp 7];

####################################################################
######################### details for the material models of bar slip of the beam
####################################
set bs_fc [expr -$BUnconfFc]; set bs_fs $BFy; set bs_es $BEs; set bs_fsu 434; set bs_dbar 16; set bs_esh [expr
$BsHratio*$BEs];
set bs_wid $colZ; set bs_dep $bmY;
set bsT_nbars 5; set bsB_nbars 2;
set bs_ljoint $colY;

################################################################################
########################## details for the material models of bar slip of the column
##################################
set cs_fc [expr -$CUnconfFc]; set cs_fs $CFy; set cs_es $CEs; set cs_fsu 660; set cs_dbar 16; set cs_esh [expr
$CsHratio*$CEs];
set cs_wid $colZ; set cs_dep $colY;
set cs_nbars 3;
set cs_ljoint $bmY;

#####################################################################
############### add nodes - command: node nodeId xCrd yCrd
#######################################################
node 1 0.0

0.0

node 2 0.0

$ColumnLengthClear

node 3 [expr -$BeamLengthOut-$BeamLengthIn-$JointWidth/2]

[expr $ColumnLengthClear+$JointHeight/2]

Chapter 21

node 4 [expr -$BeamLengthIn-$JointWidth/2]

Beam-Column Joint Element Discussion

[expr $ColumnLengthClear+$JointHeight/2]

node 5 [expr -$JointWidth/2]

[expr $ColumnLengthClear+$JointHeight/2]

node 6 [expr $JointWidth/2]

[expr $ColumnLengthClear+$JointHeight/2]

node 7 [expr $BeamLengthIn+$JointWidth/2]

243

[expr $ColumnLengthClear+$JointHeight/2]

node 8 [expr $BeamLengthOut+$BeamLengthIn+$JointWidth/2]

[expr $ColumnLengthClear+$JointHeight/2]

node 9 0.0

[expr $ColumnLengthClear+$JointHeight]

node 10 0.0

[expr 2*$ColumnLengthClear+$JointHeight]

# add material Properties - command: uniaxialMaterial matType matTag ...
#command: uniaxialMaterial Elastic tag? E?
uniaxialMaterial Elastic 1 10000000000.0

#####################################################################
############## inelastic beam column elements
##########################################################
uniaxialMaterial Concrete01 10 $BUnconfFc $BUnconfEc $BUnconfFcu $BUnconfEcu

uniaxialMaterial Concrete01 20 $BConfFc $BConfEc $BConfFcu $BConfEcu

uniaxialMaterial Steel02 30 $BFy $BEs $BsHratio 18.5 0.925 0.15 0.0 0.4 0.0 0.5

uniaxialMaterial Concrete01 40 $CUnconfFc $CUnconfEc $CUnconfFcu $CUnconfEcu

uniaxialMaterial Concrete01 50 $CConfFc $CConfEc $CConfFcu $CConfEcu

uniaxialMaterial Steel02 60 $CFy $CEs $CsHratio 18.5 0.925 0.15 0.0 0.4 0.0 0.5

########### for columns ///////////////////////////////////////////////////////////////////////
set z [expr $colZ/2.0]; set y [expr $colY/2.0];

section Fiber 1 {
patch rect 50 8 1

[expr $colCov-$y]

[expr $colCov-$z] [expr $y-$colCov]

patch rect 40 2 1

[expr -$y]

patch rect 40 2 1

[expr $y-$colCov]

patch rect 40 8 1

[expr -$y]

[expr -$z]

patch rect 40 8 1

[expr -$y]

[expr $z-$colCov] [expr $y]

[expr $z-$colCov]

[expr $colCov-$z] [expr $colCov-$y]

[expr $z-$colCov]

[expr $colCov-$z] [expr $y]

[expr $z-$colCov]

[expr $y]

[expr $colCov-$z]
[expr $z]

Chapter 21

layer straight 60 3 $CAs

[expr $y-$colCov]

layer straight 60 2 $CAs

0.0

layer straight 60 3 $CAs

[expr $colCov-$y]

Beam-Column Joint Element Discussion

[expr $colCov-$z] [expr $y-$colCov]
[expr $colCov-$z] 0.0

244

[expr $z-$colCov]

[expr $z-$colCov]

[expr $colCov-$z] [expr $colCov-$y]

[expr $z-$colCov]

}

#################### for beams ///////////////////////////////////////////////////////////////////
set z [expr $bmZ/2.0]; set y [expr $bmY/2.0];

section Fiber 2 {
patch rect 20 8 1

[expr $bmCov1-$y]

[expr $bmCov1-$z]

patch rect 10 2 1

[expr -$y]

patch rect 10 2 1

[expr $y-$bmCov1]

patch rect 10 8 1

[expr -$y]

[expr -$z]

patch rect 10 8 1

[expr -$y]

[expr $z-$bmCov1]

[expr $bmCov1-$z]

[expr $bmCov1-$y]

[expr $bmCov1-$z]

layer straight 30 3 $BAs [expr $y-$bmCov1]

[expr $y]

[expr $y]

}

##############/////////////////////////////////////////////////////////////////////////////////////

## add geometric transformation -command: geomTransf transfType ...

## geomTransf Linear tag?
geomTransf Linear 1
geomTransf Linear 2

element nonlinearBeamColumn 1 1 2 5 1 2
element nonlinearBeamColumn 2 9 10 5 1 2
element nonlinearBeamColumn 3 3 4 3 2 1
element nonlinearBeamColumn 4 4 5 2 2 1
element nonlinearBeamColumn 5 6 7 2 2 1
element nonlinearBeamColumn 6 7 8 3 2 1

[expr $z-$bmCov1]

[expr $z-$bmCov1]

[expr $z]

[expr $y-$bmCov1]

[expr $bmCov1-$z]

[expr $bmCov1-$z]

[expr $z-$bmCov1]

[expr $bmCov1-$z]

[expr $y]

[expr $bmCov1-$z]

layer straight 30 2 $BAs [expr $y-$bmCov1-$bmCov2]
$z - $bmCov1]
layer straight 30 2 $BAs [expr $bmCov1-$y]

[expr $y-$bmCov1]

[expr $z - $bmCov1]

[expr $y-$bmCov1-$bmCov2]

[expr $bmCov1-$y]

[expr

[expr $z - $bmCov1]

Chapter 21

Beam-Column Joint Element Discussion

245

##### end element formation as well as material defination for beams and columns ######################
##########################################################################################

# for beam bottom
set matID1 21
set matID2 22

uniaxialMaterial BarSlip $matID1 $bs_fc $bs_fs $bs_es $bs_fsu $bs_esh $bs_dbar $bs_ljoint $bsB_nbars $bs_wid
$bs_dep strong beamBot
uniaxialMaterial BarSlip $matID2 $bs_fc $bs_fs $bs_es $bs_fsu $bs_esh $bs_dbar $bs_ljoint $bsB_nbars $bs_wid
$bs_dep strong beamBot

## %%%%%%%%%%%%%%% equivalent statement can be made in other way
#uniaxialMaterial BarSlip $matID1 $bs_fc $bs_fs $bs_es $bs_fsu $bs_esh $bs_dbar $bs_ljoint $bsB_nbars $bs_wid
$bs_dep 1.0 strong beamBot damage
#uniaxialMaterial BarSlip $matID2 $bs_fc $bs_fs $bs_es $bs_fsu $bs_esh $bs_dbar $bs_ljoint $bsB_nbars $bs_wid
$bs_dep 1.0 strong beamBot damage

# for beam top
set matID3 31
set matID4 32

uniaxialMaterial BarSlip $matID3 $bs_fc $bs_fs $bs_es $bs_fsu $bs_esh $bs_dbar $bs_ljoint $bsT_nbars $bs_wid
$bs_dep strong beamTop
uniaxialMaterial BarSlip $matID4 $bs_fc $bs_fs $bs_es $bs_fsu $bs_esh $bs_dbar $bs_ljoint $bsT_nbars $bs_wid
$bs_dep strong beamTop

## %%%%%%%%%%%%%%% equivalent statement can be made in other way
#uniaxialMaterial BarSlip $matID3 $bs_fc $bs_fs $bs_es $bs_fsu $bs_esh $bs_dbar $bs_ljoint $bsT_nbars $bs_wid
$bs_dep 1.0 strong beamTop damage
#uniaxialMaterial BarSlip $matID4 $bs_fc $bs_fs $bs_es $bs_fsu $bs_esh $bs_dbar $bs_ljoint $bsT_nbars $bs_wid
$bs_dep 1.0 strong beamTop damage

# for columns
set matID5 41
set matID6 42
set matID7 43
set matID8 44

Chapter 21

Beam-Column Joint Element Discussion

246

uniaxialMaterial BarSlip $matID5 $cs_fc $cs_fs $cs_es $cs_fsu $cs_esh $cs_dbar $cs_ljoint $cs_nbars $cs_wid
$cs_dep strong column
uniaxialMaterial BarSlip $matID6 $cs_fc $cs_fs $cs_es $cs_fsu $cs_esh $cs_dbar $cs_ljoint $cs_nbars $cs_wid
$cs_dep strong column
uniaxialMaterial BarSlip $matID7 $cs_fc $cs_fs $cs_es $cs_fsu $cs_esh $cs_dbar $cs_ljoint $cs_nbars $cs_wid
$cs_dep strong column
uniaxialMaterial BarSlip $matID8 $cs_fc $cs_fs $cs_es $cs_fsu $cs_esh $cs_dbar $cs_ljoint $cs_nbars $cs_wid
$cs_dep strong column

## %%%%%%%%%%%%%%% equivalent statement can be made in other way
#uniaxialMaterial BarSlip $matID5 $cs_fc $cs_fs $cs_es $cs_fsu $cs_esh $cs_dbar $cs_ljoint $cs_nbars $cs_wid
$cs_dep 1.0 strong column damage
#uniaxialMaterial BarSlip $matID6 $cs_fc $cs_fs $cs_es $cs_fsu $cs_esh $cs_dbar $cs_ljoint $cs_nbars $cs_wid
$cs_dep 1.0 strong column damage
#uniaxialMaterial BarSlip $matID7 $cs_fc $cs_fs $cs_es $cs_fsu $cs_esh $cs_dbar $cs_ljoint $cs_nbars $cs_wid
$cs_dep 1.0 strong column damage
#uniaxialMaterial BarSlip $matID8 $cs_fc $cs_fs $cs_es $cs_fsu $cs_esh $cs_dbar $cs_ljoint $cs_nbars $cs_wid
$cs_dep 1.0 strong column damage

#################### end material formation for bar slip
########################################################

############################ material for shear panel
#############################################################
## Positive/Negative envelope Stress
set p1 2.1932; set p2 4.0872; set p3 4.4862; set p4 [expr $p3*1e-3];

##

stress1

stress2

stress3

stress4

set pEnvStrsp [list [expr $p1*$JointVolume] [expr $p2*$JointVolume] [expr $p3*$JointVolume] [expr
$p4*$JointVolume]]
set nEnvStrsp [list [expr -$p1*$JointVolume] [expr -$p2*$JointVolume] [expr -$p3*$JointVolume] [expr
-$p4*$JointVolume]]

## Positive/Negative envelope Strain
##

strain1 strain2 strain3 strain4

set pEnvStnsp [list 0.0002 0.004465 0.0131

0.0269]

set nEnvStnsp [list -0.0002 -0.004465 -0.0131 -0.0269]

## Ratio of maximum deformation at which reloading begins
##

Pos_env. Neg_env.

set rDispsp [list 0.25

0.25]

Chapter 21

Beam-Column Joint Element Discussion

## Ratio of envelope force (corresponding to maximum deformation) at which reloading begins
###

Pos_env. Neg_env.

set rForcesp [list 0.15

0.15]

## Ratio of monotonic strength developed upon unloading
###

Pos_env. Neg_env.

set uForcesp [list 0.0

0.0]

## Coefficients for Unloading Stiffness degradation
##

gammaK1 gammaK2 gammaK3 gammaK4 gammaKLimit

set gammaKsp [list 1.13364492409642
#set gammaKsp [list 0.0

0.0

0.0

0.0 0.0

0.10111033064469 0.0
0.0]

#### Coefficients for Reloading Stiffness degradation
###

gammaD1 gammaD2 gammaD3 gammaD4 gammaDLimit

set gammaDsp [list

0.12

0.0

0.23

0.0

0.95]

#set gammaDsp [list

0.0

0.0

0.0

0.0

0.0]

#### Coefficients for Strength degradation
###

gammaF1 gammaF2 gammaF3 gammaF4 gammaFLimit

set gammaFsp [list 1.11

0.0

0.319

#set gammaFsp [list 0.0

0.0

0.0

0.0
0.0

0.125]
0.0]

set gammaEsp 10.0

uniaxialMaterial Pinching4 5 [lindex $pEnvStrsp 0] [lindex $pEnvStnsp 0] \
[lindex $pEnvStrsp 1] [lindex $pEnvStnsp 1] [lindex $pEnvStrsp 2] \
[lindex $pEnvStnsp 2] [lindex $pEnvStrsp 3] [lindex $pEnvStnsp 3] \
[lindex $nEnvStrsp 0] [lindex $nEnvStnsp 0] \
[lindex $nEnvStrsp 1] [lindex $nEnvStnsp 1] [lindex $nEnvStrsp 2] \
[lindex $nEnvStnsp 2] [lindex $nEnvStrsp 3] [lindex $nEnvStnsp 3] \
[lindex $rDispsp 0] [lindex $rForcesp 0] [lindex $uForcesp 0] \
[lindex $rDispsp 1] [lindex $rForcesp 1] [lindex $uForcesp 1] \

0.91652498468618]

247

Chapter 21

Beam-Column Joint Element Discussion

248

[lindex $gammaKsp 0] [lindex $gammaKsp 1] [lindex $gammaKsp 2] [lindex $gammaKsp 3] [lindex $gammaKsp 4] \
[lindex $gammaDsp 0] [lindex $gammaDsp 1] [lindex $gammaDsp 2] [lindex $gammaDsp 3] [lindex $gammaDsp 4] \
[lindex $gammaFsp 0] [lindex $gammaFsp 1] [lindex $gammaFsp 2] [lindex $gammaFsp 3] [lindex $gammaFsp 4] \
$gammaEsp energy

#################### end material formation for shear panel ###########################################

##element BeamColumnJoint tag? iNode? jNode? kNode? lNode? matTag1? matTag2? matTag3? matTag4?
##

matTag5? matTag6? matTag7? matTag8? matTag9? matTag10? matTag11? matTag12? matTag13?

##

<element Height factor?> <element Width factor?>

## please note: the four nodes are in anticlockwise direction around the element
##

requires material tags for all 13 different components within the element.

##

the first 12 being that of spring and the last of the shear panel

element beamColumnJoint 7 2 6 9 5 41 42 1 21 31 1 43 44 1 22 32 1 5
#element beamColumnJoint 7 2 6 9 5 1 1 1 1 1 1 1 1 1 1 1 1 1

## %%%%%%%%%%%%%%% equivalent statement can be made in other way
#element beamColumnJoint 7 2 6 9 5 41 42 1 21 31 1 43 44 1 22 32 1 5 1.0 1.0
#element beamColumnJoint 7 2 6 9 5 1 1 1 1 1 1 1 1 1 1 1 1 1 1.0 1.0

# set the boundary conditions - command: fix nodeID xResrnt? yRestrnt?
fix 1 1 1 0
fix 2 0 0 0
fix 3 0 1 0
fix 4 0 0 0
fix 5 0 0 0
fix 6 0 0 0
fix 7 0 0 0
fix 8 0 1 0
fix 9 0 0 0
fix 10 0 0 0

pattern Plain 2 Linear {
load 4 0 -55000 0 -const
load 7 0 -55000 0 -const

Chapter 21

Beam-Column Joint Element Discussion

}

system ProfileSPD
constraints Plain
integrator LoadControl 0 1 0 0
test NormDispIncr 1e-8 150
algorithm Newton
numberer RCM
analysis Static
analyze 1
loadConst -time 0.0

pattern Plain 1 Linear {
#load nd? Fx? Fy? Mz?
load 10 1 0 0
}

set rbbt "_RBbt"; set rbtp "_RBtp"; set dlcbr "_DLCbr"; set sp "_Sp"; set jdf "_Jdf";
set lbbt "_LBbt"; set lbtp "_LBtp"; set drcbr "_DRCbr"; set ulcbr "_ULCbr"; set urcbr "_URCbr";
set RBbt [concat $fName$rbbt]; set RBtp [concat $fName$rbtp]; set Sp [concat $fName$sp];
set LBbt [concat $fName$lbbt]; set LBtp [concat $fName$lbtp]; set DLCbr [concat $fName$dlcbr];
set DRCbr [concat $fName$drcbr]; set URCbr [concat $fName$urcbr]; set ULCbr [concat $fName$ulcbr];
set Jdf [concat $fName$jdf];

recorder Node $fName.out disp -load -node 10 -dof 1
recorder Element 7 -file $RBbt.out node2BarSlipB stressStrain
recorder Element 7 -file $RBtp.out node2BarSlipT stressStrain
recorder Element 7 -file $LBbt.out node4BarSlipB stressStrain
recorder Element 7 -file $LBtp.out node4BarSlipT stressStrain
recorder Element 7 -file $DLCbr.out node1BarSlipL stressStrain
recorder Element 7 -file $DRCbr.out node1BarSlipR stressStrain
recorder Element 7 -file $ULCbr.out node3BarSlipL stressStrain
recorder Element 7 -file $URCbr.out node3BarSlipR stressStrain
recorder Element 7 -file $Sp.out shearpanel stressStrain
recorder Element 7 -file $Jdf.out deformation

set peakpts [list 0.1 10 10 30 30 45 45 60 60 75 75 90 90 105 105]

249

Chapter 21

Beam-Column Joint Element Discussion

250

set increment 10
set nodeTag 10
set dofTag 1
procRC $increment $nodeTag $dofTag $peakpts

# print the results at node and at all elements
print node
#print element

procMKPC.tcl
#############################################################################################
##########
#
#

procMKPC.tcl

## procedure for evaluating the confined concrete material envelope points based upon the modified
## kent park procedure. The procedure takes in the unconfined concrete and confining steel properties.
## created : NM (nmitra@u.washington.edu) dated: Dec. 2002
#############################################################################################
##########

proc procMKPC { CUnconfFc CUnconfEc Y Z Cov TSspace TSlength TSFy TSarea Strfactor Lenfactor } {

set CUnconfEcu -0.004;
set SecWid [expr $Lenfactor*$Z]; set SecDep [expr $Lenfactor*$Y]; set cover [expr $Lenfactor*$Cov];
set UFc [expr -$Strfactor*$CUnconfFc]; set Ue0 [expr -$CUnconfEc]; set Uecu [expr -$CUnconfEcu];
set hoopSpc [expr $Lenfactor*$TSspace]; set hoopLngth [expr $Lenfactor*$TSlength];
set hoopFy [expr $Strfactor*$TSFy]; set hoopArea [expr $TSarea*$Lenfactor*$Lenfactor];

# ratio of volume of rectangular steel hoops to volumne of concrete core measured to outside of peripheral hoops
set rhoS [expr ($hoopLngth*$hoopArea)/(($SecWid-2*$cover)*($SecDep-2*$cover)*$hoopSpc)];
# width of concrete core measured to outside of peripheral hoop
set b [expr $SecWid - 2*$cover];

set temp [expr $b/$hoopSpc]
set e50u [expr (3+0.002*$UFc)/($UFc - 1000)]; set e50h [expr 3*$rhoS*pow($temp,0.5)/4];
set Zm [expr 0.5*($UFc-1000)/(3+0.002*$UFc)]; set Z [expr 0.5/($e50u + $e50h - $Ue0)];
set K [expr (1 + $rhoS*$hoopFy/$UFc)];

Chapter 21

Beam-Column Joint Element Discussion

251

# unconfined ultimate compressive strength
set UFcu [expr -$UFc*(1-$Zm*($Uecu-$Ue0))/$Strfactor];
#cracking strain in confined concrete
set Ce0 [expr -$K*$Ue0];
# cracking stress in confined concrete
set CFc [expr -$K*$UFc/$Strfactor];
# ultimate stress in confined concrete
set CFcu [expr 0.2*$CFc];
# ultimate strain in confined concrete
set Cecu [expr -(0.8/$Z - $Ce0)];

global concreteProp;

set concreteProp [list $CUnconfFc $CUnconfEc $UFcu $CUnconfEcu $CFc $Ce0 $CFcu $Cecu];

#puts [lindex $concreteProp 0]

return $concreteProp;
}

procUniaxialPinching.tcl
#############################################################################################
########

##

# procUniaxialPinching.tcl #

# procedure for activating the pinching material given its parameters in the form of list #

# created NM (nmitra@u.washington.edu) dated : Feb 2002 #

#############################################################################################
########

proc procUniaxialPinching { materialTag pEnvelopeStress nEnvelopeStress pEnvelopeStrain nEnvelopeStrain rDisp
rForce uForce gammaK gammaD gammaF gammaE damage} {

Chapter 21

Beam-Column Joint Element Discussion

252

# add material - command: uniaxialMaterial ...... paramaters as shown

#uniaxialMaterial Pinching4 tag

#### stress1P strain1P stress2P strain2P stress3P strain3P stress4P strain4P

#### stress1N strain1N stress2N strain2N stress3N strain3N stress4N strain4N

#### rDispP rForceP uForceP rDispN rForceN uForceN

#### gammaK1 gammaK2 gammaK3 gammaK4 gammaKLimit

#### gammaD1 gammaD2 gammaD3 gammaD4 gammaDLimit

#### gammaF1 gammaF2 gammaF3 gammaF4 gammaFLimit gammaE $damage

uniaxialMaterial Pinching4 $materialTag [lindex $pEnvelopeStress 0] [lindex $pEnvelopeStrain 0] [lindex
$pEnvelopeStress 1] [lindex $pEnvelopeStrain 1] [lindex $pEnvelopeStress 2] [lindex $pEnvelopeStrain 2] [lindex
$pEnvelopeStress 3] [lindex $pEnvelopeStrain 3] [lindex $nEnvelopeStress 0] [lindex $nEnvelopeStrain 0] [lindex
$nEnvelopeStress 1] [lindex $nEnvelopeStrain 1] [lindex $nEnvelopeStress 2] [lindex $nEnvelopeStrain 2] [lindex
$nEnvelopeStress 3] [lindex $nEnvelopeStrain 3] [lindex $rDisp 0] [lindex $rForce 0] [lindex $uForce 0] [lindex $rDisp 1]
[lindex $rForce 1] [lindex $uForce 1] [lindex $gammaK 0] [lindex $gammaK 1] [lindex $gammaK 2] [lindex $gammaK 3]
[lindex $gammaK 4] [lindex $gammaD 0] [lindex $gammaD 1] [lindex $gammaD 2] [lindex $gammaD 3] [lindex
$gammaD 4] [lindex $gammaF 0] [lindex $gammaF 1] [lindex $gammaF 2] [lindex $gammaF 3] [lindex $gammaF 4]
$gammaE $damage

}

procRC.tcl
#############################################################################################
###########
#
#

procRC.tcl

## procedure for setting up a reversed cycle loading scheme. The input are mainly the
## peak points for the loading.
## The procedure primarily uses Displacement control for loading, if it fails uses ArcLength control
## created : NM (nmitra@u.washington.edu) dated: Sep 2002

Chapter 21

Beam-Column Joint Element Discussion

253

#############################################################################################
###########

proc procRC { incre nodeTag dofTag peakpts } {

set displayTag 0;
set numTimes 150;

set x [lindex $peakpts 0];
set dU [expr $x/$incre];
#set dU0 [expr $dU/1000];
set dU0 [expr $dU/10000];
integrator DisplacementControl $nodeTag $dofTag 0.0 1 $dU $dU
analysis Static
analyze $incre

integrator DisplacementControl $nodeTag $dofTag 0.0 1 [expr -$dU] [expr -$dU]
analyze [expr 2*$incre]

integrator DisplacementControl $nodeTag $dofTag 0.0 1 $dU $dU
analyze $incre

## end the first peak pt start for others

for {set j 1} {$j < [llength $peakpts]} {incr j 1} {

set y [lindex $peakpts $j]
set dSt [expr $y/$dU]
set dS [expr int($dSt)]

test NormDispIncr 1e-8 $numTimes $displayTag
algorithm Newton

############# start loading cycle ##################
set t 0;

while {$t != $dS} {

Chapter 21

Beam-Column Joint Element Discussion

integrator DisplacementControl $nodeTag $dofTag 0.0 1 $dU $dU
set ok [analyze 1]
incr t 1;

if {$ok != 0} {
#

if {$t == $dS} {break};
puts "Displacement control failed ..... trying Arc-Length control"
set currentDisp [nodeDisp $nodeTag $dofTag]
puts "Current Displacement is $currentDisp"

#

algorithm Linear
test NormDispIncr 1e-6 $numTimes $displayTag
#algorithm ModifiedNewton

#

integrator DisplacementControl $nodeTag $dofTag 0.0 1 $dU0 $dU0

#

integrator DisplacementControl $nodeTag $dofTag 0.0 10 $dU0 $dU0
integrator ArcLength [expr $dU0] 1.0

#

set ok [analyze 1]
analyze 1
}

#

puts "that worked ..... back to regular Newton "
test NormDispIncr 1e-8 $numTimes $displayTag

#

algorithm Newton
}

################## end of loading cycle, start unloading cycle ########

set t 0;

while {$t != [expr 2*$dS]} {
integrator DisplacementControl $nodeTag $dofTag 0.0 1 [expr -$dU] [expr -$dU]
set ok [analyze 1]
incr t 1;

if {$ok != 0} {
#

if {$t == [expr 2*$dS]} {break};
puts "Displacement control failed ..... trying Arc-Length control"
set currentDisp [nodeDisp $nodeTag $dofTag]
puts "Current Displacement is $currentDisp"

#

algorithm Linear

254

Chapter 21

Beam-Column Joint Element Discussion

255

test NormDispIncr 1e-6 $numTimes $displayTag
#algorithm ModifiedNewton
#

integrator DisplacementControl $nodeTag $dofTag 0.0 1 [expr -$dU0] [expr -$dU0]

#
-$dU0]

integrator DisplacementControl $nodeTag $dofTag 0.0 10 [expr -$dU0] [expr
integrator ArcLength [expr $dU0] 1.0

#

set ok [analyze 1]
analyze 1
}

#

puts "that worked .... back to regular Newton "
test NormDispIncr 1e-8 $numTimes $displayTag

#

algorithm Newton
}

############# end of unloading cycle, start reloading cycle ###########

set t 0;

while {$t != $dS} {
integrator DisplacementControl $nodeTag $dofTag 0.0 1 $dU $dU
set ok [analyze 1]
incr t 1;

if {$ok != 0} {
#

if {$t == $dS} {break};
puts "Displacement control failed ..... trying Arc-Length control"
set currentDisp [nodeDisp $nodeTag $dofTag]
puts "Current Displacement is $currentDisp"

#

algorithm Linear
test NormDispIncr 1e-6 $numTimes $displayTag
#algorithm ModifiedNewton

#

integrator DisplacementControl $nodeTag $dofTag 0.0 1 $dU0 $dU0

#

integrator DisplacementControl $nodeTag $dofTag 0.0 10 $dU0 $dU0
integrator ArcLength [expr $dU0] 1.0

#

set ok [analyze 1]
analyze 1
}

Chapter 21

#

Beam-Column Joint Element Discussion

256

puts "that worked .... back to regular Newton "
test NormDispIncr 1e-8 $numTimes $displayTag

#

algorithm Newton
}

######## reloading cycle completed #############################

if {$ok == 0} {
puts "analysis succesful at $y mm displacement";
} else {
puts "analysis could not proceed fine beyond $y mm displacement";
}

}
}

UC Davis Soil Elements
For further information or examples about the following elements, please visit:
http://sokocalo.engr.ucdavis.edu/~jeremic/ (http://sokocalo.engr.ucdavis.edu/~jeremic/)

FourNodeQuadUP Element
FourNodeQuadUP is a four-node plane-strain element using bilinear isoparametric formulation.
This element is implemented for simulating dynamic response of solid-fluid fully coupled material,
based on Biot's theory of porous medium. Each element node has 3 degrees-of-freedom (DOF):
DOF 1 and 2 for solid displacement (u) and DOF 3 for fluid pressure (p).

element quadUP $eleTag $iNode $jNode $kNode $lNode $thick $type
$matTag $bulk $fmass $hPerm $vPerm <$b1 $b2 $t>
$eleTag

unique element object tag

$iNode, $jNode,
$kNode, $lNode

Four element node (previously defined) numbers in counter-clockwise order
around the element

$thick

Element thickness

Chapter 21

Beam-Column Joint Element Discussion

257

$type

The string "PlaneStrain"

$matTag

Tag of an NDMaterial object (previously defined) of which the element is
composed

$bulk

Combined undrained bulk modulus Bc relating changes in pore pressure and
volumetric strain, may be approximated by:

Bc ≈ B f / n
where Bf is the bulk modulus of fluid phase (2.2x106 kPa for water), and n the
initial porosity.
$fmass

Fluid mass density

$hPerm

Permeability coefficient in horizontal direction

$vPerm

Permeability coefficient in vertical direction

$b1, $b2

Optional body forces in horizontal and vertical directions respectively (defaults
are 0.0)

$t

Optional uniform element normal traction, positive in tension (default is 0.0)

TYPICAL RANGE OF PERMEABILITY COEFFICIENT (m/s)
Gravel

Sand

Silty Sand

Silt

Clay

>1.0x10-3

1.0x10-5 ~ 1.0x10-3 1.0x10-7 ~ 1.0x10-5 1.0x10-9 ~ 1.0x10-7 <1.0x10-9

OUTPUT INTERFACE:
Pore pressure can be recorded at an element node using OpenSees Node Recorder (page 303):
recorder Node <-file $fileName> <-time> <-node ($node1 $node2 ...)> -dof 3 vel
Note: dof 3 is for pore pressure output.
The valid queries to a quadUP element when creating an ElementRecorder (page 307) are 'force',
'stiffness', or 'material matNum matArg1 matArg2 ...', where matNum represents the material
object at the corresponding integration point.

Chapter 21

Beam-Column Joint Element Discussion

258

u-p-U element
This command is used to construct a u-p-U element object, which include two types: eight node
element and twenty node element.
For eight-node element:

element Brick8N_u_p_U $eleTag $node1 $node2 $node3 $node4 $node5
$node6 $node7 $node8 $matTag $bf1 $bf2 $bf3 $n $alpha $soildDens
$fluidDens $k1 $k2 $k3 $K_fluid $P

For twenty-node element:

element Brick20N_u_p_U $eleTag $node1 $node2 $node3 $node4 $node5
$node6 $node7 $node8 $node9 $node10 $node11 $node12 $node13
$node14 $node15 $node16 $node17 $node18 $node19 $node20
$matTag $bf1 $bf2 $bf3 $n $alpha $soildDens $fluidDens $k1 $k2 $k3
$K_fluid $P

$eleTag

unique element object tag

$node1 $node2
$node3 $node4
$node5 $node6
$node7 $node8 ....

node coordinate (either eight or twenty), input order is shown in
the figure

$matTag

material tag associated with previsouly-difined NDMaterial object

$bf1 $bf2 $bf3

body force in the direction of global coordinates x, y and z

$n

porosity

$alpha

1-Ks/Kt (ratio of void space =1 for soils, =0.6 for concrete...)

$soildDens

solid density

$fluidDens

fluid density

$k1 $k1 $k3

coefficient of permeability in the direction of x, y and z

$K_fluid

fluid bulk modulus

$P

pressure... not used currently (set to 0.0)

Chapter 21

Beam-Column Joint Element Discussion

259

The valid queries to a Brick8N_u_p_U and Brick20N_u_p_U elements when creating an
ElementRecorder (page 307) object are 'force,' 'stiffness,' stress', 'gausspoint' or 'plastic'. The
output is given as follows:
'stress'

the six stress components from each Gauss points are output by the
order: sigma_xx, sigma_yy, sigma_zz, sigma_xy,
sigma_xz,sigma_yz

'gausspoint'

the coordinates of all Gauss points are printed out

'plastic'

the equivalent deviatoric plastic strain from each Gauss point is
output in the same order as the coordinates are printed

Eight Node Brick Element
The command is used to construct an eight-node three dimensional brick element object, which is
based on tensor operation.

element Brick8N $eletag $node1 $node2 $node3 $node4 $node5 $node6 $node7
$node8 $matTag $bf1 $bf2 $bf3 $massDens

$eletag

unique element object tag

$node1 $node2
$node3 $node4
$node5 $node6
$node7 $node8

eight node coordinates, input order is shown in the figure

$matTag

material tag associated with previsouly-defined NDMaterial
object

$bf1 $bf2 $bf3

body force in the direction of global coordinates x, y and z

$massDens

mass density (mass/volume)

The valid queries to a Brick8N element when creating an ElementRecorder (page 307) object are
'force,' 'stiffness,' stress', 'gausspoint' or 'plastic'. The output is given as follows:
'stress'

the six stress components from each Gauss points are output by the
order: sigma_xx, sigma_yy, sigma_zz, sigma_xy,
sigma_xz,sigma_yz

'gausspoint'

the coordinates of all Gauss points are printed out

Chapter 21

'plastic'

Beam-Column Joint Element Discussion

the equivalent deviatoric plastic strain from each Gauss point is
output in the same order as the coordinates are printed

Figure 52: Node Numbering for Eight-Node Three-Dimensional Element

260

Chapter 21

Beam-Column Joint Element Discussion

261

Twenty Node Brick Element
The element is used to construct a twenty-node three dimensional element object

element Brick20N $eletag $node1 $node2 $node3 $node4 $node5 $node6
$node7 $node8 $node9 $node10 $node11 $node12 $node13 $node14
$node15 $node16 $node17 $node18 $node19 $node20 $matTag $bf1
$bf2 $bf3 $massDen

$eletag

unique element object tag

$node1 $node2
$node3 $node4
$node5 $node6
$node7 $node8
$node9 $node10
$node11 $node12
$node13 $node14
$node15 $node16
$node17 $node18
$node19 $node20

twenty node coordinates, input order is shown in the figure

$matTag

material tag associated with previsouly-defined NDMaterial
(page 162) object

$bf1 $bf2 $bf3

body force in the direction of global coordinates x, y and z

$massDen

mass density (mass/volume)

The valid queries to a Brick20N element when creating an ElementRecorder (page 307) object are
'force,' 'stiffness,' stress', 'gausspoint' or 'plastic'. The output is given as follows:
'stress'

the six stress components from each Gauss points are output by the
order: sigma_xx, sigma_yy, sigma_zz, sigma_xy,
sigma_xz,sigma_yz

'gausspoint'

the coordinates of all Gauss points are printed out

'plastic'

the equivalent deviatoric plastic strain from each Gauss point is
output in the same order as the coordinates are printed

Chapter 21

Beam-Column Joint Element Discussion

Figure 53: Node Numbering for Twenty-Node Three-Dimensional Element

262

263

CHAPTER 22

UC San Diego Soil Elements
This chapter describes the user interfaces for: 1) a number of NDMaterial models developed for
simulating nonlinear, drained/undrained soil response under general 3D cyclic loading conditions,
and 2) a number of 2D and 3D solid-fluid fully coupled elements for simulating pore water pressure
dissipation/redistribution.
Please visit http://cyclic.ucsd.edu/opensees (http://cyclic.ucsd.edu/opensees) for examples.
This documentation is last updated at 8/5/2005 by Zhaohui Yang (zhyang@ucsd.edu
(mailto:zhyang@ucsd.edu)) and Ahmed Elgamal (elgamal@ucsd.edu
(mailto:elgamal@ucsd.edu)).

In This Chapter
FourNodeQuadUP.................................................... 264
Nine_Four_Node_QuadUP ...................................... 266
BrickUP .................................................................... 268
Twenty_Eight_Node_BrickUP .................................. 270

Chapter 22

UC San Diego Soil Elements

264

FourNodeQuadUP
FourNodeQuadUP is a four-node plane-strain element using bilinear isoparametric formulation.
This element is implemented for simulating dynamic response of solid-fluid fully coupled material,
based on Biot's theory of porous medium. Each element node has 3 degrees-of-freedom (DOF):
DOF 1 and 2 for solid displacement (u) and DOF 3 for fluid pressure (p). Please visit
http://cyclic.ucsd.edu/opensees (http://cyclic.ucsd.edu/opensees) for examples.

OUTPUT INTERFACE:
Pore pressure can be recorded at an element node using OpenSees Node Recorder:

recorder Node <-file $fileName> <-time> <-node ($nod1 $nod2 …)> -dof 3 vel

See OpenSees command manual (McKenna and Fenves 2001) for nodal displacement, velocity,
or acceleration recorders.

The valid queries to a quadUP element when creating an ElementRecorder are 'force', 'stiffness',
or 'material matNum matArg1 matArg2 ...', where matNum represents the material object at the
corresponding integration point.

element quadUP $eleTag $iNode $jNode $kNode $lNode $thick $matTag
$bulk $fmass $hPerm $vPerm <$b1=0 $b2=0 $t=0>
$eleTag

A positive integer uniquely identifying the element among all elements

$iNode, $jNode,
$kNode, $lNode

Four element node (previously defined) numbers in counter-clockwise order
around the element

$thick

Element thickness

$matTag

Tag of an NDMaterial object (previously defined) of which the element is
composed

Chapter 22

$bulk

UC San Diego Soil Elements

265

Combined undrained bulk modulus Bc relating changes in pore pressure and
volumetric strain, may be approximated by:

Bc ≈ B f / n
where Bf is the bulk modulus of fluid phase (2.2x106 kPa for water), and n the
initial porosity.
$fmass

Fluid mass density

$hPerm

Permeability coefficient in horizontal direction

$vPerm

Permeability coefficient in vertical direction

$b1, $b2

Optional gravity acceleration components in horizontal and vertical directions
respectively (defaults are 0.0)

$t

Optional uniform element normal traction, positive in tension (default is 0.0)

TYPICAL RANGE OF PERMEABILITY COEFFICIENT (cm/s)
Gravel

Sand

Silty Sand

Silt

Clay

>1.0x10-1

1.0x10-3 ~ 1.0x10-1

1.0x10-5 ~ 1.0x10-3

1.0x10-7 ~ 1.0x10-5

<1.0x10-7

Chapter 22

UC San Diego Soil Elements

266

Nine_Four_Node_QuadUP
Nine_Four_Node_QuadUP is a 9-node quadrilateral plane-strain element. The four corner nodes
have 3 degrees-of-freedom (DOF) each: DOF 1 and 2 for solid displacement (u) and DOF 3 for
fluid pressure (p). The other five nodes have 2 DOFs each for solid displacement. This element is
implemented for simulating dynamic response of solid-fluid fully coupled material, based on Biot's
theory of porous medium. Please visit http://cyclic.ucsd.edu/opensees
(http://cyclic.ucsd.edu/opensees) for examples.

OUTPUT INTERFACE:
Pore pressure can be recorded at an element node using OpenSees Node Recorder:

recorder Node <-file $fileName> <-time> <-node ($nod1 $nod2 …)> -dof 3 vel

See OpenSees command manual (McKenna and Fenves 2001) for nodal displacement, velocity,
or acceleration recorders.

The valid queries to a Nine_Four_Node_QuadUP element when creating an ElementRecorder are
'force', 'stiffness', or 'material matNum matArg1 matArg2 ...', where matNum represents the
material object at the corresponding integration point.

element 9_4_QuadUP $eleTag $Node1 $Node2 $Node3 $Node4 $Node5
$Node6 $Node7 $Node8 $Node9 $thick $matTag $bulk $fmass
$hPerm $vPerm <$b1=0 $b2=0>
4

7

3

8

9

6

1

5

2

$eleTag

A positive integer uniquely identifying the element among all elements

$Node1,…
$Node9

Nine element node (previously defined) numbers (see figure above for order of
numbering).

$thick

Element thickness

Chapter 22

UC San Diego Soil Elements

267

$matTag

Tag of an NDMaterial object (previously defined) of which the element is composed

$bulk

Combined undrained bulk modulus Bc relating changes in pore pressure and
volumetric strain, may be approximated by:

Bc ≈ B f / n
where Bf is the bulk modulus of fluid phase (2.2x106 kPa for water), and n the initial
porosity.
$fmass

Fluid mass density

$hPerm,
$vPerm

Permeability coefficient in horizontal and vertical directions respectively.

$b1, $b2

Optional gravity acceleration components in horizontal and vertical directions
respectively (defaults are 0.0)

Chapter 22

UC San Diego Soil Elements

268

BrickUP
BrickUP is an 8-node hexahedral linear isoparametric element. Each node has 4
degrees-of-freedom (DOF): DOFs 1 to 3 for solid displacement (u) and DOF 4 for fluid pressure
(p). This element is implemented for simulating dynamic response of solid-fluid fully coupled
material, based on Biot's theory of porous medium. Please visit
http://cyclic.ucsd.edu/opensees (http://cyclic.ucsd.edu/opensees) for examples.

OUTPUT INTERFACE:
Pore pressure can be recorded at an element node using OpenSees Node Recorder:

recorder Node <-file $fileName> <-time> <-node ($nod1 $nod2 …)> -dof 3 vel

See OpenSees command manual (McKenna and Fenves 2001) for nodal displacement, velocity,
or acceleration recorders.

The valid queries to a BrickUP element when creating an ElementRecorder are 'force', 'stiffness',
or 'material matNum matArg1 matArg2 ...', where matNum represents the material object at the
corresponding integration point.

element brickUP $eleTag $Node1 $Node2 $Node3 $Node4 $Node5 $Node6
$Node7 $Node8 $matTag $bulk $fmass $PermX $PermY $PermZ
<$bX=0 $bY=0 $bZ=0>
7

8

6

5

4

1

3

2

$eleTag

A positive integer uniquely identifying the element among all elements

$Node1,…
$Node8

Eight element node (previously defined) numbers (see figure above for order of
numbering).

Chapter 22

UC San Diego Soil Elements

269

$matTag

Tag of an NDMaterial object (previously defined) of which the element is composed

$bulk

Combined undrained bulk modulus Bc relating changes in pore pressure and
volumetric strain, may be approximated by:

Bc ≈ B f / n
where Bf is the bulk modulus of fluid phase (2.2x106 kPa for water), and n the initial
porosity.
$fmass

Fluid mass density

$permX,
$permY,
$permZ

Permeability coefficients in x, y, and z directions respectively.

$bX, $bY,
$bZ

Optional gravity acceleration components in x, y, and z directions directions
respectively (defaults are 0.0)

Chapter 22

UC San Diego Soil Elements

270

Twenty_Eight_Node_BrickUP
Twenty_Eight_Node_BrickUP is a 20-node hexahedral isoparametric element. The eight corner
nodes have 4 degrees-of-freedom (DOF) each: DOFs 1 to 3 for solid displacement (u) and DOF 4
for fluid pressure (p). The other nodes have 3 DOFs each for solid displacement. This element is
implemented for simulating dynamic response of solid-fluid fully coupled material, based on Biot's
theory of porous medium. Please visit http://cyclic.ucsd.edu/opensees
(http://cyclic.ucsd.edu/opensees) for examples.

OUTPUT INTERFACE:
Pore pressure can be recorded at an element node using OpenSees Node Recorder:

recorder Node <-file $fileName> <-time> <-node ($nod1 $nod2 …)> -dof 3 vel

See OpenSees command manual (McKenna and Fenves 2001) for nodal displacement, velocity,
or acceleration recorders.

The valid queries to a Twenty_Eight_Node_BrickUP element when creating an ElementRecorder
are 'force', 'stiffness', or 'material matNum matArg1 matArg2 ...', where matNum represents the
material object at the corresponding integration point.

element 20_8_BrickUP $eleTag $Node1 … $Node20 $matTag $bulk $fmass
$PermX $PermY $PermZ <$bX=0 $bY=0 $bZ=0>
7

15

6

16
8

14
20

13

5

19

18
17

4

11

12
1

$eleTag

3
10

9

2

A positive integer uniquely identifying the element among all elements

Chapter 22

UC San Diego Soil Elements

271

$Node1,…
$Node20

20 element node (previously defined) numbers (see figure above for order of
numbering).

$matTag

Tag of an NDMaterial object (previously defined) of which the element is composed

$bulk

Combined undrained bulk modulus Bc relating changes in pore pressure and
volumetric strain, may be approximated by:

Bc ≈ B f / n
where Bf is the bulk modulus of fluid phase (2.2x106 kPa for water), and n the initial
porosity.
$fmass

Fluid mass density

$permX,
$permY,
$permZ

Permeability coefficients in x, y, and z directions respectively.

$bX, $bY,
$bZ

Optional gravity acceleration components in x, y, and z directions directions
respectively (defaults are 0.0)

Chapter 22

UC San Diego Soil Elements

272

References

Elgamal, A., Lai, T., Yang, Z. and He, L. (2001). "Dynamic Soil Properties, Seismic Downhole
Arrays and Applications in Practice," State-of-the-art paper, Proc., 4th Intl. Conf. on Recent
Advances in Geote. E.Q. Engrg. Soil Dyn. March 26-31, San Diego, CA, S. Prakash (Ed.).

Elgamal, A., Yang, Z. and Parra, E. (2002). "Computational Modeling of Cyclic Mobility and
Post-Liquefaction Site Response," Soil Dyn. Earthquake Engrg., 22(4), 259-271.

Elgamal, A., Yang, Z., Parra, E. and Ragheb, A. (2003). "Modeling of Cyclic Mobility in Saturated
Cohesionless Soils," Int. J. Plasticity, 19(6), 883-905.

McKenna, F. and Fenves, G. (2001). "The OpenSees Command Language Manual: version 1.2,"
Pacific Earthquake Engineering Center, Univ. of Calif., Berkeley. (http://opensees.berkeley.edu).

Parra, E. (1996). "Numerical Modeling of Liquefaction and Lateral Ground Deformation Including
Cyclic Mobility and Dilation Response in Soil Systems," Ph.D. Thesis, Dept. of Civil Engineering,
Rensselaer Polytechnic Institute, Troy, NY.

Yang, Z. (2000). "Numerical Modeling of Earthquake Site Response Including Dilation and
Liquefaction," Ph.D. Thesis, Dept. of Civil Engineering and Engineering Mechanics, Columbia
University, NY, New York.

Yang, Z. and Elgamal, A. (2002). "Influence of Permeability on Liquefaction-Induced Shear
Deformation," J. Engrg. Mech., ASCE, 128(7), 720-729.

Yang, Z., Elgamal, A. and Parra, E. (2003). "A Computational Model for Liquefaction and
Associated Shear Deformation," J. Geotechnical and Geoenvironmental Engineering, ASCE,
129(12), 1119-1127.

273

CHAPTER 23

block Command
The block command is used to generate meshes of quadrilateral or brick finite element.
The block2D (page 274) command generates meshes of quadrilateral elements in two or three
dimensions. In three dimensions, a two-dimensional surface appropriate for shell analysis is
generated.
The block3D (page 276) command generates three-dimensional meshes of eight-node brick solid
element.

In This Chapter
block2D Command................................................... 274
block3D Command................................................... 276

Chapter 23

block Command

274

block2D Command
The block2D command generates meshes of quadrilateral elements in two or three dimensions. In
three dimensions, a two-dimensional surface appropriate for shell analysis is generated.

block2d $nx $ny $e1 $n1 element (element arguments) {
1 $x1 $y1 <$z1>
2 $x2 $y2 <$z2>
3 $x3 $y3 <$z3>
4 $x4 $y4 <$z4>
<5> <$x5> <$y5> <$z5>
<6> <$x6> <$y6> <$z6>
<7> <$x7> <$y7> <$z7>
<8> <$x8> <$y8> <$z8>
<9> <$x9> <$y9> <$z9>
}
$nx

$ny

number of elements in the local x and y directions of the block,
respectively

$e1

$n1

starting element and node number for generation, respectively

element

string defining which quadrilateral element (page 228, page 229,
page 227, page 228) is being used

(element
arguments)

list of data parameters for element being used. This list may
include, but is not limited to, a $matTag number

{$x1, .... $x9} {$y1,
.... $y9}

coordinates of the block elements in two dimensions

{$z1, .... $z9}

coordinate of the block elements in third dimension (optional,
default=0.0)

Only the first four nodes (1-4) are required. Nodes 5-9 are used to generate curved meshes. The
user may specify any combination of nodes 5-9, omitting some of them if desired.

Chapter 23

block Command

NOTE: this command only recognizes variable substitutions when the command
arguments are placed in quotes rather than braces
EXAMPLE:
block2d $nx $ny $e1 $n1 element (element arguments) {
1 $x1 $y1 <$z1>
2 $x2 $y2 <$z2>
3 $x3 $y3 <$z3>
4 $x4 $y4 <$z4>
<5> <$x5> <$y5> <$z5>
<6> <$x6> <$y6> <$z6>
<7> <$x7> <$y7> <$z7>
<8> <$x8> <$y8> <$z8>
<9> <$x9> <$y9> <$z9>
}

Figure 54: Node Numbering for Nine-Node block2D

275

Chapter 23

block Command

276

block3D Command
The block3D command generates three-dimensional meshes of eight-node brick solid element.

block3d $nx $ny $nz $e1 $n1 element elementArgs {
1 $x1 $y1 $z1
2 $x2 $y2 $z2
3 $x3 $y3 $z3
4 $x4 $y4 $z4
5 $x5 $y5 $z5
6 $x6 $y6 $z6
7 $x7 $y7 $z7
8 $x8 $y8 $z8
<9> <$x9> <$y9> <$z9>
...
<27> <$x27> <$y27> <$z27>
}
$nx $ny $nz

number of elements in the local x,y and z-direction of the block

$e1

starting element number for generation

$n1

starting node number for generation

element

define which brick element (page 231, page 230) is being used

elementArgs

list of data parameters for element being used. This list may
include, but is not limited to, a $matTag number

{$x1, .... $x27} {$y1,
.... $y27} {$z1, ....
$z27}

coordinates of the block elements in three dimensions.

Chapter 23

block Command

277

NOTE: this command only recognizes variable substitutions when the command
arguments are placed in quotes rather than braces
Only the first eight nodes (1-8) are required. Nodes 9-27 are used to generate curved meshes.
The user may specify any combination of nodes 9-27, omitting some of them if desired.

278

CHAPTER 24

region Command
The region command is used to label a group of nodes and elements. This command is also used
to assign rayleigh damping parameters to the nodes and elements in this region.

region $regTag <-ele ($ele1 $ele2 ...)> <-eleRange $startEle $endEle> <-ele all>
<-node ($node1 $node2 ...)> <-nodeRange $startNode $endNode>
<-node all> <-rayleigh $alphaM $betaK $betaKinit $betaKcomm>
The region is specified by either elements or nodes, not both. If elements are defined, the region
includes these elements and the all connected nodes. If nodes are specified, the region includes
these nodes and all elements whose external nodes are prescribed.
$regTag

unique integer tag

$ele1 $ele2 ...

tags of elements -- selected elements in domain (optional,
default: omitted)

$startEle $endEle

tag for start and end elements -- range of selected elements in
domain (optional, default: all)

all

all elements in domain (optional & default)

$alphaM $betaK
$betaKinit
$betaKcomm

Arguments to define Rayleigh damping matrix (optional, default:
zero)

OR:
$regTag

unique integer tag

$node1 $node2 ...

node tags -- select nodes in domain (optional,
default: all)

$startNode
$endNode

tag for start and end nodes -- range of nodes in
domain (optional, default: all)

all

all nodes in domain (optional & default)

$alphaM $betaK
$betaKinit
$betaKcomm

Arguments to define Rayleigh damping matrix
(optional, default: zero)

The damping matrix D is specified as a combination of stiffness and mass-proportional damping
matrices:
D = $alphaM * M + $betaK * Kcurrent +$betaKinit * Kinit + $betaKcomm * KlastCommit

Chapter 24

region Command

The mass and stiffness matrices are defined as:
M

mass matrix used to calculate Rayleigh Damping

Kcurrent

stiffness matrix at current state determination used to calculate
Rayleigh Damping

Kinit

stiffness matrix at initial state determination used to calculate
Rayleigh Damping

KlastCommit

stiffness matrix at last-committed state determination used to
calculate Rayleigh Damping

NOTE: a region is defined by either nodes or elements, not both.
EXAMPLE:
region 1 -ele 1 5 -eleRange 10 15
region 2 -node 2 4 6 -nodeRange 9 12

279

280

CHAPTER 25

Geometric Transformation
Command
The geometric-transformation command (geomTransf) is used to construct a
coordinate-transformation (CrdTransf) object, which transforms beam element stiffness and
resisting force from the basic system to the global-coordinate system. The command has at least
one argument, the transformation type. Each type is outlined below.

In This Chapter
Linear Transformation .............................................. 280
P-Delta Transformation ............................................ 286
Corotational Transformation ..................................... 287

Linear Transformation
This command is used to construct a linear coordinate transformation (LinearCrdTransf) object,
which performs a linear geometric transformation of beam stiffness and resisting force from the
basic system to the global-coordinate system.
For a two-dimensional problem:

geomTransf Linear $transfTag <-jntOffset $dXi $dYi $dXj $dYj>
For a three-dimensional problem:

geomTransf Linear $transfTag $vecxzX $vecxzY $vecxzZ <-jntOffset $dXi $dYi
$dZi $dXj $dYj $dZj>
$transfTag

unique identifier for CrdTransf object

Chapter 25

$vecxzX $vecxzY
$vecxzZ

Geometric Transformation Command

X, Y, and Z components of vecxz, the vector used to define the
local x-z plane of the local-coordinate system. The local y-axis is
defined by taking the cross product of the x-axis and the vecxz
vector.
These components are specified in the global-coordinate system
X,Y,Z and define a vector that is in a plane parallel to the x-z
plane of the local-coordinate system.
These items need to be specified for the three-dimensional
problem.

$dXi $dYi $dZi

joint offset values -- absolute offsets specified with respect to the
global coordinate system for element-end node i (the number of
arguments depends on the dimensions of the current model)
(optional)

$dXj $dYj $dZj

joint offset values -- absolute offsets specified with respect to the
global coordinate system for element-end node j (the number of
arguments depends on the dimensions of the current model)
(optional)

The element coordinate system is specified as follows:

281

Chapter 25

Geometric Transformation Command

282

The x-axis is the axis connecting the two element nodes; the y- and z-axes are then defined using
a vector that lies on a plane parallel to the local x-z plane -- vecxz. The y-axis is defined by taking
the cross product of the x-axis and the vecxz vector. The section is attached to the element such
that the y-z coordinate system used to specify the section corresponds to the y-z axes of the
element.

Figure 55: Definition of the Local Coordinate System

Chapter 25

Geometric Transformation Command

Figure 56: Definition of Rigid Joint Offset (note: check sign of dXi,etc components)

283

Chapter 25

Geometric Transformation Command

The following figures should aid in understanding the vector vecxz definition:

284

Chapter 25

Geometric Transformation Command

285

Chapter 25

Geometric Transformation Command

286

P-Delta Transformation
This command is used to construct the P-Delta Coordinate Transformation (PDeltaCrdTransf)
object, which performs a linear geometric transformation of beam stiffness and resisting force from
the basic system to the global coordinate system, considering second-order P-Delta effects.
For a two-dimensional problem:

geomTransf PDelta $transfTag <-jntOffset $dXi $dYi $dXj $dYj>
For a three-dimensional problem:

geomTransf PDelta $transfTag $vecxzX $vecxzY $vecxzZ <-jntOffset $dXi $dYi
$dZi $dXj $dYj $dZj>
The element coordinate system and joint offset values are specified as in the Linear
transformation (page 280).
$transfTag

unique identifier for CrdTransf object

$vecxzX $vecxzY
$vecxzZ

X, Y, and Z components of vecxz, the vector used to define the
local x-z plane of the local-coordinate system. (These items
need to be specified for the three-dimensional problem.)
These components are specified in the global-coordinate system
X,Y,Z and define a vector that is in a plane parallel to the x-z
plane of the local-coordinate system.
These items need to be specified for the three-dimensional
problem.

$dXi $dYi $dZi

joint offset values -- absolute offsets specified with respect to the
global coordinate system for element-end node i (the number of
arguments depends on the dimensions of the current model
(page 34)) (optional)

$dXj $dYj $dZj

joint offset values -- absolute offsets specified with respect to the
global coordinate system for element-end node j (the number of
arguments depends on the dimensions of the current model
(page 34)) (optional)

Chapter 25

Geometric Transformation Command

287

Corotational Transformation
This command is used to construct the Corotational Coordinate Transformation (CorotCrdTransf)
object, which performs an exact geometric transformation of beam stiffness and resisting force
from the basic system to the global coordinate system.
For a two-dimensional problem:

geomTransf Corotational $transfTag <-jntOffset $dXi $dYi $dXj $dYj>
For a three-dimensional problem:

geomTransf Corotational $transfTag $vecxzX $vecxzY $vecxzZ <-jntOffset $dXi
$dYi $dZi $dXj $dYj $dZj>
NOTE: The Corotational transformation is only available with the Win32 version of OpenSees
(http://opensees.berkeley.edu/OpenSees/binaries.html).
The element coordinate system and joint offset values are specified as in the Linear
transformation (page 280).
$transfTag

unique identifier for CrdTransf object

$vecxzX $vecxzY
$vecxzZ

X, Y, and Z components of vecxz, the vector used to define the
local x-z plane of the local-coordinate system. (These items
need to be specified for the three-dimensional problem.)
These components are specified in the global-coordinate system
X,Y,Z and define a vector that is in a plane parallel to the x-z
plane of the local-coordinate system.

$dXi $dYi $dZi

joint offset values -- absolute offsets specified with respect to the
global coordinate system for element-end node i (the number of
arguments depends on the dimensions of the current model
(page 34)) (optional)

$dXj $dYj $dZj

joint offset values -- absolute offsets specified with respect to the
global coordinate system for element-end node j (the number of
arguments depends on the dimensions of the current model
(page 34)) (optional)

288

CHAPTER 26

Time Series
While there is no timeSeries command in the language, a number of commands take as the
argument a list of items which defines the TimeSeries object to be constructed as part of the
command, such as the LoadPattern (page 294) and groundMotion (page 299) objects.

Time series act differently depending on what type of object they are applied to:
LoadPattern (page 294) object:
Load factors are applied to the loads and constraints
groundMotion (page 299) object:
Load factors are applied at the DOF in a ground motion

The type of TimeSeries objects available are presented in this chapter.

NOTE: The TimeSeries objects are handled by the Tcl interpreter as lists. Therefore, they can be
defined a-priori within quotes "" and given a variable name. EXAMPLE:
set Gaccel "Series -dt $dt -filePath $outFile -factor $GMfatt"; # time series information
pattern UniformExcitation 2 1 -accel $Gaccel;

In This Chapter
Constant Time Series............................................... 289
Linear Time Series ................................................... 289
Rectangular Time Series .......................................... 290
Sine Time Series ...................................................... 291
Path Time Series...................................................... 292

# create uniform excitation

Chapter 26

Time Series

289

Constant Time Series
This command creates a ConstantSeries TimeSeries (page 288) object and associates it to the
LoadPattern (page 294) object being constructed.

Constant <-factor $cFactor>
$cFactor

load-factor coefficient. (optional. default = 1.0)

The load factor to be applied to the loads and constraints in the LoadPattern object is constant and
equal to $cFactor.

Figure 57: Constant Time Series

Linear Time Series
This command creates a LinearSeries TimeSeries (page 288) object and associates it to the
LoadPattern (page 294) or groundMotion (page 299) object being constructed.

Linear <-factor $cFactor>

Chapter 26

$cFactor

Time Series

290

load-factor coefficient. (optional. default = 1.0)

The load factor to be applied to the loads and constraints in the LoadPattern or groundMotion
object is equal to $cFactor* time

Figure 58: Linear Time Series

Rectangular Time Series
This command creates a RectangularSeries TimeSeries (page 288) object and associates it to the
LoadPattern (page 294) object being constructed.

Rectangular $tStart $tFinish <-factor $cFactor>
$tStart

start time when the load factor is applied

$tFinish

end time when the load factor is applied

$cFactor

load-factor coefficient. (optional. default = 1.0)

Chapter 26

Time Series

291

The load factor to be applied to the loads and constraints in the LoadPattern object is constant and
equal to $cFactor during the domain time from $tStart to $tFinish

Figure 59: Rectangular Time Series

Sine Time Series
This command creates a TrigSeries TimeSeries (page 288) object and associates it to the
LoadPattern (page 294) object being constructed.

Sine $tStart $tFinish $period <-shift $shift> <-factor $cFactor>
$tStart

start time when the load factor is applied

$tFinish

end time when the load factor is applied

$period

characteristic period of sine wave

$shift

phase shift (radians) (optional. default = 0.0)

$cFactor

load-factor coefficient. (optional. default = 1.0)

The load factor applied to the loads and constraints in the LoadPattern object is equal to:

Chapter 26

Time Series

Figure 60: Sine Time Series

Path Time Series
This command associates a TimeSeries (page 288) object of the type PathSeries or
PathTimeSeries (if the increment is not constant) to a LoadPattern (page 294) object.
There are many ways to specify the load path.
For a load path where the values are specified at constant time intervals:

Series -dt $dt -values {list_of_values} <-factor $cFactor>
where the values are specified in a list included in the command

Series -dt $dt -filePath $fileName <-factor $cFactor>
where the values are taken from a file specified by $fileName

292

Chapter 26

Time Series

293

For a load path where the values are specified at non-constant time intervals:

Series -time {list_of_times} -values {list_of_values} <-factor $cFactor>
where both time and values are specified in a list included in the command

Series -fileTime $fileName1 -filePath $fileName2 <-factor $cFactor>
where both time and values are taken from a file specified by $fileName1 (for the time data)
and $fileName2 (for the values data)
$cFactor

load-factor coefficient. (optional. default = 1.0)

The load factor to be applied to the loads and constraints in the LoadPattern object is equal to
$cFactor*(user-defined series)

294

CHAPTER 27

pattern Command
The pattern command is used to construct a LoadPattern object, its associated with the
TimeSeries (page 288) object and the Load (page 295) and Constraint (page 316) objects for the
pattern.

In This Chapter
plain Pattern ............................................................. 294
UniformExcitation Pattern......................................... 298
MultipleSupport Pattern ............................................ 299

plain Pattern
This command is used to construct an ordinary LoadPattern (page 294) object in the Domain
(page 30).

pattern Plain $patternTag (TimeSeriesType arguments) {
load (load-command arguments)
sp (sp-command arguments)
eleLoad (eleLoad-command arguments)
}
$patternTag

unique pattern object tag

TimeSeriesType
arguments

list which is parsed to construct the TimeSeries (page 288) object
associated with the LoadPattern object.

load ...

list of commands to construct nodal loads -- the NodalLoad (page
295) object

sp ...

list of commands to construct single-point constraints -- the
SP_Constraint (page 296) object

eleLoad ...

list of commands to construct element loads -- the eleLoad (page
297) object

Chapter 27

pattern Command

295

NOTE: The TimeSeries object is handled by the Tcl interpreter as a list and can be defined a-priori
and given a variable name.

EXAMPLE
# define LoadPattern 1. impose load in a linear manner

pattern Plain 1 Linear { ;
load 3 100 0. 0. 0. 0. 20.;

# apply force and moment at node 3

}

load Command
This command is used to construct a NodalLoad object.

load $nodeTag (ndf $LoadValues)
The nodal load is added to the LoadPattern being defined in the enclosing scope of the pattern
command.
$nodeTag

node on which loads act

$LoadValues

load values that are to be applied to the node.
Valid range is from 1 through ndf (page 34), the number of nodal
degrees-of-freedom.

EXAMPLE
load 3 100 0. 0. 0. 0. 20.;

# apply force Fx=100 and moment Mz=20 at node 3

Chapter 27

pattern Command

296

sp Command
This command is used to construct a single-point non-homogeneous constraint (SP_Constraint)
object.

sp $nodeTag $DOFtag $DOFvalue
$nodeTag

node on which the single-point constraint acts

$DOFtag

degree-of-freedom at the node being constrained.
Valid range is from 1 through ndf (page 34), the number of nodal
degrees-of-freedom.

$DOFvalue

reference value of the constraint to be applied to the DOF at the
node.

EXAMPLE
sp 3 1 0.1;

# impose displacement Dx=0.1 at node 3

Chapter 27

pattern Command

297

eleLoad Command
The elasticBeamColumn (page 217), forceBeamColumn (nonlinearBeamColumn (page 218)) and
dispBeamColumn (page 223) elements all handle ele loads.

 The syntax for 2D is as follows:

For uniformly-distributed load:

eleLoad -ele $eleTag1 <$eleTag2 ....> -type -beamUniform $Wz <$Wx>

For point load:

eleLoad -ele $eleTag1 $eleTag2 -type -beamPoint $Pz $xL <$Px>

 The syntax for 3D is as follows:

For uniformly-distributed load:

eleLoad -ele $eleTag1 <$eleTag2 ....> -type -beamUniform $Wy $Wz <$Wx>

For point load:

eleLoad -ele $eleTag1 $eleTag2 -type -beamPoint $Py $Pz $xL <$Px>
$eleTag1

previously-defined-element tags

<$eleTag2 .....>

additional previously-defined-element tags (optional)

$Wy

3D: uniformly-distributed load in local y direction

$Wz

2D: uniformly-distributed load in direction perpendicular to
element longitudinal axis
3D: uniformly-distributed load in local z direction

Chapter 27

pattern Command

$Wx

uniformly-distributed load in direction parallel to element
longitudinal axis

$Py

3D: point load in local y direction

$Pz

2D: point load in direction perpendicular to element longitudinal
axis

298

3D: point load in local z direction
$xL

location of point load, prescribed as fraction of element length

$Px

point load in direction longitudinal to element longitudinal axis
(applied at the same location as $Pz)

were x axis is along the member.

NOTE: the forceBeamColumn (nonlinearBeamColumn (page 218)) element might have problems
converging; the current code needs to be redone, 'MICHAEL' has promised to get around to it.

UniformExcitation Pattern
This command is used to construct a UniformExcitation load pattern object.

pattern UniformExcitation $patternTag $dir -accel (TimeSeriesType arguments)
<-vel0 $ver0>
$patternTag

unique pattern object tag

$dir

direction of excitation (1, 2, or 3) used in formulating the
inertial loads for the transient analysis.

TimeSeriesType
arguments

TimeSeries (page 288) object associated with the acceleration
record used in determining the inertial loads.

$vel0

initial velocity to be assigned to each node (optional, default:
zero)

NOTE: The TimeSeries object is handled by the Tcl interpreter as a list and can be defined a-priori
and given a variable name.
EXAMPLE:

Chapter 27

pattern Command

299

set Gaccel "Series -dt $dt -filePath $outFile -factor $GMfatt"; # time series information
pattern UniformExcitation 2 1 -accel $Gaccel;
with IDtag 2 in direction 1

# create uniform excitation

MultipleSupport Pattern
This command is used to construct a MultipleSupportExcitation load pattern object.

pattern MultipleSupport $patternTag {
groundMotion (groundMotion-command arguments)
imposedMotion (imposedMotion-command arguments)
}
$patternTag

unique pattern object tag

groundMotion ...

list of commands to construct the GroundMotions (page 299)
object that is then added to the object to define the
multiple-support excitation that is being imposed on the model

imposedMotion ...

list of commands to construct the ImposedSupportSP (page 301)
constraint object that is then added to the object to define the
multiple-support excitation that is being imposed on the model

groundMotion Command
The groundMotion command is used to construct a GroundMotion object used by the
ImposedMotionSP (page 301) constraints in a MultipleSupportExcitation (page 299) object.

Chapter 27

pattern Command

300

Plain GroundMotion
This command is used to construct a plain GroundMotion object. Each GroundMotion object is
associated with a number of TimeSeries (page 288) objects, which define the acceleration,
velocity and displacement records.

groundMotion $gMotionTag Plain <-accel (accelSeriesType accelArgs)> <-vel
(velSeriesType velArgs)> <-disp (dispSeriesType dispArgs)> <-int
(IntegratorType intArgs)>
$gMotionTag

unique GroundMotion (page 299) object tag

<-accel (accelSeriesType accelArgs)>
TimeSeries (page 288) objects defining the acceleration record
(optional).
<-vel (velSeriesType velArgs)>
TimeSeries (page 288) objects defining the velocity record (optional)
<-disp (dispSeriesType dispArgs)>
TimeSeries (page 288) objects defining the displacement record
(optional)
<-int (IntegratorType intArgs)>
If only the acceleration record is specified, the user has the option of
specifying the TimeSeriesIntegrator (page 333) that is to be used to
integrate the acceleration record to determine the velocity and
displacement record (optional, default: Trapezoidal)
NOTE: The TimeSeries object is handled by the Tcl interpreter as a list and can be defined
a-priori and given a variable name.
NOTE: Any combination of the acceleration, velocity and displacement time-series can be
specified.

Chapter 27

pattern Command

301

Interpolated GroundMotion
This command is used to construct an InterpolatedGroundMotion object.

groundMotion $gMotionTag Interpolated $gmTag1 $gmTag2 ... -fact $fact1
$fact2 ...

$gMotionTag

unique GroundMotion (page 299) object tag

$gmTag1 $gmTag2
...

ground motions which have already been added to the
MultipleSupportExcitation (page 299) object.

$fact1 $fact2 ...

factors that are used in the interpolation of the ground motions to
determine the ground motion for this InterpolatedGroundMotion
object.

imposedMotion Command
This command is used to construct an ImposedMotionSP constraint which is used to enforce the
response of a dof at a node in the model. The response enforced at the node at any give time is
obtained from the GroundMotion (page 299) object associated with the constraint.

imposedMotion $nodeTag $dirn $gMotionTag
$nodeTag

node where response is enforced

$dirn

dof of enforced response
Valid range is from 1 through ndf (page 34), the number of nodal
degrees-of-freedom.

$gMotionTag

pre-defined GroundMotion (page 299) object tag

NOTE: The GroundMotion (page 299) object must be added to the MultipeSupportExcitation
(page 299) pattern before the ImposedMotionSP constraint.

Chapter 27

FMK: ADD TIME-SERIES INTEGRATORS

pattern Command

302

303

CHAPTER 28

Recorder Objects
The recorder commands are used to construct a Recorder object, which is used to monitor items
of interest to the analyst at each commit().

In This Chapter
Node Recorder......................................................... 303
EnvelopeNode Recorder .......................................... 305
Drift Recorder........................................................... 306
Element Recorder .................................................... 307
EnvelopeElement Recorder...................................... 309
Display Recorder...................................................... 310
Plot Recorder ........................................................... 311
playback Command.................................................. 311

Node Recorder
The Node type records the displacement, velocity, acceleration and incremental displacement at
the nodes (translational & rotational)

recorder Node <-file $fileName> <-xml $fileName> <-time> <-node ($node1
$node2 ...)> <-nodeRange $startNode $endNode> <-region
$RegionTag> <-node all> -dof ($dof1 $dof2 ...) $respType
-file

output recorder data to a file

-xml

output recorder data + xml metadata labelling
each column of data (-file and -xml cannot be
specified symultaneously)

$fileName

file where results are stored. Each line of the file
contains the result for a committed state of the
domain (optional, default: screen output)

-time

this argument will place the pseudo time of the
as the first entry in the line. (optional, default:
omitted)

$node1 $node2 ...

tags nodes where response is being recorded -select nodes in domain (optional, default: all)

Chapter 28

Recorder Objects

$startNode
$endNode

tag for start and end nodes where response is
being recorded -- range of nodes in domain
(optional, default: all)

$RegionTag

tag for previously-defined selection of nodes
defined using the Region command. (optional)

all

record all nodes in model. (Note: This option is
recommended only for xml option as OpenSees
renumbers nodes)

$dof1 $dof2 ...

degrees of freedom of response being
recorded.

304

Valid range is from 1 through ndf (page 34) , the
number of nodal degrees-of-freedom.
$respType

defines response type to be recorded. The
following response types are available:
disp

displacement*

vel

velocity*

accel

acceleration*

incrDisp

incremental displacement

"eigen i"

eigenvector for mode i

reaction

nodal reaction

NOTE: $respType must be the last argument in this command.
Do not forget the double quote in the eigen response type.
*NOTE:
1.The all option has been removed from the documentation, as OpenSees renumbers the nodes
that are output.
2. For transient analysis, the response output recorded depends on the input:
UniformExcitation (page 298) Pattern(input acceleration
record):

Relative (wrt supports) disp, vel and accel

MultipleSupport (page 299)Pattern (input displacement
record):

Absolute disp, vel and accel

Example:

Chapter 28

Recorder Objects

305

recorder Node -file nodeDisp.out –time –node 1 5 -nodeRange 10 25 -dof 2 disp
recorder Node -file node34.eig -time -node 3 4 -dof 1 2 3 "eigen 2"
recorder Node -file Rnode.out -time -node 1 3 5 -dof 1 2 reaction

EnvelopeNode Recorder
The Node type records the envelope of displacement, velocity, acceleration and incremental
displacement at the nodes (translational & rotational). The envelope consists of the following:
minimum, maximum and maximum absolute value of specified response type.

recorder EnvelopeNode <-file $fileName> <-node ($node1 $node2 ...)>
<-nodeRange $startNode $endNode> <-region $RegionTag> <-node
all> -dof ($dof1 $dof2 ...) $respType
$fileName

file where results are stored. Each line of the file contains the
result for a committed state of the domain (optional, default:
screen output)

$node1 $node2 ...

where response is being recorded -- select nodes (optional,
default: all)

$startNode
$endNode

tag for start and end where response is being recorded (optional,
default: all)

$RegionTag

tag for previously-defined selection of nodes defined using the
Region command. (optional)

all

where response is being recorded -- all nodes in domain
(optional & default)

$dof1 $dof2 ...

degrees of freedom of response being recorded.
Valid range is from 1 through ndf (page 34) , the number of nodal
degrees-of-freedom.

$respType

defines response type to be recorded. The following response
types are available:
disp

displacement

vel

velocity

accel

acceleration

incrDisp

incremental displacement

NOTE: $respType must be the last argument in this command.

Chapter 28

Recorder Objects

306

Example:
recorder EnvelopeNode -file EnvelopeNode.out –time –node 1 5 -nodeRange 10 25 -dof 2 disp

Drift Recorder
The Drift type records the displacement drift between two nodes. The drift is taken as the ratio
between the prescribed relative displacement and the specified distance between the nodes.

recorder Drift -file $fileName <-time> -iNode ($inode1 $inode2 ...) -jNode
($jnode1 $jnode2 ...) -dof ($dof1 $dof2 ...) -perpDirn ($perpDirn1
$perpDirn2 ...)

$fileName

file where results are stored. Each line of the file contains the
result for a committed state of the domain

-time

this argument will place the pseudo time of the as the first entry in
the line. (optional, default: omitted)

($inode1 $inode2
...)

set of i nodes for which drift is recorded

($jnode1 $jnode2
...)

set of j nodes for which drift is recorded

($dof1 $dof2 ...)

set of nodal degrees of freedom to monitor for drift
Valid range is from 1 through ndm (page 34), the number of nodal
degrees-of-freedom.

($perpDirn1
$perpDirn2 ...)

set of perpendicular global directions from which length is
determined to compute drift (1 = X, 2 = Y, 3 = Z)

Example:
recorder Drift -file drift.out -time -iNode 1 2 -jNode 3 4 -dof 1 -perpDirn 2

Chapter 28

Recorder Objects

307

Element Recorder
The Element type records the response of a number of elements. The response recorded is
element-dependent and depends on the arguments which are passed to the setResponse()
element method.

recorder Element <-file $fileName> <-time> <-ele ($ele1 $ele2 ...)> <-eleRange
$startEle $endEle> <-region $regTag> <-ele all> ($arg1 $arg2 ...)

-file

output recorder data to a file

-xml

output recorder data + xml metadata labelling each column of
data (-file and -xml cannot be specified symultaneously)

$filename

file where results are stored. Each line of the file contains the
result for a committed state of the domain (optional, default:
screen output)

-time

this argument will place the pseudo time of the as the first entry in
the line. (optional, default: omitted)

$ele1 $ele2 ...

tags of elements whose response is being recorded -- selected
elements in domain (optional, default: omitted)

$startEle $endEle

tag for start and end elements whose response is being recorded
-- range of selected elements in domain (optional, default: all)

$regTag

previously-defined tag of region of elements whose response is
being recorded -- region of elements in domain (optional)

all

elements whose response is being recorded -- all elements in
domain (optional & default)

$arg1 $arg2 ...

arguments which are passed to the setResponse() element
method

The setResponse() element method is dependent on the element type, and is described with the
element Command (page 215).

 Beam-Column Elements (page 219, page 223, page 217, page 218) :
Common to all beam-column elements:
globalForce – element resisting force in global coordinates (does not include inertial forces)
example:
recorder Element -file ele1global.out -time -ele 1 globalForce
localForce – element resisting force in local coordinates (does not include inertial forces)

Chapter 28

Recorder Objects

308

example:
recorder Element -file ele1local.out -time -ele 1 localForce

 Sections: (page 191)
section $secNum – request response quantities from a specific section along the element length,
$secNum refers to the integration point whose data is to be output
force – section forces
example: recorder Element -file ele1sec1Force.out –time -ele 1 section 1 force
deformation – section deformations
example: recorder Element -file ele1sec1Defo.out –time -ele 1 section 1 deformation
stiffness – section stiffness
example: recorder Element -file ele1sec1Stiff.out –time -ele 1 section 1 stiffness
stressStrain – record stress-strain response.
example: recorder Element -file ele1sec1StressStrain.out –time -ele 1 section 1 fiber $y $z
<$matID> stressStrain
$y

local y coordinate of fiber to be monitored*

$z

local z coordinate of fiber to be monitored*

$matID

previously-defined material tag (optional)

*NOTE: The recorder object will search for the fiber closest to the location ($y,$z) on the section
and record its stress-strain response
NOTE: the ZeroLength section element (page 226) only has 1 section therefore you do not need
to identify the section in the recorder command .. Example:
recorder Element -file Element1.out -time -ele 1 section 1 fiber 0.10 0.10 stressStrain
OUTPUT FORMAT
The format of the output is typically dependent on the element and/or section type. In general,
however, the output follows the order of the degrees of freedom.
Here are some cases:
element

globalForce

2D, 3dof: FX FY MZ
3D, 6dof: FX FY FZ MX MY MZ

localForce

2D, 3dof: Fx Fy Mz
3D, 6dof: Fx Fy Fz Mx My Mz

section

force

Fx Mx

Chapter 28

deformation

axial-strain curvature

stressStrain

stress strain

Recorder Objects

309

EnvelopeElement Recorder
The Element type records the response of a number of elements. The response recorded is
element-dependent and depends on the arguments which are passed to the setResponse()
element method. The envelope consists of the following: minimum, maximum and maximum
absolute value of specified response type.

recorder EnvelopeElement <-file $fileName> <-ele ($ele1 $ele2 ...)> <-eleRange
$startele $endele> <-ele all> <-region $regTag> ($arg1 $arg2 ...)
$fileName

file where results are stored. Each line of the file contains the
result for a committed state of the domain (optional, default:
screen output)

$eleID1 $eleID2 ...

tags of elements whose response is being recorded -- selected
elements in domain (page 30) (optional, default: omitted)

$startele $endele

tag for start and end elements whose response is being recorded
-- selected elements in domain (page 30) (optional, default: all)

all

elements whose response is being recorded -- all elements in
domain (page 30) (optional & default)

$regTag

tag of region of elements whose response is being recorded -region of elements in domain (page 30) (optional)

$arg1 $arg2 ...

arguments which are passed to the setResponse() element
method

The setResponse() element method is dependent on the element type, and is described with the
element Command (page 215).

 Beam-Column Elements (page 219, page 223, page 217, page 218) :
Common to all beam-column elements:
globalForce – element resisting force in global coordinates (does not include inertial forces)
example:
recorder EnvelopeElement -file ele1global.out -time -ele 1 globalForce

Chapter 28

Recorder Objects

310

localForce – element resisting force in local coordinates (does not include inertial forces)
example:
recorder EnvelopeElement -file ele1local.out -time -ele 1 localForce

 Sections: (page 191)
section $secNum – request response quantities from a specific section along the element length,
$secNum refers to the integration point whose data is to be output
force – section forces
example: recorder EnvelopeElement -file ele1sec1Force.out –time -ele 1 section 1 force
deformation – section deformations
example: recorder EnvelopeElement -file ele1sec1Force.out –time -ele 1 section 1 deformation
stiffness – section stiffness
example: recorder EnvelopeElement -file ele1sec1Force.out –time -ele 1 section 1 stiffness
stressStrain – record stress-strain response.
example: recorder EnvelopeElement -file ele1sec1Force.out –time -ele 1 section 1 fiber $y $z
stressStrain
$y

local y coordinate of fiber to be monitored*

$z

local z coordinate of fiber to be monitored*

*NOTE: The recorder object will search for the fiber closest to the location ($y,$z) on the section
and record its stress-strain response
NOTE: the ZeroLength section element (page 226) only has 1 section therefore you do not need
to identify the section in the recorder command .. Example:
recorder Element -file Element1.out -time -ele 1 section fiber 0.10 0.10 stressStrain

Display Recorder
This recorder opens a graphical window for displaying of graphical information.

recorder display $windowTitle $xLoc $yLoc $xPixels $yPixels <-file $fileName>
$windowTitle

title of graphical window

$xLoc $yLoc

horizontal and vertical location of graphical window (upper
left-most corner)

Chapter 28

Recorder Objects

$xPixels $yPixels

width and height of graphical window in pixels

$fileName

in addition to the window display, information is sent to a file to
redisplay images at a later time. (optional)

311

A TclFeViewer object is constructed. This constructor adds a number of additional commands to
OpenSees, similar to the construction of the BasicBuilder (page 34). These additional commands
are used to define the viewing system for the image that is place on the screen. These commands
are currently under review and will be presented in a future version of this document.

Plot Recorder
This recorder type opens a graphical window for the plotting of the contents of the prescribed file

recorder plot $fileName $windowTitle $xLoc $yLoc $xPixels $yPixels -columns
$xCol0 $yCol0 <-columns $xCol1 $yCol1><-columns $xCol2 $yCol2> ...
$fileName

source file of plotted data

$windowTitle

title of graphical window

$xLoc $yLoc

horizontal and vertical location of graphical window in pixels
(upper left-most corner)

$xPixels $yPixels

width and height of graphical window in pixels

$xCol0 $yCol0

Column number to be plotted in X-axis and Y-axis, respectively.
One set of columns must be defined.

$xCol1 $yCol1

Additional lines may be plotted on the same graph by repeating
the -columns command. These data come from the same source
file. (optional)

$xCol2 $yCol2

playback Command
This command is used to invoke playback on all Recorder objects constructed with the recorder
command (page 303).

playback $commitTag
$commitTag

integer used to invoke the record() method (????)

Chapter 28

Recorder Objects

312

313

CHAPTER 29

Analysis Objects
The Analysis objects are responsible for performing the analysis. The analysis moves the model
along from state at time t to state at time t + dt. This may vary from a simple static (page 339) linear
analysis to a transient (page 340, page 341) non-linear analysis. In OpenSees each Analysis
object is composed of several component objects, which define the type of analysis how the
analysis is performed.
In general terms, the analysis objects are used to solve the following time-dependent
equilibrium-equation problem for a transient analysis:

-- transient equilibrium
Where FI is the acceleration-dependent inertial force vector, FR is the velocity (damping) and
displacement-dependent (stiffness) resisting-force vector. P(t) is the external applied-force vector.
The acceleration, velocity and displacement vectors are all time-dependent.
The component classes consist of the following:

ConstraintHandler (page 316) -- determines how the constraint equations are enforced in
the analysis -- how it handles the boundary conditions/imposed displacements

DOF_Numberer (page 321) -- determines the mapping between equation numbers and
degrees-of-freedom
AnalysisModel (page 339) -- defines what time of analysis is to be performed

Integrator -- determines the predictive step for time t+dt

SolutionAlgorithm (page 329) -- determines the sequence of steps taken to solve the
non-linear equation at the current time step
SystemOfEqn/Solver -- within the solution algorithm, it specifies how to store and solve the
system of equations in the analysis

Chapter 29

Figure 61: Analysis Object

In This Chapter
constraints Command .............................................. 316
numberer Command ................................................ 321
system Command .................................................... 323
test Command.......................................................... 326
algorithm Command ................................................. 329
integrator Command................................................. 333
analysis Command................................................... 339
rayleigh command .................................................... 342
eigen Command....................................................... 343
analyze Command ................................................... 344
dataBase Commands............................................... 345

Analysis Objects

314

Chapter 29

Analysis Objects

315

316

CHAPTER 30

constraints Command
This command is used to construct the ConstraintHandler object. The ConstraintHandler object
determines how the constraint equations are enforced in the analysis. Constraint equations
enforce a specified value for a DOF, or a relationship between DOFs. The degrees of freedom can
be broken down into UR, the retained DOF's, and UC, the condensed DOF's:

Chapter 30

constraints Command

317

The Plain Constraints (page 318) command is used to enforce homogeneous single-point
constraints, such as the case of homogeneous boundary conditions, where all boundary
conditions are fixity, using single-point constraints (page 38, http://www.). For this case: UC=0.0

The other constraints commands are used for ALL other cases, such as the case of
non-homogeneous single-point constraints using the sp command (page 296), multi-point
constraints (page 41), imposed motions (page 301) and multi-support excitation (page 299). For
such cases, the relationship between DOF's can be written as:UC=CRCUR. Where CRC is a matrix of
constants.
The following constraints handlers are currently availble:

Penalty Method (page 318) -- consists of adding large numbers to the stiffness matrix and
the restoring-force vectors to impose a prescribed zero or nonzero DOF. This method applies
very stiff elements (numerically) at the boundary conditions. These additional stiffnesses affect
the eigenvalues/eigenvectors in a transient analysis. This is the recommended method for a
static analysis.
Lagrange Multipliers (page 319) -- apply the method of lagrange multipliers to the system of
equations, thus enlarging the size of the materices. Once Labrange Multipliers have been
applied, the resulting stiffness matrix is no longer positive definite. Therefore, this method
should be used only if there are condition-number problems with the penalty method.
Transformation Method (page 320) -- transforms the stiffness matrix by condensing out the
constrained DOF's. This method reduces the size of the system for multi-point constraints.
This is the recommended method for a transient analysis. However, this method should not be
used when nodes are constrained in series. For example, U3 is constrained to U2, which is then
constrained to U1.

Of the different methods, "the Lagrange multiplier method is more attractive than the
transformation method if there are few constraint equations that couple many DOF. However,
Lagrange multipliers are active at the structure level, but transformation equations can be applied
at either the structure level or element by element. The latter has the appeal of disposing of
constraints at an early stage, when the matrices are small and manageable". (Cook)
"In comparison with Lagrange multipliers, penalty functions have the advantage of introducing no
new variables. However, the penalty matrix may significantly increase the bandwidth of the
structural equations, depending on how DOF are numbered and what DOF are coupled by the
constraint equations. Penalty functions have the disadvantage that penalty numbers must be
chosen in an allowable range: large enough to be effective but not so large as to provoke
numerical difficulties". (Cook)
More information and examples on these methods are discussed in detail in the Cook book.

Chapter 30

constraints Command

318

In This Chapter
Plain Constraints ...................................................... 318
Penalty Method ........................................................ 318
Lagrange Multipliers ................................................. 319
Transformation Method ............................................ 320

Plain Constraints
This command creates a PlainHandler which is only capable of enforcing homogeneous
single-point constraints. If other types of constraints exist in the domain, a different constraint
handler must be specified.

constraints Plain

Penalty Method
This command is used to construct a PenaltyConstraintHandler which will cause the constraints to
be enforced using a penalty method. The penalty method consists of adding large numbers to the
stiffness matrix and the restoring-force vectors to impose a prescribed zero or nonzero DOF.

constraints Penalty $alphaSP $alphaMP
$alphaSP

factor used when adding the single-point constraint into the
system of equations

$alphaMP

factor used when adding the multi-point constraint into the
system of equations

In this method the potential-energy equation which makes up the system of equations is
augmented by a penalty function {t}T[alpha]{t}/2
where [alpha] is a diagonal matrix of "penalty numbers". The resulting system of equations is of
the form:
[K + CTalphaC]U = [R+CTalphaQ]

Chapter 30

constraints Command

319

Where CTalphaC can be called the penalty matrix. C and Q are matrices containing constants, K is
the stiffness matrix, U represents the DOF and R the restoring forces. If alpha=0 the constraints
are ignored. As alpha grows, U changes in such a way that the constraint equations are more
nearly satisfied. In this case, however, the analysis becomes error prone, as the system
represents a stiff region supported by a flexible region.
NOTE: The Penalty Method affects the maximum eigenvalues of the system and may cause
problems in a Transient analysis.
The Penalty Method is discussed in detail in the Cook Book -- Concepts and Applications of Finite
Element Analysis.
"Guideline for choice of alpha: If computer words carry approximately p decimal digits, experience
has shown that alpha should not exceed 10p/2". (Cook)

Lagrange Multipliers
This command is used to construct a LagrangeConstraintHandler which will cause the constraints
to be enforced using the method of Lagrange multipliers.

constraints Lagrange <$alphaSP> <$alphaMP>
$alphaSP

factor used when adding the single-point constraint into the
system of equations (optional, default=1.0)

$alphaMP

factor used when adding the multi-point constraint into the
system of equations (optional, default=1.0)

NOTE: Values for $alphaSP and $alphaMP other than 1.0 are permitted to offset numerical
roundoff problems.
NOTE: The system of equations is not positive definite due to the introduction of zeroes on the
diagonal by the constraint equations:

From Cook: "Lagrange's method of undetermined multipliers is used to find the maximum or
minimum of a function whose variables are not independent but have some prescribed relation. In
structural mechanics the function is the potential energy and the variables are the DOF".

Chapter 30

constraints Command

320

Transformation Method
This command is used to construct a TransofrmationConstraintHandler which will cause the
constraints to be enforced using the transformation method.

constraints Transformation
NOTE: With the current implementation, a retained node in an MP_Constraint cannot also be
specified as being a constrained node in another MP_Constraint.
The constraint equations takes the following form:

321

CHAPTER 31

numberer Command
This command is used to construct the DOF_Numberer object. The DOF_Numberer object
determines the mapping between equation numbers and degrees-of-freedom -- how
degrees-of-freedom are numbered.

Plain (page 321) -- nodes are assigned degrees-of-freedom arbitrarily, based on the input file.
This method is recommended for small problems or when sparse solvers are used, as they do
their own internal DOF numbering.

RCM (page 322) -- nodes are assigned degrees-of-freedom using the Reverse Cuthill-McKee
algorithm. This algorithm optimizes node numbering to reduce bandwidth using a numbering
graph. This method will output a warning when the structure is disconnected.

As certain system of equation and solver objects do their own mapping, i.e. SuperLU, UmfPack,
Kincho's, specifying a numberer other than plain may not be needed.

In This Chapter
Plain Numberer ........................................................ 321
RCM Numberer ........................................................ 322

Plain Numberer
This command is used to construct a PlainNumberer object.

numberer Plain
The Plain numberer assigns degrees-of-freedom to the nodes based on how the nodes are stored
in the domain. Currently, the user has no control over how nodes are stored.

Chapter 31

numberer Command

322

RCM Numberer
This command is used to construct a RCMNumberer object.

numberer RCM
The RCM numberer uses the reverse Cuthill McKee (REF?) algorithm to number the degrees of
freedom.

323

CHAPTER 32

system Command
This command is used to construct the LinearSOE and LinearSolver objects to store and solve the
system of equations in the analysis.

Figure 62: system command

In This Chapter
BandGeneral SOE.................................................... 324
BandSPD SOE......................................................... 324
ProfileSPD SOE ....................................................... 324
SparseGeneral SOE................................................. 324
UmfPack SOE .......................................................... 325
SparseSPD SOE ...................................................... 325

Chapter 32

system Command

324

BandGeneral SOE
This command is used to construct an un-symmetric banded system of equations object which will
be factored and solved during the analysis using the Lapack band general solver.

system BandGeneral

BandSPD SOE
This command is used to construct a symmetric positive definite banded system of equations
object which will be factored and solved during the analysis using the Lapack band spd solver.

system BandSPD

ProfileSPD SOE
This command is used to construct symmetric positive definite profile system of equations object
which will be factored and solved during the analysis using a profile solver.

system ProfileSPD

SparseGeneral SOE
This command is used to construct a general sparse system of equations object which will be
factored and solved during the analysis using the SuperLU solver.

system SparseGeneral <-piv>
-piv

perform partial-pivoting (optional, Default: no partial pivoting is
performed)

Chapter 32

system Command

325

UmfPack SOE
This command is used to construct a general sparse system of equations object which will be
factored and solved during the analysis using the UMFPACK solver. (REF?)

system UmfPack

SparseSPD SOE
This command is used to construct a sparse symmetric positive definite system of equations
object which will be factored and solved during the analysis using a sparse solver developed at
Stanford University by Kincho Law. (REF?)

system SparseSPD

326

CHAPTER 33

test Command
This command is used to construct a ConvergenceTest object. Certain SolutionAlgorithm (page
329) objects require a ConvergenceTest object to determine if convergence has been achieved at
the end of an iteration step. The convergence test is applied to the following equation:

The test perform the following checks:

Norm Unbalance

Norm Displacement
Increment
Energy Increment

In This Chapter
Norm Unbalance Test .............................................. 326
Norm Displacement Increment Test ......................... 327
Energy Increment Test ............................................. 328

Norm Unbalance Test
This command is used to construct a CTestNormUnbalance object which tests positive force
convergence if the 2-norm of the b vector (the unbalance) in the LinearSOE (page 323) object is
less than the specified tolerance.

test NormUnbalance $tol $maxNumIter <$printFlag>
$tol

convergence tolerance

$maxNumIter

maximum number of iterations that will be performed before
"failure to converge" is returned

$printFlag

flag used to print information on convergence (optional)

Chapter 33

test Command

0

no print output (default)

1

print information on each step

2

print information when convergence has been achieved

4

print norm, dU and dR vectors

5

at convergence failure, carry on, print error message,
but do not stop analysis

327

The test performs the following check:

Norm Displacement Increment Test
This command is used to construct a CTestNormDispIncr object which tests positive force
convergence if the 2-norm of the x vector (the displacement increment) in the LinearSOE (page
323) object is less than the specified tolerance.

test NormDispIncr $tol $maxNumIter <$printFlag>
$tol

convergence tolerance

$maxNumIter

maximum number of iterations that will be performed before
"failure to converge" is returned

$printFlag

flag used to print information on convergence (optional)
0

no print output (default)

1

print information on each step

2

print information when convergence has been achieved

4

print norm, dU and dR vectors

5

at convergence failure, carry on, print error message,
but do not stop analysis

The test performs the following check:

Chapter 33

test Command

328

Energy Increment Test
This command is used to construct a CTestEnergyIncr object which tests positive force
convergence if one half of the inner-product of the x and b vectors (displacement increment and
unbalance) in the LinearSOE (page 323) object is less than the specified tolerance.

test EnergyIncr $tol $maxNumIter <$printFlag>
$tol

convergence tolerance

$maxNumIter

maximum number of iterations that will be performed before
"failure to converge" is returned

$printFlag

flag used to print information on convergence (optional)
0

no print output (default)

1

print information on each step

2

print information when convergence has been achieved

4

print norm, dU and dR vectors

5

at convergence failure, carry on, print error message,
but do not stop analysis

The test performs the following check:

329

CHAPTER 34

algorithm Command
This command is used to construct a SolutionAlgorithm object, which determines the sequence of
steps taken to solve the non-linear equation.

In This Chapter
Linear Algorithm ....................................................... 329
Newton Algorithm ..................................................... 329
Newton with Line Search Algorithm .......................... 330
Modified Newton Algorithm....................................... 331
Krylov-Newton Algorithm .......................................... 331
BFGS Algorithm ....................................................... 331
Broyden Algorithm.................................................... 332

Linear Algorithm
This command is used to construct a Linear algorithm object which takes one iteration to solve the
system of equations.

algorithm Linear

Newton Algorithm
This command is used to construct a NewtonRaphson algorithm object which uses the
Newton-Raphson method to advance to the next time step.

algorithm Newton
NOTE: The tangent is updated at each iteration.

Chapter 34

algorithm Command

Newton with Line Search Algorithm
This command is used to construct a NewtonLineSearch algorithm object which uses the
Newton-Raphson method with line search to advance to the next time step.

algorithm NewtonLineSearch $ratio
$ratio

limiting ratio between the residuals before and after the
incremental update (between 0.5 and 0.8)
If the ratio between the residuals before and after the incremental
update is greater than the specified limiting ratio the line search
algorithm developed by Crissfield (REF?) is employed to try to
improve the convergence.

330

Chapter 34

algorithm Command

331

Modified Newton Algorithm
This command is used to construct a ModifiedNewton algorithm object which uses the Modified
Newton-Raphson method to advance to the next time step. The difference between this method
and the Newton-Raphson method is that the tangent stiffness is not updated at each step, thus
avoiding expensive calculations needed in multi-DOF systems. However, more iterations may be
needed to reach a prescribed accuracy.

algorithm ModifiedNewton
NOTE: The tangent at the first iteration of the current time step is used to iterate on the next time
step.

Krylov-Newton Algorithm
This command is used to construct a KrylovNewton algorithm object which uses a modified
Newton method with Krylov subspace acceleration to advance to the next time step.

algorithm KrylovNewton
The accelerator is described by Carlson and Miller in "Design and Application of a 1D GWMFE
Code" from SIAM Journal of Scientific Computing
(http://epubs.siam.org/sam-bin/dbq/toclist/SISC) (Vol. 19, No. 3, pp. 728-765, May 1998).

BFGS Algorithm
This command is used to construct a BFGS algorithm object for symmetric systems which
performs successive rank-two updates of the tangent at the first iteration of the current time step.

algorithm BFGS <$count>
$count

number of iterations within a time step until a new tangent is
formed

Chapter 34

algorithm Command

332

Broyden Algorithm
This command is used to construct a Broyden algorithm object for general unsymmetric systems
which performs successive rank-one updates of the tangent at the first iteration of the current time
step.

algorithm Broyden <$count>
$count

number of iterations within a time step until a new tangent is
formed

333

CHAPTER 35

integrator Command
This command is used to construct the Integrator object. The Integrator object determines the
meaning of the terms in the system of equation object Ax=B.
The Integrator object is used for the following:

determine the predictive step for time t+dt
specify the tangent matrix and residual vector at any iteration

determine the corrective step based on the displacement increment dU

The system of nonlinear equations is of the form:

Static analysis:
Transient analysis:

Chapter 35

integrator Command

334

The type of integrator used in the analysis is dependent on whether it is a static analysis (page
339) or transient analysis (page 340):

STATIC ANALYSIS*

LoadControl (page
334)

DisplacementControl
(page 335)

MinUnbalDispNorm
(page 336)
ArcLength (page 336)

TRANSIENT ANALYSIS

Newmark (page 337)

Hilbert-Hughes-Taylor Method (HHT (page 338))

*NOTE: static integrators should only be used with a Linear TimeSeries (page 289) object with a
factor of 1.0.

In This Chapter
Load Control............................................................. 334
Displacement Control ............................................... 335
Minimum Unbalanced Displacement Norm............... 336
Arc-Length Control ................................................... 336
Newmark Method ..................................................... 337
Hilbert-Hughes-Taylor Method.................................. 338

Load Control
This command is used to construct a StaticIntegrator object of type LoadControl

integrator LoadControl $dLambda1 <$Jd $minLambda $maxLambda>

Chapter 35

integrator Command

$dLambda1

first load increment (pseudo-time step) in the next invocation of
the analysis (page 339) command.

$Jd

factor relating load increment at subsequent time steps.
(optional, default: 1.0)

$minLambda
$maxLambda

arguments used to bound the load increment (optional, default:
$dLambda1 for both)

335

The load increment at iterations i, dLambda(i), is related to the load increment at (i-1),
dLambda(i-1), and the number of iterations at (i-1), J(i-1), by the following:
dLambda(i) = dLambda(i-1)*Jd/J(i-1)

Displacement Control
This command is used to construct a StaticIntegrator object of the type DisplacementControl.

integrator DisplacementControl $nodeTag $dofTag $dU1 <$Jd $minDu
$maxDu>
$nodeTag

node whose response controls the solution

$dofTag

degree-of-freedom whose response controls the solution.
Valid range is from 1 through ndf (page 34), the number of nodal
degrees-of-freedom.

$dU1

first displacement increment (pseudo-time step) in the next
invocation of the analysis command

$Jd

factor relating displacement increment at subsequent time steps.
(optional, default: 1.0)

$minDu $maxDu

arguments used to bound the displacement increment (optional,
default: $dU1 for both)

The displacement increment at iterations i, dU(i), is related to the displacement increment at (i-1),
dU(i-1), and the number of iterations at (i-1), J(i-1), by the following:
dU(i) = dU(i-1)*Jd/J(i-1)

Chapter 35

integrator Command

336

Minimum Unbalanced Displacement Norm
This command is used to construct a StaticIntegrator object of type MinUnbalDispNorm.

integrator MinUnbalDispNorm $dlambda11 <$Jd $minLambda $maxLambda>
$dLambda11

first load increment (pseudo-time step) at the first iteration in the
next invocation of the analysis (page 339) command.

$Jd

factor relating first load increment at subsequent time steps.
(optional, default: 1.0)

$minLambda
$maxLambda

arguments used to bound the load increment (optional, default:
$dLambda11 for both)

The load increment at iterations i, dLambda1(i), is related to the load increment at (i-1),
dLambda1(i-1), and the number of iterations at (i-1), J(i-1), by the following:
dLambda1(i) = dLambda1(i-1)*Jd/J(i-1)

Arc-Length Control
This command is used to construct a StaticIntegrator object of type ArcLength. Arc-length
methods are used to enable the solution algorithm to pass limit points, such as maximum and
minimum loads, and snap-through and snap-back responses. At these limit points, the stability of
the numerical system is dependent on whether the analysis is performed under load or
displacement control. In structural analysis, these limit points are characteristic of cracking of
reinforced concrete and of buckling of shells.

integrator ArcLength $arclength $alpha
(??? is this the correct order, at the workshop Frank had it different)
$arclength
$alpha
SEE FMK

arclength value

Chapter 35

integrator Command

337

The equilibrium equation can be written in the from:

the arc-length method aims to find the intersection of the above equation with s=constant, where s
is the arc-length, defined by:

and

the scaling parameter ψ is required because the load contribution depends on the adopted scaling
between the load and displacement terms.
for the arc-length methods, one should replace the differential form of the equation for ds with an
incremental form:
???

where ∆l is the fixed 'radius of the desired intersection.
In the arc-length method the load parameter λ becomes a variable, adding one to the n
displacement variables and equations.

Newmark Method
This command is used to construct a TransientIntegrator object of type Newmark.

integrator Newmark $gamma $beta
$gamma

Newmark parameter γ

$beta

Newmark parameter β

The damping matrix D is specified as a combination of stiffness and mass-proportional damping
matrices:
D = $alphaM * M + $betaK * Kcurrent +$betaKinit * Kinit + $betaKcomm * KlastCommit

Chapter 35

integrator Command

338

The mass and stiffness matrices are defined as:
M

mass matrix used to calculate Rayleigh Damping

Kcurrent

stiffness matrix at current state determination used to calculate
Rayleigh Damping

Kinit

stiffness matrix at initial state determination used to calculate
Rayleigh Damping

KlastCommit

stiffness matrix at last-committed state determination used to
calculate Rayleigh Damping

Note: Damping should be specified using the Rayleigh (page 342) command.

Hilbert-Hughes-Taylor Method
This command is used to construct a TransientIntegrator object of type HHT or HHT1.

integrator HHT $gamma <$alphaM $betaK $betaKinit $betaKcomm>
$gamma

Newmark parameter γ

$alphaM $betaK $betaKinit
$betaKcomm

Arguments to define Rayleigh damping matrix
(optional, default: zero)

The damping matrix D is specified as a combination of stiffness and mass-proportional damping
matrices:
D = $alphaM * M + $betaK * Kcurrent +$betaKinit * Kinit + $betaKcomm * KlastCommit
The mass and stiffness matrices are defined as:
M

mass matrix

Kcurrent

stiffness matrix at current state determination

Kinit

stiffness matrix at initial state determination

KlastCommit

stiffness matrix at last-committed state determination

339

CHAPTER 36

analysis Command
This command is used to construct the Analysis object (page 313), which defines what type of
analysis is to be performed. The following analysis types are available:

Static Analysis (page 339) -- solves the KU=R problem, without the mass or damping matrices.

Transient Analysis (page 340) -- solves the time-dependent analysis. The time step in this type
of analysis is constant. The time step in the output is also constant.

Variable Transient Analysis (page 341) -- performs the same analysis type as the Transient
Analysis object. The time step, however, is variable. This method is used when there are
convergence problems with the Transient Analysis object at a peak or when the time step is
too small. The time step in the output is also variable.

All currently-available analysis objects employ incremental solution strategies.

In This Chapter
Static Analysis.......................................................... 339
Transient Analysis .................................................... 340
VariableTransient Analysis ....................................... 341

Static Analysis
This command is used to construct a StaticAnalysis object.

analysis Static
This analysis object is constructed with the component objects previously created by the analyst. If
none has been created, default objects are constructed and used:
Component Object

Default object

Chapter 36

analysis Command

SolutionAlgorithm
(page 329),
StaticIntegrator (page
335, page 333, page
334, page 336)

NewtonRaphson (page 329) EquiSolnAlgo with a
CTestNormUnbalance (page 326) with a tolerance of 1e-6
and a maximum of 25 iterations

ConstraintHandler
(page 316)

PlainHandler (page 318) ConstraintHandler

DOF_Numberer (page
321)

RCM (page 322) DOF_Numberer

LinearSOE (page 323),
LinearSolver (page
323)

profiled symmetric positive definite (page 324) LinearSOE
and Linear Solver

Integrator

LoadControl StaticIntegrator (page 334) with a constant
load increment of 1.0

340

Transient Analysis
This command is used to construct a DirectIntegrationAnalysis object.

analysis Transient
This analysis object is constructed with the component objects previously created by the analyst. If
none has been created, default objects are constructed and used:
Component Object

Default object

SolutionAlgorithm
(page 329),
TransientIntegrator
(page 333)

NewtonRaphson (page 329) EquiSolnAlgo with a
CTestNormUnbalance (page 326) with a tolerance of 1e-6
and a maximum of 25 iterations

ConstraintHandler
(page 316)

PlainHandler (page 318) ConstraintHandler

DOF_Numberer (page
321)

RCM (page 322) DOF_Numberer

LinearSOE (page 323),
LinearSolver (page
323)

profiled symmetric positive definite (page 324) LinearSOE
and Linear Solver

Chapter 36

Integrator

analysis Command

341

Newmark TransientIntegrator (page 337) with γ=0.5 and
β=0.25

VariableTransient Analysis
This command is used to construct a VariableTimeStepDirectIntegrationAnalysis object.

analysis VariableTransient
This analysis object is constructed with the component objects previously created by the analyst. If
none has been created, default objects are constructed and used:
Component Object

Default object

SolutionAlgorithm
(page 329),
TransientIntegrator
(page 333)

NewtonRaphson (page 329) EquiSolnAlgo with a
CTestNormUnbalance (page 326) with a tolerance of 1e-6
and a maximum of 25 iterations

ConstraintHandler
(page 316)

PlainHandler (page 318) ConstraintHandler

DOF_Numberer (page
321)

RCM (page 322) DOF_Numberer

LinearSOE (page 323),
LinearSolver (page
323)

profiled symmetric positive definite (page 324) LinearSOE
and Linear Solver

Integrator

Newmark TransientIntegrator (page 337) with γ=0.5 and
β=0.25

342

CHAPTER 37

rayleigh command
This command is used to assign damping to all previously-defined elements and nodes:

rayleigh $alphaM $betaK $betaKinit $betaKcomm

The damping matrix D is specified as a combination of stiffness and mass-proportional damping
matrices:
D = $alphaM * M + $betaK * Kcurrent +$betaKinit * Kinit + $betaKcomm * KlastCommit
The mass and stiffness matrices are defined as:
M

mass matrix used to calculate Rayleigh Damping

Kcurrent

stiffness matrix at current state determination used to calculate
Rayleigh Damping

Kinit

stiffness matrix at initial state determination used to calculate
Rayleigh Damping

KlastCommit

stiffness matrix at last-committed state determination used to
calculate Rayleigh Damping

343

CHAPTER 38

eigen Command
This command is used to perform a generalized eigenvalue problem to determine a specified
number of eigenvalues and eigenvectors.

eigen <$type> $numEigenvalues
$type

$numEigenvalues

eigen-value analysis type:
frequency

solve: K- λ M

generalized

solve: K- λ M (default)

standard

solve: K- λ I

number of first eigenvalues (λ) to be determined

The eigenvectors are stored at the nodes and can be printed out using Node Recorder (page 303)
or the Print command (page 347).
NOTE: The current eigensolver is able to solve only for N-1 eigenvalues, where N is the number of
interial DOFs. When running into this limitation, the user should add negligible masses to
additional unrestrained degrees of freedom.
For example, for a 3-dof/node problem, instead of:
mass 1 100 0 0
the user should input:
mass 1 100 1e-9 0
where dof-2 at node 1 is unrestrained.

344

CHAPTER 39

analyze Command
This command is invoked on the Analysis object constructed with the analysis command (page
339).

analyze $numIncr <$dt> <$dtMin $dtMax $Jd>
$numIncr

number of load steps

$dt

time-step increment.
Required if a transient analysis (page 340) or variable time step
transient analysis (page 341) was specified.

$dtMin

$dtMax

minimum and maximum time steps
Required if a variable time step transient analysis (page 341) was
specified.

$Jd

number of iterations performed at each step
Required if a variable time step transient analysis (page 341) was
specified.

This command RETURNS:
0

successful

<0

unsuccessful

345

CHAPTER 40

dataBase Commands
This command is used to construct a FE_Datastore object.
Currently there is only one type of Datastore object available.

In This Chapter
FileDatastore Command........................................... 345

FileDatastore Command
This command is used to construct the FE_Datastore object.

database $type $dbName
$type

$dbName

database type:
File

outputs database into a file

MySQL

creates a SQL database

BerkeleyDB

creates a BerkeleyDB database

database name.
If the database type is File, the command will save the data into a
number of files, e.g. $dbName.id11 for all ID objects of size 11
that sendSelf() is invoked upon.

The invocation of this command will add the additional commands save and restore to the
OpenSees interpreter to allow users to save and restore model states.

Chapter 40

dataBase Commands

save Command
This command is used to save the state of the model in the database.

save $commitTag
$commitTag

unique identifier that can be used to restore (page 346) the state
at a later time

restore Command
This command is used to restore the state of the model from the information stored in the
database.

restore $commitTag
$commitTag

unique identifier used to restore the state at the model when the
save (page 346) command was invoked

346

347

CHAPTER 41

Miscellaneous Commands
These are a few additional miscellaneous command used in OpenSees

In This Chapter
print Command......................................................... 347
reset Command........................................................ 348
wipe Command ........................................................ 348
wipeAnalysis Command ........................................... 348
loadConst Command................................................ 349
getTime Command................................................... 349
nodeDisp Command................................................. 349
video Command ....................................................... 350
nodeBounds ............................................................. 351
display Command..................................................... 352

print Command
This command is used to print output.
To print all objects of the domain:

print <$fileName>
To print node information:

print <$fileName> -node <-flag $flag> <$node1 $node2 ...>
To print element information:

print <$fileName> -ele <-flag $flag> <$ele1 $ele2 ...>
$fileName

fileName for printed output (optional, Default: stderr -- screen
dump)

Chapter 41

Miscellaneous Commands

$flag

integer flag to be sent to the print() method, depending on the
node and element type (optional)

$node1 $node2 ...

node tag for selected-node output (optional)

348

Default: all
$ele1 $ele2 ...

element tag for selected-element output (optional)
Default: all

reset Command
This command is used to set the state of the domain to its original state.

reset
The command invokes revertToStart() on the Domain (page 30) object.

wipe Command
This command is used to destroy all constructed objects.

wipe
This command is used to start over without having to exist and restart the interpreter (page 18).

wipeAnalysis Command
This command is used to destroy all objects constructed for the analysis.

wipeAnalysis

Chapter 41

Miscellaneous Commands

349

This command is used to start a new type of analysis. This command does not destroy the
elements (page 215), nodes (page 36), materials (page 162, page 43), etc. It does destroy the
solution strategies: the algorithm (page 329), analysis (page 339), equation solver (page 323),
constraint handler (page 316), etc.

loadConst Command
This command is used to invoke setLoadConst() on all LoadPattern (page 294) objects which
have been created up to this point.

loadConst <-time $pseudoTime>
-time $pseudoTime

set pseudo time in the domain to $pseudoTime (optional, default:
zero)

getTime Command
This command returns the time in the domain.

getTime

nodeDisp Command
Returns the displacement or rotation at specified node.

nodeDisp $nodeTag $dof
$nodeTag

node tag

$dof

degree-of-freedom tag
Valid range is from 1 through ndf (page 34), the number of nodal
degrees-of-freedom. (???)

Chapter 41

Miscellaneous Commands

350

video Command
This command is used to construct a TclVideoPlayer object for displaying the images in a file
created by the recorder display (page 310) command.

video -file $fileName -window $windowName
$fileName

fileName of images file created by the recorder display (page
310) command

$windowName

name of window to be created

The images are displayed by invoking the play (page 351) command.

Chapter 41

Miscellaneous Commands

351

play Command
This command is used to play the TclVideoPlayer object created by the video (page 350)
command.

play

nodeBounds
This commands returns a 5-element list of the max and min coordinates of the nodes defined in
the domain:

nodeBounds

The command returns: "Xmin Ymin Zmin Xmax Ymax Zmax", independently of the domain
dimensions, 1D, 2D or 3D, zeros are returned for the extra dimensions.
This command is useful when setting up a display.

Example:
3D

set Xmin [lindex [nodeBounds] 0];
set Ymin [lindex [nodeBounds] 1];
set Zmin [lindex [nodeBounds] 2];
set Xmax [lindex [nodeBounds] 3];
set Ymax [lindex [nodeBounds] 4];
set Zmax [lindex [nodeBounds] 5];

2D

set Xmin [lindex [nodeBounds] 0];
set Ymin [lindex [nodeBounds] 1];
set Xmax [lindex [nodeBounds] 3];
set Ymax [lindex [nodeBounds] 4];

1D

set Xmin [lindex [nodeBounds] 0];
set Xmax [lindex [nodeBounds] 3];

Chapter 41

Miscellaneous Commands

352

display Command
This command is used to display the model defined in the domain, and is associated with the
display recorder (page 310):

display $arg1 $arg2 $amplification

Example usage:
set dAmp 10; # this amplification is dependent on the model size
if {$ShapeType == "ModeShape" } {
display -$nEigen 0 $dAmp; # display mode shape for mode $nEigen
} elseif {$ShapeType == "NodeNumbers" } {
display 1 -1 0 ;

# display node numbers

} elseif {$ShapeType == "DeformedShape" } {
display 1 5 $dAmp;
}

# display deformed shape

353

CHAPTER 42

How To....
In this chapter, some examples on how to generate input for OpenSees for specific tasks will be
presented.

In This Chapter
Run OpenSees......................................................... 354
...Define Units & Constants ...................................... 356
...Generate Matlab Commands................................. 357
...Define Tcl Procedure............................................. 357
...Read External files ................................................ 359
Building The Model................................................... 360
Defining Output ........................................................ 366
Gravity Loads ........................................................... 369
Static Analysis.......................................................... 370
Dynamic Analysis ..................................................... 372
...Combine Input-File Components ........................... 373
...Run Parameter Study ............................................ 374
...Run Moment-Curvature Analysis on Section ......... 376
...Determine Natural Period & Frequency ................. 377

Chapter 42

How To....

Run OpenSees
There are three ways that OpenSees/Tcl commands can be executed:

 Interactive
Commands can be input directly at the propt, as shown in the figure (Win32 version):

Figure 63: Run OpenSees -- Interactive

354

Chapter 42

How To....

355

 Execute Input File at OpenSees prompt
This method is the most-commonly used one. An external file containing the input commands can
be generated a-priori (inputFile.tcl) and be executed at the OpenSees prompt by using the source
command. The generation of the input script files is presented in this chapter. The file execution is
shown in the figure (Win32 version):

Figure 64: Run OpenSees -- Source File

 Batch Mode
The previously-created input file containing the Tcl script commands necessary to execute the
analsis can also be executed at the MS-DOS/Unix prompt, as shown in the figure (Win32 version):

Chapter 42

How To....

356

Figure 65: Run OpenSees -- Batch Mode

...Define Units & Constants
The OpenSees interpreter does not process units. Units, however, can be used when entering
values if these units are defined previously. The unit definition consists of two parts: the basic units
are defined first, all other units are subsequently defined. The basic units are assigned a value of
one and all OpenSees output is in these units. It is very important that all basic units are
independent of each other. The unit-definition file can contain both metric and Imperial units, as
can the basic units. Hence, the input files may contain mixed units.
Constants, such as π and g can also be defined apriori.
An example of unit and constant definition is given in the following:

 Procedure to define units and constants
# ----Units&Constants.tcl--------------------------------------------------------# define basic units

set in 1.;
set sec 1.;
set kip 1.;
set ksi [expr $kip/pow($in,2)];

# define dependent units

set psi [expr $ksi/1000.];
set ft [expr 12.*$in];
set lb [expr $kip/1000];
set pcf [expr $lb/pow($ft,3)];
set ksi [expr $kip/pow($in,2)];
set psi [expr $ksi/1000.];
# define metric units

set cm [expr $in/2.54];
set meter [expr 100.*$cm];
set MPa [expr 145*$psi];

# define constants

set PI [expr 2*asin(1.0)];
set g [expr 32.2*$ft/pow($sec,2)];
set U

1.e10;

# a really large number

set u

[expr 1/$U];

# a really small number

Chapter

How To....

357

CHAPTER

...Generate Matlab Commands
Matlab is a common tool for post-processing. Matlab command files can be generated using the
Tcl scripting language. Using this technique ensures that the same analysis parameters are used.
Here is an example.

 # script to generate .m file to be read by matlab
# -------------MatlabOutput.tcl------------------------------------------------------------------set Xframe 1;

# this parameter would be passed in

set fDir "Data/";
file mkdir $fDir;

# create directory

set outFileID [open $fDir/DataFrame$Xframe.m w]; # Open output file for writing
puts $outFileID "Xframe($Xframe) = $Xframe;";

# frame ID

puts $outFileID "Hcol($Xframe) = $Hcol;";

# column diameter

puts $outFileID "Lcol($Xframe) = $Lcol;";

# column length

puts $outFileID "Lbeam($Xframe) = $Lbeam;";

# beam length

puts $outFileID

"Hbeam($Xframe) = $Hbeam;";

# beam depth

puts $outFileID

"Bbeam($Xframe) = $Bbeam;";

# beam width

puts $outFileID "Weight($Xframe) = $Weight;"

;

# superstructure weight

close $outFileID

...Define Tcl Procedure
The procedure is a useful tool available from the Tcl language. A procedure is a generalized
funcion/subroutine using arguments. Whenever the Tcl procedure is invoked, the contents of body
will be executed by the Tcl interpreter.
An example of a Tcl procedure is found in RCcircSec.tcl. It defines a procedure which generates a
circular reinforced concrete section with one layer of steel evenly distributed around the perimeter
and a confined core:
# ----RCcircSec.tcl-----------------------------------------------------------------------#

by Michael H. Scott

# Define a procedure which generates a circular reinforced concrete section
# with one layer of steel evenly distributed around the perimeter and a confined core.

Chapter

How To....

358

# Formal arguments
#

id - tag for the section that is generated by this procedure

#

ri - inner radius of the section

#

ro - overall (outer) radius of the section

#

cover - cover thickness

#

coreID - material tag for the core patch

#

coverID - material tag for the cover patches

#

steelID - material tag for the reinforcing steel

#

numBars - number of reinforcing bars around the section perimeter

#

barArea - cross-sectional area of each reinforcing bar

#

nfCoreR - number of radial divisions in the core (number of "rings")

#

nfCoreT - number of theta divisions in the core (number of "wedges")

#

nfCoverR - number of radial divisions in the cover

#

nfCoverT - number of theta divisions in the cover

# Notes
#

The center of the reinforcing bars are placed at the inner radius

#

The core concrete ends at the inner radius (same as reinforcing bars)

#

The reinforcing bars are all the same size

#

The center of the section is at (0,0) in the local axis system

#

Zero degrees is along section y-axis

proc RCcircSection {id ri ro cover coreID coverID steelID numBars barArea nfCoreR nfCoreT nfCoverR
nfCoverT} {
section fiberSec $id {
set rc [expr $ro-$cover];

# Core radius

patch circ $coreID $nfCoreT $nfCoreR 0 0 $ri $rc 0 360;

# Core patch

patch circ $coverID $nfCoverT $nfCoverR 0 0 $rc $ro 0 360; # Cover patch
if {$numBars <= 0} {
return
}
set theta [expr 360.0/$numBars];

# Angle between bars

layer circ $steelID $numBars $barArea 0 0 $rc $theta 360; # Reinforcing layer
}
}

This procedure is invoked by the following commands, assuming that all arguments have been
defined previously in the input generation:
source RCcircSection.tcl;
RCcircSection $IDcolFlex $riCol $roCol $cover $IDcore $IDcover $IDsteel $NbCol $AbCol $nfCoreR $nfCoreT
$nfCoverR $nfCoverT

Chapter

How To....

359

NOTE: the file containing the definition of the procedure (RCcircSec.tcl) needs to be sourced
before the procedure is invoked.

...Read External files
External files may either contain Tcl commands or data.

 Common input file
The external file may contain a series of commands that is common in most analyses. One set of
Tcl commands that can be stored in a external file are ones which define units.
An example of an external file that may want to be read within the input commands is the
unit-definition file presented earlier (units&constants.tcl (page 439)).
This file is invoked with the following command:
source units.tcl

 Repeated Calculations
An external file may contain a series of calculations that are repeated. An example of this is a
parameter study:
set Hcolumn 66;
source analysis.tcl
set Hcolumn 78;
source analysis.tcl

The analysis.tcl file contains the commands that set up and execute the entire analysis.

 External Data File
The following commands open a data file (filename=inFilename), read the file row by row and
assign the value of each row to the a single variable (Xvalues). If there are more than one value in
the row, $Xvalues is a list array, and the individual components may be extracted using the lindex
command. The user may change the commands to be exectued once the data-line has been read
to whatever is needed in the analysis.
# ----ReadData.tcl-------------------------------------------------------------------if [catch {open $inFilename r} inFileID] {; # Open the input file and check for error
puts stderr "Cannot open $inFilename for reading";

# output error statement

} else {
foreach line [split [read $inFileID] \n] { ;

# Look at each line in the file

if {[llength $line] == 0} {; # Blank line --> do nothing
continue;
} else {

Chapter

set Xvalues $line;

How To....

360

# execute operation on read data

}
}
close $inFileID; ;

# Close the input file

}

Building The Model
...Define Variables and Parameters
In the Tcl scripting language variables may be used to represent numbers. Once defined, these
variables can be use instead of numbers in Tcl and OpenSees commands. When they are being
recalled, the variables are precedented by the symbol $. If this symbol is not used, the variable
name is interpreted as a string command and an error may result.
A few examples are given:
MATERIAL PARAMETERS:
# -----MaterialParameters.tcl------------------------------------------------------# nominal compressive strength of concrete

set fc [expr -4.0*$ksi];

set Ec [expr 57*$ksi*sqrt(-$fc/$psi)];

# Concrete Elastic Modulus

set fc1C [expr 1.26394*$fc];

# CONFINED concrete (mander model), max stress

set eps1C [expr 2.*$fc1C/$Ec];

# strain at maximum stress

set fc2C $fc;

# ultimate stress

set eps2C [expr 2.*$fc2C/$Ec];
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
