adzetto/DASK_26__DESIGN_AND_ANALYSIS/analysis/torsional_irregularity/results/damping_study/rayleigh_curve.csv

T | f | xi_0.005 | xi_0.010 | xi_0.020 | xi_0.030 | xi_0.050 | xi_0.070 | xi_0.100 | xi_0.150 | xi_0.200
0.0200 | 50.0000 | 0.011495 | 0.022990 | 0.045980 | 0.068970 | 0.114951 | 0.160931 | 0.229902 | 0.344852 | 0.459803
0.0250 | 40.0000 | 0.009371 | 0.018742 | 0.037485 | 0.056227 | 0.093711 | 0.131196 | 0.187423 | 0.281134 | 0.374846
0.0300 | 33.3333 | 0.007988 | 0.015975 | 0.031950 | 0.047926 | 0.079876 | 0.111827 | 0.159752 | 0.239628 | 0.319504
0.0350 | 28.5714 | 0.007027 | 0.014054 | 0.028109 | 0.042163 | 0.070272 | 0.098380 | 0.140543 | 0.210815 | 0.281086
0.0400 | 25.0000 | 0.006331 | 0.012662 | 0.025325 | 0.037987 | 0.063311 | 0.088636 | 0.126623 | 0.189934 | 0.253246
0.0500 | 20.0000 | 0.005415 | 0.010830 | 0.021660 | 0.032490 | 0.054151 | 0.075811 | 0.108301 | 0.162452 | 0.216603
0.0600 | 16.6667 | 0.004869 | 0.009738 | 0.019477 | 0.029215 | 0.048692 | 0.068169 | 0.097384 | 0.146076 | 0.194768
0.0700 | 14.2857 | 0.004535 | 0.009070 | 0.018140 | 0.027209 | 0.045349 | 0.063488 | 0.090698 | 0.136046 | 0.181395
0.0800 | 12.5000 | 0.004333 | 0.008666 | 0.017331 | 0.025997 | 0.043328 | 0.060659 | 0.086655 | 0.129983 | 0.173311
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
