adzetto/DASK_26__DESIGN_AND_ANALYSIS/analysis/torsional_irregularity/results/floor_summary.csv

floor | height_cm | driftRatio_KYH1 | peakDisp_cm_KYH1 | driftRatio_KYH2 | peakDisp_cm_KYH2 | driftRatio_KYH3 | peakDisp_cm_KYH3
1 | 6.000 | 0.00090996 | 0.00819134 | 0.00363214 | 0.03269520 | 0.00668503 | 0.06017700
2 | 12.000 | 0.00137939 | 0.01647240 | 0.00545437 | 0.06544080 | 0.01036310 | 0.12239200
3 | 18.000 | 0.00225910 | 0.03004340 | 0.00885126 | 0.11861300 | 0.01727280 | 0.22615200
4 | 24.000 | 0.00252896 | 0.04520950 | 0.00991009 | 0.17804400 | 0.01937010 | 0.34231300
5 | 30.000 | 0.00293620 | 0.06282590 | 0.01147670 | 0.24690000 | 0.02271910 | 0.47863200
6 | 36.000 | 0.00305077 | 0.08115150 | 0.01192710 | 0.31854500 | 0.02364110 | 0.62063600
7 | 42.000 | 0.00337388 | 0.10157700 | 0.01317190 | 0.39829000 | 0.02640750 | 0.78044000
8 | 48.000 | 0.00371686 | 0.13291000 | 0.01450690 | 0.52054700 | 0.02915290 | 1.02828000
9 | 54.000 | 0.00351478 | 0.14485000 | 0.01371240 | 0.56722500 | 0.02793520 | 1.12219000
10 | 60.000 | 0.00391456 | 0.17184500 | 0.01522050 | 0.67275200 | 0.03109000 | 1.33943000
11 | 66.000 | 0.00408017 | 0.19244900 | 0.01564210 | 0.75340500 | 0.03229400 | 1.50460000
12 | 72.000 | 0.00438520 | 0.21888900 | 0.01675860 | 0.85708800 | 0.03468090 | 1.71971000
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
