adzetto/DASK_26__DESIGN_AND_ANALYSIS/analysis/torsional_irregularity/results/tbdy2018_irregularities.csv

floor | z | n_nodes | Lx | Ly | cm_x | cm_y | cr_x | cr_y | e_x | e_y | e_acc_x | e_acc_y | e_total_x | e_total_y | eta_x | eta_y | eta_max | D_bi | a1a | a1a_severe | k_story | n_col | n_brace | b1_eta | b1 | b2_eta | b2 | mass | b3_above | b3_below | b3
1 | 9.0 | 64 | 30.0 | 40.0 | 15.0 | 20.0 | 15.0 | 20.0 | 0.0 | 0.0 | 1.5 | 2.0 | 1.5 | 2.0 | 1.1 | 1.1 | 1.1 | 1.0 | False | False | 1.9342222222222205 | 64 | 0 | 0.2962962962962958 | True | 0.2962962962962958 | True | 1.6087128712871286 | 1.0 | 1.0 | False
2 | 15.0 | 64 | 30.0 | 40.0 | 15.0 | 20.0 | 15.0 | 20.0 | 0.0 | 0.0 | 1.5 | 2.0 | 1.5 | 2.0 | 1.1 | 1.1 | 1.1 | 1.0 | False | False | 6.528000000000006 | 64 | 0 | 1.0 | False | 1.0 | False | 1.6087128712871286 | 1.0 | 1.0 | False
3 | 21.0 | 64 | 30.0 | 40.0 | 15.0 | 20.0 | 15.0 | 20.0 | 0.0 | 0.0 | 1.5 | 2.0 | 1.5 | 2.0 | 1.1 | 1.1 | 1.1 | 1.0 | False | False | 6.528000000000006 | 64 | 0 | 1.0 | False | 1.0 | False | 1.6087128712871286 | 1.0 | 1.0 | False
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
