adzetto/DASK_26__DESIGN_AND_ANALYSIS/results/renders/01_front.png

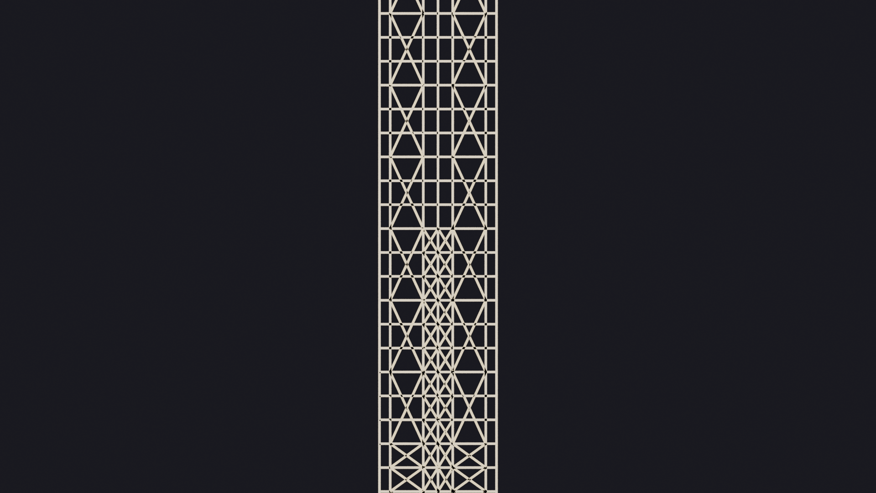
results/renders/01_front.png
