adzetto/DASK_26__DESIGN_AND_ANALYSIS/results/renders/05_iso_NE.png

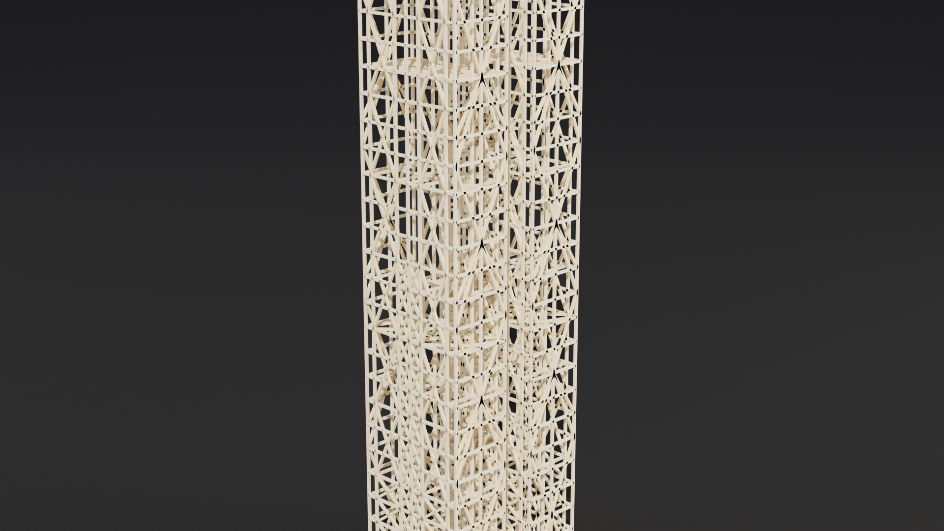
results/renders/05_iso_NE.png
