adzetto/DASK_26__DESIGN_AND_ANALYSIS/results/renders/06_iso_NW.png

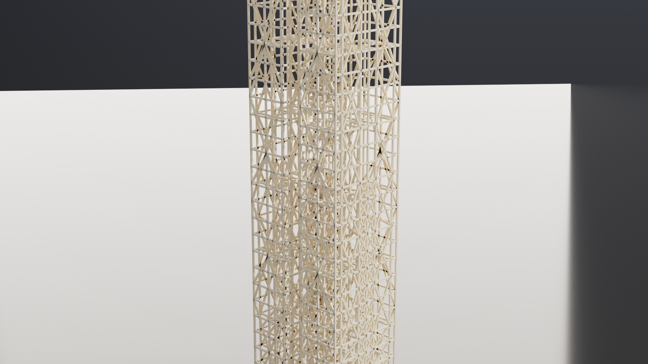
results/renders/06_iso_NW.png
