adzetto/DASK_26__DESIGN_AND_ANALYSIS/results/renders/07_iso_SE.png

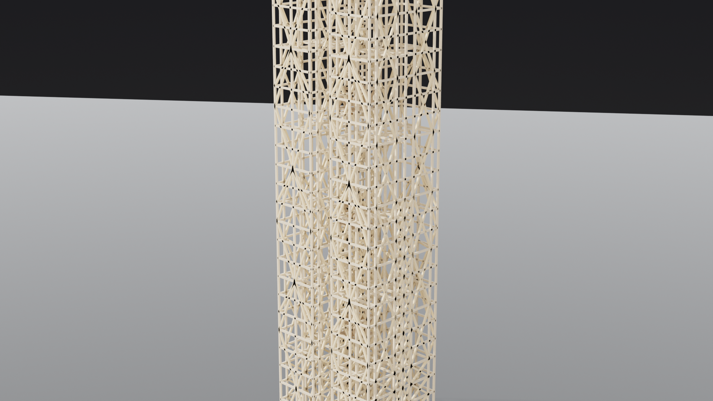
results/renders/07_iso_SE.png
