adzetto/DASK_26__DESIGN_AND_ANALYSIS/results/renders/08_iso_SW.png

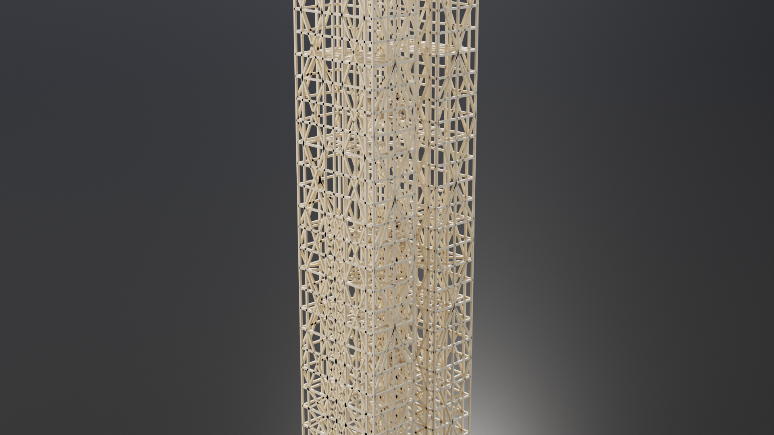
results/renders/08_iso_SW.png
