adzetto/DASK_26__DESIGN_AND_ANALYSIS/results/renders/09_top.png

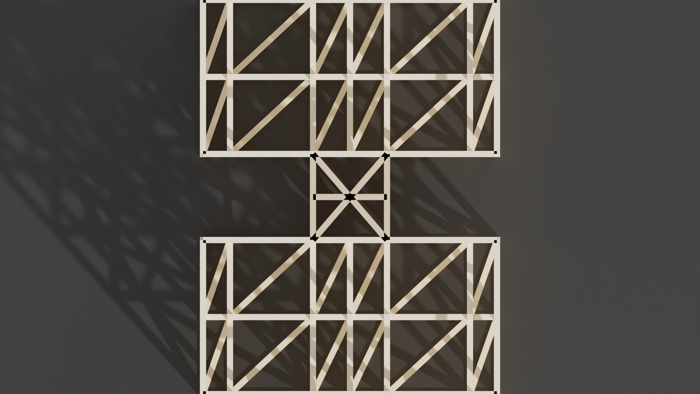
results/renders/09_top.png
