adzetto/DASK_26__DESIGN_AND_ANALYSIS/results/renders/10_worm.png

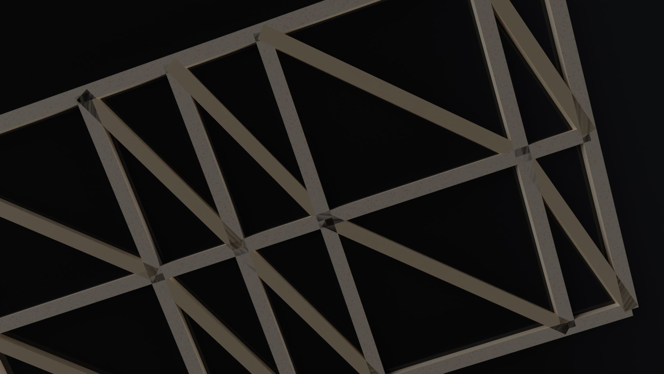
results/renders/10_worm.png
