adzetto/DASK_26__DESIGN_AND_ANALYSIS/results/renders/11_section_x03.png

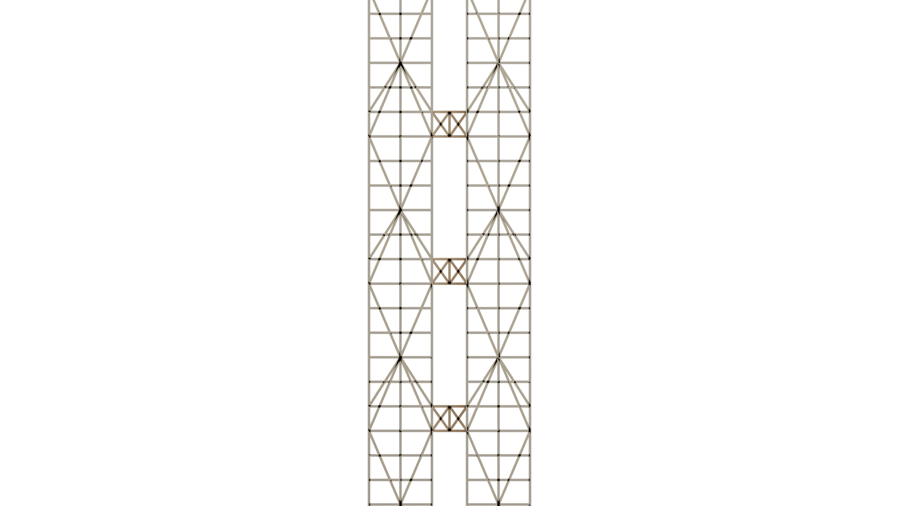
results/renders/11_section_x03.png
