adzetto/DASK_26__DESIGN_AND_ANALYSIS/results/renders/13_hero.png

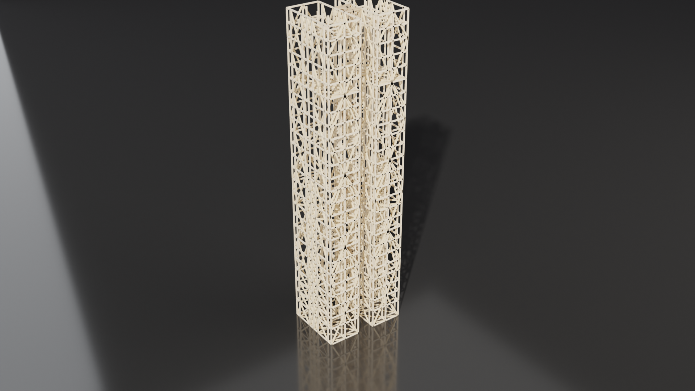
results/renders/13_hero.png
