adzetto/DASK_26__DESIGN_AND_ANALYSIS/results/renders/14_bridge_detail.png

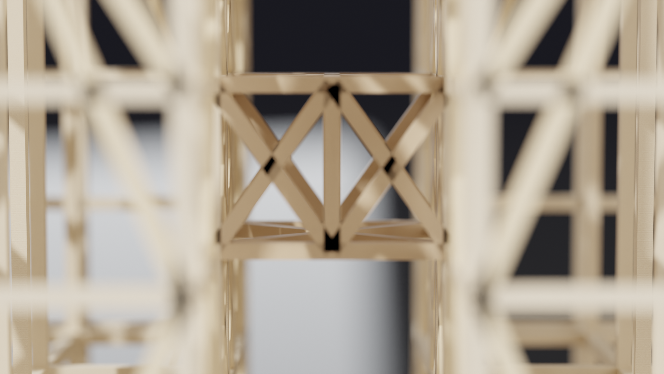
results/renders/14_bridge_detail.png
