adzetto/DASK_26__DESIGN_AND_ANALYSIS/results/renders/v10_iso_ne.png

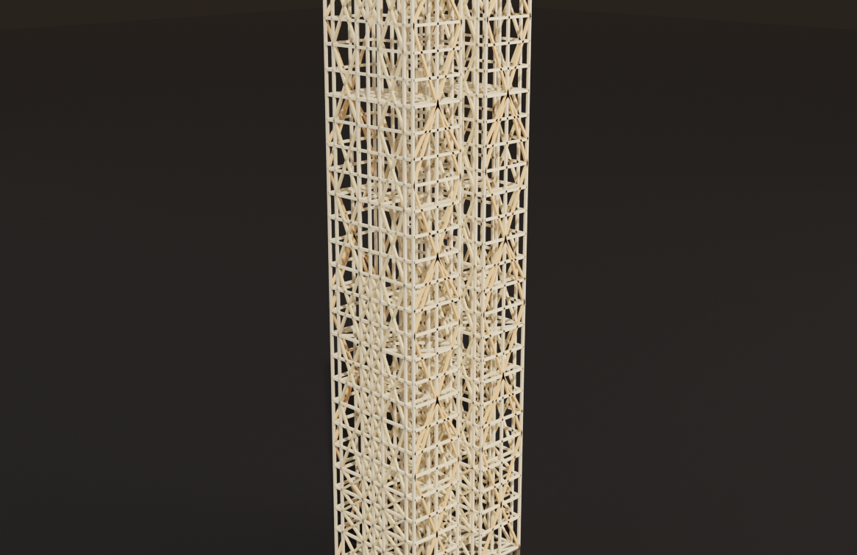
results/renders/v10_iso_ne.png
