adzetto/DASK_26__DESIGN_AND_ANALYSIS/results/visualizations/modal_analysis_tbdy2018.png

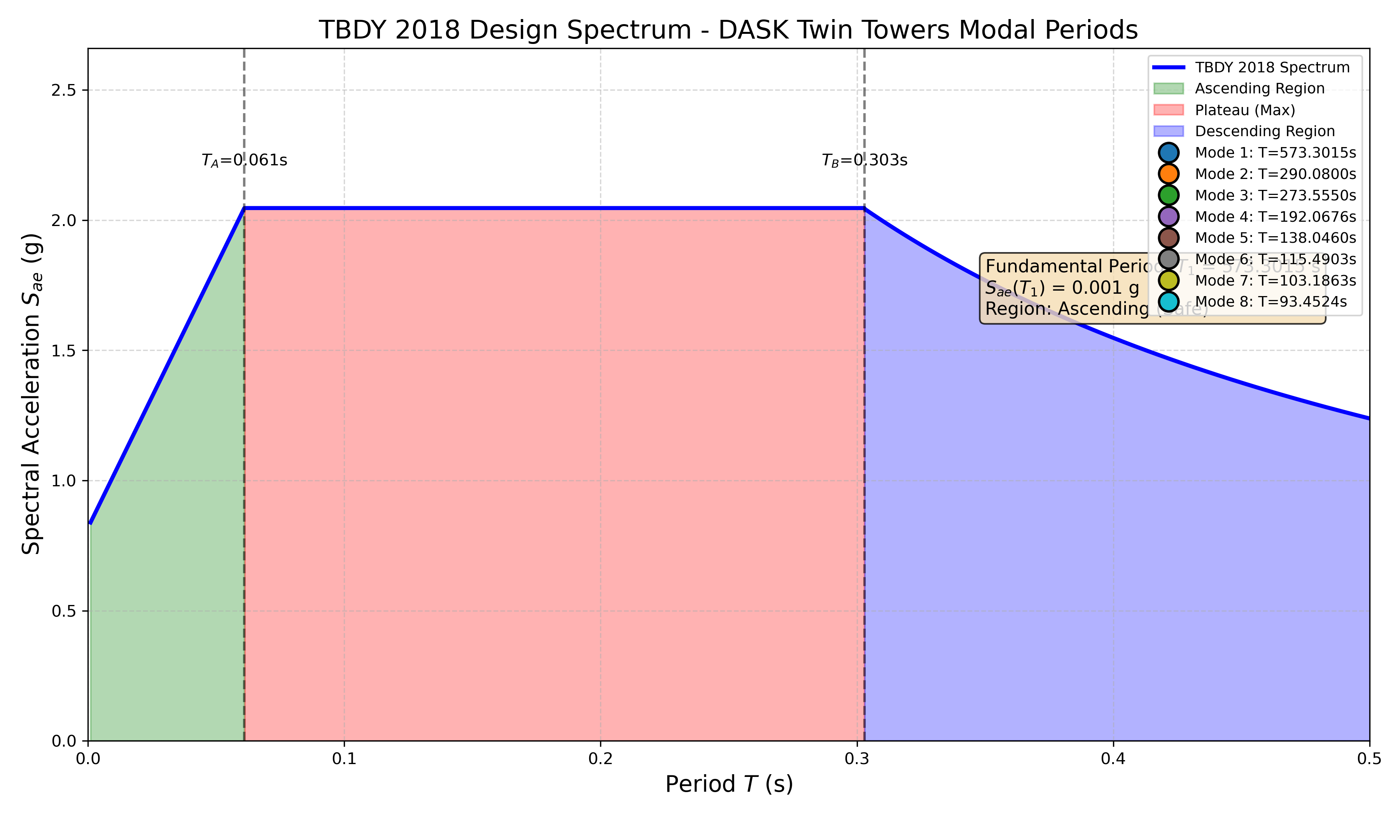
results/visualizations/modal_analysis_tbdy2018.png
